nathanfraske/CEC-Platform/beta/pcie-8pin-2port/README.md

# PCIe 8-pin module — 2-port SKU

> **STATUS (2026-07-04, spec §2.8 v1.4.0 output-architecture revision, owner-ratified,
> BETA-2):** the per-cable board-mount **J_OUT1/J_OUT2** output headers are **RETIRED**. Each
> cable's output now crosses the ratified all-Keystone/TE connector-daughterboard interface
> (`docs/standard-tier-review/output-daughterboard-study-2026-07-04.md` §8.9–§8.10,
> `blade-fit-check-2026-07-04.md`): **2 rail clips + 2 GND clips per cable** (Keystone 3586 SMT
> universal-entry blade clips, LCSC C238113, refs `TB{cable}1`–`TB{cable}4` — e.g. cable 1 =
> `TB11`–`TB14`), each single-pin clip landing on the exact post-shunt net (`/SENSEC{n}_LO`) or
> `GND` its share of J_OUT used to carry. Applied via `scripts/gen-module-beta.py`'s
> `06-cable-power` leaf (generator edit + `--force` regen); J_IN (input) unchanged.
> Netlist-verified: only `/SENSEC1_LO`, `/SENSEC2_LO`, and `GND` changed, every other net
> byte-for-byte identical; ERC/audit-sch introduce zero new findings once `fp-lib-table`
> carries `cec-Connector_Blade` (added). `bom/pcie8pin-2port-module-BOM-jlcpcb.csv` updated.
> Sense-return contacts are explicitly NOT added — study §5 decision box (e) is still open with
> the owner. **PCB follow-up (not done here):** needs Update-PCB-from-Schematic + a footprint
> swap + re-route before fab. The mating daughterboard (TE 63849-1 tabs) is a separate
> deliverable, tracked outside this board.

Standard-tier **per-cable** sensing module for the PCIe 8-pin (PCIe/GPU) power
connector. **2-port SKU: 2 cables → 4 connectors**. The 3-port variant (spec
upper bound) is a separate board in
[`../pcie-8pin-3port`](../pcie-8pin-3port). BOM target **$38** (100-qty). See spec
[§6.2](../../CEC-Platform-Ground-Truth-Spec.md).

| Item | Decision |
|---|---|
| Tier | Standard |
| SKU | **2-port** (2 cables / 4 connectors) — SKU separation from the 3-port |
| MCU | **ESP32-C6-MINI-1-N4** (v3.10; was ESP32-S3-MINI-1-N4R2). Native USB-Serial-JTAG on IO13 (D+)/IO12 (D−); ADC1 = GPIO0–6. |
| Hub link | RJ-45 8P8C shielded FTP, locking boot (J1) |
| Power path | Pass-through interposer: per cable a PSU-side **IN** + load-side **OUT** 8-pin (2×4) header; **2 cables → 4 headers**. Molex Mini-Fit Jr (PCIe/ATX 8-pin standard; 3×12V + 5×GND). Gender/footprint per the 24-pin §2.8 interposer pattern — confirm at layout. |
| Control | CAN on pair 3 (classical 500 kbps in a Standard Hub), TJA1051T/3 (U2) |
| Sensing | **Per-cable INA238** (16-bit I²C), 2 cables (U10/U11, distinct I²C addresses) — one across each cable's **0.5 mΩ** Kelvin shunt (RS1/RS2, §6.4), Vbus read on the load side. |
| Transient detection (§6.13) | **Per-cable analog DETECTION front-end** (v3.10, resolves OQ-9): INA181A2 gain-50 CSA (U20/U21) → TLV7011 hysteresis comparator (U30/U31) → board-shared firmware THRESH (MCU PWM IO14 + R10 10 kΩ / C40 100 nF) → per-cable DET → MCU GPIO, ORs into the §6.10 FREEZE trigger. Binary event (it happened + averaged envelope), not the sub-ms waveform — magnitude/shape are a PCIe Pro/Max SKU. |
| Streaming | RS-485 **not populated** (Standard); pair 2 terminated module-side |
| DETECT | 2.2 kΩ precision (R1) — CAN-only code (§2.3, OQ-6 resolved), Hub 10 kΩ/3.3 V divider; poke-and-ack tap R7 → IO10 (OQ-28) |
| Protection | No per-pin PoE/over-voltage (Standard/Pro, §2.4 v2.0); low-cap ESD diode D1 (**PESD5V0S1BA**, C5261083) on DETECT pin 8 |
| Flash/debug | USB-C (J5) on the ESP32-C6 native USB-Serial-JTAG (D+ = IO13 / D− = IO12) + BOOT/RESET buttons (SW1/SW2, TS-1088-AR02016; BOOT = IO9); VBUS ORs into +5VSB via D2 (SS34); CC1/CC2 = 5.1 kΩ |
| Decoupling | LP5907 LDO; 24-pin gold-standard tiering (2× 10 µF bulk, 1 µF LDO in/out, per-IC 100 nF) |
| BOM target | $38 (100-qty) |

## Open questions touching this board

- **OQ-9 (RESOLVED, v3.10 §6.13):** PCIe transient capture is the analog DETECTION
  ladder above — Standard sees that a transient happened (binary, into FREEZE);
  magnitude/shape are held to the PCIe Pro/Max SKUs. (OQ-57..59 gate the details.)
- **OQ-10 / OQ-12:** bundled-shunt vertical transition + high-current stackup for
  the ~40–55 A/cable shunt sites (§6.7).
- **OQ-11:** per-module shunt part selection (§6.4 table).
- *(OQ-6 module-ID encoding resolved — CAN-only modules = 2.2 kΩ.)*

## Status

Schematic generated by `scripts/gen-modules.py`; the initial PCB floorplan by
`scripts/gen-module-pcb.py` (one-shot — hand-maintained in the GUI afterwards):
4-layer, **2 oz outer / 1 oz inner** (In1 = GND, In2 = 12 V), ~110 × 66 mm, 2
cables inline top/bottom, the ESP + CAN + LDO + flash front end + RJ-45 on the
right, 4× M3 corner mounts (cables inset to clear them), CEC copper logo on the
back. **DRAFT** marker present (ERC/DRC not yet CI-gated). Next in GUI: *Update
PCB from Schematic* to pull the passives, then place/route + pour (§6.8 Kelvin
taps, §6.7 high-current transitions). Project-local library tables point at
`../../lib` via `${KIPRJMOD}`.

## Update (2026-06-06) — v3.10: ESP32-C6 MCU + §6.13 transient-detection front-end

Regenerated on the consolidated v3.10 spec:

- **MCU ESP32-S3-MINI-1-N4R2 → ESP32-C6-MINI-1-N4** (C5736265), pin map
  netlist-verified (CAN_TX/RX → pads 26/27, USB D+/D− → pads 18/17, I²C → 24/25,
  EN → 8, BOOT/IO9 → 23, DETECT_SENSE → 12, +3V3 → 3, THRESH_PWM/IO14 → 19).
  Footprint `cec-RF_Module:ESP32-C6-MINI-1`.
- **§6.13 per-cable detection front-end** (2 cables): U20/U21 **INA181A2IDBVR**
  (C2058784) + U30/U31 **TLV7011DBVR** (C702117) + board-shared R10/C40 THRESH RC
  off MCU PWM IO14. Chain netlist-verified (shunt → INA181 → comparator → THRESH →
  per-cable DET → MCU GPIO pads 28/29). **D1 PESD UL → BA** (C5261083).
- BOM regenerated (`bom/pcie8pin-2port-module-BOM-jlcpcb.csv`): **sourced 39/45**;
  open are the 0.5 mΩ shunts (OQ-11) + the Mini-Fit Jr THT power headers.
- ERC = benign only.

## PCB floorplan (2026-06-06) — condensed candidate generator (86.4 × 44 mm)

Reproduced by `scripts/gen-pcie-condensed.py` (the **parametric** PCIe analogue of the
EPS `gen-eps-condensed.py`; reuses `gen-module-pcb.py`'s emit helpers without touching the
shared generator — one script drives both PCIe SKUs by board-name arg). Built the EPS way,
with **two sub-agent passes — footprint/placement planning, then a routing game-plan**.
**86.4 × 44 mm** (4-layer, F.Cu 2 oz / In1 1 oz / In2 1 oz / B.Cu 2 oz) — condensed from the
earlier 99 × 44. Plan + diagram: `pcie2-routing-plan.png`. **All 45 schematic parts placed**
(25/25 support passives netlist-verified by `PASSIVE_SPEC` + explicitly cluster-placed — the
3 entries for the 3rd cable are correctly absent on this 2-cable SKU); DRC 0 structural apart
from a known headless false within-footprint mask-bridge artifact on a button (absent in the
GUI; the RJ-45 mouth overhangs with copper kept on-board).

- **Cable connectors = the REAL Molex 45586** (J_IN/J_OUT): **Mini-Fit Jr. right-angle,
  3rd-gen PCIe polarization, 8-circuit, Nylon UL94V-0, 2.54µm matte tin — MPN
  45586-0005** (user-confirmed keying). The footprint is the manufacturer ECAD land
  (`cec-Connector_Molex:Molex_Mini-Fit_Jr_45586_2x04_P4.20mm_Horizontal`, vendored from
  the Molex `-SD` export + its STEP): 4.20 mm pitch + **5.50 mm rows**, round ⌀2.36 mm /
  1.85 mm-drill pads, two ⌀3.0 mm snap pegs in line with the outer pins 7.3 mm forward.
  THT, consigned/hand-soldered.
- **Connectors overhang their edges** — the body+mouth hang off the top (J_IN) /
  bottom (J_OUT) edges; only the pad rows + the 2 snap pegs stay on-board. The
  footprint is native mouth-toward-+y, so J_IN is placed rot180 / J_OUT rot0 (which
  reproduces the prior pad columns, so the net map + 12 V alignment are unchanged).
  The **RJ-45 mouth overhangs the right edge** too. The 45586 snap pegs set H = 44.
- **Side-by-side sense band** per cable: 0.5 mΩ shunt vertical in the 12 V path, INA238 +
  the §6.13 INA181→TLV7011 pair beside it.
- **J1 = platform FTP jack** Kinghelm **KH-RJ45-58-8P8C** (LCSC **C2683360**,
  `cec:RJ45_FTP_Shielded_Horizontal`), SH1/SH2 → GND — matching the Hub, EPS and
  12VHPWR.
- **3 M3 mounts:** two on the logic/electronics (right) side (TR/BR corners) + **one
  centered on the connector (left) side** at (4, H/2). USB-C on the top edge.
- Dual `GND Plane` over In1 + In2 (12 V on the outers, split at the shunt), emitted
  unfilled. Routing-candidate guides on user layers (12 V pours Dwgs.User, Kelvin pairs
  Cmts.User, control→sense spine Eco1.User, CAN/USB Eco2.User). CEC logo + fab note on back.

**Next in the GUI:** *Fill All Zones*, route (§6.8 Kelvin taps, §6.7 high-current
transitions), re-DRC. Regenerate (pre-route only) with
`python3 scripts/gen-pcie-condensed.py pcie-8pin-2port` — one-shot bootstrap, refuses to
overwrite once tracks/vias exist (`--force` overrides); hand-maintained from the first route.
