nathanfraske/CEC-Platform/hubs/hub-rev2/README.md

# Hub Rev2 — sectioned regen + mezzanine stack (2026-06-24)

Generated by `scripts/gen-hub-rev2.py` from the hand-maintained **Hub Standard** netlist
(extracted to `extract.json`, BOM/LCSC preserved), laid out in 10 LABELLED FUNCTIONAL SECTIONS,
with the **Rev2 delta**: the mezzanine SOCKET (`CEC_MEZZANINE_16P`, mirror of the 24-pin rev3
header) wired as "port 0" — pre-muxed `+5V_SYS`→`+5VSB`, the shared CAN bus, `/DETECT1`, GND.
Population variant: `J_MEZZ` XOR the `J2` RJ-45 port.

STATUS: schematic DRAFT — ERC clean (0 errors; benign lib_symbol_mismatch/pin_to_pin warnings only),
78 parts, BOM sourced (inherited from Hub Standard). The live `hubs/hub-standard/` stays the source of
truth; this is a fresh Rev2 board. NEXT: PCB layout (shared alignment frame w/ the 24-pin), and the
mezzanine socket on B.Cu (the mirror). Pinout verification + the 2 new-vs-24pin IC datasheets: see the
respin docs.

## Pinout verification vs datasheets (2026-06-24)
All Hub ICs cross-checked against their cached datasheets — every pinout MATCHES (no wiring errors):
| IC | verdict | note |
|---|---|---|
| ESP32-S3-WROOM-1 | ✅ match (41 pins) | CAN_TX=10/IO17, CAN_RX=11/IO18, DETECT1-4=4-7 (ADC1), EN=3, +3V3=2 all confirmed; pads 13/14 USB + pad41 EPAD=GND are cosmetic names |
| TPS3839DBZ | ✅ match (3) | 1=GND/2=RESET/3=VDD. NOTE: RESET is PUSH-PULL (not open-drain) — no external pull-up needed on the RESET line (drop one if the layout carries it). |
| SN74AHCT1G08 | ✅ match (5) | 1=A/2=B/3=GND/4=Y/5=VCC; the LED-data buffer use (A,B tied) is correct |
| TJA1051 / LP5907 / TPS2121 | ✅ | same symbols already datasheet-verified with the 24-pin rev3 |

The Hub Rev2 is electrically verified — connectivity, BOM, and all IC pinouts checked. NEXT: PCB layout.
