nathanfraske/CEC-Platform/modules/eps-8pin-rev2/README.md

# eps-8pin-rev2 — sectioned regen (2026-06-24)

Generated by `scripts/gen-module-rev2.py eps-8pin` from the source module's extracted netlist
(`extract.json`, BOM/LCSC preserved via cec_sch `props=`), laid out in **7 LABELLED FUNCTIONAL
SECTIONS** (cable connectors · MCU C6 · CAN · LDO · cable sensing INA238+shunt+§6.13 · flash/USB ·
hub-link RJ-45+DETECT). Same treatment as the 24-pin rev3 / Hub Rev2.

STATUS: schematic DRAFT — ERC = 1 benign error (the C6→CAN-TXD GPIO typing every generated module
carries) + benign lib_symbol_mismatch/pin_to_pin warnings. BOM sourced (inherited). All ICs use
symbols already datasheet-verified (C6, TJA1051, LP5907, INA238=INA226 body, INA181, TLV7011); INA238
datasheet now cached. The source module `modules/eps-8pin/` stays the source of truth. NEXT: PCB layout.
