nathanfraske/CEC-Platform/firmware/tools/README.md

# Bench tooling (`firmware/tools/`)

Host-side tools for the 12vhpwr proto bench. They replace "open PuTTY, log
everything, extract CSVs by hand, plot offline" with a clean capture → organize
→ analyze pipeline.

```
  device (ESP32-P4 + FPGA + AD7606)
        │  USB-CDC: teleplot lines, command output, ===BURST_CSV=== blocks
        ▼
  cec_bench.py ........ owns the serial port (no dropped lines), sends commands,
        │               splits each capture into its own file + a run manifest
        ▼
  runs/run-<ts>/
    captures/NNN-<hhmmss>-<kind>.csv     one file per capture (version-stamped header line)
    analysis/NNN-<hhmmss>-<kind>/        (--analyze) per-capture subfolder:
                                           *-time.png  *-imbalance.png  *-fft.png
                                           *-metrics.md/.json (analyzer version stamped)
    manifest.md                          every command + capture + version, timestamped
    session.log                          raw terminal mirror
        ▲
        │
  cec_capture_analyze.py ... per-MODULE analysis: parses a capture, computes the
                             metrics that matter for THAT module, emits plots +
                             a metrics.md/.json. Reads the MEASURED sample rate
                             from the capture header (never the nominal label).
```

Keep using **TelePlot** for the live 5 Hz monitor — these tools own the **bursts**
and the **record**. This capture→organize→analyze path is the prototype of the
**Concierge** host layer (spec Appendix C); the per-module profiles seed its
analysis stage.

## One-time setup (your bench machine)

Install into the **same** interpreter you'll run the tools with — use
`python -m pip` (not bare `pip`) so it can't land in a different Python than the
one you launch. These tools do **not** need ESP-IDF; a plain PowerShell/terminal
is fine (and avoids polluting the IDF venv).

```
python -m pip install pyserial numpy matplotlib
python -c "import serial, numpy, matplotlib; print('ok', serial.__version__)"   # verify
```

> Windows uses `python`; Linux/macOS use `python3`. The examples below say
> `python3` — substitute `python` on Windows. **Gotcha:** in the ESP-IDF terminal
> `pip` and `python3` can be *different* Pythons, so a `pip install` then a
> `python3 ...` gives "pyserial is required". The `python -m pip` form above + the
> matching `python` (Windows) / `python3` (Linux/mac) avoids it.

## A bench session

```
# 0. rebuild the FPGA bitstream + reflash the ESP if firmware changed.
# 1. start the host (Windows COM7 / Linux /dev/ttyACM0). --analyze auto-plots each capture.
python3 cec_bench.py --port COM7 --analyze --script "cal; rate; fastburst"
#    cal   -> zeroes the current channels at idle (run with the GPU idle)
#    rate  -> measures the TRUE native rate (~100k, not the 200k nominal) -- pins the FFT axis
#    fastburst -> a native-rate window; analyzer plots it
# 2. then induce a GPU load and, interactively, type:
autoburst 500 5
#    watches the stream; on a transient > ~0.75 A deviation it freezes the native
#    ring and dumps it. The host saves + analyzes each automatically.
quit
```

Everything lands in `runs/run-<timestamp>/` — captures, the manifest doc, and
(with `--analyze`) the metrics + plots. No manual extraction.

> The scripted sequence uses quiet-detection between commands (good for the
> deterministic `cal`/`rate`/`fastburst`/`stream` setup). `autoburst` waits for a
> transient *you* induce, so run it interactively.

## `cec_bench.py` — capture host

```
python3 cec_bench.py --port PORT [--analyze] [--module 12vhpwr]
                     [--script "cal; rate; fastburst"] [--run-dir DIR]
                     [--show-teleplot] [--teleplot-udp 127.0.0.1:47269]
```
Owns the port (pyserial), shows device output + lets you type commands, **and** in
the background splits each `===BURST_CSV===` block into `captures/`, appends to
`manifest.md`, and (`--analyze`) runs the analyzer per capture. `quit` to stop.

**Auto-analyze needs numpy + matplotlib in the *same* Python** that runs
`cec_bench` (the analyzer runs as its subprocess). `--analyze` checks this at
startup and prints the exact `pip` line if they're missing — that's the usual
reason charts don't appear. Each capture's charts land in their own subfolder
`analysis/<capture>/`, and the CSVs + manifest carry a version
(`cec_bench v1.0+<git-sha>`) so a run is documented + reproducible.

**The 5 Hz teleplot `>` lines are HIDDEN in the terminal by default** — they'd
otherwise bury your typing and the command output (and break the `--script`
step-detection). They still go to `session.log`. `--show-teleplot` un-hides them.

**Live graphing + capture at the same time:** a serial port has exactly one owner,
so you cannot run Teleplot *and* `cec_bench` on the same COM port. Two ways to get
both:
- **`--teleplot-udp 127.0.0.1:47269`** — `cec_bench` owns the port and re-broadcasts
  the teleplot stream over UDP; point Teleplot's **UDP input** at that address and
  it graphs live while `cec_bench` captures. (Works with the UDP-capable Teleplot;
  the VS Code extension reading *serial* can't share the port this way.)
- Or just run them **separately** — Teleplot for live monitoring, `cec_bench` for a
  capture session. (During `autoburst`/`fastburst` the device pauses teleplot
  anyway, so you're not losing much by not having both at once.)

## `cec_capture_analyze.py` — per-module analysis

```
python3 cec_capture_analyze.py CAPTURE.csv|putty.log [--module 12vhpwr]
                     [--rate HZ] [--index N] [--out DIR]
                     [--analog-rc-hz 15900 --analog-adc-hz 14000]
```
Parses every capture block in the input (a single file or a whole PuTTY log) and,
per the **module profile**, writes `*-time.png`, `*-fft.png`, and `*-metrics.md/.json`.

Each module asks a different question, so analysis is a **profile** (pluggable):

| module | what it computes |
|---|---|
| **`12vhpwr`** (done) | per-PIN imbalance (the melt metric, flagged under load), per-pin mean/peak/RMS, total, rail droop/ripple, load fundamental + floor (FFT at the real rate, analog-ceiling overlay) |
| `atx-24pin` (stub) | per-rail power + energy (INA228 accumulators), rail stability |
| `eps` / `pcie` (stub) | per-cable balance + total power + §6.13 transient events |

### Honest notes (they matter for the numbers)

- **Rate:** the analyzer uses the rate stamped in the capture header. If it says
  `(NOMINAL -- run rate)`, every frequency is flagged ~2× suspect — run `rate` on
  the device first (the conv+read FSM self-limits to ~100k at ÷4, not the 200k
  nominal). `--rate HZ` overrides.
- **Imbalance needs load:** at idle the mean pin current is ~0 (and dominated by
  uncalibrated INA offsets), so the imbalance % is undefined and reported as
  `no_load`. Run `cal`, then capture under GPU load for a real imbalance number.
- **Imbalance has a measurement floor:** the per-pin shunts are ±1% *independent*,
  so each pin's share is only known to ±`2·tol·(N-1)/N` (≈ ±1.5% at 4 pins) — drawn
  as the grey band on the imbalance chart. A bar inside the band may be shunt
  mismatch, not real imbalance; the headline spread is trustworthy above ~2×tol.
  `--isense-tol PCT` sets the shunt class (default 1.0).
- **FFT validity:** uniform only for `fastburst`/`autoburst` (FPGA-paced). The
  ESP-paced `burst` has a non-uniform time axis — time-domain + stats only.
- **Analog ceiling** defaults to the perfboard RC (15.9 kHz) × AD7606 (14 kHz) ≈
  9.6 kHz; adjust to your front-end with `--analog-rc-hz` / `--analog-adc-hz`.

## Next

When the firmware stamps a **self-describing header** (module id + channel roles,
on top of the measured rate it already stamps), the analyzer will auto-select the
profile from the capture instead of `--module`. That header + these profiles are
the handoff into Concierge.
