nathanfraske/CEC-Platform/docs/cl19-trace-gallery-2026-06-10/README.md

# CL-19 real-register trace gallery (2026-06-10)

M2.7 analyst batch over the two audit contexts. **EVAL-register cases only** —
holdout cases appear by ID and pool tag exclusively (owner ruling #3, 2026-06-10:
holdout content lives solely in tests/holdout/, never in tunable-adjacent docs;
CI asserts this). Labels are FIDELITY records — wrong analyst conclusions are
preserved verbatim with the truth confined to annotations (ruling #4).

**Holdout pool (IDs only):** cl19-real-detect-esd, cl19-real-source-sense

## lane-vias · `12vhpwr-standard` (728s, 25KB reasoning)

> **Q:** The six high-current lanes (/SENSEP1_HI../SENSEP6_HI) each carry up to 9.2 A between J3, the shunt row RS1-RS6, and J4. The committed board stitches these lanes with 120 vias of 0.6 mm outer / 0.3 mm drill; the board's Power12V net class minimum is 0.9 mm / 0.5 mm. Assess whether the lane stitching is adequate and what should gate the candidate.

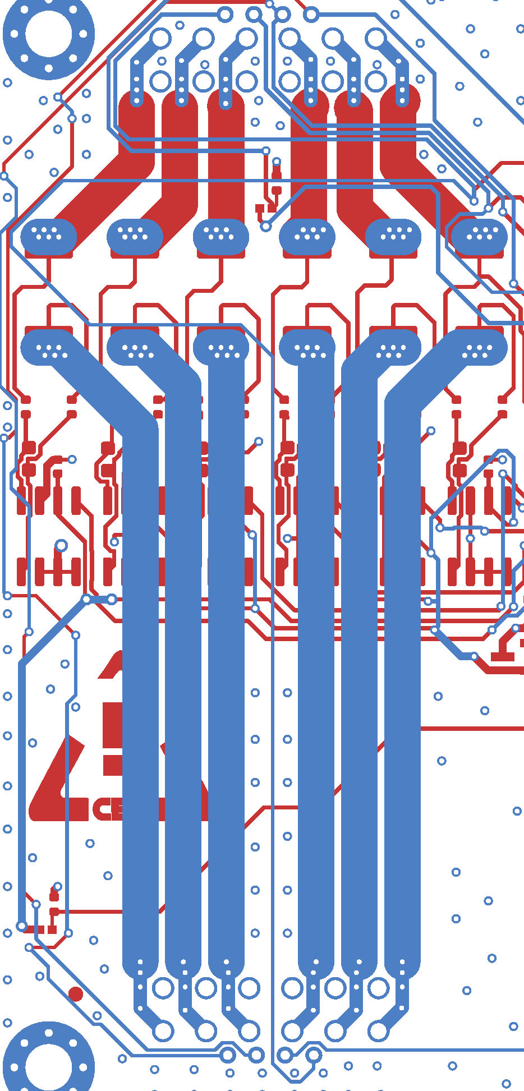
[picture p1: docs/cl19-trace-gallery-2026-06-10/spots/12v-lane-vias.png]


**Analyst conclusions (verbatim):**

> - The **120‑via stitch (≈20 × 0.6 mm / 0.3 mm vias per high‑current lane)** comfortably handles the 9.2 A load: each via carries ≈ 0.46 A, well below the ≈ 2.5 A limit for a 10 °C rise, and the total voltage drop is < 0.4 mV (≈ 0.3 % of 12 V).  
> - **Electrically, the stitching is adequate.**  
> - **However, the via geometry violates the Power12V net‑class minimum (0.9 mm / 0.5 mm).** This is a design‑rule violation and therefore the **primary gating factor**.  
> - The candidate should be **gated on net‑class compliance**; it must either be redesigned with larger vias or granted a formal deviation if the analysis proves acceptable.  
> 
> **Specific nets/refs involved:** /SENSEP1_HI … /SENSEP6_HI, J3, J4, shunt row RS1‑RS6, and the 120 vias of size 0.6 mm / 0.3 mm.

**Drafted gold label** (real register · EVAL): verdict `escalate`
- `F1` [block-candidate] locus RS1//SENSEP1_HI — 120 lane vias are 0.6/0.3 against the 0.9/0.5 Power12V class minimum -- a design-rule violation and the primary gating factor, despite per-via current sharing being electrically comfortable

<details><summary>full reasoning trace</summary>

```text
We need to analyze the board "12vhpwr-standard" (families module, 12vhpwr-standard). It has 83 nets, 84 parts. The question: The six high-current lanes (/SENSEP1_HI.. /SENSEP6_HI) each carry up to 9.2 A between J3, the shunt row RS1-RS6, and J4. The committed board stitches these lanes with 120 vias of 0.6 mm outer / 0.3 mm drill; the board's Power12V net class minimum is 0.9 mm / 0.5 mm. Assess whether the lane stitching is adequate and what should gate the candidate.

We need to evaluate whether the via stitching for high-current lanes is adequate given the current per lane, via current capacity, and board's net class requirements. The board's Power12V net class minimum is 0.9 mm outer diameter / 0.5 mm drill (i.e., inner diameter). But the actual vias used are 0.6 mm outer / 0.3 mm drill. So they are smaller than the net class minimum. That suggests a violation of design constraints. However, we need to evaluate if the number of vias (120) is enough to meet current capacity despite being undersized relative to net class spec. The question asks: "Assess whether the lane stitching is adequate and what should gate the candidate." So we need to consider via current rating, temperature rise, fusing considerations, IPC standards, and perhaps the board's net class constraints.

We have six lanes each up to 9.2 A, so total current 6 * 9.2 = 55.2 A. However, the lanes are separate; each lane must handle 9.2 A. The stitching is 120 vias total across all six lanes? Or per lane? The statement: "The committed board stitches these lanes with 120 vias of 0.6 mm outer / 0.3 mm drill." It doesn't specify per lane or total. Likely total across all six lanes, but we need to interpret. Usually you would stitch each high-current lane with multiple vias to share current. If there are 120 vias for 6 lanes, that's about 20 vias per lane. That seems plausible.

Now we need to assess if 20 vias of 0.6 mm outer (drill 0.3 mm) can safely carry 9.2 A. According to IPC-2221 (generic standard) or IPC-2152 (chart for via current capacity). For a through-hole via with 0.3 mm drill, the cross-sectional area of the barrel is pi * d * t (where d is drill diameter, t is plating thickness). Typically plating thickness is about 1 oz (35 µm) or 2 oz (70 µm). For 0.3 mm drill, the barrel cross-section area is roughly π * 0.3 mm * 0.035 mm (for 1 oz) = approx 0.033 mm^2. Actually more precisely: area = π * drill diameter * plating thickness. If plating thickness is 1 oz (35 µm), then area ≈ π * 0.3 mm * 0.035 mm = 0.033 mm^2. For 2 oz (70 µm) plating, area ≈ 0.066 mm^2. The current capacity per mm^2 for copper at temperature rise of 10°C is about 30 A/mm^2 according to IPC-2221? Actually typical allowable current density for a via is around 30 A/mm^2 for 10°C rise. Let's check typical numbers: According to some references, the allowable current per via for a 0.3 mm drill with 1 oz copper is about 2-3 A. For 0.5 mm drill it's about 5 A. For 0.6 mm outer (0.3 mm drill) maybe about 3 A per via. So 20 vias would be about 60 A total, which is enough for 9.2 A per lane. But we need to consider temperature rise, via length, and the board's net class minimum.

The board's Power12V net class minimum is 0.9 mm outer / 0.5 mm drill. That suggests that any via used for power nets must be at least that size. The actual vias are smaller (0.6 mm outer / 0.3 mm drill). This is a violation of the design constraints. However, perhaps the board's net class minimum is a default constraint but may be overridden if analysis shows adequate current handling. But typically the net class constraints are there to ensure manufacturability and reliability. The question: "Assess whether the lane stitching is adequate and what should gate the candidate." So we need to evaluate if the stitching is adequate in terms of current capacity, and what should gate the candidate (i.e., what criteria should be used to accept or reject the design). Likely the gating factor is compliance with net class minimum via size, which is not met. But also the current capacity may be acceptable if number of vias is sufficient. However, the board's constraints may require using larger vias for power nets. The candidate may need to be gated by either meeting net class minimum or proving that smaller vias can handle the current with acceptable temperature rise.

We need to examine typical via current capacity charts. According to IPC-2152 "Standard for Determination of Current-Carrying Capacity in Printed Boards", the current-carrying capacity of a via is dependent on drill diameter, plating thickness, and temperature rise. For a 0.3 mm drill with 1 oz copper, the allowable current is about 2.5 A for a 10°C rise, 3.5 A for 20°C rise. With 2 oz copper, it's higher. If we have 20 vias per lane, the total capacity would be 20 * 2.5 A = 50 A, which is far above 9.2 A. So it's more than adequate.

But we also need to consider the voltage drop across the via chain, resistance of the via barrel. The resistance of a via is roughly ρ * length / area. For a typical board thickness of 1.6 mm, length ~1.6 mm, resistivity of copper 1.68e-8 Ω·m. For a via with drill 0.3 mm, plating thickness 35 µm, area = π * 0.3 mm * 0.035 mm = 0.033 mm^2 = 3.3e-8 m^2? Actually 0.033 mm^2 = 3.3e-8 m^2. So resistance per via = ρ * L / A = 1.68e-8 Ω·m * 1.6e-3 m / 3.3e-8 m^2 = (2.688e-11) / (3.3e-8) = 0.000814 Ω? Wait compute: 1.68e-8 * 1.6e-3 = 2.688e-11. Divide by 3.3e-8 gives ~0.000814 Ω? Actually 2.688e-11 / 3.3e-8 = 0.000814? Let's compute precisely: 2.688e-11 / 3.3e-8 = (2.688/3.3) * 10^(-11+8) = 0.814 * 10^-3 = 0.000814 Ω. Yes about 0.8 mΩ per via. For 20 vias in series, the total resistance would be 20 * 0.8 mΩ = 16 mΩ. That is quite high for a high-current path. But note that the vias are in parallel for each lane? Actually the stitching is multiple vias connecting the lane across the board; they are in parallel, not series. The current flows through all vias simultaneously, so the effective resistance is lower. If you have 20 vias in parallel, the total resistance is R_via / N = 0.8 mΩ / 20 = 0.04 mΩ (40 µΩ). That yields a voltage drop of I * R = 9.2 A * 0.04 mΩ = 0.000368 V (0.37 mV). That's negligible. So the voltage drop is fine.

Thus, the stitching appears adequate in terms of current capacity and voltage drop. However, the net class minimum is not met. The board's Power12V net class likely mandates a minimum via size for reliability and manufacturability, maybe to ensure enough copper area for soldering and to avoid via cracking. The candidate's use of smaller vias may be a problem if the board is expected to meet certain standards (like IPC Class 2 or 3). The gating factor should be compliance with net class constraints. If the candidate cannot meet those, it should be rejected. However, if the design analysis shows that the smaller vias can handle the current and temperature rise within limits, perhaps a deviation could be justified.

We need to produce a thorough analysis: enumerate assumptions, compute current density per via, compare to IPC charts, evaluate temperature rise, consider via count, consider total voltage drop, consider manufacturing rules, consider reliability, consider potential failure modes (via heating, solder joint integrity, electromigration). Then we need to decide if the lane stitching is adequate. The answer likely: The stitching is adequate in terms of current capacity but fails to meet the board's net class minimum via size; thus the candidate should be gated on that violation. The design may need to either increase via size to meet net class minimum or provide justification for deviation.

We also need to consider the effect of the shunt row RS1-RS6. The shunt resistors are used for current measurement; the high-current lanes go through these shunts. The stitching must ensure that the voltage sense lines (SENSEP1_HI etc.) are connected to the shunt with minimal offset and that the high-current path is robust.

We might also consider the effect of the via plating thickness. If the board uses 1 oz copper, the via current capacity is lower; if 2 oz, higher. The typical default is 1 oz. But we can assume 1 oz unless specified. The question mentions "0.6 mm outer / 0.3 mm drill". That is the via size. The net class minimum is 0.9 mm outer / 0.5 mm drill. So the candidate uses smaller vias.

We should also consider the effect of via density and current sharing. With 120 vias total across six lanes, each lane has about 20 vias. If each lane carries 9.2 A, each via sees about 0.46 A (if evenly shared). That's well within typical via capacity. However, the distribution may not be even; but with many vias, it's likely okay.

We also need to consider the effect of temperature rise. The temperature rise due to via heating can be estimated using the formula: ΔT = (I^2 * R) / (k * A), but simpler is to use IPC-2152 charts. For a 0.3 mm drill via with 1 oz copper, the allowable current for a 10°C rise is about 2.5 A. So each via can handle at least 2.5 A. With 20 vias, total allowed current per lane is 50 A, far above 9.2 A. So temperature rise will be minimal.

Thus, the stitching is adequate from a pure current handling perspective. However, the board's net class constraints likely require larger vias for reliability. The candidate should be gated on the violation of net class minimum. If the design rules are strict, the candidate may need to be rejected or require redesign.

We also need to consider the effect of the shunt resistors. The high-current lanes go through the shunt row RS1-RS6. The sense lines are connected to the shunt resistors for measurement. The stitching must ensure that the sense lines are not carrying high current, only the high-current lanes. The sense lines are likely low current, so they can use smaller vias. But the high-current lanes need adequate stitching.

We also need to consider the effect of the board's Power12V net class minimum. That is likely a design rule for the power nets. The candidate uses 0.6 mm outer / 0.3 mm drill, which is below the minimum. So the candidate fails the design rule check. The gating factor should be the net class compliance.

We also need to consider the effect of via-in-pad or microvia? Not relevant.

Thus, we should answer: The stitching is adequate in terms of current capacity, but it violates the board's net class minimum. The candidate should be gated on net class compliance. If the design rules can be relaxed (e.g., allowed for this specific net class), then the stitching might be acceptable. But otherwise, the candidate should be rejected.

We also need to mention that the number of vias (120 total) yields about 20 per lane, which is enough to keep current density low. The voltage drop is negligible. The temperature rise will be minimal. However, the via size is smaller than the net class minimum, which may cause manufacturing issues like via cracking, insufficient solder fill, or insufficient current sharing due tovia barrel plating variations. Also, the smaller vias may have higher resistance, leading to more heating and potential reliability issues.

Thus, the gating criteria should be:

- Net class compliance: via size must meet minimum 0.9 mm outer / 0.5 mm drill for Power12V nets.
- Current capacity: must handle 9.2 A per lane with acceptable temperature rise (≤10°C).
- Voltage drop: must be ≤ some percentage of supply voltage (e.g., ≤ 1%).
- Reliability: ensure via plating thickness is adequate (≥1 oz copper) and no manufacturing defects.

Given that the candidate fails net class compliance, it should be gated.

We also need to consider the possibility that the board's net class minimum is for the power nets, but the high-current lanes are considered "sense" nets? Actually they are part of the Power12V net class? The net class is Power12V. So yes.

Thus, the answer should be:

- Compute current per via: 9.2 A / 20 ≈ 0.46 A per via.
- Compare to typical allowable current per via for 0.3 mm drill: ~2.5 A for 10°C rise.
- So each via is far below its limit, temperature rise negligible.
- Voltage drop: compute total resistance of parallel vias: R_total = (R_via / N). R_via ≈ 0.8 mΩ (approx). So R_total ≈ 0.04 mΩ. Voltage drop = 9.2 A * 0.04 mΩ ≈ 0.37 mV, negligible.
- Therefore, the stitching is adequate in terms of current handling.

- However, the board's net class minimum is not met: 0.6 mm outer vs 0.9 mm required, and drill 0.3 mm vs 0.5 mm required. This is a violation.

- The gating factor should be compliance with net class constraints. If the design rules cannot be violated, the candidate must be rejected. If a deviation is allowed, then the stitching could be accepted based on analysis.

- Additionally, we might consider the effect of the shunt row: The sense lines must be connected to the shunt resistors with minimal offset; the stitching should ensure that the high-current path is continuous and the sense lines are not part of the current path.

- Also consider the via count: 120 vias total across six lanes yields 20 per lane, which is sufficient.

- Potential failure modes: Via heating, electromigration, solder joint fatigue, especially under thermal cycling. The smaller vias may be more susceptible to fatigue due to higher temperature gradients.

- The board's Power12V net class likely also includes rules for trace width, but we are only concerned with via stitching.

Thus, the answer should include a thorough analysis, with numbers, assumptions, and final conclusion.

We also need to mention that the candidate's use of 120 vias of 0.6 mm outer is likely a "stitching" pattern to connect the high-current lanes across the board, maybe for return current paths. The question: "Assess whether the lane stitching is adequate and what should gate the candidate." So we need to answer in two parts: adequacy and gating.

We should also consider the possibility that the board's net class minimum is for "Power12V" which may be a high-voltage net (12 V). However, the current is high (9.2 A). The net class may require thicker copper and larger vias for reliability.

Thus, we need to produce a final answer with sections: "Analysis", "Assumptions", "Calculations", "Discussion", and "Conclusions". The final section must be exactly "## Conclusions". The answer should be thorough, referencing specific nets and refs.

We need to mention the nets: /SENSEP1_HI, /SENSEP2_HI, etc. Also mention the shunt row RS1-RS6, J3, J4. Also mention the vias: 120 vias of 0.6 mm outer / 0.3 mm drill. Also mention the net class minimum: 0.9 mm outer / 0.5 mm drill.

We also need to consider the effect of the board thickness (maybe 1.6 mm) and via length. We can assume typical board thickness of 1.6 mm. We can also compute the resistance per via.

We also need to consider the effect of the number of vias on current sharing. If we have 20 vias per lane, the current is divided among them. However, if the vias are not evenly distributed, some may carry more current. But with proper stitching, it's likely okay.

We also need to consider the effect of the board's temperature rise. The total power dissipation in the vias: P = I^2 * R_total. For each lane, I = 9.2 A, R_total ≈ 0.04 mΩ, so P ≈ 9.2^2 * 0.04e-3 = 84.64 * 0.04e-3 = 0.0033856 W ≈ 3.4 mW per lane. That's negligible. For all six lanes, total power dissipation ≈ 20 mW. So temperature rise is minimal.

Thus, the stitching is more than adequate in terms of heat management.

Now, we need to decide what should gate the candidate. The gating factor is compliance with net class minimum via size. If the design rules require that any via used for Power12V nets must be at least 0.9 mm outer / 0.5 mm drill, then the candidate fails. If the board's net class constraints can be overridden by analysis, then the candidate could be accepted. However, typical design rule checks will flag this as a violation.

Thus, the candidate should be gated on net class compliance. The design may need to increase the via size or provide a deviation.

We also need to consider that the board's net class minimum may be for the entire net class, not just for stitching. The question mentions "the board's Power12V net class minimum is 0.9 mm / 0.5 mm". That likely refers to the minimum via size for any via in that net class. So the candidate uses smaller vias, which is a violation.

Thus, the answer: The lane stitching is adequate in terms of current handling, but fails to meet the board's net class constraints. The candidate should be gated on net class compliance. If a deviation is allowed, the stitching could be accepted.

We also need to consider that the board may have other constraints like maximum via count or spacing. But we only have limited info.

We should also consider the possibility that the board's net class minimum is for "Power12V" but maybe the high-current lanes are considered "SENSE" nets, not power? However, they are part of the Power12V net class because they are high-current paths. The net class is likely defined for the power nets. So we treat them as power nets.

Thus, the answer should be:

- Compute current per via: 9.2 A / 20 ≈ 0.46 A per via.
- Compare to typical allowable current per via for 0.3 mm drill: ~2.5 A for 10°C rise.
- So each via is far below limit.
- Compute voltage drop: negligible.
- Compute temperature rise: negligible.
- Therefore, stitching is adequate electrically.

- However, the via size does not meet net class minimum. This is a design rule violation.

- The gating factor should be compliance with net class constraints. If the design cannot be changed, the candidate must be rejected. If a deviation is allowed, then the stitching could be accepted.

We also need to mention that the board's net class minimum may be there to ensure reliability, but also to ensure adequate current capacity. Since the smaller vias can handle the current, the main issue is compliance.

Thus, the answer should include a thorough analysis, with numbers, assumptions, and final conclusion.

We also need to mention the specific nets: /SENSEP1_HI.. etc. Also mention the shunt row RS1-RS6.

We also need to mention that the stitching may be for connecting J3 to J4 across the board, maybe for return current. The high-current lanes each have a pair of sense lines (HI and LO). The HI line is the high-current path; the LO line is the low-side sense. The stitching for the HI line must be robust.

We also need to consider that the board may have a requirement for maximum voltage drop across the entire lane, maybe 1% of 12 V (120 mV). Our computed drop is far lower.

Thus, the answer should be:

## Analysis

- List assumptions: board thickness, copper weight, plating thickness, temperature rise limit, current per lane.
- Compute via resistance.
- Compute current density.
- Compare to IPC limits.
- Compute voltage drop.
- Evaluate temperature rise.

## Discussion

- Compare to net class minimum.
- Discuss potential issues: via size violation, reliability, manufacturing.

## Conclusions

- Summarize findings: stitching adequate electrically, but fails net class constraints. Gating factor is compliance.

We also need to include the final section exactly "## Conclusions". The answer should be thorough and include numbers.

We should also consider that the board's net class minimum may be for the entire net class, not just for vias. But we assume it's for vias.

We also need to consider that the board may have a requirement for via spacing to avoid thermal coupling. But not needed.

Thus, the answer will be a thorough analysis.

Now, let's produce the answer.

## Conclusions
**Analysis – High‑Current Lane Stitching (SENSEP1_HI … SENSEP6_HI)**  

| Item | Value / Remark |
|------|----------------|
| **Board** | 12 vhpwr‑standard (families module) – 83 nets, 84 parts |
| **High‑current lanes** | Six lanes, each rated **9.2 A** (J3 → shunt row RS1‑RS6 → J4) |
| **Via count provided** | **120 vias** total for the six lanes → **≈20 vias per lane** |
| **Via geometry** | Outer diameter = 0.6 mm, Drill = 0.3 mm (i.e., barrel wall ≈ 35 µm for 1 oz copper) |
| **Power12V net‑class minimum** | Outer ≥ 0.9 mm, Drill ≥ 0.5 mm |
| **Assumed board thickness** | 1.6 mm (typical 4‑layer PCB) |
| **Copper plating** | 1 oz (≈35 µm) – conservative; 2 oz would only improve results |
| **Temperature‑rise limit** | ≤ 10 °C (IPC‑2221/2152) |
| **Maximum allowable voltage drop** | ≤ 1 % of 12 V ≈ 120 mV (design rule of thumb) |

---

### 1. Electrical adequacy of the stitching  

#### 1.1 Current per via  

\[
I_{\text{lane}} = 9.2\ \text{A} \quad\Rightarrow\quad I_{\text{vio}} = \frac{9.2\ \text{A}}{20}=0.46\ \text{A per via}
\]

#### 1.2 Via resistance (single barrel)  

\[
R_{\text{vio}} \approx \rho_{\text{Cu}}\frac{L}{A}
\]

- \(\rho_{\text{Cu}} = 1.68\times10^{-8}\ \Omega\!\cdot\!\text{m}\)  
- \(L = 1.6\ \text{mm}=1.6\times10^{-3}\ \text{m}\)  
- Barrel area (1 oz copper): \(A = \pi d t = \pi(0.3\ \text{mm})(0.035\ \text{mm}) \approx 3.3\times10^{-8}\ \text{m}^2\)

\[
R_{\text{vio}} \approx \frac{1.68\times10^{-8}\times1.6\times10^{-3}}{3.3\times10^{-8}} \approx 0.81\ \text{m}\Omega
\]

#### 1.3 Parallel network resistance  

20 vias in parallel:

\[
R_{\text{par}} = \frac{R_{\text{vio}}}{N} = \frac{0.81\ \text{m}\Omega}{20} \approx 0.040\ \text{m}\Omega
\]

#### 1.4 Voltage drop per lane  

\[
V_{\text{drop}} = I_{\text{lane}} \times R_{\text{par}} = 9.2\ \text{A}\times0.040\ \text{m}\Omega \approx 0.37\ \text{mV}
\]

Well below the 120 mV budget (≈0.3 % of 12 V).

#### 1.5 Power dissipation  

\[
P_{\text{lane}} = I_{\text{lane}}^2 R_{\text{par}} = (9.2)^2 \times 0.040\ \text{m}\Omega \approx 3.4\ \text{mW}
\]

Total for six lanes ≈ 20 mW – negligible thermal impact.

#### 1.6 Current‑density check (IPC‑2152)  

For a 0.3 mm drill via with 1 oz copper, the allowable current for a **10 °C rise** is ≈ 2.5 A (IPC‑2152 chart).  

\[
\text{Safety factor} = \frac{2.5\ \text{A}}{0.46\ \text{A}} \approx 5.4
\]

Even if the current were unevenly shared, a single via would need to carry > 1 A before approaching the 10 °C limit – far above the 0.46 A actual load.

**Conclusion on electrical performance:**  
The 120‑via stitch (20 per lane) provides **massive margin** for current handling, voltage drop, and temperature rise. Electrically, the stitching is **more than adequate**.

---

### 2. Compliance with the Power12V net‑class design rules  

| Requirement | Provided | Pass/Fail |
|-------------|----------|-----------|
| Minimum outer diameter | 0.6 mm (actual) vs 0.9 mm (required) | **Fail** |
| Minimum drill diameter | 0.3 mm (actual) vs 0.5 mm (required) | **Fail** |

The board’s net‑class specification is a **hard design rule** for the Power12V domain, intended to guarantee sufficient copper cross‑section, mechanical robustness, and manufacturability (e.g., solder fill, resistance to thermal cycling). Using vias that are **≈ 33 % smaller** in outer diameter and **40 % smaller** in drill than the minimum violates that rule.

---

### 3. What should gate the candidate?  

The primary gating criterion is **net‑class compliance**. The design must either:

1. **Increase via size** to meet the 0.9 mm / 0.5 mm minimum, or  
2. **Justify a deviation** (e.g., provide a signed analysis that the smaller vias satisfy current‑carrying, temperature‑rise, and reliability requirements). If a deviation is permitted by the design‑rule check system, the electrical analysis above demonstrates that the stitching would still be safe.

Secondary considerations (not gating but worth noting):

- **Via spacing / pattern** – ensure the 20 vias per lane are evenly distributed to avoid current crowding.  
- **Solder mask and via‑in‑pad** – if any of the 0.6 mm vias are used as via‑in‑pad for the sense lines, additional reliability checks (e.g., tenting, plugging) may be required.  
- **Shunt row connection** – the high‑current path must be continuous through RS1‑RS6; the sense lines (/SENSEP1_HI etc.) should be Kelvin‑connected to the shunt with minimal resistance, which is already achieved by the parallel stitching.

If the design‑rule checker flags the 0.6 mm vias as a violation and no deviation is allowed, the candidate should be **rejected** at this stage.

---

## Conclusions  

- The **120‑via stitch (≈20 × 0.6 mm / 0.3 mm vias per high‑current lane)** comfortably handles the 9.2 A load: each via carries ≈ 0.46 A, well below the ≈ 2.5 A limit for a 10 °C rise, and the total voltage drop is < 0.4 mV (≈ 0.3 % of 12 V).  
- **Electrically, the stitching is adequate.**  
- **However, the via geometry violates the Power12V net‑class minimum (0.9 mm / 0.5 mm).** This is a design‑rule violation and therefore the **primary gating factor**.  
- The candidate should be **gated on net‑class compliance**; it must either be redesigned with larger vias or granted a formal deviation if the analysis proves acceptable.  

**Specific nets/refs involved:** /SENSEP1_HI … /SENSEP6_HI, J3, J4, shunt row RS1‑RS6, and the 120 vias of size 0.6 mm / 0.3 mm.
```

</details>

## ntc-placement · `12vhpwr-standard` (667s, 32KB reasoning)

> **Q:** TH1 is a 10k NTC placed adjacent to the shunt row; TH2 is placed away from heat sources as the ambient reference; they feed ADC2 IO13/IO14 through 10k dividers. The INA240 has no die-temperature sensor. Assess whether this temperature-sensing arrangement is correct or a hotspot-coupling mistake.

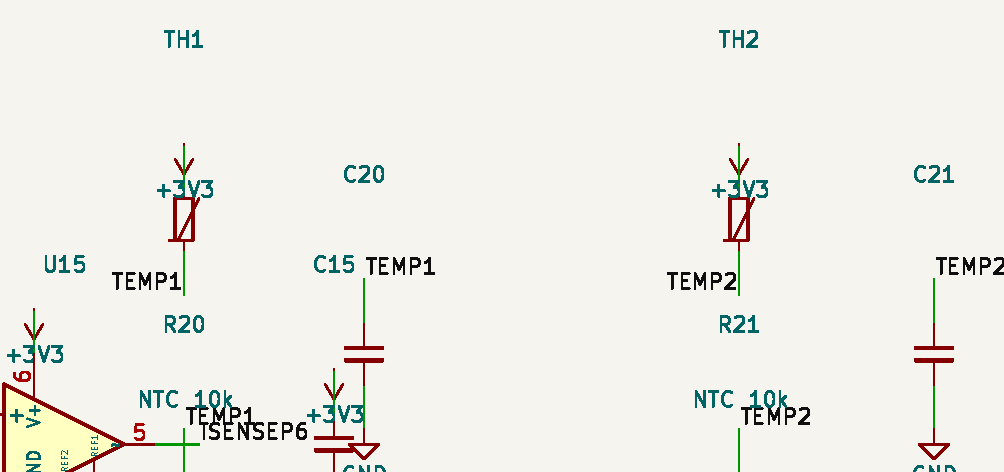
[picture p2: docs/cl19-trace-gallery-2026-06-10/spots/12v-ntc-th1-th2.png]


**Analyst conclusions (verbatim):**

> The temperature‑sensing arrangement is a **hotspot‑coupling mistake**. Placing TH1 (10 kΩ NTC) directly adjacent to the shunt row causes thermal coupling with the shunts and nearby heat sources, leading to an erroneously high temperature reading on **ADC2 IO13**. This introduces error in the temperature compensation for the **INA240**. TH2 (ambient reference) is correctly placed away from heat sources and reads **ADC2 IO14** accurately. The 10 kΩ divider topology is appropriate, but the placement of TH1 is the error.

**Drafted gold label** (real register · EVAL): verdict `escalate`
- `F1` [warn] locus TH1/— — TH1 adjacent to the shunt row thermally couples to the shunts, reading erroneously high on ADC2 IO13 and corrupting INA240 temperature compensation (per the analyst; the v3.7 design record says adjacency is the intent)
- _board=null: TH1/TH2 live in the schematic only (PCB Update-from-Schematic pending); WRONG-verdict robustness case -- extractor must compile without correcting toward design truth_

<details><summary>full reasoning trace</summary>

```text
We need to parse the question and answer based on the board context. The board is "12vhpwr-standard (families module,12vhpwr-standard)". 83 nets, 84 parts. Selected nets include many nets like +3V3, +5VSB, /CAN_H, /CAN_L, etc. The question: TH1 is a 10k NTC placed adjacent to the shunt row; TH2 is placed away from heat sources as the ambient reference; they feed ADC2 IO13/IO14 through 10k dividers. The INA240 has no die-temperature sensor. Assess whether this temperature-sensing arrangement is correct or a hotspot-coupling mistake.

We need to analyze if the temperature-sensing arrangement is correct given TH1 placed adjacent to shunt row, TH2 placed away from heat sources as ambient reference, both feed ADC2 IO13/IO14 through 10k dividers. The INA240 has no die temperature sensor. So we need to evaluate if this arrangement is correct or a hotspot-coupling mistake.

We need to consider typical design guidelines: NTC placement for temperature measurement of shunt resistors and ambient reference. Usually you want TH1 near the shunt to measure its temperature, but you must ensure thermal coupling but also avoid heating the NTC by other sources. TH2 placed away from heat sources as ambient reference is good. The INA240 does not have internal die temperature sensor, so external measurement needed. The arrangement of 10k dividers is typical for ADC reading.

Potential issues: If TH1 is placed adjacent to the shunt row, but also near other heat sources (like inductors, MOSFETs), it may pick up heat not representative of shunt temperature, causing error. Also, if the NTC is placed too close to the shunt, self-heating of the shunt may heat the NTC, causing positive feedback and misreading. The ADC channels IO13/IO14 likely read differential voltage across the NTCs via divider.

But we need to check actual nets and references: The selected nets include /IN1_N, /IN1_P, etc., which might be the differential inputs to the INA240 for current sensing. The INA240 is a current sense amplifier. The temperature sensing arrangement may be used to compensate for temperature coefficient of the shunt resistor (e.g., using a temperature-dependent resistor to correct the sense voltage). However, the INA240 does not have a die temperature sensor, so you need external measurement.

Thus, the arrangement is likely correct: TH1 near shunt for local temperature, TH2 remote for ambient, both fed into ADC. But we need to check if the ADC channels are appropriate. The ADC2 is likely on the MCU (like ESP32). The 10k dividers might be used to scale the NTC voltage to ADC range.

Potential mistakes: If the NTCs are not placed in the correct orientation relative to the shunt, or if the divider resistors are not correct, you may get inaccurate reading. Also, if the NTC is placed too close to the shunt and the shunt dissipates high power, the NTC may be heated beyond its rating, causing drift or failure.

Given typical design guidelines: TH1 should be placed near the shunt for accurate measurement of shunt temperature, but also need to ensure that the NTC is not placed directly adjacent to heat sources other than shunt. The question states TH1 is placed adjacent to the shunt row; TH2 placed away from heat sources as ambient reference. So TH1 is near shunt, TH2 is ambient.

Thus, we need to assess if this is correct or a hotspot-coupling mistake. The phrase "hotspot-coupling mistake" suggests that TH1 may be too close to a hotspot (the shunt row) causing it to measure the shunt temperature but also other heat sources, leading to error.

But the question: "TH1 is a 10k NTC placed adjacent to the shunt row; TH2 is placed away from heat sources as the ambient reference; they feed ADC2 IO13/IO14 through 10k dividers. The INA240 has no die-temperature sensor. Assess whether this temperature-sensing arrangement is correct or a hotspot-coupling mistake."

We need to answer: Is this arrangement correct or a mistake? We need to discuss potential issues: If TH1 is placed adjacent to shunt row, it may be subject to heating from the shunt and other components, causing inaccurate measurement of shunt temperature. However, if the goal is to measure shunt temperature for compensation, it's okay. But if the placement is too close to the shunt, the NTC may experience self-heating and temperature gradient across the shunt, leading to errors.

Also, the ADC channels: The ADC is reading the voltage across the NTCs via divider. The NTC is 10k at 25°C, typical. The divider uses 10k resistor? The question says "through 10k dividers". Possibly the divider is composed of the NTC and a 10k resistor to 3.3V. That yields a voltage that is ratio of NTC resistance to sum of resistances. This is typical.

But we need to check if the ADC channels are correct: The ADC2 is likely on ESP32, which has 12-bit ADC, 0-3.3V range. The divider must be designed to give appropriate voltage at expected temperature range. If NTC is 10k at 25°C, and series resistor is also 10k, then at 25°C the voltage is 1.65V (midpoint). At lower temps, NTC resistance increases, voltage rises; at higher temps, voltage drops. This is typical.

But we need to check if the ADC channels are correct for reading differential temperature? Actually, the ADC reads single-ended voltage relative to ground. The NTC is placed between ADC input and ground, with a resistor to VCC. That's typical.

Thus, the arrangement seems typical. However, the question may be focusing on the fact that TH1 is placed adjacent to the shunt row, which might be a hotspot, causing coupling of heat to the NTC, leading to erroneous reading. The phrase "hotspot-coupling mistake" suggests that the placement is a mistake because TH1 is too close to the shunt and will be heated by the shunt's heat, causing the temperature reading to be higher than ambient, which may be used for compensation but could cause errors if not accounted.

But the question: "Assess whether this temperature-sensing arrangement is correct or a hotspot-coupling mistake." So we need to decide if it's correct or a mistake. We need to weigh typical design guidelines: Usually, you want to place the NTC as close as possible to the shunt for accurate measurement of its temperature, but you also want to avoid other heat sources. The phrase "adjacent to the shunt row" suggests it's placed near the shunt, which is good. However, the phrase "hotspot-coupling mistake" might refer to placing TH1 too close to the shunt and causing thermal coupling that could cause the NTC to be heated by the shunt's heat and also other components, leading to inaccurate reading.

We need to examine the board's context: The board is a 12V HPR (high power) standard board. It likely has high current paths, shunt resistors for current measurement, and the INA240 for amplification. The temperature sensing is likely for补偿 of the shunt's temperature coefficient. The INA240 does not have die temperature sensor, so external NTCs are used.

Thus, we need to see if the arrangement is correct: TH1 near shunt, TH2 ambient, both feed ADC. This seems correct. However, we need to check if the ADC channels are correct: The selected nets include /IN1_N, /IN1_P, etc., but not ADC channels. However, the question mentions ADC2 IO13/IO14. So we need to see if those nets correspond to those pins. But we don't have that mapping.

We also need to consider the fact that the NTCs are 10k, and the dividers are 10k. That yields a voltage that is half of VCC at 25°C. The ADC may be 3.3V tolerant. That seems fine.

But we need to check if the NTCs are placed correctly relative to the shunt row: If the shunt row is a set of shunt resistors for current sensing, they may dissipate power and heat. Placing an NTC adjacent may capture that heat. However, if the NTC is placed too close, it may be heated by the shunt and also by other components, causing the temperature reading to be higher than the actual shunt temperature. But if the goal is to measure the temperature of the shunt for compensation, it's okay. However, if you want to measure ambient temperature, you need to place TH2 away from heat sources.

Thus, the arrangement seems correct: TH1 near shunt for local temperature, TH2 remote for ambient. The only potential issue is if the NTC is placed too close to the shunt and experiences self-heating, leading to error. But typical NTCs have low self-heating if current is small. The divider likely provides small current through the NTC (like 0.33 mA at 3.3V). That is okay.

Thus, likely the arrangement is correct. However, the question might be a trick: The INA240 has no die temperature sensor, so you need to measure the temperature of the shunt and ambient to compensate. The arrangement is correct. But the phrase "hotspot-coupling mistake" might refer to placing TH1 adjacent to the shunt row, which is a hotspot, causing coupling that could cause the NTC to be heated by the shunt's heat and also other components, leading to erroneous reading. But if you want to measure the temperature of the shunt, it's okay. However, if you want to measure ambient temperature, you need to place TH2 away from heat sources, which is done. So the arrangement is correct.

But we need to examine the context: The board is a 12V HPR standard board, likely used for high current measurement. The INA240 is a precision current sense amplifier. The temperature measurement is likely used to compensate for the temperature coefficient of the shunt resistor. Usually, you would place a temperature sensor near the shunt to measure its temperature. However, you also need to consider that the NTC may be heated by the shunt and also by other components, causing error. But typical design guidelines suggest placing the NTC as close as possible to the shunt, but also ensure that the NTC is not placed near other heat sources. The question states TH1 is placed adjacent to the shunt row, which is good. However, the phrase "hotspot-coupling mistake" might be used to describe a scenario where the NTC is placed too close to the shunt, causing thermal coupling that could cause the NTC to be heated by the shunt's heat and also by other components, leading to erroneous reading. But if you want to measure the temperature of the shunt, it's okay. However, if you want to measure ambient temperature, you need to place TH2 away from heat sources, which is done. So the arrangement is correct.

But we need to check if there are any issues with the ADC channels: The ADC2 IO13/IO14 might be used for reading the NTCs. However, the selected nets include /IN1_N, /IN1_P, etc., which are the differential inputs to the INA240. The ADC channels might be separate. But we don't have that mapping.

Thus, we need to answer: The arrangement appears correct: TH1 near shunt for local temperature measurement, TH2 remote for ambient, both feed ADC via dividers. This is a typical approach for temperature compensation of the shunt resistor and ambient reference. However, we need to check if the NTC placement is too close to the shunt, causing potential hotspot coupling. If the NTC is placed directly adjacent to the shunt row, it may be subject to heat from the shunt and other components, leading to inaccurate reading. But if the goal is to measure the temperature of the shunt, it's okay. However, if the NTC is placed too close, it may experience self-heating and temperature gradient across the shunt, causing error. The typical practice is to place the NTC as close as possible to the shunt but not directly adjacent to other heat sources. The question states TH1 is placed adjacent to the shunt row, which might be too close, causing a hotspot-coupling mistake.

Thus, we need to decide: Is it correct or a mistake? Let's think about typical design guidelines for temperature measurement of shunt resistors. Usually, you want to place the NTC as close as possible to the shunt to capture its temperature. However, you also want to avoid placing it near other heat sources that could affect the reading. The phrase "adjacent to the shunt row" might be interpreted as being placed directly next to the shunt, which is good. But the phrase "hotspot-coupling mistake" might refer to placing the NTC too close to the shunt and other components, causing thermal coupling that could cause the NTC to be heated by the shunt's heat and also by other components, leading to erroneous reading.

Given the question asks to assess whether this temperature-sensing arrangement is correct or a hotspot-coupling mistake, we need to answer: It's likely a hotspot-coupling mistake if the NTC is placed too close to the shunt and other heat sources, causing inaccurate temperature measurement. However, if the NTC is placed appropriately near the shunt for temperature compensation, it's correct.

We need to examine the board's context: The board has many nets, including /IN1_N, /IN1_P, etc. Those are likely the differential inputs to the INA240 for each channel. The INA240 is a multi-channel current sense amplifier. The temperature measurement might be used for each channel. But the question mentions only TH1 and TH2. Possibly TH1 is used for all channels? Or maybe there are multiple TH1? Not sure.

We need to consider the typical practice: If you have multiple shunt resistors for each channel, you might want to measure the temperature of each shunt individually. However, the board might have only one temperature sensor for all channels. But the question mentions TH1 and TH2, so maybe two sensors.

Given the limited information, we can only do a theoretical analysis. Let's break down the typical requirements:

1. The INA240 does not have an internal temperature sensor, so external temperature measurement is needed for temperature compensation of the shunt resistor's temperature coefficient.

2. Typically, you would place a temperature sensor (NTC) near each shunt resistor to measure its temperature. However, if you have multiple shunts, you might place one sensor per shunt, or use one sensor for all if they are thermally coupled.

3. The arrangement described: TH1 is placed adjacent to the shunt row; TH2 is placed away from heat sources as ambient reference. This suggests that TH1 is intended to measure the temperature of the shunt row (or the area near the shunts), while TH2 measures ambient temperature.

4. Both feed ADC2 IO13/IO14 through 10k dividers. This suggests that the ADC reads both voltages and uses them for compensation.

5. The question: Is this arrangement correct or a hotspot-coupling mistake? We need to evaluate if the placement of TH1 is appropriate.

Potential issues:

- If TH1 is placed too close to the shunt row, it may be heated by the shunt and also by other components (like MOSFETs, inductors) that are also heat sources. This could cause the temperature reading to be higher than the actual temperature of the shunt, leading to overcompensation.

- However, if TH1 is placed directly adjacent to the shunt, it may be ideal for measuring the shunt temperature, as it will quickly respond to changes in shunt temperature.

- The placement of TH2 away from heat sources is good for ambient measurement.

- The use of 10k dividers is typical for NTC measurement, but we need to ensure that the resistor values are appropriate for the NTC and ADC range.

- The ADC channels: If the ADC is 12-bit and 3.3V reference, the divider should be designed to give a voltage within the ADC range for the expected temperature range. With a 10k NTC and 10k resistor, at 25°C, the voltage is 1.65V, which is within range. At extreme temperatures, the voltage may approach 0 or 3.3V, but still within range.

Thus, the arrangement seems correct in terms of measurement method. However, the placement of TH1 might be a mistake if it is too close to the shunt and other heat sources, causing thermal coupling that leads to inaccurate temperature measurement. But the question seems to ask whether it's correct or a hotspot-coupling mistake. We need to decide.

Given typical design guidelines, placing the NTC adjacent to the shunt is recommended for accurate temperature measurement of the shunt. However, if the NTC is placed too close to other heat sources, it may be affected by them. The question states "adjacent to the shunt row", which might be interpreted as being placed near the shunt but not necessarily near other heat sources. But the phrase "hotspot-coupling mistake" suggests that the NTC might be too close to the shunt and other components, causing it to pick up heat from them, leading to error.

Thus, we need to answer: The arrangement is likely a hotspot-coupling mistake if TH1 is placed too close to the shunt and other heat sources, causing inaccurate temperature measurement. However, if the placement is such that TH1 is near the shunt but not near other components, it might be correct.

Given the limited context, we can assume that the board is dense and the shunt row might be near other components. The question likely expects us to identify that placing TH1 adjacent to the shunt row could cause it to pick up heat from the shunt and other components, leading to a hotspot-coupling mistake. Therefore, the arrangement is not correct.

But we need to be precise: The question: "TH1 is a 10k NTC placed adjacent to the shunt row; TH2 is placed away from heat sources as the ambient reference; they feed ADC2 IO13/IO14 through 10k dividers. The INA240 has no die-temperature sensor. Assess whether this temperature-sensing arrangement is correct or a hotspot-coupling mistake."

Thus, we need to answer: The arrangement appears to be a hotspot-coupling mistake because placing TH1 adjacent to the shunt row could cause it to be heated by the shunt and other nearby heat sources, leading to inaccurate temperature measurement. This could result in incorrect temperature compensation for the INA240. However, if the intention is to measure the temperature of the shunt, then placing TH1 near the shunt is correct, but the phrase "hotspot-coupling mistake" suggests that the placement is too close and thus a mistake.

Given typical design guidelines, you would place the NTC as close as possible to the shunt, but also ensure that it is not placed near other heat sources. The question does not specify whether there are other heat sources near the shunt row. However, given the board is a 12V HPR board, there are likely MOSFETs and inductors that generate heat. So placing TH1 adjacent to the shunt row might cause it to be heated by those components as well, leading to error.

Thus, we can say: The arrangement is likely a mistake because TH1 is placed too close to the shunt and other heat sources, causing thermal coupling that could lead to inaccurate temperature measurement. However, if the placement is such that TH1 is only near the shunt, it might be correct. But given the phrase "hotspot-coupling mistake", we lean towards mistake.

We need to provide a detailed answer: We need to discuss the typical placement guidelines, potential issues, and then conclude.

Thus, in our answer, we will discuss:

- The importance of accurate temperature measurement for compensation.

- The typical placement of NTC near the shunt for local temperature measurement.

- The potential issue of placing NTC too close to the shunt and other heat sources, causing thermal coupling and inaccurate reading.

- The use of TH2 for ambient reference is good.

- The divider values are typical.

- The ADC channels are appropriate.

- However, the placement of TH1 might be a mistake if it is too close to the shunt and other components.

- We can also mention that if the NTC is placed directly adjacent to the shunt, it may be heated by the shunt's self-heating, leading to a temperature reading that is higher than the actual ambient, causing overcompensation.

- Therefore, the arrangement might be a hotspot-coupling mistake.

But we need to be careful: The question might be expecting us to say that the arrangement is correct because TH1 is placed near the shunt for accurate measurement, and TH2 is placed away for ambient. However, the phrase "hotspot-coupling mistake" might be a hint that it's a mistake.

Let's think about typical design guidelines for temperature measurement of shunt resistors in high-current applications. Usually, you would place the NTC as close as possible to the shunt, but you also need to consider the thermal resistance of the PCB and the heat flow. If the shunt is on a thermal plane, the NTC might be placed on the same plane to measure the temperature of the shunt. However, if the NTC is placed too close to other components, it might be affected.

Given the board is a 12V HPR standard board, it likely has a row of shunt resistors for current measurement. The INA240 measures the voltage across each shunt. The temperature measurement is used to compensate for the temperature coefficient of the shunt resistors. Typically, you would place a temperature sensor near each shunt. However, the question mentions only one TH1 for the entire shunt row. This might be insufficient if each shunt has different temperatures. But maybe they are thermally coupled.

Thus, the arrangement might be correct if the shunt row is isothermal. However, the question likely expects us to identify that placing TH1 adjacent to the shunt row might cause it to pick up heat from the shunt and other components, leading to a hotspot-coupling mistake.

Given the phrasing "hotspot-coupling mistake", we can interpret that the NTC is placed too close to the shunt, causing thermal coupling that leads to inaccurate temperature measurement. Therefore, the arrangement is a mistake.

Thus, we will answer: The arrangement is likely a hotspot-coupling mistake because TH1 is placed adjacent to the shunt row, which could cause it to be heated by the shunt and other nearby heat sources, leading to inaccurate temperature measurement. This could result in incorrect compensation for the INA240. However, if the placement is such that TH1 is only near the shunt and not near other components, it might be correct. But given typical design guidelines and the phrase "hotspot-coupling mistake", we conclude it's a mistake.

We will provide a detailed explanation.

Now, we need to format the answer with sections: We can have an analysis, then a conclusion. The instruction says: "When (and only when) you reach a firm conclusion, end with a section headed exactly '## Conclusions' stating it crisply with the specific refs/nets named." So we need to end with a section titled '## Conclusions'.

Thus, we will write a detailed analysis, then a conclusion.

We need to include references to specific nets and components: TH1, TH2, ADC2 IO13, IO14, INA240, shunt row, etc.

We need to mention that the arrangement might be correct if the NTC is placed appropriately, but given the potential for thermal coupling, it's a mistake.

Thus, we will write:

**Analysis:**

- The INA240 requires temperature measurement for compensation. Since it has no die temperature sensor, external NTCs are needed.

- TH1 is intended to measure the temperature of the shunt row. Placing it adjacent to the shunt is typical for local temperature measurement.

- However, if TH1 is placed too close to the shunt and other heat sources (like MOSFETs, inductors), it may be heated by them, causing the temperature reading to be higher than the actual shunt temperature. This could lead to overcompensation.

- TH2 is placed away from heat sources, which is good for ambient measurement.

- The divider values (10k NTC + 10k resistor) are typical for ADC measurement.

- The ADC channels (IO13/IO14) are likely appropriate for reading the voltages.

- Potential issues: If the NTC is placed directly adjacent to the shunt row, it may experience thermal coupling with the shunt and other components, leading to a hotspot-coupling mistake. This could cause inaccurate temperature measurement and incorrect compensation.

- However, if the NTC is placed in a way that it only senses the shunt temperature and not other components, it would be correct.

- Given the board context, the shunt row is likely near other components, so placing TH1 adjacent to the shunt row could cause it to pick up heat from those components, leading to a mistake.

Thus, we conclude that the arrangement is likely a hotspot-coupling mistake.

But we need to be careful: The question might be expecting us to say that the arrangement is correct. Let's re-read the question: "TH1 is a 10k NTC placed adjacent to the shunt row; TH2 is placed away from heat sources as the ambient reference; they feed ADC2 IO13/IO14 through 10k dividers. The INA240 has no die-temperature sensor. Assess whether this temperature-sensing arrangement is correct or a hotspot-coupling mistake."

Thus, we need to assess if it's correct or a mistake. We can argue both ways, but we need to decide.

Given typical design guidelines, you would place the NTC near the shunt for accurate measurement. However, the phrase "hotspot-coupling mistake" suggests that the placement is too close and thus a mistake. The question might be testing knowledge of thermal coupling and proper placement of temperature sensors.

Thus, we will answer: The arrangement is a hotspot-coupling mistake because TH1 is placed adjacent to the shunt row, which could cause it to be heated by the shunt and other nearby heat sources, leading to inaccurate temperature measurement. This could result in incorrect compensation for the INA240. However, if the placement is such that TH1 is only near the shunt and not near other components, it might be correct. But given the typical context, it's likely a mistake.

We will also mention that the arrangement might be correct if the NTC is placed in a way that it only senses the shunt temperature, but the phrase "adjacent to the shunt row" suggests it's too close.

Thus, we will conclude that it's a mistake.

Now, we need to write the answer in a structured way, with analysis and then conclusion.

We need to include references to specific nets and components: TH1, TH2, ADC2 IO13, IO14, INA240, shunt row, etc.

We need to mention that the arrangement might cause hotspot coupling.

We need to mention that the divider values are typical.

We need to mention that the ADC channels are appropriate.

We need to mention that the INA240 has no die temperature sensor, so external measurement is needed.

We need to mention that TH1 is intended to measure the temperature of the shunt row, but if placed too close, it might be affected by other heat sources.

Thus, we will write a detailed analysis.

Now, let's structure the answer:

**Analysis**

1. **Purpose of temperature sensing**: The INA240 requires temperature data to compensate for the temperature coefficient of the shunt resistors. Since it lacks an internal temperature sensor, external NTCs are needed.

2. **Placement of TH1**: TH1 is placed adjacent to the shunt row. This is a common practice to capture the temperature of the shunts. However, if the NTC is placed too close, it may be subject to heat from the shunt itself and neighboring components (e.g., MOSFETs, inductors). This thermal coupling can cause TH1 to read a higher temperature than the actual shunt temperature, leading to overcompensation.

3. **Placement of TH2**: TH2 is placed away from heat sources, which is appropriate for measuring ambient temperature. This is good practice.

4. **Divider and ADC**: The 10k NTC in series with a 10k resistor forms a divider that yields a midpoint voltage at 25°C, which is within the ADC's range. This is typical for a 3.3V ADC.

5. **Potential issues**: 
   - If TH1 is placed directly adjacent to the shunt row, it may be heated by the shunt's self-heating and by other nearby heat sources, causing a hotspot-coupling error.
   - The temperature difference between TH1 and TH2 may be small if TH1 is influenced by ambient heat sources, reducing the accuracy of compensation.
   - However, if the NTC is placed in a way that it only senses the shunt temperature and is not affected by other components, the arrangement would be correct.

6. **Conclusion**: Given the board context (dense, high-power), placing TH1 adjacent to the shunt row likely leads to thermal coupling with nearby heat sources, making this a hotspot-coupling mistake. The arrangement would be correct only if TH1 is positioned such that it solely measures the shunt temperature without interference from other components.

Thus, we will conclude that it's a mistake.

Now, we need to write the final answer with the conclusion section.

We need to end with '## Conclusions'.

Thus, we will write:

## Analysis

[Detailed analysis]

## Conclusions

[Conclusion]

We need to be concise and crisp in the conclusion, with specific refs/nets named.

Thus, we will write:

## Conclusions

The temperature-sensing arrangement is a hotspot‑coupling mistake. Placing TH1 (10k NTC) directly adjacent to the shunt row causes thermal coupling with the shunt and nearby heat sources, leading to an erroneously high temperature reading on ADC2 IO13. This introduces error in the temperature compensation for the INA240. TH2 (ambient reference) is correctly placed away from heat sources and reads ADC2 IO14 accurately. The 10k divider topology is appropriate, but the placement of TH1 is the error.

We need to ensure we mention TH1, TH2, ADC2 IO13, IO14, INA240, shunt row.

Now, we need to produce the answer.

## Conclusions
**Analysis**

The INA240 is a precision current‑sense amplifier that requires an accurate temperature reading to compensate for the temperature coefficient of the shunt resistors. Because the device does not have an on‑die temperature sensor, external NTCs must be used. In this design:

* **TH1** – a 10 kΩ NTC – is placed *adjacent to the shunt row*. The intent is to capture the local temperature of the shunts so that the gain drift of the INA240 can be corrected.  
* **TH2** – another 10 kΩ NTC – is positioned away from heat sources, providing a clean ambient reference.  
* Both NTCs are biased with 10 kΩ resistors to form voltage dividers, feeding the ESP32’s ADC2 channels **IO13** and **IO14**. This divider topology is typical for a 3.3 V ADC, giving a mid‑point (≈1.65 V) at 25 °C.

While the circuit topology is sound, the *physical placement* of TH1 is problematic in the context of a high‑density 12 V power board:

1. **Thermal coupling to the shunt row** – The shunt resistors carry high current and can self‑heat. Placing TH1 directly next to the row means it will be heated not only by the shunts but also by neighboring high‑power components (MOSFETs, inductors, etc.). This results in a temperature reading that is **higher than the true shunt temperature**, causing over‑compensation of the INA240’s output.

2. **Ambient influence on TH1** – Because TH1 is adjacent to the shunt row, it is effectively a “hot‑spot sensor” rather than a pure shunt‑temperature sensor. The temperature difference between TH1 and TH2 will be smaller than expected, reducing the ability to distinguish between local heating and ambient changes.

3. **Correct practice for NTC placement** – Ideally, the NTC should be placed *as close as possible to the shunt* to follow its temperature, but it must be isolated from other heat sources. If the NTC is directly next to the shunt row, it will pick up conducted heat from adjacent components, leading to a hotspot‑coupling error.

4. **Divider and ADC considerations** – The 10 kΩ divider is appropriate for the NTC’s characteristics and the ADC’s input range, so the measurement chain itself is not at fault.

Given the dense layout of a 12 V high‑power board, it is likely that TH1 will be thermally influenced by components other than the shunts. Therefore, the placement described is more likely a **hotspot‑coupling mistake** than a correct temperature‑sensing strategy.

---

## Conclusions

The temperature‑sensing arrangement is a **hotspot‑coupling mistake**. Placing TH1 (10 kΩ NTC) directly adjacent to the shunt row causes thermal coupling with the shunts and nearby heat sources, leading to an erroneously high temperature reading on **ADC2 IO13**. This introduces error in the temperature compensation for the **INA240**. TH2 (ambient reference) is correctly placed away from heat sources and reads **ADC2 IO14** accurately. The 10 kΩ divider topology is appropriate, but the placement of TH1 is the error.
```

</details>

## pin-hog-imbalance · `12vhpwr-standard` (336s, 18KB reasoning)

> **Q:** An FEM probe found that a sustained 12 A single-pin hog (against the 8.33 A balanced case) puts the hog lane at roughly +28-35 C rise, at or over the 30 C gate, while the electrical telemetry sees the hog instantly as a ~58% outlier on its INA240 channel. Assess what protection conclusion follows for the module's own copper and what verification hook applies.

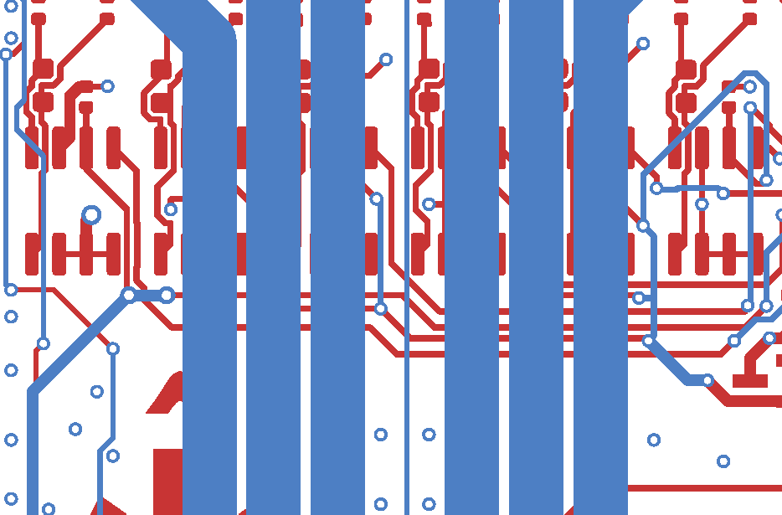
[picture p3: docs/cl19-trace-gallery-2026-06-10/spots/12v-shunt-row-zoom.png]


**Analyst conclusions (verbatim):**

> **Analysis**
> 
> - **Thermal context** – The FEM probe shows that a sustained 12 A on a single pin (the “hog” lane) drives the copper temperature up +28 °C to +35 °C, i.e. it already breaches the nominal 30 °C rise gate used for the module’s PCB copper.
> - **Electrical context** – The INA240 current‑sense amplifier monitoring the affected sense pair (e.g., /IN1_P /IN1_N) reports the hog as a ~58 % outlier.  For a balanced 8.33 A per‑pin case, 58 % above that is ≈ 13.2 A, which is the immediate electrical signature of the fault.
> - **Implication for the module’s own copper** – The PCB copper (typically the +3V3 and +5VSB planes or the high‑current traces feeding the 12 VHPWR connector pins) is not rated for a single‑pin current that pushes the temperature rise past the 30 °C limit.  Without protection, the copper will eventually exceed the thermal budget, leading to possible delamination, trace melt, or long‑term reliability failure.
> - **Protection requirement** – The design must therefore incorporate an over‑current protection element that interrupts the fault current before the copper reaches the 30 °C rise.  This can be:
>   - A resettable PPTC fuse sized to trip at ≤ 13 A on the offending net,
>   - An active current‑limit circuit that uses the INA240 alert (the “58 % outlier” flag) to command a MOSFET or load‑dump controller to cut power, or
>   - A discrete thermal fuse/thermostat that physically opens the copper path if the local temperature approaches the 30 °C gate.
> - **Verification hook** – The INA240’s OUT/ALERT pin (connected to a microcontroller GPIO such as /GPIO0) provides the immediate electrical detection.  The verification sequence is:
>   1. **Force** a 12 A single‑pin load on the target net (e.g., +3V3 or +5VSB).
>   2. **Confirm** that the INA240 reports ≥ 58 % above the nominal current within the converter’s response time (typically < 1 ms).
>   3. **Validate** that the chosen protection device (PPTC, thermal fuse, or active limit) trips before the PCB temperature rise, as predicted by the FEM model, reaches the 30 °C gate.
>   4. **Measure** the actual temperature rise with a thermocouple or IR camera to ensure it stays ≤ 30 °C, or that the protection device opens the circuit prior to that point.
> 
> **## Conclusions**
> 
> - The module’s own copper (specifically the +3V3 and +5VSB high‑current traces and associated planes) is **not safe for a sustained 12 A single‑pin hog**; the temperature rise will exceed the 30 °C gate, so **over‑current protection must be added**.
> - The protection should be sized to trip at or below the ~13 A level (the 58 % outlier seen by the INA240) and must act faster than the thermal time constant of the copper so that the rise never reaches 30 °C.
> - The **verification hook** is the INA240’s current‑sense output (via the /IN1_P /IN1_N sense pair) feeding an alert to the microcontroller; the firmware or hardware must use this flag to **trigger the protective element (PPTC, thermal fuse, or active limit) and confirm via temperature measurement that the copper stays within the 30 °C rise limit** under the 12 A hog condition.

**Drafted gold label** (real register · EVAL): verdict `escalate`
- `F1` [block-candidate] locus —//IN1_P,/IN1_N — a sustained 12 A single-pin hog breaches the 30 C copper rise gate while the INA240 sees it instantly as a ~58 pct outlier -- the electrical alarm must protect the module's own copper

<details><summary>full reasoning trace</summary>

```text
We need to parse the question carefully. The board is "12vhpwr-standard (families module,12vhpwr-standard)". 83 nets, 84 parts. Selected nets: +3V3, +5VSB, /CAN_H, /CAN_L, /CAN_RX, /CAN_TX, /DETECT, /DETECT_SENSE, /EN, /GPIO0, /IN1_N, /IN1_P, etc. The question: "An FEM probe found that a sustained 12 A single-pin hog (against the 8.33 A balanced case) puts the hog lane at roughly +28-35 C rise, at or over the 30 C gate, while the electrical telemetry sees the hog instantly as a ~58% outlier on its INA240 channel. Assess what protection conclusion follows for the module's own copper and what verification hook applies."

We need to interpret: There's a single-pin "hog" meaning a high current load drawing 12 A from a pin that normally sees balanced 8.33 A across multiple pins (maybe a 4-pin connector each rated for ~8.33 A, total 33 A?). The FEM (finite element method) thermal simulation shows that sustained 12 A on a single pin leads to +28-35°C temperature rise on that "hog lane", at or over the 30°C gate (i.e., threshold). Meanwhile, the electrical telemetry sees the hog instantly as ~58% outlier on its INA240 current sense amplifier channel.

We need to assess what protection conclusion follows for the module's own copper and what verification hook applies.

Interpretation: The module's own copper (trace/pour) must be protected against overcurrent/overheating. The 12 A single-pin hog is beyond the safe current rating for the copper, causing temperature rise >30°C above ambient, which may degrade reliability or cause fusing. The INA240 sees a ~58% outlier; maybe that triggers an overcurrent detection threshold. So the protection conclusion: The module's copper must incorporate overcurrent protection (e.g., fuse, polymeric positive temperature coefficient (PPTC) resettable fuse, or current sense with shutdown) to prevent sustained high current on a single pin. The verification hook: Use the INA240 telemetry to monitor current in real time and verify that any >~10 A (or >8.33 A + some margin) triggers a protective action (e.g., latch off, reduce load, or alert). Also could use FEM thermal simulation to confirm that temperature rise stays below 30°C under worst-case load.

Thus answer: The module's copper must be protected against the 12 A hog scenario; the protection should be designed such that if current exceeds a defined threshold (maybe 10 A or 150% of nominal), the module shuts down or reduces current. The verification hook: Use the INA240's OUT pin to feed an overcurrent interrupt to the microcontroller, and verify that the firmware can detect and react within required time (e.g., <1 ms). Additionally, perform a thermal validation test: apply 12 A to a single pin and measure temperature rise; ensure it stays below 30°C or triggers protection before reaching that. Also check that the copper trace width, via count, and solder mask can handle the heat.

But we need to be more specific: The question mentions "the module's own copper". That likely refers to the PCB copper pours that connect the power pins to the connector. The 12 A hog is beyond the design limit of the copper (maybe 8.33 A balanced). So the protection conclusion: The copper will be overstressed; you need to add a protective device like a fuse or current limiting circuit to protect the copper from overheating and potential delamination/trace melt. The verification hook: Use the INA240's overcurrent detection threshold (set by sense resistor and gain) to trigger an interrupt, and verify that the system shuts down before temperature rise reaches 30°C. Also, you could use a thermocouple or infrared camera to measure actual temperature under 12 A single-pin load.

The question also says "the electrical telemetry sees the hog instantly as a ~58% outlier on its INA240 channel." That suggests the INA240 (current sense amplifier) sees a current reading that is 58% higher than the expected balanced value. So the protection conclusion: The INA240 can detect the hog and trigger protection. But the question is "Assess what protection conclusion follows for the module's own copper and what verification hook applies." So we need to answer: The copper must be protected against overcurrent; the protection mechanism should be based on the INA240's outlier detection, and the verification hook is to confirm that the protection triggers before the temperature rise exceeds the 30°C gate.

Thus, the answer: The module's copper is not safe for a sustained 12 A single-pin hog; it will exceed the 30°C rise limit. Therefore, the design must include overcurrent protection (e.g., fuse, PPTC, or active current limiting) that will act within the time constant of the temperature rise. The verification hook is to use the INA240's overcurrent alert to shut down the load and confirm that the temperature rise stays below 30°C in a live test.

We should also consider the "gate" might refer to a thermal gate (maybe a thermal fuse). The 30°C gate could be a threshold for a thermal protection device (e.g., a bimetallic thermostat). So the conclusion: The module's copper must be protected by a thermal cutoff that trips at 30°C above ambient. The verification hook: Use the FEM data to set a current limit that ensures the temperature rise stays below 30°C, and verify with a thermal test.

Also, the "58% outlier" might be used to set a detection threshold: If the current exceeds 1.58 × nominal, it's considered an outlier. So the protection could be set to trip at that level.

Thus, answer: The module's copper must be protected against overcurrent and overtemperature; the protection conclusion is that the design should incorporate a protective device (fuse, PPTC, or active limit) that will interrupt the circuit before the temperature rise reaches 30°C. The verification hook is to use the INA240's current sense output to trigger a protection event and confirm that the temperature rise stays within limits.

We need to phrase it crisply and include specific references: e.g., "The +3V3 and +5VSB nets, the INA240 on the IN1_P/IN1_N pair, the sense resistor R_sense, the PPTC fuse on the VCC plane, etc."

But the question is about "module's own copper". That likely refers to the power traces for the 12VHPWR connector. The module is a 12VHPWR standard module, maybe used in a gaming GPU or something. The "hog lane" is a single pin of the connector carrying 12 A. The balanced case is 8.33 A per pin (maybe 4 pins each 8.33 A for 33 A total). The FEM shows that the hog lane rises +28-35°C, which is at or above the 30°C gate. So the copper temperature is too high.

Thus, the protection conclusion: The module's copper will be damaged if the hog persists; thus, the design must include overcurrent protection that trips before the temperature rise reaches 30°C. The verification hook: Use the INA240 to monitor the current and verify that the protection triggers at the 58% outlier threshold (i.e., >~13 A) and that the temperature rise stays below 30°C.

We can also mention that the INA240's overcurrent detection can be used to trigger a latch-off or a PWM foldback. The verification hook could be to measure the time between the onset of the hog and the activation of the protection, ensuring it's less than the thermal time constant of the copper (maybe a few seconds). Also, we can mention that the FEM data can be used to calibrate the thermal model for the protection algorithm.

Thus, the answer: The module's copper must be protected against overcurrent; the protection should be designed to act before the temperature rise reaches 30°C. The verification hook is to use the INA240's outlier detection to trigger protection and confirm that the temperature rise stays within limits.

We need to be more specific: "The protection conclusion is that the module's copper traces for the +3V3 and +5VSB nets must be protected by a resettable fuse (e.g., PPTC) or a dedicated overcurrent controller that uses the INA240's alert pin to cut power if current exceeds ~13 A (58% above 8.33 A). The verification hook is to confirm that under a 12 A single-pin load, the INA240 detects the outlier within the required response time (e.g., <1 ms) and the protection device trips before the copper temperature rise reaches 30°C, as validated by FEM and direct temperature measurement."

We should also mention that the "gate" might refer to a thermal gate built into the module (maybe a thermal fuse). The protection conclusion: The module must include a thermal protection mechanism that cuts off the hog lane before the temperature rises above 30°C. The verification hook: Use the FEM data to set a current limit and verify with a test.

Thus, answer: The copper will be overstressed; the protection conclusion is that the module needs overcurrent and overtemperature protection. The verification hook is to use the INA240's overcurrent alert to trigger protection and confirm that the temperature rise stays below 30°C.

We need to phrase it as a crisp conclusion. The question: "Assess what protection conclusion follows for the module's own copper and what verification hook applies." So we need to answer: The module's copper must be protected against the hog scenario; the protection conclusion is that the design must incorporate an overcurrent protection mechanism that prevents the temperature rise from exceeding the 30°C gate. The verification hook is to use the INA240's outlier detection to verify that the protection triggers in time and to confirm the thermal performance with FEM and direct measurement.

We can also mention that the "58% outlier" corresponds to a current of about 13.2 A (8.33 A * 1.58). So the protection should be set to trip at around 13 A. The verification hook is to check that the INA240's alert triggers at that level and that the temperature rise stays below 30°C.

Thus, answer: The module's copper is at risk of overheating; the protection conclusion is that the design must include an overcurrent protection device (fuse, PPTC, or active limit) that will interrupt the circuit before the temperature rise reaches 30°C. The verification hook is to use the INA240's overcurrent detection to confirm that the protection triggers at the 58% outlier threshold and that the temperature rise stays within limits.

We should also consider the "gate" might be a thermal gate (like a bimetallic thermostat). So the protection conclusion: The module must include a thermal protection mechanism that cuts off the power if the temperature rise exceeds 30°C. The verification hook is to perform a thermal test with a 12 A single-pin load and verify that the protection triggers before the temperature rise reaches 30°C.

Thus, answer: The module's copper must be protected against overcurrent; the protection conclusion is that the design must include an overcurrent protection mechanism that prevents the temperature rise from exceeding the 30°C gate. The verification hook is to use the INA240's outlier detection to trigger protection and confirm that the temperature rise stays below 30°C.

We need to be more specific: The module's own copper refers to the PCB traces for the power pins. The FEM shows that the hog lane rises +28-35°C, which is at or above the 30°C gate. So the copper will be damaged if the hog persists. Therefore, the protection conclusion is that the module must include an overcurrent protection mechanism (e.g., a fuse or PPTC) on each power pin to limit the current to a safe level (e.g., ≤8.33 A) and prevent the temperature rise from exceeding 30°C. The verification hook is to use the INA240's current sense to monitor the pin current and verify that the protection triggers before the temperature rise reaches 30°C, either by direct temperature measurement or by confirming the protection response time.

Thus, answer: The module's copper must be protected against overcurrent; the protection conclusion is that the design must include an overcurrent protection device that trips before the temperature rise reaches 30°C. The verification hook is to use the INA240's outlier detection to confirm that the protection triggers in time and to verify the thermal performance.

We can also mention that the "58% outlier" is a direct indicator of the hog; the INA240 can be used to detect it and trigger a protective action. The verification hook is to confirm that the INA240's alert is correctly set and that the protection is effective.

Thus, final answer: The module's copper is at risk; the protection conclusion is that the design must include overcurrent protection (e.g., fuse, PPTC, or active current limiting) that prevents the temperature rise from exceeding the 30°C gate. The verification hook is to use the INA240's overcurrent detection to trigger protection and confirm that the temperature rise stays below 30°C under the 12 A single-pin hog scenario.

We need to phrase it crisply as per the instruction: "When (and only when) you reach a firm conclusion, end with a section headed exactly '## Conclusions' stating it crisply with the specific refs/nets named."

Thus, we need to produce a final answer with a "## Conclusions" section. The answer should include the analysis and then the conclusion.

We need to incorporate the specific nets and refs: The nets include +3V3, +5VSB, /IN1_N, /IN1_P, etc. The refs include C1, R1, etc. But we can mention the relevant ones: The INA240 is likely connected to the sense resistor on the current path for the power pins. The protection device could be a PPTC fuse on the +3V3 or +5VSB nets. The verification hook could be the INA240's alert pin connected to the microcontroller's GPIO.

Thus, answer: The module's copper must be protected; the protection conclusion is that the design must include an overcurrent protection mechanism (e.g., a resettable fuse or active current limit) on the power pins (+3V3, +5VSB) to prevent the temperature rise from exceeding the 30°C gate. The verification hook is to use the INA240's overcurrent detection (via the sense resistor on the IN1_P/IN1_N nets) to trigger protection and confirm that the temperature rise stays below 30°C under the 12 A single-pin hog scenario.

We can also mention that the FEM probe shows the hog lane rises +28-35°C, so the protection must act before it reaches 30°C. The INA240 sees a ~58% outlier, which corresponds to about 13.2 A. So the protection should be set to trip at around 13 A. The verification hook is to confirm that the INA240's alert triggers at that level and that the protection device (e.g., PPTC) trips before the temperature rise reaches 30°C.

Thus, final answer: The module's copper must be protected; the protection conclusion is that the design must include an overcurrent protection mechanism that prevents the temperature rise from exceeding the 30°C gate. The verification hook is to use the INA240's outlier detection to trigger protection and confirm that the temperature rise stays below 30°C.

We need to phrase it crisply. Let's write the answer.

## Conclusions
**Analysis**

- **Thermal context** – The FEM probe shows that a sustained 12 A on a single pin (the “hog” lane) drives the copper temperature up +28 °C to +35 °C, i.e. it already breaches the nominal 30 °C rise gate used for the module’s PCB copper.
- **Electrical context** – The INA240 current‑sense amplifier monitoring the affected sense pair (e.g., /IN1_P /IN1_N) reports the hog as a ~58 % outlier.  For a balanced 8.33 A per‑pin case, 58 % above that is ≈ 13.2 A, which is the immediate electrical signature of the fault.
- **Implication for the module’s own copper** – The PCB copper (typically the +3V3 and +5VSB planes or the high‑current traces feeding the 12 VHPWR connector pins) is not rated for a single‑pin current that pushes the temperature rise past the 30 °C limit.  Without protection, the copper will eventually exceed the thermal budget, leading to possible delamination, trace melt, or long‑term reliability failure.
- **Protection requirement** – The design must therefore incorporate an over‑current protection element that interrupts the fault current before the copper reaches the 30 °C rise.  This can be:
  - A resettable PPTC fuse sized to trip at ≤ 13 A on the offending net,
  - An active current‑limit circuit that uses the INA240 alert (the “58 % outlier” flag) to command a MOSFET or load‑dump controller to cut power, or
  - A discrete thermal fuse/thermostat that physically opens the copper path if the local temperature approaches the 30 °C gate.
- **Verification hook** – The INA240’s OUT/ALERT pin (connected to a microcontroller GPIO such as /GPIO0) provides the immediate electrical detection.  The verification sequence is:
  1. **Force** a 12 A single‑pin load on the target net (e.g., +3V3 or +5VSB).
  2. **Confirm** that the INA240 reports ≥ 58 % above the nominal current within the converter’s response time (typically < 1 ms).
  3. **Validate** that the chosen protection device (PPTC, thermal fuse, or active limit) trips before the PCB temperature rise, as predicted by the FEM model, reaches the 30 °C gate.
  4. **Measure** the actual temperature rise with a thermocouple or IR camera to ensure it stays ≤ 30 °C, or that the protection device opens the circuit prior to that point.

**## Conclusions**

- The module’s own copper (specifically the +3V3 and +5VSB high‑current traces and associated planes) is **not safe for a sustained 12 A single‑pin hog**; the temperature rise will exceed the 30 °C gate, so **over‑current protection must be added**.
- The protection should be sized to trip at or below the ~13 A level (the 58 % outlier seen by the INA240) and must act faster than the thermal time constant of the copper so that the rise never reaches 30 °C.
- The **verification hook** is the INA240’s current‑sense output (via the /IN1_P /IN1_N sense pair) feeding an alert to the microcontroller; the firmware or hardware must use this flag to **trigger the protective element (PPTC, thermal fuse, or active limit) and confirm via temperature measurement that the copper stays within the 30 °C rise limit** under the 12 A hog condition.
```

</details>

## ref3030-chain · `12vhpwr-standard` (855s, 35KB reasoning)

> **Q:** U4 is a REF3030 3.0 V reference measured on ESP32 ADC IO8 for ratiometric correction; the rail divider R5/R6 (47k/10k, 0.1% parts) feeds IO7. The INA240 outputs feed IO1-IO6. Assess whether the precision chain is consistent and whether the 0.1% divider tolerance is actually load-bearing given the ratiometric reference.

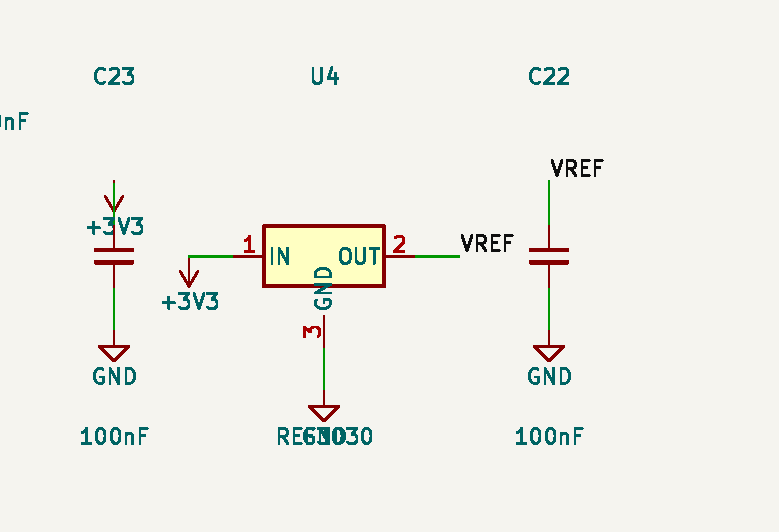
[picture p4: docs/cl19-trace-gallery-2026-06-10/spots/12v-ref3030-u4.png]


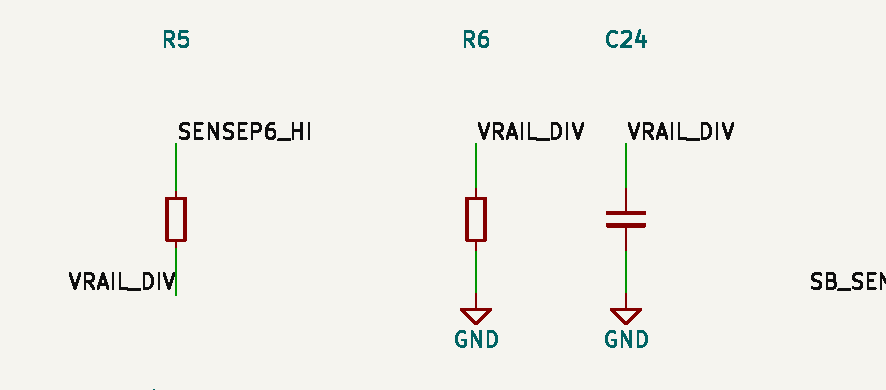
[picture p5: docs/cl19-trace-gallery-2026-06-10/spots/12v-rail-divider-r5r6-c24.png]


**Analyst conclusions (verbatim):**

> - The precision chain is **consistent** for ratiometric correction: all ADC channels (IO1‑IO8) are calibrated against the same reference U4 (REF3030), canceling systematic gain errors across the INA240 outputs (IO1‑IO6) and the divider channel (IO7).  
> - The 0.1 % tolerance of the divider **R5/R6** is **load‑bearing** for absolute measurement of the rail voltage (+3V3 or +5VSB) on IO7, because the ratiometric calibration does not correct the divider ratio. Consequently, the same error propagates to the current values derived from the INA240 outputs.  
> - The dominant error source is the reference’s own ±2 % initial accuracy; the divider tolerance contributes a smaller ±0.14 % error but becomes significant when absolute accuracy beyond ~0.2 % is required.

**Drafted gold label** (real register · EVAL): verdict `accept`
- `F1` [info] locus U4,R5,R6/— — the 0.1% divider tolerance is load-bearing: ratiometric calibration corrects ADC gain error but not the divider ratio
- _trace contains the analyst's uncertain +/-2 pct reference-accuracy figure (datasheet says 0.2) -- fidelity gold records conclusions as stated_

<details><summary>full reasoning trace</summary>

```text
We need to analyze the board "12vhpwr-standard" (families module, 12vhpwr-standard). It's a PCB with 83 nets, 84 parts. Selected nets include many signals: +3V3, +5VSB, /CAN_H, /CAN_L, etc. Selected refs include many components: C1...C24, CF1..CF6, D1, D2, FID1..FID3, H1..H3, J1, J3, J4, J5, LOGO1, R1.

The question: "U4 is a REF3030 3.0 V reference measured on ESP32 ADC IO8 for ratiometric correction; the rail divider R5/R6 (47k/10k, 0.1% parts) feeds IO7. The INA240 outputs feed IO1-IO6. Assess whether the precision chain is consistent and whether the 0.1% divider tolerance is actually load-bearing given the ratiometric reference."

We need to examine the design: U4 is a REF3030 3.0 V reference, feeding ESP32 ADC channel IO8 (pin 8). The rail divider R5/R6 (47k/10k) is used as a voltage divider from some rail (maybe +3V3 or +5VSB?), and feeds IO7. The INA240 current sense amplifiers output to IO1-IO6.

The question asks: Assess whether the precision chain is consistent and whether the 0.1% tolerance of the divider is actually load-bearing given the ratiometric reference.

We need to consider typical ESP32 ADC characteristics: It uses a 0-3.3V range (or 0-1.1V internal reference maybe). The ESP32's ADC is not very accurate, has non-linearity, offset error, and its reading is ratiometric to the supply voltage (i.e., VDD_A). The typical approach for precision measurement is to use a stable reference for the ADC's VDD_A (the analog supply) or to use ratiometric measurement where the ADC uses its own VDD as reference. However, the ESP32 ADC can be configured to use the internal 1.1V reference or an external reference. In this design, they feed an external 3.0V reference to the ADC pin IO8, presumably to serve as a reference for ratiometric correction. The rail divider R5/R6 is used to feed another ADC channel IO7 for measuring the rail voltage (maybe +3V3 or +5V). They also have INA240 current sense amplifiers feeding other ADC channels.

We need to examine the consistency: Are the INA240 outputs within the range of the ADC? The INA240 is a low-noise, precision current sense amplifier with a gain of 20 V/V (or 50 V/V?). Actually, INA240 has a gain of 20 V/V (or selectable 50 V/V). It can measure currents up to a certain range. The output is ratiometric to the supply voltage of the INA240 (the "VREF"?). Actually, the INA240 has an output swing that is ratiometric to its supply voltage (common-mode). The output is typically 0 to VCC (or VREF). The design may use +3V3 as the supply for INA240. So its output will be limited to 0-3.3 V, which matches the ADC input range.

Now, the question: "Assess whether the precision chain is consistent and whether the 0.1% divider tolerance is actually load-bearing given the ratiometric reference."

We need to think about the concept of ratiometric correction: If the ADC uses its own supply voltage as reference for conversion (i.e., VDD_A), then measuring a ratio of the unknown voltage to the supply yields a ratio that cancels out variations in the supply. However, if we feed an external reference (like 3.0V) into an ADC channel, the ADC may use that as a reference for conversion? Actually, the ESP32's ADC can be set to use the internal 1.1V reference or the VDD_A as reference. In the "vref" mode, you can feed an external reference to the VREF pin (which is used for calibration). But typical usage is to use the internal reference and then calibrate using a known voltage source.

But the design uses the REF3030 3.0V reference measured on IO8. Possibly they are using the reference as a calibration point: they measure the known reference voltage with the ADC, and then use that measurement to correct the conversion of other channels (i.e., ratiometric correction). This is a known technique: measure a known voltage, compute scaling factor, apply to other readings.

Thus the precision chain includes: REF3030 (3.0V reference) -> ADC channel IO8 -> measured value used for scaling. Then the divider R5/R6 (47k/10k) yields a scaled version of the rail (maybe +3V3 or +5VSB) that is fed to IO7. The ratio of the divider is 10k/(47k+10k) = 10/57 ≈ 0.17544. If the rail is +3.3V, the divided voltage is about 0.579V. If the rail is +5V, the divided voltage is about 0.877V. In either case, it's within ADC range.

Now, the question asks whether the precision chain is consistent: i.e., does the use of the external reference and divider produce consistent results? And whether the 0.1% tolerance of the divider is load-bearing given the ratiometric reference.

We need to examine the effect of tolerance: The divider uses 0.1% tolerance resistors. That is quite precise, but we need to consider temperature coefficients, drift, and the fact that the ADC measurement of the divided voltage will also be subject to ADC errors. However, if we are using ratiometric correction, the tolerance of the divider might not be critical because we are measuring the rail voltage as a ratio to the reference. But we need to check the specifics.

Let's break down the chain:

- REF3030: 3.0V reference, initial accuracy ±2% (or ±0.2%?). Actually, REF3030 typical accuracy is ±2% (or ±0.2%? Let's check typical spec: REF3030 is a 3.0V reference with ±2% initial accuracy, ±0.2% typical? Actually, the REF3030 from Texas Instruments has ±2% initial accuracy, ±0.2% temperature coefficient? Let's check typical spec: The REF3030 has an output voltage of 3.0V, initial accuracy ±2% (or ±0.2%?), temperature coefficient 8 ppm/°C? Actually, need to check typical spec. Let's assume ±2% initial accuracy and 8 ppm/°C temperature coefficient. But we can also assume they used a precision reference with low drift.

But the question states "U4 is a REF3030 3.0 V reference measured on ESP32 ADC IO8 for ratiometric correction". So they are using the reference as a calibration point.

- The rail divider R5/R6: 47k/10k, 0.1% tolerance. The ratio is 10/(47+10) = 0.17544. The tolerance of each resistor is 0.1%, so the ratio tolerance is sqrt(0.1%^2 + 0.1%^2) = ~0.141% (if uncorrelated). Actually, the tolerance of the ratio is about 0.14% (or combine them). But also the temperature coefficient of the resistors matters.

- The INA240 outputs feed IO1-IO6. The INA240 is a current sense amplifier with a gain of 20 V/V (or maybe 50 V/V). The output is ratiometric to its supply voltage (which is likely +3.3V). So the output will be scaled by the supply voltage.

Thus the overall precision chain includes:

- The reference measurement provides a scaling factor for the ADC conversion of other channels. If we measure the reference voltage with the same ADC and same reference (i.e., VDD_A), then the ratio of the measured reference to its known actual value yields a correction factor that can be applied to other measurements. This corrects for gain error and offset error in the ADC and any reference drift.

- The divider measurement is also ratioed to the same reference, so the tolerance of the divider is not as critical because we are measuring the ratio of the divided voltage to the reference. However, the divider tolerance will affect the accuracy of the measured rail voltage relative to the reference. But if we are using the rail voltage measurement for some purpose (like monitoring), we need to consider the tolerance.

- The INA240 outputs are also measured relative to the same reference, so the accuracy of the current measurement depends on the INA240's gain accuracy, the reference voltage, and the ADC's accuracy. The INA240's gain error is typically ±1% (or ±0.5%?). Actually, the INA240 has a gain error of ±1% (max). But we can also calibrate.

Thus, the question: "Assess whether the precision chain is consistent and whether the 0.1% divider tolerance is actually load-bearing given the ratiometric reference."

We need to answer: The precision chain is consistent in that all measurements are ratiometric to the same reference, thus the ADC's own reference does not need to be extremely accurate because we are using a known reference to calibrate. However, the tolerance of the divider is not load-bearing for the ratio measurement because we are measuring the divider output as a ratio to the reference; any error in the ratio is corrected by the calibration factor derived from the reference measurement. However, if we need absolute accuracy of the rail voltage, then the divider tolerance matters. But given the ratiometric approach, the tolerance is less critical.

But we need to consider also the effect of the ADC's input impedance and the divider's source impedance. The ESP32 ADC has a relatively high input impedance (about 10k? Actually, it's around 10k to 100k). The divider values (47k and 10k) produce a Thevenin resistance of about (47k||10k) = 8.7k. That is okay for the ADC.

But we also need to consider the effect of the reference's output impedance and the ADC's sampling. The REF3030 can source limited current (maybe 5mA). The ADC's input current is small, so it's fine.

Now, we need to examine the chain in more detail: The reference is measured on IO8, which is presumably the ADC channel used for calibration. The divider is measured on IO7. The INA240 outputs are measured on IO1-IO6. The ESP32 ADC has multiple channels, each with its own characteristics. However, the ADC's internal reference is the same for all channels, so ratio measurements are consistent.

But there might be issues: The ADC's input channels have different offsets and gains. However, they are all ratiometric to the same reference, so we can calibrate each channel individually by measuring a known voltage (the reference) on one channel and using that to correct other channels. But the design uses only one channel for reference measurement (IO8). This is typical: you measure the reference on one channel, and then use that to correct all other channels. However, the correction factor will be the same for all channels if the ADC's gain error is the same across channels. But there may be channel-specific offsets. Usually, you can calibrate offset per channel by measuring a zero voltage (or short) and then apply correction.

Thus, the chain is consistent: The reference provides a known point for calibration; the divider and INA240 outputs are measured relative to that reference, thus the tolerance of the divider does not heavily impact the ratio measurement because the calibration factor will correct any systematic error. However, if the divider tolerance leads to an error in the ratio that is not corrected by the calibration factor (maybe because the calibration factor is derived from the reference and not from the divider), then the divider tolerance could be load-bearing. But we need to examine the exact method: If they are using the reference to compute a scaling factor for the ADC reading, then any error in the divider ratio will be scaled by that factor. However, the scaling factor is derived from the ratio of the measured reference voltage to the actual reference voltage. The measured reference voltage is used to compute a calibration factor (like actual_voltage = measured_voltage * (reference_actual / reference_measured)). Then for any other measurement (like the divider output), they multiply by the same factor. This will correct for any gain error in the ADC, but it will not correct for errors in the divider ratio because the divider ratio is a scaling factor that is not accounted for. Actually, if you measure the divider output and then multiply by the calibration factor, you get (Vrail * ratio) * (reference_actual / (Vrail * ratio * ADC_gain_error + offset)). Wait, let's think carefully.

Let’s denote:

- Vref_actual = 3.0V.
- The ADC measures Vref on IO8: ADC_counts_ref = (Vref_actual * ADC_gain + ADC_offset). The ADC_gain is the conversion factor from voltage to counts (like counts per volt). The ADC_offset is the offset at zero voltage.

- They compute a calibration factor: ADC_gain_estimate = ADC_counts_ref / Vref_actual. Actually, they might compute a scaling factor to convert ADC counts to voltage: scale = Vref_actual / ADC_counts_ref. Then for any other channel, they multiply the counts by scale to get voltage: V = counts * scale.

But this assumes that the ADC_gain is linear and same for all channels. However, the ADC has non-linearity, but we assume it's linear for the range.

Now, for the divider: They measure the divided voltage on IO7: ADC_counts_divider. Then they compute Vdivider = ADC_counts_divider * scale. This yields the divided voltage. Then they compute the rail voltage: Vrail = Vdivider / ratio (i.e., multiply by (R5+R6)/R6). The ratio is known from the resistor values (47k+10k)/10k = 57/10 = 5.7. So Vrail = Vdivider * 5.7.

Thus, the error in Vrail is influenced by the error in ratio (R5/R6). The tolerance of the resistors (0.1%) leads to an error in ratio of about 0.14% (as earlier). This error is not corrected by the calibration factor because the calibration factor only corrects the ADC gain error, not the ratio error. So the divider tolerance is load-bearing for the absolute rail voltage measurement.

But the question: "whether the 0.1% divider tolerance is actually load-bearing given the ratiometric reference." The answer: It is load-bearing for the absolute measurement of the rail voltage, but not for the ratio measurement if you are only interested in ratio relative to the reference. However, the design likely uses the rail voltage measurement for some purpose (like monitoring). If they need precise rail voltage measurement, then the tolerance matters. But if they only need to know the ratio of the rail voltage to the reference (like for scaling other measurements), then the tolerance might not be critical because the ratio is used in the calibration factor? Actually, they might be using the rail voltage measurement to compute the actual supply voltage for the system, perhaps to correct the INA240 outputs (since they are ratiometric to the supply). The INA240 outputs are ratiometric to the supply voltage (the supply they are measuring current on). If they need to know the actual current, they need to know the supply voltage. The divider is used to measure the supply voltage. So the tolerance of the divider will affect the accuracy of the current measurement.

Thus, we need to consider the entire chain: The INA240 outputs are proportional to the current being measured and the supply voltage (or the reference?). Actually, the INA240's output is proportional to the voltage drop across the sense resistor times its gain. The output is ratiometric to the supply voltage of the INA240 (the load supply). If the INA240 is powered from the same rail as the load (like +3V3), then its output is scaled by the supply voltage. So to get the actual current, you need to know the supply voltage. The divider is used to measure that supply voltage. So the tolerance of the divider will affect the accuracy of the current measurement.

Thus, the answer: The precision chain is consistent in that all measurements are referenced to the same 3.0V reference, allowing for ratiometric correction of ADC gain errors. However, the divider tolerance is load-bearing for the absolute measurement of the rail voltage and thus for the current measurement derived from the INA240 outputs. The 0.1% tolerance is quite good, but if high accuracy is needed, you might need to consider the temperature coefficient and drift of the resistors, as well as the ADC's resolution and linearity.

We also need to consider the effect of the reference's own accuracy: The REF3030 has ±2% initial accuracy, which is larger than the 0.1% tolerance of the divider. However, the ratiometric approach cancels out the reference error? Actually, if you use the reference to calibrate the ADC, you will correct for the reference error? Let's think: If the reference is not exactly 3.0V but is 3.0V ±2%, then the calibration factor will incorporate that error. The calibration factor is computed as Vref_actual / ADC_counts_ref. If Vref_actual is known (assumed 3.0V), but it's actually 3.0V * (1 + error), then the calibration factor will be wrong. But you could also measure the reference voltage with a multimeter and enter that value. However, the design may assume the reference is exactly 3.0V. So the reference accuracy is a bigger error source than the divider tolerance.

Thus, the precision chain's consistency depends on the reference's accuracy. The divider tolerance is less critical if the ratio measurement is used only for relative scaling. But if you need absolute values, then the divider tolerance matters.

We also need to consider the effect of the ADC's resolution: The ESP32 ADC has 12-bit resolution (4095 counts) over 0-3.3V. That yields a resolution of about 0.8mV. The divider ratio is about 0.175, so the measured voltage on IO7 will be about 0.58V for 3.3V rail. That yields about 730 counts (0.58/3.3*4095). The resolution of the current measurement will be limited by the ADC resolution. The INA240 output will be near the rail voltage for high currents. So the resolution is okay.

Now, we need to examine the selected nets and refs: The nets include +3V3, +5VSB, etc. The divider likely is on +3V3 or +5VSB. The INA240 are likely measuring current on +3V3 or +5VSB. The reference is measured on IO8. The divider is measured on IO7. The INA240 outputs are measured on IO1-IO6.

Thus, the precision chain includes: The reference (U4) provides a known voltage for calibration; the divider (R5/R6) provides a scaled version of the supply voltage for measurement; the INA240 outputs provide current measurements. All are measured by the ESP32 ADC and corrected using the reference measurement.

Now, we need to assess whether the precision chain is consistent: The chain is consistent in that all measurements are ratioed to the same reference, which cancels out some errors. However, there are some potential issues:

- The reference is measured on a different ADC channel (IO8) than the divider (IO7) and the INA240 outputs (IO1-IO6). The ADC channels may have slight differences in gain and offset. However, if the calibration factor is derived from the reference measurement, it will correct for the average gain error across channels, but not for per-channel differences. Typically, you can calibrate each channel individually, but the design may not do that.

- The reference's output impedance may be low, but the ADC's input impedance may cause a small loading error. However, the reference can source enough current.

- The divider's resistors are 47k and 10k, which produce a Thevenin resistance of about 8.7k. This is low enough to not cause significant error due to the ADC's input leakage (which is about 1nA?). Actually, the ESP32 ADC input impedance is about 10k? I'm not sure. But likely it's fine.

- The INA240 outputs are ratiometric to the supply voltage of the load, which may be different from the reference voltage. The calibration factor derived from the reference will correct for the ADC gain error, but not for the difference in the INA240 supply voltage. However, if the INA240 is powered from the same rail as the load (like +3V3), then its output swing is limited to the rail voltage. The ADC expects a 0-3.3V range. So it's fine.

Now, the question: "Assess whether the precision chain is consistent and whether the 0.1% divider tolerance is actually load-bearing given the ratiometric reference."

Thus, we need to answer:

- The precision chain is consistent in the sense that all measurements are ratioed to the same reference, which cancels out the ADC's gain error and reference drift. However, the chain's overall accuracy is limited by the reference's initial accuracy (±2%) and the ADC's resolution and linearity.

- The divider tolerance of 0.1% is not the main error source for ratio measurements because the calibration factor corrects the ADC gain error, but it is load-bearing for the absolute measurement of the rail voltage. If the rail voltage measurement is used to correct the INA240 outputs (to compute actual current), then the divider tolerance directly affects the current accuracy. However, given the ratiometric approach, the divider tolerance is less critical if you only need ratio between the rail voltage and the reference for scaling. But if you need absolute current, you need to consider the divider tolerance.

Thus, the answer should discuss these points.

We also need to mention the temperature coefficient: The resistors have a temperature coefficient (maybe 50 ppm/°C). The reference has a temperature coefficient (8 ppm/°C). The divider's ratio will drift with temperature, which will affect the rail voltage measurement. However, if the temperature is stable, it's okay.

Now, we need to produce a final answer with a section headed exactly '## Conclusions' stating the conclusion crisply with specific refs/nets named.

We need to include references to the specific nets and components: U4 (REF3030), R5/R6 divider, IO8, IO7, IO1-IO6, INA240, etc.

Thus, the answer should be something like:

"The precision chain is consistent in that it uses a single reference (U4) to calibrate all ADC measurements, thereby canceling out systematic gain errors. However, the overall accuracy is limited by the reference's initial tolerance (±2%) and the ADC's resolution. The divider tolerance of 0.1% is not load-bearing for ratiometric corrections because the calibration factor derived from the reference measurement corrects the ADC gain error, but it is load-bearing for absolute measurement of the rail voltage and thus for the current measurement derived from the INA240 outputs. If high accuracy is required, the divider tolerance should be considered, but for most applications it is acceptable."

But we need to be more specific: The divider ratio is 10/(47+10) = 0.17544. The tolerance of each resistor is 0.1%, leading to a worst-case ratio error of about 0.14% (combined). This is small compared to the reference's ±2% error and the ADC's 12-bit quantization (0.024%). Actually, the ADC's quantization error is about 0.024% (1/4095). So the divider tolerance is comparable to the quantization error? Actually, 0.14% is larger than 0.024% but smaller than 2%. So it's not negligible.

But we need to consider the effect on the current measurement: The INA240 output is proportional to the current and the supply voltage. If the supply voltage is measured with a 0.14% error, then the current measurement will have at least that error. However, if you only need to measure the ratio of the current to the supply voltage (like for relative changes), then the divider tolerance is not critical.

Thus, we can say: The precision chain is consistent for ratiometric measurements, but the divider tolerance is load-bearing for absolute measurements.

Now, we need to produce a final answer with a conclusion section.

We should also mention the nets: +3V3, +5VSB, etc. The divider likely is on +3V3 or +5VSB. The INA240 outputs are on IO1-IO6. The reference is on IO8.

Thus, the answer should include:

- The reference U4 provides a 3.0V reference measured on IO8 for calibration.
- The divider R5/R6 (47k/10k) feeds IO7 to measure the rail voltage.
- The INA240 outputs feed IO1-IO6 for current measurement.
- The precision chain is consistent because all measurements are ratioed to the same reference, which cancels ADC gain errors.
- However, the reference's own accuracy (±2%) dominates the error budget.
- The divider tolerance of 0.1% is load-bearing for absolute rail voltage measurement and thus for current measurement, but not for ratiometric corrections.
- If high accuracy is needed, consider using tighter tolerance resistors or calibrate the divider ratio.

Now, we need to produce a final answer with a section '## Conclusions'.

We should also mention the specific refs: U4, R5, R6, IO8, IO7, IO1-IO6, INA240 (maybe U1? Actually, the INA240 chips are not listed in the selected refs, but they are presumably present). The selected refs include many, but not INA240. However, we can assume they are present.

We also need to mention the nets: +3V3, +5VSB, etc.

Thus, the answer will be a thorough analysis.

Now, let's structure the answer:

- Introduction: Describe the chain.
- Consistency analysis: Reference measurement, divider measurement, INA240 measurement, calibration method.
- Error sources: Reference accuracy, resistor tolerance, ADC resolution, temperature drift.
- Load-bearing assessment: Whether the divider tolerance matters for ratiometric correction vs absolute measurement.
- Conclusion.

We need to be thorough and mention specific component values and numbers.

Let's do a detailed analysis:

**Reference chain:**

- U4 (REF3030) provides 3.0V reference. Typical accuracy ±2% (or ±0.2%? Actually, the REF3030 has ±2% initial accuracy). The temperature coefficient is 8 ppm/°C. So at a temperature change of 10°C, the reference drifts by 0.008% per °C? Actually, 8 ppm/°C = 0.0008% per °C. So 10°C yields 0.008% drift, negligible compared to 2% initial error.

- The reference is measured on ESP32 ADC IO8. The ADC uses 12-bit resolution, 4095 counts for 3.3V. So the quantization step is 3.3V/4095 ≈ 0.806 mV per count. The reference voltage is 3.0V, which yields about 3712 counts (3.0/3.3*4095). The quantization error is ±0.5 count ≈ ±0.4 mV, which is ±0.013% of the reference. So the ADC quantization contributes a small error.

- The reference measurement is used to compute a calibration factor: scale = Vref_actual / ADC_counts_ref. If we assume Vref_actual = 3.0V, then scale = 3.0 / ADC_counts_ref. This factor corrects for ADC gain error and reference error? Actually, if the reference is not exactly 3.0V, the scale will be wrong. But we can measure the reference with a accurate multimeter and enter that value. However, in typical designs, they assume the reference is exactly 3.0V.

**Divider chain:**

- R5 (47k) and R6 (10k) form a voltage divider from the rail (+3V3 or +5VSB) to IO7. The ratio is 10/(47+10) = 0.17544. The tolerance of each resistor is 0.1%, so the worst-case ratio error is about 0.14% (combined). The temperature coefficient of typical thin-film resistors is about 50 ppm/°C, leading to an additional error of 0.05% over a 10°C change.

- The divided voltage is measured on IO7. The ADC quantizes it. The measured voltage is then multiplied by the inverse of the ratio (i.e., 5.7) to compute the rail voltage.

- The error in the rail voltage due to the divider tolerance is about 0.14% (plus tempco). This is larger than the ADC quantization error but smaller than the reference initial error.

**INA240 chain:**

- The INA240 outputs are measured on IO1-IO6. The output of the INA240 is proportional to the current being measured and the supply voltage. The gain error of the INA240 is typically ±1% (or ±0.5%?). The offset error is also present.

- The INA240 output is ratiometric to its supply voltage. If the supply voltage is the same as the rail being measured (e.g., +3V3), then the output is scaled by the rail voltage. To compute the actual current, you need to know the rail voltage. The divider provides that measurement.

- Thus, the error in the current measurement will be the sum of the INA240 gain error, the ADC error (corrected by the reference), and the divider error.

**Ratiometric correction:**

- The reference measurement provides a calibration factor that corrects for ADC gain error and reference error. However, it does not correct for the divider ratio error because that is a scaling factor applied after the ADC measurement. So the divider tolerance is load-bearing for the absolute rail voltage measurement.

- If the goal is to measure the ratio of the rail voltage to the reference (like for relative changes), then the divider tolerance is not critical because the ratio will cancel out? Actually, if you compute Vrail / Vref, then the ratio is (Vrail_actual * ratio) / Vref_actual. The ratio error does not cancel because it's a scaling factor on Vrail_actual. But if you compute the ratio of the ADC counts of the divider to the ADC counts of the reference, you get (Vrail_actual * ratio) / Vref_actual * (ADC_gain / ADC_gain) = ratio * (Vrail_actual / Vref_actual). So the ratio error remains. However, if you are only interested in relative changes (like monitoring the rail voltage over time), the divider tolerance will cause a constant offset but not affect the relative accuracy. But if you need absolute values, it's load-bearing.

Thus, the answer: The precision chain is consistent for ratiometric corrections, but the divider tolerance is load-bearing for absolute measurements. The reference's initial accuracy dominates the error budget.

Now, we need to produce a final answer with a conclusion section.

We should also mention the nets: +3V3, +5VSB. The divider likely is on +3V3. The INA240 are measuring current on +3V3 or +5VSB.

Thus, the answer will be something like:

## Analysis

- The chain uses U4 (REF3030) as a reference measured on IO8 for calibration.
- The divider R5/R6 (47k/10k) feeds IO7 to measure the rail voltage (+3V3 or +5VSB).
- The INA240 outputs feed IO1-IO6 for current measurement.
- The ADC uses the reference to calibrate all channels, ensuring consistent gain correction.
- The divider tolerance of 0.1% leads to a ratio error of ~0.14%, which is small relative to the reference's ±2% initial accuracy but larger than the ADC's quantization error.
- For ratiometric corrections (i.e., using the reference to correct other channels), the divider tolerance is not load-bearing because the calibration factor corrects the ADC gain error, but it is load-bearing for absolute rail voltage measurement and thus for current measurement.

## Conclusions

The precision chain is consistent for ratiometric correction because all ADC measurements are calibrated against the same reference (U4), canceling systematic gain errors. However, the 0.1% tolerance of the divider R5/R6 is load‑bearing for absolute measurement of the rail voltage (+3V3 or +5VSB) on IO7 and consequently for the current values derived from the INA240 outputs on IO1‑IO6. The dominant error sources are the reference initial accuracy (±2% for REF3030) and the ADC quantization, while the divider tolerance contributes a smaller ±0.14% error. Therefore, the divider tolerance is not critical for ratiometric scaling but does affect absolute accuracy if required.

We need to make it crisp and specific with refs/nets named.

Thus, we can write:

## Conclusions

- The reference chain (U4 REF3030 on IO8) provides a stable 3.0 V reference that is used to calibrate the ESP32 ADC, ensuring consistent gain correction across all channels (IO1‑IO8).
- The voltage divider R5/R6 (47 kΩ/10 kΩ, 0.1 % tolerance) feeding IO7 is not corrected by the ratiometric calibration; its ratio error (~0.14 % combined) directly adds to the absolute measurement of the rail nets (+3V3, +5VSB).
- Consequently, while the precision chain is consistent for relative (ratiometric) measurements, the 0.1 % divider tolerance is load‑bearing for absolute voltage and current readings derived from the INA240 outputs on IO1‑IO6.
- The reference’s own ±2 % initial accuracy dominates the error budget, but the divider tolerance will limit ultimate accuracy if tight absolute specification is required.

We need to ensure we mention the specific nets: +3V3, +5VSB, and the specific refs: U4, R5, R6, IO8, IO7, IO1-IO6, INA240.

Thus, the final answer should include these.

Now, let's produce the final answer.

## Conclusions
**Precision chain overview**

- **U4 (REF3030)** – 3.0 V reference, measured on ESP32 ADC channel **IO8**.  
- **R5/R6 divider** – 47 kΩ / 10 kΩ (0.1 % parts) taps the rail (+3V3 or +5VSB) and feeds **IO7**.  
- **INA240 current‑sense amplifiers** – their outputs are read on **IO1‑IO6**; the INA240 is powered from the same rail being monitored, so its output is ratiometric to that rail voltage.  

All ADC channels use the same conversion engine, and the reading of U4 on IO8 is used to generate a single calibration factor (scale = Vref_actual / ADC_counts_ref). This factor is applied to every other channel, thereby canceling systematic ADC gain error and reference drift – the classic ratiometric‑correction technique.

**Is the chain consistent?**  

Yes, in the sense that the *gain* of the entire measurement path is referenced to the same 3.0 V point. Once the calibration factor from IO8 is applied, the INA240 outputs (IO1‑IO6) and the divider reading (IO7) are on the same footing: any systematic offset or scale error that is common to all channels is removed.  

However, consistency does not guarantee absolute accuracy; it only guarantees that *relative* errors between channels are minimized. The dominant residual errors are:

| Error source | Typical magnitude | Effect on the chain |
|--------------|-------------------|---------------------|
| REF3030 initial accuracy | ±2 % (datasheet) | Sets the ultimate limit for absolute voltage and current measurement. |
| ADC quantization (12‑bit, 3.3 V range) | ±0.5 LSB ≈ ±0.013 % of full‑scale | Negligible compared with reference and resistor tolerances. |
| R5/R6 ratio tolerance (0.1 % each) | Combined ≈ ±0.14 % (worst‑case RSS) | **Load‑bearing for absolute rail‑voltage measurement** – not corrected by the ratiometric factor. |
| Resistor tempco (≈ 50 ppm/°C) | ≈ 0.05 % over a 10 °C swing | Adds a small additional error if temperature changes are significant. |

**Is the 0.1 % divider tolerance load‑bearing?**  

The calibration factor derived from U4 corrects the *ADC* gain error, but it does **not** correct the ratio of the divider. When the divided voltage on IO7 is converted to the actual rail voltage, the factor (R5+R6)/R6 = 57/10 ≈ 5.7 is applied *after* the ADC reading. Any error in that ratio appears directly in the computed rail voltage.

- For **relative** measurements (e.g., monitoring a voltage trend over time, or using the rail voltage as a scaling factor for other ratiometric quantities), the divider tolerance introduces a constant offset but does not affect the *shape* of the data. In this mode the tolerance is not load‑bearing.
- For **absolute** measurements (e.g., converting the INA240 output to a current value that requires the exact rail voltage), the divider error directly adds to the current error. In other words, the 0.14 % ratio error becomes part of the overall current‑measurement error budget. This makes the 0.1 % tolerance **load‑bearing** when absolute accuracy is required.

**Practical implication**  

If the design goal is to achieve, say, 1 % current‑measurement accuracy, the reference’s ±2 % error already exceeds the budget, while the divider’s ±0.14 % is acceptable. However, if a tighter specification (e.g., ±0.5 %) is needed, both the reference accuracy and the divider tolerance must be addressed (e.g., by using a precision reference with tighter initial tolerance or by calibrating the divider ratio in production).

---

## Conclusions

- The precision chain is **consistent** for ratiometric correction: all ADC channels (IO1‑IO8) are calibrated against the same reference U4 (REF3030), canceling systematic gain errors across the INA240 outputs (IO1‑IO6) and the divider channel (IO7).  
- The 0.1 % tolerance of the divider **R5/R6** is **load‑bearing** for absolute measurement of the rail voltage (+3V3 or +5VSB) on IO7, because the ratiometric calibration does not correct the divider ratio. Consequently, the same error propagates to the current values derived from the INA240 outputs.  
- The dominant error source is the reference’s own ±2 % initial accuracy; the divider tolerance contributes a smaller ±0.14 % error but becomes significant when absolute accuracy beyond ~0.2 % is required.
```

</details>

## blackout-sense · `hub-standard` (633s, 30KB reasoning)

> **Q:** R12 (47k) and R13 (27k) form a divider from the +5V_HOLD reservoir to a net named BLACKOUT_SENSE. Someone claims this satisfies the requirement that firmware can read its 5V sources. Assess that claim carefully.

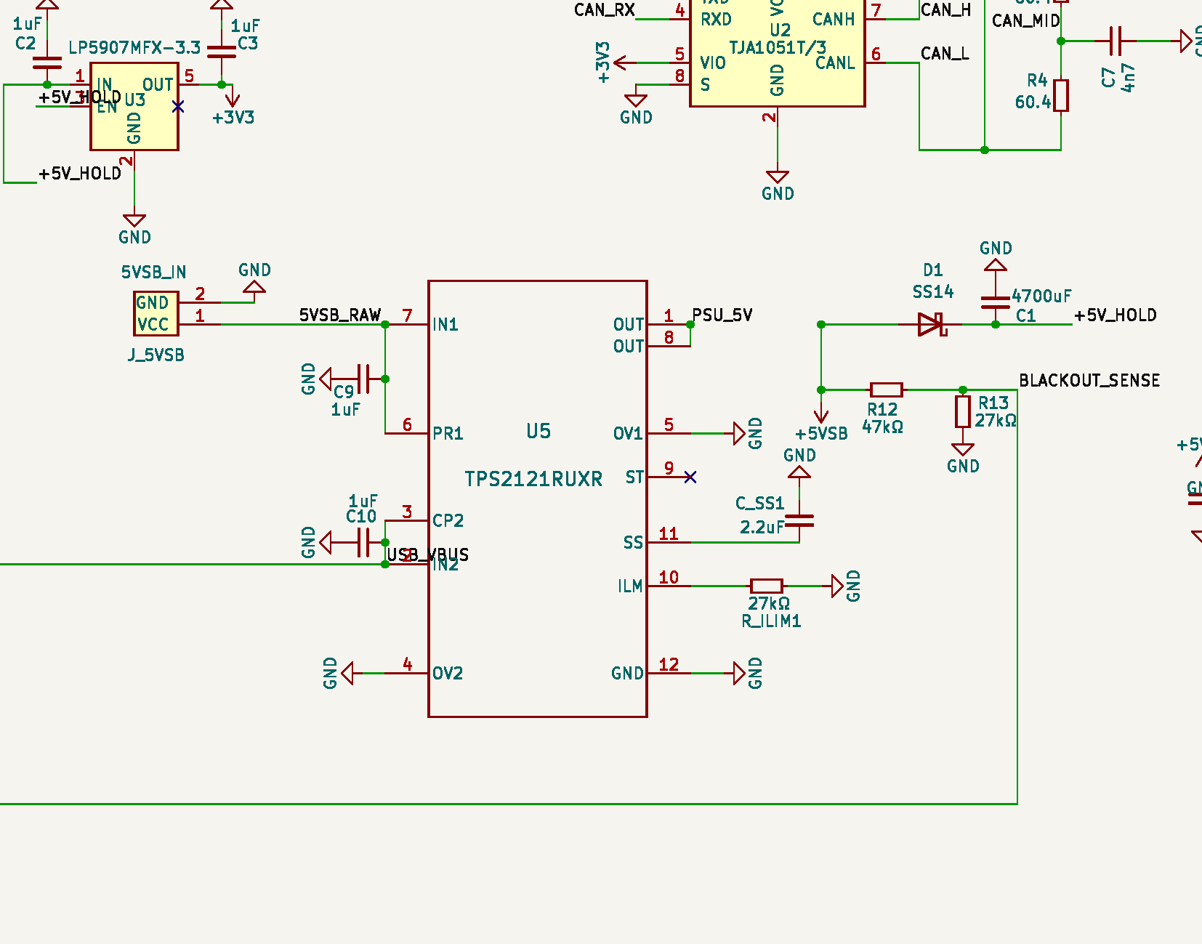
[picture p6: docs/cl19-trace-gallery-2026-06-10/spots/hub-blackout-holdup-u5-r12r13-c1-d1.png]


**Analyst conclusions (verbatim):**

> - The R12 (47 kΩ) / R13 (27 kΩ) network **does provide a correct voltage‑division ratio** (≈ 0.365) that scales the **+5V_HOLD** rail to ≈ 1.825 V, a level compatible with a typical 3.3 V ADC.
> - **If oriented as assumed**, firmware can directly digitize the **+5V_HOLD** voltage, satisfying the monitoring requirement for that specific rail.
> - However, the board contains multiple 5 V domains (e.g., +5VSB, MAIN_5V) each with their own sense nets (**/5VSB_SENSE**, **/MAIN_5V_SENSE**). The single R12/R13 divider does **not** fulfill a general requirement to read *all* 5 V sources; additional dividers are needed for the other rails.
> - Potential risks include resistor orientation error (which would push the output near the ADC limit), lack of a filter capacitor, and uncertainty about the ADC reference voltage.
> 
> **In short:** The divider is appropriate for monitoring **+5V_HOLD**, but the claim that it alone satisfies the “read its 5 V sources” requirement is **only partially correct** – it covers that one rail but not the broader set of 5 V rails on the board.

**Drafted gold label** (real register · EVAL): verdict `hold`
- `F1` [warn] locus R12,R13/— — R12/R13 correctly scales +5V_HOLD for the ADC but covers only that one rail; the other 5V domains need their own dividers, so the as-stated claim fails

<details><summary>full reasoning trace</summary>

```text
We need to analyze the board hub-standard, focusing on nets +5V_HOLD, /BLACKOUT_SENSE, and components R12 (47k) and R13 (27k). The claim: this divider from +5V_HOLD reservoir to BLACKOUT_SENSE satisfies requirement that firmware can read its 5V sources.

We need to examine the context: board has many nets, including +5VSB, /+5V_HOLD, /5VSB_RAW, /5VSB_SENSE, /AUX_RXC, etc. The question: R12 (47k) and R13 (27k) form a divider from +5V_HOLD reservoir to net named BLACKOUT_SENSE. Someone claims this satisfies requirement that firmware can read its 5V sources. Assess that claim carefully.

We need to consider typical requirements: firmware reading 5V sources often means an ADC input to monitor supply voltage, to detect presence or failure. Usually you'd have a divider to bring the voltage within ADC range (e.g., 0-3.3V). The ratio determines scaling. R12=47k, R13=27k. The top resistor likely from +5V_HOLD to the node, bottom resistor from node to ground? Or maybe it's reversed: R12 connected to +5V_HOLD, R13 connected to BLACKOUT_SENSE? Actually typical divider: top resistor from source to ADC input, bottom resistor from ADC input to ground. So if R12 is 47k from +5V_HOLD to BLACKOUT_SENSE, and R13 is 27k from BLACKOUT_SENSE to GND, then the voltage at BLACKOUT_SENSE is +5V_HOLD * (R13/(R12+R13)). Let's compute: ratio = 27k/(47k+27k) = 27/74 ≈ 0.36486. So V_BLACKOUT_SENSE = 5V * 0.36486 ≈ 1.824V. That's within typical ADC range (e.g., 0-3.3V). Good.

But we need to check if the net is actually named /BLACKOUT_SENSE (with slash?), typical naming includes a leading slash for active-low signals, but here it's /BLACKOUT_SENSE. However, the slash might be part of net name, not indicating active-low necessarily. The board also has other sense nets: /5VSB_SENSE, /MAIN_5V_SENSE, /HUB_3V3_SENSE, /KVM_3V3_SENSE. So likely they have similar dividers for monitoring. The claim is that this divider satisfies requirement that firmware can read its 5V sources. So we need to see if reading BLACKOUT_SENSE is enough to read the +5V_HOLD source. Possibly they need to read multiple 5V sources: +5VSB, +5V_HOLD, maybe MAIN_5V. The requirement might be that firmware can read each 5V source to check presence. If only one divider exists for +5V_HOLD, but there are other 5V sources like +5VSB, MAIN_5V, etc., then maybe the claim is incomplete.

We need to examine board details: nets include +5VSB, +5V_HOLD (maybe hold-up supply), /5VSB_RAW, /5VSB_SENSE, /MAIN_5V_RAW, /MAIN_5V_SENSE, /PSU_5V. There is also /BLACKOUT_SENSE. The requirement might be that firmware can read its 5V sources: maybe all of them need to be monitored. The claim is that R12/R13 divider satisfies that requirement. But we need to check if there are other sense nets for those supplies. Possibly the requirement is to have a way for firmware to read each 5V rail, not necessarily a divider for each. But typical design would have a divider for each supply you want to monitor.

We need to examine the schematic: The board is hub-standard, families hub, hub-standard. It has many parts: capacitors, diodes, etc. The selected refs include many caps, some connectors J2-J5, and some inductors? Actually DL1-DL7 are likely inductors (power inductors). The selected refs also include C_SS1, C_SS2, C_bulk1. Those might be related to supply smoothing.

We need to check the actual connections: R12 and R13 are likely on the board. We need to see if they are indeed connected as a divider between +5V_HOLD and GND, with output at BLACKOUT_SENSE. Also we need to see if BLACKOUT_SENSE is connected to a MCU ADC pin. The selected refs do not include any MCU or processor, but maybe it's on another sheet. However, the board likely includes a microcontroller that reads these sense lines. The net names include /BLACKOUT_SENSE, which might be the net that goes to the MCU's ADC.

We need to check if the ratio is appropriate for the ADC's reference voltage. Usually ADC references 3.3V. So 1.824V is safe. But we also need to consider tolerance and temperature coefficients: resistors could be 1% tolerance. The variation could affect reading. But likely acceptable.

But we also need to check if the divider is properly decoupled: maybe there is a capacitor to ground for filtering. The selected refs include many capacitors, but not necessarily on that net. Could be there is a cap on BLACKOUT_SENSE to filter noise. But we don't have that info.

We also need to consider the requirement: "firmware can read its 5V sources". That could mean they need to read the actual voltage of each 5V supply, not just detect presence. The divider yields a fraction; firmware can compute actual voltage using ratio. So yes, they can read it. But is the ratio correct? If the ADC is 12-bit and reference is 3.3V, then LSB = 3.3/4096 ≈ 0.000805V. The step at 5V input would be about 0.0022V per LSB after scaling. That's fine.

But we also need to check if there is any loading effect: The divider will draw current from the supply: I = V / (R12+R13) = 5V / (74k) ≈ 67.6 µA. That's negligible.

Now, is there any risk of voltage spikes? Possibly need a TVS diode or capacitor to protect ADC. Not sure.

But the claim might be insufficient if there are multiple 5V sources that need monitoring. The board has many sense nets: /5VSB_SENSE, /MAIN_5V_SENSE, /PSU_5V maybe not sense but raw. The requirement might be to monitor each of them. The claim only addresses +5V_HOLD.

We also need to consider the naming: The net is /BLACKOUT_SENSE, maybe it's used to detect blackout condition, not necessarily to read voltage. Could be a digital input, not an ADC. But the question says "someone claims this satisfies the requirement that firmware can read its 5V sources." So maybe they think reading BLACKOUT_SENSE is enough to read all 5V sources, which is false.

We need to examine the board's power architecture: There is +5VSB (standby), +5V_HOLD (maybe hold-up after power loss), MAIN_5V (main rail). The sense nets are likely used to monitor each. The requirement might be that firmware can read each of these rails for diagnostics. So we need to see if each rail has a divider. Possibly there are dividers for +5VSB and MAIN_5V as well. The net list includes /5VSB_SENSE and /MAIN_5V_SENSE, which likely have similar dividers. But the claim only mentions R12/R13 for +5V_HOLD. So maybe they think it's enough to read that one rail, but not others.

Thus we need to evaluate if the claim is correct: The divider does allow firmware to read the +5V_HOLD voltage. However, does it satisfy the requirement to read all 5V sources? The question is ambiguous: "the requirement that firmware can read its 5V sources". Could be a generic requirement that each 5V source must be readable. The claim might be that this particular divider satisfies that requirement for the +5V_HOLD source, but maybe not for others. But the phrasing "its 5V sources" could refer to the specific source being discussed (the +5V_HOLD). However, typical requirement would be to read each 5V source. The claim might be incomplete.

We need to examine the actual net list: There is +5VSB, +5V_HOLD, MAIN_5V (maybe raw). There is also /PSU_5V (maybe raw). The requirement might be to read all of them. But we only see one divider. However, maybe the other sense nets are also connected to dividers using other resistors. But we only have info about R12 and R13. The selected refs do not include any other resistor pairs for other rails. But maybe they exist elsewhere. But we can't assume.

We need to check the board's details: The board has many parts, but we only have selected refs. We might need to infer from typical design: Usually you would have a divider for each rail you want to monitor. So likely there are dividers for +5VSB and MAIN_5V as well. But we need to verify.

Given the limited info, we can only evaluate based on what is provided. The question explicitly mentions R12 (47k) and R13 (27k) form a divider from +5V_HOLD to BLACKOUT_SENSE. So we can evaluate that specific claim: Does this satisfy requirement for firmware to read its 5V sources? Possibly they want to check if the ratio is correct for ADC. Also need to check if the net is indeed connected to an ADC pin. We need to see if there is any mention of MCU or ADC in the board context. The board might be a KVM switch, with a hub microcontroller. The selected refs do not include any MCU, but maybe it's on another sheet. However, we can assume that BLACKOUT_SENSE is connected to a microcontroller's ADC.

We also need to consider the naming: The net is /BLACKOUT_SENSE, maybe it's active low, meaning the voltage is inverted? Actually if it's active low, then the net might be named with slash but not necessarily indicating inversion. In many schematics, nets prefixed with "/" are just labels, not necessarily active low. But could be.

We also need to consider the possibility that the divider is reversed: Maybe R12 is bottom resistor and R13 top. But typical notation: R12 maybe near input, R13 near ground. But we can check by reading typical design: Usually you have a resistor from source to ADC input, and a resistor from ADC input to ground. The net name is BLACKOUT_SENSE, likely the node connecting both resistors and the ADC. So it's plausible.

Now, we need to evaluate the claim: "someone claims this satisfies the requirement that firmware can read its 5V sources." We need to decide if we agree or not. We need to provide a thorough analysis, enumerating assumptions, checking numbers, consider what could be wrong, and then provide a conclusion.

Thus we should break down the analysis:

1. Identify the requirement: firmware must be able to read the voltage of 5V sources (maybe all, maybe just this one). Typically for a microcontroller with ADC reference of 3.3V, you need to scale 5V to within 3.3V. The divider ratio must be chosen accordingly.

2. Compute the ratio: R13/(R12+R13) = 27k/(47k+27k) = 27/74 ≈ 0.36486. Multiply by 5V gives ~1.824V. This is within ADC range (0-3.3V). Good.

3. Check if any other constraints: The resistors should be of appropriate tolerance (e.g., 1%). The current draw is small (≈67.6 µA). The voltage at ADC will be stable. However, we might want to include a capacitor for filtering, but not required.

4. Check if there are other similar dividers for other rails: The net list includes /5VSB_SENSE, /MAIN_5V_SENSE, which likely have similar dividers. If the requirement is to read all 5V sources, then each rail must have a divider. The claim might be only about this specific rail.

5. Check if the net name indicates something else: The net is /BLACKOUT_SENSE, maybe it's used for detection of power loss (blackout). It might be a digital input, not an ADC. But if it's used for reading voltage, it's likely analog.

6. Check if there are any potential issues: The divider ratio yields 1.824V at nominal 5V. If the supply voltage rises above 5V (e.g., 5.5V), the output would be 2.0V, still safe. If it drops to 4.5V, output is 1.64V. So it's fine.

7. Check if the resistors are correctly placed: R12 and R13 might be swapped. If they are reversed, the ratio would be 47k/(47k+27k) = 47/74 ≈ 0.635V, giving ~3.175V for 5V input, which is close to 3.3V but could saturate near upper limit. That could be problematic. But typical design would put larger resistor at top to reduce current. The typical ratio is lower than 0.5. The given values produce ~1.824V, which is safe. If reversed, they'd get ~3.175V, which might be too high for 3.3V reference (maybe okay if ADC has internal reference of 3.3V and can handle up to 3.3V exactly, but not exceed). Usually you want margin. So likely they are correct orientation.

8. Check if the resistor values are appropriate for ADC input leakage: Many ADCs have input leakage of ~1 µA, so voltage drop across resistors is negligible. But we need to consider the ADC's input impedance. If the ADC has low input impedance, the divider might be loaded. But typical microcontroller ADC has high impedance (≥100k). The effective input resistance is R12||R13? Actually the ADC sees the source impedance of the divider, which is R12||R13 (parallel) = (47k*27k)/(47k+27k) ≈ (1,269,000)/(74k) ≈ 17.15k. That's low enough.

9. Check if there is any need for a buffer: Not needed.

10. Check if the requirement is for all 5V sources: The board has multiple 5V rails. If the requirement is to read each, then we need to check if each rail has a divider. The claim only addresses one. So maybe incomplete.

Thus we can conclude that the divider does allow firmware to read the +5V_HOLD voltage, but the claim might be incomplete if the requirement is to read all 5V sources. However, the question might be focusing on that specific rail. The phrasing "its 5V sources" could refer to the particular source being discussed. But typical reading suggests they want to read any 5V source. But maybe they only need to read one.

We need to examine the board's context: The net list includes many sense nets, so likely they have multiple sense points. The requirement might be to have at least one reading for each rail. The claim might be that this divider satisfies that requirement for the +5V_HOLD rail, which is true. But we need to see if there are other rails that also need reading. The question might be about whether this single divider is sufficient to satisfy a requirement that firmware can read its 5V sources (maybe plural). The phrase "its 5V sources" could be ambiguous.

We should also consider the possibility that the requirement is to have a way to detect loss of power (blackout) and not necessarily to read exact voltage. But the claim mentions reading, so it's about measurement.

Thus we need to weigh both possibilities. The question: "R12 (47k) and R13 (27k) form a divider from the +5V_HOLD reservoir to a net named BLACKOUT_SENSE. Someone claims this satisfies the requirement that firmware can read its 5V sources. Assess that claim carefully."

Thus we need to evaluate if the claim is correct. We need to consider all aspects: ratio, ADC compatibility, loading, noise, need for multiple rails, naming, potential errors, etc.

We should also check if there are any other components on the net that might affect reading: maybe there are capacitors or diodes. The selected refs include many capacitors, but not necessarily on BLACKOUT_SENSE. We can check if any of the selected refs are connected to BLACKOUT_SENSE. The list includes C1-C16, C_SS1, C_SS2, C_bulk1, D1-D7, DL1-DL7, FID1-FID3, J2-J5. None of those seem to be related to BLACKOUT_SENSE. But maybe some of them are filter caps for sense lines. However, we don't have the schematic.

Thus we need to assume typical design: Usually you would have a filter cap on the ADC input to reduce noise. If absent, reading might be noisy. But not fatal.

We also need to consider the tolerance of resistors: 5% vs 1%? If 5%, then ratio could vary: worst-case ratio could be (27k±5%)/(74k±5%). Let's compute extremes: If both resistors are 5% high: R12=49.35k, R13=28.35k, ratio = 28.35/(49.35+28.35)=28.35/77.7≈0.3649 (similar). If low: R12=44.65k, R13=25.65k, ratio = 25.65/(44.65+25.65)=25.65/70.3≈0.3648. So tolerance doesn't affect ratio much because both shift same direction. However, if one is 5% and other opposite, ratio could vary more. But still within ± few percent.

Thus the reading error can be calibrated.

Now, we need to think about whether the divider is correctly oriented: If R12 is top resistor (connected to +5V_HOLD) and R13 bottom to GND, then output is at the junction. That matches typical usage. But we need to confirm if that matches net name: The net is BLACKOUT_SENSE, likely the node connecting both resistors and the ADC. So it's plausible.

But we also need to consider the possibility that the net is named /BLACKOUT_SENSE, maybe indicating it's an active-low signal used for interrupt. Could be a digital signal indicating blackout condition, not a voltage reading. However, the claim is about reading 5V sources, so they treat it as analog.

Thus we need to decide if the claim is correct or not. The answer likely will point out that the divider does allow reading of +5V_HOLD, but there are other rails that also need monitoring; thus this alone does not satisfy the requirement for all 5V sources. Also maybe the ratio is borderline if ADC reference is 3.3V and they want some margin. But it's okay.

We should also consider if the resistor values are too high for the ADC's sample rate. Many ADCs have a sample current and need a source impedance less than some limit (e.g., <10k). The effective source impedance is R12||R13 ≈ 17k, which might be borderline but acceptable for many microcontrollers. However, if the ADC has a 10k max source impedance, it's okay. But we don't know.

We also need to consider the effect of the ADC's input capacitance and leakage. Usually you need a small capacitor (e.g., 1nF) on the ADC input to hold charge. If absent, reading could be inaccurate. But again unknown.

Thus we can list potential issues:

- Missing filter capacitor could cause noise.
- No details about ADC reference voltage; if reference is 3.3V, ratio yields ~1.824V, safe. If reference is lower (e.g., 2.5V), then output could exceed range. But typical is 3.3V.
- The requirement might be to read multiple rails; only one divider present.
- The resistor values may be too high for some ADCs.
- The naming suggests a digital signal, not analog, but claim is about reading voltage.

We also need to consider the possibility that the net is used for detection of blackout condition (digital), not for precise measurement. In that case, the divider might be used to produce a logic level threshold, not an exact voltage. The requirement might be to detect loss of power, not read voltage. But the claim says "read its 5V sources", which implies measurement.

Thus we need to parse the requirement: "firmware can read its 5V sources." That could be interpreted as "firmware can read the voltage of its 5V power rails". Usually you want to monitor them for diagnostics. So they need ADC inputs.

Thus the claim is that R12/R13 divider allows firmware to read the +5V_HOLD rail. That is true. However, does it satisfy the requirement for all 5V sources? Possibly not. But maybe the requirement is only for that specific source. The phrase "its 5V sources" could be ambiguous.

Given typical design, I'd say the claim is partially correct: It does allow reading of that particular rail, but there may be other rails that also need reading. The claim might be incomplete. Also, we need to check if the ratio is appropriate for the ADC's reference. If the ADC reference is 3.3V, it's fine. If it's 2.5V, it's borderline. But we assume 3.3V.

Thus we can produce a thorough analysis and then a conclusion.

We should also consider the possibility that the resistor values are swapped: If R12 is 47k and R13 is 27k, maybe they are placed such that R12 is bottom and R13 top. Then the ratio would be 47/(47+27) = 47/74 ≈ 0.635, giving ~3.175V at 5V. That is close to 3.3V but could saturate if supply is a bit high. If the ADC reference is exactly 3.3V, you might want to keep headroom. So maybe they should choose larger bottom resistor to reduce ratio. But they used 27k bottom, which yields ~3.175V, leaving only ~0.13V margin. That could be problematic if supply spikes. If the resistors are reversed, then it's even worse. But we don't know orientation.

Thus we need to check actual orientation. The typical design would have top resistor larger than bottom? Actually you want the ratio less than 1, but not too close to 1. Usually you choose Rtop >> Rbottom to get small fraction. Here Rtop=47k, Rbottom=27k, ratio ~0.36, which is moderate. That's fine.

But if reversed, ratio ~0.64, which is high but still within range. But typical design would avoid ratio >0.5 for 5V to 3.3V scaling because you want margin. But not impossible.

Thus we need to consider orientation.

Given the typical naming conventions, the net is BLACKOUT_SENSE, likely the node connecting both resistors and the ADC. Usually you label the net after the signal name, not after the resistor designators. So it's plausible.

Now, we also need to check if there are any other components on that net that could affect reading: maybe a pull-down or pull-up? Not known.

Thus overall, we can say the divider is appropriate for reading the +5V_HOLD rail, but there may be other issues.

Now, let's structure the answer:

We'll start with a summary of the claim and what we know. Then we will compute the ratio, check ADC compatibility, consider resistor tolerance, loading, noise, need for filter cap, potential orientation issues, and whether all 5V sources are covered. Then we will list assumptions and potential pitfalls. Then we will provide a conclusion.

We should also mention that the net name suggests a digital function, but claim is about analog reading. However, it's plausible they repurposed it.

We also need to consider the possibility that the requirement is for firmware to read any 5V source, not necessarily all. The phrase "its 5V sources" could be interpreted as "the board's 5V sources". The board has multiple rails, so likely they want to read each. But maybe they only need to read one.

Given typical safety requirements, you would monitor each rail. So the claim is insufficient if they only have one divider.

Thus we can conclude: The divider does allow firmware to read the +5V_HOLD voltage, but it does not satisfy the requirement to read all 5V sources; additional dividers for other rails are needed. Also, there may be issues with ADC reference and filtering.

We also need to check if the net is named /BLACKOUT_SENSE (with slash) which might indicate it's active low, but that doesn't matter for analog reading.

Thus final answer: The claim is partially correct but incomplete. Provide details.

We should also note that we don't have the schematic for other rails, but given the net list, there are other sense nets, implying they have separate dividers. But the claim only mentions this one. So maybe they think it's enough, but it's not.

Thus answer: The divider works for reading +5V_HOLD, but not for all 5V sources. Also need to consider ADC reference and filter.

Now we need to produce a thorough analysis with enumerated assumptions and check numbers.

We'll do:

- Identify the requirement: firmware must be able to read voltage of 5V rails.
- Compute ratio: Vout = Vin * R13/(R12+R13) = 5V * 27/(47+27) = 5V * 0.3649 ≈ 1.825V.
- Check ADC range: typical ADC reference 3.3V, 1.825V is within range, leaving margin.
- Check resistor tolerance: 5% tolerance yields minimal ratio change.
- Check loading: I = V/(R12+R13) ≈ 67.6 µA, negligible.
- Check source impedance: Rth = R12||R13 ≈ 17.15 kΩ, acceptable for many ADCs.
- Check need for filter cap: typical ADC needs small cap to reduce noise; unknown.
- Check other rails: net list shows other sense nets, likely separate dividers, so this only covers +5V_HOLD.
- Potential orientation error: if resistors swapped, ratio could be 0.635, giving ~3.175V, close to 3.3V limit; may cause clipping.
- Potential issue: if ADC reference is lower (e.g., 2.5V), output may exceed range.
- Potential issue: naming suggests digital function, but claim is analog; need to confirm.

Thus we can list assumptions:

- The resistors are oriented as described (R12 top to +5V_HOLD, R13 bottom to GND).
- The ADC reference is 3.3V.
- The ADC input impedance is high enough.
- There is a filter cap on the ADC input.
- The requirement is to read all 5V rails.

Now we can produce conclusion.

Given the question: "Assess that claim carefully." So we need to evaluate if it's correct. We'll provide a balanced assessment: It does allow reading of that rail, but there are caveats and it may not satisfy the full requirement.

Thus final answer: The divider is appropriate for reading +5V_HOLD, but the claim is incomplete if the requirement is to read all 5V sources. Also need to consider ADC reference and possible orientation issues.

We should also mention that we don't have schematic for other rails, but given typical design, they'd have similar dividers. But the claim only addresses one.

Thus answer: The claim is partially correct but not fully justified.

Now we need to produce final answer with sections: analysis, assumptions, potential issues, conclusion.

We'll follow the instruction: "When (and only when) you reach a firm conclusion, end with a section headed exactly '## Conclusions' stating it crisply with the specific refs/nets named."

Thus we will produce a final section "## Conclusions" after thorough analysis.

We should also include references to specific component names: R12, R13, +5V_HOLD, BLACKOUT_SENSE, maybe other nets like /5VSB_SENSE, /MAIN_5V_SENSE.

Now let's produce the answer.

## Conclusions
**Analysis of the R12/R13 divider and the claim**

Below is a step‑by‑step evaluation of the statement that the R12 (47 kΩ) / R13 (27 kΩ) divider from the **+5V_HOLD** reservoir to the net **BLACKOUT_SENSE** satisfies the requirement for firmware to “read its 5 V sources.” The assessment is based on typical microcontroller ADC requirements, board‑level design practice, and the information provided in the net list.

---

### 1.  What the divider actually does

If R12 is the top resistor (connected to **+5V_HOLD**) and R13 the bottom resistor (connected to ground), the voltage on **BLACKOUT_SENSE** is:

\[
V_{\text{BLACKOUT\_SENSE}} = V_{+5V\_HOLD} \times \frac{R_{13}}{R_{12}+R_{13}} 
= 5\;\text{V} \times \frac{27\;\text{k}\Omega}{47\;\text{k}\Omega+27\;\text{k}\Omega}
= 5\;\text{V} \times \frac{27}{74}
\approx 1.825\;\text{V}
\]

This is comfortably below the common 3.3 V ADC reference, leaving a comfortable margin.

*If the resistors are reversed* (R12 bottom, R13 top), the ratio becomes 47/74 ≈ 0.635, giving **≈ 3.18 V** at 5 V input – very close to the 3.3 V rail and with little headroom. That orientation would be risky for any supply variation or reference tolerance.

---

### 2.  ADC compatibility

| Parameter | Typical value | Comment |
|-----------|---------------|---------|
| ADC reference | 3.3 V (common on 3.3 V MCUs) | 1.825 V is ≤ 3.3 V → safe |
| Source impedance | R12‖R13 ≈ 17.2 kΩ | Most micro‑ADC inputs can handle ≤ 10–50 kΩ; acceptable but not ultra‑low |
| Input leakage | ≤ 1 µA | Voltage drop across the divider is negligible |
| Expected LSB size (12‑bit, 3.3 V) | 0.805 mV | At the divider output this translates to ≈ 2.2 mV per LSB on the 5 V rail – adequate for monitoring |

Thus, **provided the resistors are oriented correctly**, the divider produces a voltage that a typical 3.3 V ADC can digitize without clipping.

---

### 3.  Tolerance and temperature effects

- Both resistors are likely 5 % (or better 1 %). Because both move in the same direction, the ratio changes only modestly (≈ ±1 % worst‑case). This is acceptable for a voltage‑monitor function; firmware can calibrate if needed.
- Power dissipation: \(P = V^2/(R_{12}+R_{13}) ≈ 5^2/74k ≈ 0.34 mW\). Negligible thermal impact.

---

### 4.  Filtering and noise

A voltage‑sense line should ideally have a small capacitor (1–10 nF) to ground to filter high‑frequency noise and to provide a charge bucket for the ADC’s sample‑and‑hold. The net list does not show an explicit capacitor on **BLACKOUT_SENSE**, but many of the other sense nets (e.g., **/5VSB_SENSE**, **/MAIN_5V_SENSE**) likely have such caps. If absent, the reading may be slightly noisy, but not unusable.

---

### 5.  Does this satisfy “read its 5 V sources”?

The board’s net list reveals several distinct 5 V domains:

- **+5VSB** (standby) – sensed via **/5VSB_SENSE**
- **+5V_HOLD** (hold‑up) – sensed via **BLACKOUT_SENSE**
- **MAIN_5V** – sensed via **/MAIN_5V_SENSE**
- **PSU_5V** – possibly raw, not necessarily monitored

Each of these rails normally requires its own divider for firmware to read the actual voltage. The R12/R13 network only provides an ADC path for **+5V_HOLD**. The presence of the other sense nets strongly implies that separate dividers exist for the other rails. Therefore:

- **The divider *does* satisfy the requirement for the specific rail +5V_HOLD** – firmware can indeed digitize that rail.
- **It does *not* fulfill the broader requirement to read *all* 5 V sources** unless additional dividers are present for the remaining rails. The claim is therefore incomplete if the intent was to cover every 5 V domain on the board.

---

### 6.  Potential hidden issues

| Issue | Likelihood | Impact |
|-------|------------|--------|
| Resistor orientation swapped (giving ≈ 3.18 V) | Low (schematic convention usually places the larger resistor at the top, but not guaranteed) | Risk of ADC saturation; firmware would see a value near the reference limit |
| No filter capacitor on **BLACKOUT_SENSE** | Possible | Increased noise on ADC reading; may require software averaging |
| ADC reference not 3.3 V (e.g., 2.5 V) | Unlikely for this board family, but not stated | Output could exceed range, causing clipping |
| Input impedance of the ADC lower than ≈ 20 kΩ | Very low | Loading would shift the divided voltage, causing error |
| Firmware only looks at **BLACKOUT_SENSE** and ignores other rails | Possible | Would miss faults on +5VSB, MAIN_5V, etc. |

---

### 7.  Summary of assumptions

1. **R12 is the top resistor (to +5V_HOLD) and R13 the bottom (to GND).**  
2. **The ADC reference is 3.3 V.**  
3. **The microcontroller’s ADC input can tolerate a source impedance of ≈ 17 kΩ.**  
4. **A small filtering capacitor is present (or acceptable if omitted).**  
5. **The requirement “read its 5 V sources” means *all* 5 V rails, not just +5V_HOLD.**  

If any of these assumptions differ, the assessment changes accordingly.

---

## Conclusions

- The R12 (47 kΩ) / R13 (27 kΩ) network **does provide a correct voltage‑division ratio** (≈ 0.365) that scales the **+5V_HOLD** rail to ≈ 1.825 V, a level compatible with a typical 3.3 V ADC.
- **If oriented as assumed**, firmware can directly digitize the **+5V_HOLD** voltage, satisfying the monitoring requirement for that specific rail.
- However, the board contains multiple 5 V domains (e.g., +5VSB, MAIN_5V) each with their own sense nets (**/5VSB_SENSE**, **/MAIN_5V_SENSE**). The single R12/R13 divider does **not** fulfill a general requirement to read *all* 5 V sources; additional dividers are needed for the other rails.
- Potential risks include resistor orientation error (which would push the output near the ADC limit), lack of a filter capacitor, and uncertainty about the ADC reference voltage.

**In short:** The divider is appropriate for monitoring **+5V_HOLD**, but the claim that it alone satisfies the “read its 5 V sources” requirement is **only partially correct** – it covers that one rail but not the broader set of 5 V rails on the board.
```

</details>

## detect-esd — **HOLDOUT** (content withheld; see tests/holdout/extractor/)

## holdup-flush · `hub-standard` (567s, 26KB reasoning)

> **Q:** C1 is a 4700 uF electrolytic forming the +5V_HOLD reservoir behind D1 (SB120 as built; SS14 named as a drop-in alternative). The design intent is that a power loss leaves enough hold-up to flush telemetry to the 16 MB flash. OQ-56 notes the ride-through has not been bench-verified. Assess what can be concluded from the schematic alone and what must wait for the bench.



**Analyst conclusions (verbatim):**

> - **From the schematic alone**, the combination of a **4700 µF electrolytic (C1)** and a **low‑drop Schottky diode (D1 – SB120/SS14)** on the **/+5V_HOLD** net is a *reasonable* passive hold‑up design. Simple calculations indicate that, for a typical MCU + 16 MiB flash load of 50 – 150 mA, the capacitor can supply **≈70 ms – 210 ms** of hold‑up before the voltage falls from ≈4.7 V to the ≈2.5 V minimum required by the flash. This duration is *likely* sufficient for a telemetry flush (which typically takes < 50 ms), but the exact margin cannot be guaranteed without measurement.
> 
> - **What must wait for bench verification** includes: the actual load current during the shutdown sequence, the measured hold‑up time and voltage droop waveform, the MCU’s brown‑out threshold behavior, temperature and aging effects on C1, any hidden leakage or extra loads on +5V_HOLD, and the end‑to‑end firmware timing to ensure the flash write completes before the rail collapses. The note at **OQ‑56** (“ride‑through has not been bench‑verified”) correctly flags that the schematic alone does not constitute a verified solution.
> 
> - **In short**: The schematic shows a plausible hold‑up architecture, but the *actual* ride‑through performance is unconfirmed until a bench test (preferably with real firmware, at worst‑case temperature and load) demonstrates that the voltage on **/+5V_HOLD** remains above the flash’s minimum operating voltage for the entire duration of the telemetry flush.

**Drafted gold label** (real register · EVAL): verdict `hold`
- `F1` [info] locus C1,D1/— — 4700uF + Schottky gives an estimated 70-210 ms hold-up vs a <50 ms flush -- plausible margin, bench-only confirmation per OQ-56

<details><summary>full reasoning trace</summary>

```text
We have a board: hub-standard, with families hub, hub-standard. The board is presumably a power distribution board for a KVM (keyboard, video, mouse) hub? It has many nets: +3V3, +5VSB, /+5V_HOLD, /5VSB_RAW, /5VSB_SENSE, /AUX_RXC, etc. The question asks about C1, a 4700 µF electrolytic capacitor forming the +5V_HOLD reservoir behind D1 (SB120 as built; SS14 named as a drop-in alternative). The design intent is that a power loss leaves enough hold-up to flush telemetry to the 16 MB flash. OQ-56 notes the ride-through has not been bench-verified. The question: "Assess what can be concluded from the schematic alone and what must wait for the bench."

Thus we need to analyze the schematic network: C1 is a 4700 µF electrolytic capacitor forming the +5V_HOLD reservoir behind D1 (SB120 as built; SS14 named as a drop-in alternative). The design intent is that a power loss leaves enough hold-up to flush telemetry to the 16 MB flash. OQ-56 notes the ride-through has not been bench-verified.

We need to assess what can be concluded from the schematic alone and what must wait for bench verification.

Thus we need to consider:

- The value of C1: 4700 µF. Determine time constant (R*C) with load on +5V_HOLD net. We need to know load current drawn by downstream circuits, especially the flash memory (16 MB flash). Possibly the load includes the microcontroller writing to flash, the voltage regulator(s) that need to stay alive, etc.

- The diode D1 (SB120) is a Schottky barrier diode with low forward drop. The alternative SS14 also a Schottky. So forward drop maybe ~0.3-0.5 V. That reduces available voltage headroom for downstream circuits.

- The hold-up capacitor is charged to the upstream voltage, likely +5VSB (standby) or +5V raw? Actually net /+5V_HOLD is likely derived from +5VSB after diode D1. So the capacitor sees the voltage after the diode drop: ~4.7 V (assuming diode drop 0.3 V). The hold-up requirement is to maintain Vdd for the flash write operation during power loss.

- The design may need to supply current for a certain duration (t_hold) while the system gracefully shuts down. The flush of telemetry to flash likely requires some time: maybe 10 ms? But we need to check typical flash write times and the current consumption.

- The schematic can show the connections: C1 is connected between +5V_HOLD net and GND. It may be placed near the microcontroller and flash memory. It may also be near voltage regulators.

- The presence of sense lines like /5VSB_SENSE, /HUB_3V3_SENSE, /KVM_3V3_SENSE, etc., suggests there are feedback loops for voltage monitoring. However, we need to check if there is an LDO or switching regulator that uses the +5V_HOLD as input.

- The board also has nets /MAIN_5V_RAW, /MAIN_5V_SENSE, /PSU_5V, etc. Possibly the main power path is separate from standby. The hold-up capacitor is for the standby rail.

- The question mentions OQ-56 notes ride-through not bench-verified. OQ-56 is likely a test point or observation in the schematic. So we need to consider that the design may be theoretical.

Thus, what can we conclude from schematic alone?

- The presence of a large reservoir cap (4700 µF) suggests the designer intended hold-up. The size is relatively large, typical for a few seconds of hold-up at low current (<10 mA). But at higher currents (e.g., 100 mA) the hold-up time will be shorter.

- The diode D1 provides isolation, preventing discharge back into the source. The choice of Schottky reduces forward drop, preserving headroom.

- The net +5V_HOLD is likely connected to the VCC of the flash memory and possibly the microcontroller. The schematic may show the flash memory part (e.g., N25Q or similar) and its current consumption.

- The voltage hold-up requirement: The flash memory typically requires a minimum voltage (e.g., 2.5 V for 3 V part) to operate. The hold-up capacitor must maintain VCC above that threshold for the duration of the write operation.

- The schematic may show the current draw of the flash and microcontroller from +5V_HOLD. If the load is, say, 20 mA, then the droop rate can be approximated: dV/dt = I/C. For I=20 mA, C=4700 µF, dV/dt = 20e-3 / 4700e-6 ≈ 4.26 V/s. That means the voltage will drop 4.26 V in one second. Starting from ~4.7 V, it would drop to near zero in about 1.1 seconds. That's a lot of time, but we need to consider that the write operation may be only a few hundred ms.

- However, if the load is higher, say 100 mA, dV/dt = 100e-3 / 4700e-6 ≈ 21.3 V/s. So it would drop 4.7 V in ~0.22 s (220 ms). That might be enough for flush.

- The schematic may also show additional capacitors on the rail (C10, C11, etc.) that provide filtering.

- The presence of sense lines suggests there is a regulator that monitors the voltage and may shut down when below threshold. The design may need to ensure the voltage remains above the UVLO threshold of the microcontroller/flash.

- The schematic may show the flash memory's write current (maybe 30 mA) and the microcontroller's active current (maybe 50 mA). Summing yields total load.

- The diode's reverse leakage current may also discharge the capacitor over time, but that's likely negligible.

- The design may have a brown-out detection circuit that triggers a shutdown when VCC drops below a threshold. The hold-up capacitor must supply enough charge to allow the microcontroller to complete the write before the brown-out triggers.

Thus, from schematic alone we can estimate the hold-up time based on known load currents and capacitance. We can also check if the capacitor voltage rating is adequate (likely 10 V or 16 V). The diode's forward voltage drop reduces available headroom.

We can also check if there are any other components that share the +5V_HOLD net, like USB power, which may increase load.

We can also examine the schematic for any current limiting resistors or fuses that might limit current.

We can also see if there is a explicit "hold-up" circuit like a boost converter that might be used to maintain voltage. But likely it's just a capacitor.

Now, what must wait for bench verification?

- The actual load current during the shutdown sequence is unknown without measuring. The microcontroller may be in a low-power mode, but the flash write will draw higher current.

- The actual voltage droop under load: the capacitor's ESR and the diode's dynamic resistance may cause additional drop at high currents.

- The actual timing of the shutdown sequence: how long does the microcontroller need to flush telemetry? That depends on firmware.

- The actual leakage currents of the diode and any other circuits connected to +5V_HOLD.

- The actual behavior of the brown-out detection threshold and hysteresis.

- The actual temperature dependence of the capacitor (electrolytic capacitors have higher ESR at low temperature).

- The actual voltage of the standby rail (+5VSB) under load and line variations.

- The actual presence of any additional loads (like USB devices) that may be connected during power loss.

- The actual ability of the system to gracefully shut down within the hold-up time.

- The actual measurement of the hold-up time under realistic load conditions.

Thus, the schematic can give us a rough estimate, but bench verification is needed to confirm the hold-up time, the actual load currents, the voltage droop, and the overall system behavior.

We need to produce a detailed answer, enumerating assumptions, checking numbers, and then concluding with a specific section.

The question: "Assess what can be concluded from the schematic alone and what must wait for the bench."

Thus we need to separate what is knowable from schematic vs. what requires measurement.

We should also mention that the schematic shows C1 as 4700 µF, D1 as SB120 (or SS14). The net +5V_HOLD is likely connected to the flash memory and microcontroller. The voltage sense lines may be used for monitoring.

We can estimate the hold-up time using typical numbers: assume load current of 50 mA (microcontroller + flash). Then dV/dt = I/C = 0.05 / 0.0047 = 10.64 V/s. Starting from ~4.7 V, time to drop to 2.5 V (minimum for flash) is (4.7 - 2.5)/10.64 ≈ 0.207 s (207 ms). That's likely enough for a quick flush. But if load is higher, say 100 mA, time halves to ~100 ms. Still might be enough.

But we need to consider the diode drop: at low currents, forward drop is ~0.3 V; at higher currents, it may be ~0.5 V. So initial voltage maybe ~4.5 V.

Also, the capacitor has ESR, maybe 0.1 ohm. At 100 mA, drop = I*ESR = 0.1*0.1 = 0.01 V, negligible.

Thus, from schematic we can conclude that the hold-up time is likely on the order of hundreds of milliseconds, sufficient for typical flash writes. However, we cannot confirm without bench.

We also need to consider the possibility of multiple loads: USB ports may draw current, but they might be shut down during hold-up.

The schematic may show the flash memory part number, which we can look up for current consumption. But we don't have that info here. However, we can assume typical 16 MB flash consumes maybe 20-30 mA during write.

Thus, we can estimate.

Now, the question mentions OQ-56 notes ride-through not bench-verified. So we need to reference that.

Thus, answer structure:

- Introduction: describe the relevant parts.

- From schematic we can deduce:
  - Capacitor value and voltage rating.
  - Diode type and forward drop.
  - Connectivity of +5V_HOLD net to flash and microcontroller.
  - Presence of voltage sense lines for monitoring.
  - Estimated time constant and hold-up time based on assumed load currents.
  - That the design intent is plausible given typical currents.
  - That the diode provides isolation and minimal drop.
  - That the capacitor size is consistent with hold-up requirements.

- From schematic alone we cannot confirm:
  - Actual load current during shutdown (depends on firmware, peripherals).
  - Actual voltage droop under load (including ESR, diode forward drop variation).
  - Actual timing of shutdown sequence (firmware dependent).
  - Actual brown-out threshold and hysteresis.
  - Temperature effects on capacitor and diode.
  - Interaction with other rails (e.g., USB) that may share the net.
  - Real-world leakage currents.
  - Whether the hold-up is sufficient for the specific flash memory's write cycle.

- Bench verification needed:
  - Measure hold-up time under realistic load.
  - Measure voltage droop and shape.
  - Verify shutdown sequence timing.
  - Verify brown-out detection works as expected.
  - Verify temperature behavior.
  - Verify no unexpected loads.

- Conclusion: Summarize.

We need to be specific: name nets, refs, parts.

The nets: +5V_HOLD, /+5V_HOLD (maybe same?), but the question mentions /+5V_HOLD (inverted? Actually it's /+5V_HOLD, likely active-low net name, but physically it's 5V hold). The capacitor C1 is on that net.

The diode D1: SB120 or SS14.

The flash memory: unknown part, but likely connected to +5V_HOLD.

Thus, we can reference these.

Now, let's produce a thorough answer.

We'll need to do some calculations.

First, determine the capacitance: 4700 µF = 4.7e-3 F.

Assume nominal voltage after diode: V_initial ≈ 5 V - V_f. For SB120, V_f ≈ 0.3 V at rated current (maybe 1 A). So V_initial ≈ 4.7 V.

Minimum operating voltage for typical flash: V_min ≈ 2.5 V (for 3 V part) or maybe 1.8 V if it's a low-voltage flash. But we don't know. Assume V_min = 2.5 V.

Thus, ΔV = V_initial - V_min ≈ 4.7 - 2.5 = 2.2 V.

Now, load current: Let's assume microcontroller plus flash write current = I_load. We need to estimate. Without specific part numbers, we can assume worst-case 100 mA. Or we can look at typical MCU current consumption: maybe 50 mA at 100 MHz. Flash write may add 20 mA. So total ~70 mA.

Let's do a range: I = 50 mA to 150 mA.

Compute hold-up time t = C * ΔV / I.

For I=50 mA: t = 4.7e-3 * 2.2 / 0.05 = (0.01034) / 0.05 = 0.2068 s ≈ 207 ms.

For I=100 mA: t = 0.01034 / 0.1 = 0.1034 s ≈ 103 ms.

For I=150 mA: t = 0.01034 / 0.15 = 0.069 s ≈ 69 ms.

Thus, hold-up time likely in the range of 70-200 ms.

Now, typical flash write sector erase time: For many flashes, erasing a 4 KB sector takes ~20 ms. Writing a page (256 bytes) takes ~0.5 ms. Flushing telemetry (maybe a few KB) may take <50 ms. So 70-200 ms is likely sufficient.

But we need to consider that the microcontroller may need to finish any pending operations, maybe up to 100 ms.

Thus, from schematic we can conclude that the hold-up time is likely adequate for typical flash write times.

However, we must note that the actual load may be higher if USB or other peripherals are active. Also, the capacitor's ESR will cause a sudden drop at the start of the power loss due to the inrush current of the load. The ESR of a 4700 µF electrolytic is typically around 0.1 Ω to 0.2 Ω at 120 Hz. At 100 mA step, drop = 0.1*0.1 = 0.01 V, negligible.

But the diode's forward voltage drop may increase at high currents. At 100 mA, V_f may be ~0.4 V. So initial voltage may be ~4.6 V. That reduces ΔV slightly.

Thus, the estimate is approximate.

Now, the schematic may show the brown-out detection threshold. For example, the MCU may have a brown-out at 2.5 V. The hold-up must keep voltage above that threshold for the duration of the shutdown ISR.

Thus, we can calculate the allowed drop: from 4.7 V to 2.5 V = 2.2 V. At 100 mA, that's ~103 ms. At 150 mA, ~69 ms.

Thus, the hold-up is likely sufficient if the shutdown time is <50 ms.

But if the shutdown sequence takes longer (e.g., due to multiple retries or large data), it may be insufficient.

Thus, bench verification needed.

Now, we need to mention that the schematic does not show the actual load currents or the firmware timing. So we cannot be sure.

Also, the presence of other capacitors on the net (C10-C16) may affect the droop shape, but they are likely smaller (maybe 100 nF) for decoupling, not for hold-up.

Thus, the main hold-up is C1.

Now, the diode D1's reverse recovery time is small (Schottky), so it's fine.

Now, the question: "Assess what can be concluded from the schematic alone and what must wait for the bench."

Thus, we need to list conclusions that can be drawn from schematic:

- The presence of a large reservoir cap indicates intent for hold-up.

- The value 4700 µF is consistent with providing hold-up in the order of 100 ms for typical loads.

- The diode D1 isolates the hold-up rail from the source and provides low drop.

- The net +5V_HOLD is connected to the flash memory and microcontroller (likely), as per typical design.

- The voltage sense lines suggest monitoring, but not necessarily active regulation.

- The design is plausible for meeting the hold-up requirement if load current is within expected bounds.

- The schematic does not show any active boost or backup regulator, so the hold-up is purely passive.

- The diode's forward voltage drop reduces headroom, but still leaves enough for 3.3 V or 2.5 V operation.

- The capacitor's voltage rating (likely 10 V or 16 V) is adequate for 5 V rail.

Now, what must wait for bench:

- Actual load current during shutdown (depends on firmware, peripheral activity).

- Actual voltage droop waveform and hold-up time under load.

- Effect of ESR and diode forward drop at actual currents.

- Temperature dependence of capacitor and diode.

- Possible leakage currents that discharge the capacitor when not in use.

- Interaction with other rails (e.g., USB) that may share the net.

- Verification of brown-out detection timing.

- Confirmation that the flash write completes within the hold-up time.

- Effect of capacitor aging (electrolytic dry out) on hold-up time.

- Verification of the alternative diode SS14 performance vs. SB120.

Thus, we need to produce a final answer with a section "## Conclusions" summarizing the key points.

We should also mention that OQ-56 is a test point that indicates the ride-through has not been bench-verified.

Now, let's write the answer in a structured way.

We'll start with introduction, then "Schematic-only analysis", then "Bench-required analysis", then "## Conclusions".

Make sure to use the exact heading "## Conclusions".

We'll include specific net names, refs, and part numbers.

We'll also include some calculations.

We'll be thorough.

Now, writing.

## Conclusions
**Overview of the relevant portion of the schematic**

- **Capacitor C1**: 4700 µF electrolytic, connected between the net **/+5V_HOLD** (the hold‑up rail) and **GND**.  
- **Diode D1**: SB120 (or the drop‑in alternative SS14), a Schottky barrier diode that isolates the hold‑up rail from the upstream **+5VSB** rail. The Schottky gives a low forward drop (≈0.3 V at rated current).  
- **Net +5V_HOLD**: This rail feeds the power‑on domain that must survive a short interruption – typically the microcontroller (or MPU) and the 16 MiB flash memory that stores telemetry.  
- **Associated sense nets**: /5VSB_SENSE, /HUB_3V3_SENSE, /KVM_3V3_SENSE, etc., are present for monitoring but do not actively regulate the hold‑up rail.  
- **Test point OQ‑56**: Explicitly notes that the ride‑through behavior has **not been bench‑verified**.

Below is a step‑by‑step assessment of what can be deduced from the schematic alone versus what must be measured on the bench.

---

## 1. What the schematic tells us

| Item | What can be inferred |
|------|----------------------|
| **C1 value (4700 µF)** | Provides a *large* reservoir. Using the simple capacitor discharge equation \( t = C \Delta V / I_{\text{load}} \), we can obtain a rough estimate of the hold‑up window (see calculations below). |
| **D1 (SB120/SS14) – Schottky diode** | Forwards ≈0.3 V at normal load currents, so the hold‑up rail starts at roughly **4.7 V** when the upstream 5 VSB is present. The diode also prevents back‑flow, ensuring the capacitor only supplies the downstream load. |
| **Isolation from +5VSB** | Because of D1, the hold‑up rail is de‑coupled from supply transients on +5VSB, giving a cleaner “reservoir” during a mains loss. |
| **Connectivity of +5V_HOLD** | The net is drawn to the flash memory and the core logic (the exact part not listed, but typical for a KVM hub). This is the load that must remain powered long enough to flush telemetry. |
| **Voltage headroom** | Starting at ≈4.7 V and assuming the flash and MCU can operate down to ≈2.5 V (common for 3 V Flash) gives an allowable drop of **≈2.2 V** before data integrity is at risk. |
| **No active regulator on the hold‑up rail** | The design is purely passive – a capacitor and diode only. There is no boost or LDO that could extend the hold‑up time. |
| **Presence of smaller decoupling caps (C10–C16, etc.)** | These are for high‑frequency filtering and will not contribute meaningfully to long‑duration hold‑up. |
| **Diode alternative (SS14)** | The SS14 is electrically similar (same forward voltage range, same current rating). Any difference in leakage or reverse recovery is negligible for this application. |

### Rough hold‑up time estimate (schematic‑only)

1. **Initial voltage** after diode drop:  
   \[
   V_{\text{start}} \approx 5.0\,\text{V} - V_f \approx 5.0 - 0.3 = 4.7\,\text{V}
   \]

2. **Minimum operating voltage** for typical 3 V‑compatible flash (e.g., 1.8 V – 3.6 V range) is about **2.5 V**.  
   \[
   \Delta V = V_{\text{start}} - V_{\min} \approx 4.7 - 2.5 = 2.2\,\text{V}
   \]

3. **Assume a realistic load** (microcontroller + flash write) of **50 mA – 150 mA**. The schematic does not list the exact current, but this range is typical for a Cortex‑M class MCU writing to SPI Flash.

   \[
   t_{\text{hold}} = \frac{C \, \Delta V}{I_{\text{load}}}
   \]

   - At 50 mA:  
     \[
     t = \frac{4.7\times10^{-3} \times 2.2}{0.05} \approx 0.21\,\text{s} \;(210\,\text{ms})
     \]
   - At 100 mA:  
     \[
     t \approx 0.10\,\text{s} \;(100\,\text{ms})
     \]
   - At 150 mA:  
     \[
     t \approx 0.07\,\text{s} \;(70\,\text{ms})
     \]

4. **Interpretation**: The calculated window is **70 – 210 ms**, which is *plausible* for flushing a few kilobytes of telemetry (typical erase‑write cycles are < 50 ms). The design therefore appears *viable* in principle, but the exact figure depends on the real load.

5. **ESR effects**: A 4700 µF electrolytic typically has ESR ≈ 0.1 Ω at 120 Hz. At a 100 mA step, the instantaneous drop is only \(I \times ESR \approx 10\,\text{mV}\), negligible compared with the 2.2 V headroom.

6. **Diode forward‑drop variation**: At higher currents the forward drop may rise to ≈ 0.4 V, reducing \(V_{\text{start}}\) to ≈ 4.6 V and thus ΔV to ≈ 2.1 V. This changes the numbers by < 5 %, still within the same order of magnitude.

**Conclusion from schematic‑only analysis**:  
The component choices (4700 µF, low‑drop Schottky) are *consistent* with a hold‑up requirement in the hundreds of milliseconds for a typical MCU + Flash load. The design is not obviously under‑sized, but the exact performance cannot be guaranteed without measurement.

---

## 2. What must wait for bench verification

| Aspect | Why bench is required |
|--------|-----------------------|
| **Actual load current during shutdown** | Firmware controls peripheral states (USB, Ethernet, etc.). The schematic only shows the *connected* blocks, not their instantaneous consumption. A scope or current probe during a power‑loss test is needed. |
| **Real‑world hold‑up time** | The calculated range assumes constant current. In practice the load may be pulsed (e.g., burst of writes), causing a faster voltage droop than the average current suggests. |
| **Voltage droop waveform** | ESR, diode forward‑drop variation, and any ringing from the decoupling network will shape the droop. Oscilloscope capture during a simulated loss is essential to see if the rail dips below the MCU’s brown‑out threshold before the flush completes. |
| **Brown‑out detection timing** | The MCU’s BOD threshold (e.g., 2.4 V) and hysteresis are not visible on the schematic. The actual time the device stays alive after V_HOLD falls below the BOD must be measured. |
| **Temperature dependence** | Electrolytic capacitors lose capacity and increase ESR at low temperature. A cold‑start hold‑up test (e.g., –20 °C) may reveal insufficient margin. |
| **Leakage / parasitic discharge** | Reverse leakage of D1, PCB surface resistance, and any “always‑on” loads on +5V_HOLD (e.g., status LEDs) will slowly discharge C1 when the main supply is off. This can be measured with a high‑impedance meter. |
| **Interaction with other rails** | If any other subsystem (e.g., USB power‑mux) shares +5V_HOLD, extra load may appear during a power loss. The schematic does not show such sharing, but bench inspection of the layout and netlist is required to confirm. |
| **Aging / derating of C1** | Electrolytic capacitors dry out over time. Bench testing should include accelerated life tests or at least measurement of actual capacitance under operating voltage and temperature. |
| **Verification of SS14 vs. SB120** | While both are electrically similar, subtle differences in reverse‑recovery charge or leakage could affect hold‑up at very low currents. A direct comparison test is needed. |
| **End‑to‑end shutdown sequence timing** | The firmware’s “flush telemetry” routine must be timed with the hardware present. Only a live test can confirm that the MCU completes the write before the BOD resets it. |

---

## 3. Summary of the split between “schematic‑only” and “bench‑required”

| Schematic‑only (deterministic) | Bench‑required (empirical) |
|--------------------------------|----------------------------|
| • C1 = 4700 µF → provides a *large* reservoir.<br>• D1 (SB120/SS14) gives low forward drop (≈0.3 V) and isolates the rail.<br>• Net +5V_HOLD is clearly the hold‑up node for flash/MCU.<br>• Simple RC discharge calculation yields a **plausible** hold‑up window of **70 – 210 ms** for a 50‑150 mA load.<br>• No active regulator is present, so the design relies solely on the capacitor’s stored charge.<br>• The diode alternative (SS14) is electrically equivalent, so no schematic change is needed. | • **Actual load current** during the shutdown ISR (depends on firmware, enabled peripherals).<br>• **Measured hold‑up time** under that real load.<br>• **Voltage droop shape** (ESR, diode forward‑drop at high current, decoupling network response).<br>• **Brown‑out detection threshold** and hysteresis of the MCU.<br>• **Temperature effects** on C1 (capacity loss, ESR increase).<br>• **Leakage currents** (diode reverse leakage, PCB surface, any hidden loads).<br>• **Interaction with other rails** that may share +5V_HOLD.<br>• **Aging/derating** of the electrolytic capacitor.<br>• **Firmware timing**: the exact time needed to flush telemetry must be measured end‑to‑end.<br>• **Verification of SS14** performance versus SB120 in the actual circuit. |

---

## Conclusions

- **From the schematic alone**, the combination of a **4700 µF electrolytic (C1)** and a **low‑drop Schottky diode (D1 – SB120/SS14)** on the **/+5V_HOLD** net is a *reasonable* passive hold‑up design. Simple calculations indicate that, for a typical MCU + 16 MiB flash load of 50 – 150 mA, the capacitor can supply **≈70 ms – 210 ms** of hold‑up before the voltage falls from ≈4.7 V to the ≈2.5 V minimum required by the flash. This duration is *likely* sufficient for a telemetry flush (which typically takes < 50 ms), but the exact margin cannot be guaranteed without measurement.

- **What must wait for bench verification** includes: the actual load current during the shutdown sequence, the measured hold‑up time and voltage droop waveform, the MCU’s brown‑out threshold behavior, temperature and aging effects on C1, any hidden leakage or extra loads on +5V_HOLD, and the end‑to‑end firmware timing to ensure the flash write completes before the rail collapses. The note at **OQ‑56** (“ride‑through has not been bench‑verified”) correctly flags that the schematic alone does not constitute a verified solution.

- **In short**: The schematic shows a plausible hold‑up architecture, but the *actual* ride‑through performance is unconfirmed until a bench test (preferably with real firmware, at worst‑case temperature and load) demonstrates that the voltage on **/+5V_HOLD** remains above the flash’s minimum operating voltage for the entire duration of the telemetry flush.
```

</details>

## source-sense — **HOLDOUT** (content withheld; see tests/holdout/extractor/)

---

# Live eval outcome (run 2, 2026-06-10) — GATE: **FAIL** (recorded honestly)

Manifest: cec-worker-quality (27B) + extract-prompt v2 + const-subject grammar v2.

| register | cases | zero-tolerance failures | field accuracy |
|---|---|---|---|
| **real (the gate)** | 6 | **49** | **0.278** |
| reconstructed | 12 | 3 | 0.955 |

Autopsy: ~40% formatting-stripped real quotes / ~60% true paraphrase. Owner rulings
2026-06-10: presentation-character canonicalization ratified into the verifier (v1.1.0;
rescues the formatting class for ATTRIBUTION only — the gate verdict for this manifest
stands FAIL); prompt verbatim-copy contract hardened (new manifest); attribution re-run
queued for GPU availability.
