nathanfraske/CEC-Platform/beta/output-daughterboards/eps-out-db/README.md

# EPS 8-pin output daughterboard (per-cable) — BETA-1

> **XFCN PROTOTYPE SUPERSESSION (2026-08-12):** the live authority uses four
> T34069 daughterboard bolt lands, each with a 3.4 mm plated M3 clearance
> hole, arranged `GND / +12V / +12V / GND`. The compact live outline is
> **28.0 × 18.5 mm** (9.2% less area than the 28.5 × 20.01 mm predecessor).
> The blade-era material below is retained only as historical provenance.

Passive connector-daughterboard for **one** EPS 8-pin cable's OUTPUT side,
per spec **§2.8 v1.4.0** and `docs/standard-tier-review/SYNTHESIS-beta-plan.md`
§D-5a. **One design, instantiated per cable** — the EPS module populates 2
cables, so 2 of these boards are built per module (identical PCB, no
per-cable variant). Mates with the main board's per-cable `TB{n}1`–`TB{n}6`
Keystone 3586 clips (TB symbols exist in `modules/eps-8pin`'s **schematic**,
commit `b76a62a`; **no clip placement exists on any main-board PCB yet** —
this board's tab grid is the authoritative mating drawing, see "Keying").
No active or passive components.

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

DRAFT (no fab yet — OQ-86 fit-check sample gate open).

## Posture — vertical card, tabs blade-DOWN (owner sketch, 2026-07-05)

This board is a small vertical card standing perpendicular to the main
board (unchanged). The connector form is settled by the **owner's sketch**
(the third and final same-day 2026-07-05 form — the two earlier ones are
retired, record in `docs/standard-tier-review/blade-fit-check-2026-07-04.md`
addendum 3; full geometry description in `atx24-out-db/README.md`
"Posture", identical here): the 6 **TE 63951-1** right-angle FASTON .250
tabs mount with their two legs **horizontal** through this board's face,
leg pitch (5.08 mm) **vertical** (legs stacked one above the other), so
each in-plane-L blade points **straight down**, descending past this
board's bottom edge at a 2.54–8.89 mm Z-standoff from the face. The whole
board drops vertically; the blades enter the main-board Keystone 3586
clips' **top-entry** jaws broadside, and the board's own bottom edge
**floats clear** of the main board — the tab does the reaching, not the
board. Board axes: X = length (FREE); Y = height — **the ≤15 mm cap is
EXPLICITLY RELAXED by the owner for the iteration-4 compact two-band form**
(see the 24-pin README's "Board axes" for the verbatim follow-up).

**Measured final size**: **38.5 × 20.0 mm** (length × height). Iteration 4
stacks the packed tab row BELOW the field band (owner: "stack the blades
right next to each other and put them below the pinout"), cutting length
67.8 → 43.0 mm at an honest height cost of 11.0 → 20.0 mm. Height
decomposition: 0.4 top margin + 10.2 field + 0.25 band gap + 4.82 tab
top-extent (carrier stub) + 3.79 pad lower half + 0.55 edge margin.
Length is tab-row-driven (6 × 7.6 mm pitch + margins).

## Mating geometry / seating model (iteration-4 numbers)

Same uniform model as the 24-pin board (one seating spec platform-wide,
asserted by `check_output_daughterboards.py`; derivation in that README):

- **Leg row**: **4.34 mm above the bottom edge** (uniform across families —
  the tab band is the lowest thing on every board; lower pad clears the
  0.5 mm copper-to-edge constraint by 0.05 mm, checker-asserted).
- **Blade standoff**: 2.54–8.89 mm off the front face; main-board clip slot
  centreline at **5.72 mm** from the wall plane, slot axis perpendicular
  to the wall line.
- **Descender reach**: blade tip 15.75 mm below the leg row → **11.41 mm
  below this board's bottom-edge level** (off-board at the standoff).
- **Seating**: the board **floats** (cannot edge-rest) — at the recommended
  1.0 mm tip clearance above the main-board surface (hard stop ≈0.4–0.5 mm,
  tip on the clip's own base metal), the bottom edge floats **12.41 mm**
  above the main board (now UNIFORM across families); top edge at
  **32.4 mm** (24-pin: 33.8). Blade engagement spans the clip's full
  7.16 mm interior. Legs protrude 2.21 mm out the back face.

## Mounting / retention — no mounting holes (owner directive, 2026-07-05)

Same ruling and rationale as the 24-pin board (see that README): retention
is the Keystone clip's own high insertion force (a feature, not a
shortfall) plus chassis strain relief on the cable/assembly side (OQ-87
owns the numeric spec). No BOM/schematic impact — mounts were a PCB-only
mechanical footprint on this generator, never a schematic part.

## Tab map (6 joints/cable, TE 63951-1 / LCSC C591344)

| Ref | Net | EPS8 pins bundled |
|---|---|---|
| J10, J11, J12 | GND | 1, 2, 3, 4 |
| J13, J14, J15 | +12V | 5, 6, 7, 8 |

3 contacts/polarity — matches spec §2.8 v1.4.0's ratified EPS joint count
(12 total across the module's 2 cables). Design-basis current: ~13 A/pin
continuous → ~52 A/cable sustained worst case → ~65 A margin target (§1 of
the output-daughterboard study), well inside 3× the Keystone 3586's 30 A
field rating (confirm-soak/thermal-cycle contact-R trend recommended before
BOM lock, OQ-86/88 — not gating).

## Output field (J1, `cec-Connector_Generic:EPS8_Daughterboard_Field_P4.20mm`)

Bare THT solder field, 8 positions, 2×4 @ 4.20 mm pitch / 5.5 mm row — the
real Molex Mini-Fit Jr 5569-08A2 land (measured off
`lib/vendor/Connector_Molex.pretty`). Pin map **1–4 = GND, 5–8 = +12V**,
matching the platform's own corrected EPS pinout convention (see
`CLAUDE.md` "EPS 8-pin power-connector pinout fix"). All 8 positions are
power-class (1.8 mm drill / 2.7×3.7 mm oval, 16 AWG-class) — no signal
circuits on this cable. Reuses the generic `cec:CEC_CONN_2x4` symbol
(unnamed pins; the net map lives in the wiring, not the symbol).

**Population options** — identical menu to the 24-pin board (see that
README for the full text): (1) bare 16 AWG pigtail (default); (2)
MODDIY-class vertical header, dimensionally compatible, **not placed** (no
footprint vendored, OQ-88 provenance gap); (3) sellable
daughterboard-plus-extension assembly (OQ-89).

## Keying

**Single row of 6 tabs at 7.6 mm pitch** (iteration-4 packed row), net
order GND×3 then +12V×3 (matching the tab map above). The pitch floor is
the **main-board clip row**, not the tab (each tab is ~0.84 mm thin along
the row; its 2.5 mm pads → 5.1 mm tab pad gap, trivially clear): the
Keystone 3586 rotated slot-perpendicular-to-wall presents 3.81 mm body /
3.82 mm courtyard and a **6.60 mm SMD pad span** along the row — **floor =
6.60 + 0.50 stated solder clearance = 7.10 mm**. This board sits 0.5 mm
above the floor purely for KEYING (the delta to PCIe's at-floor 7.1 mm
pitch that keeps the no-subset proof green — see below). At 7.6 mm:
**3.78 mm clip body gap, 1.00 mm pad gap** — asserted with printed numbers
by `check_output_daughterboards.py` §3b.

**The real safety property is proved geometrically, not by pitch alone.**
`scripts/check_output_daughterboards.py` takes every family's tab-centre
list straight from `pcb_placement()` (the committed board's own
coordinates) and, for every ORDERED pair, searches all 4 rotations
(0/90/180/270°) × every candidate translation for a rigid whole-set mapping
onto a subset of another family's grid, within 0.5 mm (exact bipartite
match). All 6 ordered pairs (this family vs. both others, both directions)
come back "cannot seat" — **re-proved at the iteration-4 packed pitches
(8.4/7.6/7.1)**. The pitch here (7.6 mm) and PCIe's (7.1 mm) differ by
0.5 mm, giving a (G/2)×Δpitch = 0.75 mm end error at PCIe's G=3 — 1.5× the
0.5 mm tolerance, so pitch differentiation survives at the packed floor and
no pattern keying was needed. The historic failure mode (0.1 mm/step over
3 gaps = 0.15 mm end error → PCIe seated inside this board's grid) stays
live in the checker's teeth: a sabotaged 7.2 mm pitch here was re-verified
this pass to make the proof correctly FAIL. See
`scripts/gen-output-daughterboard.py`'s `TAB_PITCH` comment for the floor +
delta math. **This daughterboard's tab grid is the authoritative main-board
mating drawing** for the EPS per-cable clip pattern (TB clip symbols exist
in the main board's schematic only; the future clip-placement pass mirrors
these X positions, the rotated-clip orientation, and the 5.72 mm
slot-centreline standoff).

**Dual-face tabs**: evaluated and rejected under the earlier flat-tab model
(see the 24-pin README); moot a fortiori under the sketch model — the row
pitch is clip/keying-limited, not tab-body-limited. Single-face, single-row
stands.

## Layer stack / current

**4-layer** (F.Cu / In1.Cu / In2.Cu / B.Cu, 2 oz outer / 1 oz inner) — this
is a **2-net board** (GND, +12V), so unlike the 24-pin board there is no
inter-rail banding problem: **GND floods both inner layers** (In1.Cu +
In2.Cu, matching this platform's own already-built EPS/PCIe cable-power
convention — "two GND inners... 12V lives on the OUTERS",
`scripts/gen-module-pcb.py` `gnd_planes()` docstring) and **+12V floods both
outer layers** (F.Cu + B.Cu). Every field pin and blade tab here is a
through-hole pad by construction (no SMD parts on this board at all), so
each already carries copper on every layer; the real `ZONE_FILLER`
auto-clears around every foreign-net pad within a flood's outline and
auto-connects to every same-net pad — **no explicit tracks/vias are needed
at all** for a genuine 2-net board, which is why 2-layer was NOT chosen
instead: doubling the copper thickness on both rails via full F+B and
In1+In2 pairing (four total flooded layers across two nets) directly buys
current margin on the ~65 A/cable target the 2-layer alternative would have
to fight for with much thinner single-layer copper.

## Electrothermal sanity — not needed as a solver run

Both nets are full-board floods on doubled layer pairs with no thin
fan-out geometry to check (no per-pin stub traces exist on this board —
see above); the governing current-capacity question is the **blade-clip
joint** itself (OQ-86's recommended confirm-soak/thermal-cycle bench), not
this board's own copper. Noted, not treated as a gap.

> **CORRECTION (2026-07-06, blade-interconnect thermal audit): the claim
> above is falsified — the solver run WAS needed.** The copper has no thin
> neck (correct), but at the 52 A worst-case basis the board dissipates
> ~2.75 W on ~11 cm² of still air: the 2.5D coupled solve gives
> **dT 216.7 °C** in the enclosed/no-sink posture vs the 30 °C-rise policy —
> a board-LEVEL dissipation red, not a neck. Unmodelled conduction sinks
> (blades → main board, pigtail copper, chassis strain relief) are large
> and the basis is worst-case (dT ~ I²: at half current ~54–71 °C class),
> so this is a gate red pending the OQ-86 thermal-soak datum, not a
> fusing defect. See
> `docs/standard-tier-review/blade-interconnect-thermal-2026-07-06.md` (F2).

## Sense-return provision

Not provisioned on this board (no signal header exists here, unlike the
24-pin board — EPS carries only GND/+12V). If OQ-88's sense-return decision
lands "yes" for EPS, it needs a small signal-tab addition in a future
revision; not a silent gap, just genuinely absent today.

## Verification (this pass — 2026-07-05 iteration-4 compact two-band layout)

- ERC: 0 errors (2 benign `lib_symbol_mismatch` warnings).
- Static connectivity audit: clean.
- DRC: **0 errors, 0 unconnected** (`kicad-cli pcb drc --severity-error`).
  At full verbosity: 17 hits, ALL cosmetic silk (5 `silk_overlap` +
  12 `silk_over_copper` — the documented-benign class; silk counts rose
  with the denser two-band stack, no copper impact).
- `scripts/check_output_daughterboards.py`: all checks pass, including the
  updated sketch-model checks (tab rot 0 / legs vertical / the NEW uniform
  4.34 mm leg-row-above-edge seating invariant / clip-row gaps recomputed
  at the packed pitches) and the geometric no-subset-seating proof re-run
  at 8.4/7.6/7.1 (teeth re-verified at the floor via a sabotaged 7.2 mm
  pitch — see the 24-pin README).
- Netlist-verified: all 6 tabs land on their mapped rail; the field's 8
  positions reproduce the platform's corrected EPS8 pinout exactly.
  Net-group identity vs. the pre-rework baseline confirmed (2→2 groups).

## Library assets used

- **`cec-vendor:TE_63951-1_FASTON_Tab` / `cec-Connector_Blade:TE_63951-1_FASTON_Tab_250x032_RA_THT`
  (LCSC C591344, in stock, $0.099–$0.164/unit by qty)** — right-angle .250
  FASTON tab, footprint REWRITTEN this pass to the true in-plane-L geometry
  (legs stacked vertically at (0, ±2.54), blade descending +Y at the
  2.54–8.89 mm standoff) from TE dwg C=63951 rev L2
  (`lib/datasheets/TE_63951-1.pdf`); see the blade-fit-check addendum 3 for
  the retired interim model.
- `cec-vendor:TE_63849-1_FASTON_Tab` / `cec-Connector_Blade:TE_63849-1_FASTON_Tab_250x032_THT`
  — pre-existing, LCSC C86469, unreferenced by this generator (left
  vendored; harmless).
- `cec:CEC_CONN_2x4` (pre-existing generic connector symbol).
- `cec-Connector_Generic:EPS8_Daughterboard_Field_P4.20mm` — tightened its
  Y-margin in an earlier pass (pad half-height instead of half the row
  pitch, `scripts/gen-daughterboard-libassets.py`), dropping its own
  courtyard height 13.0→10.2 mm; the single biggest lever in clearing the
  height cap. Unchanged this pass.
- No mounting-hole footprint — removed in an earlier pass (owner directive;
  see "Mounting / retention" above). Never a schematic/BOM part on this
  generator, so the BOM is unaffected.

Generator: `scripts/gen-output-daughterboard.py eps-out-db`.

---
## 2026-07-06 — solid high-current joints

`route_simple()` now sets `ZONE_CONNECTION_FULL` on both power floods (was the
KiCad-default THERMAL RELIEF — four 0.5 mm spokes necked the high-current joint,
owner observation). Result at worst-case no-sink: eps-out-db dT drops ~40 %
(eps 235→141 °C, pcie 117→70 °C), tab pads go from hottest feature to cool/solid.
DRC 0/0, checker 113 OK. Record + map: `docs/standard-tier-review/
thermal-wave1-daughterboard-landing-2026-07-06.md`.
