nathanfraske/CEC-Platform/beta/12vhpwr-standard/12vhpwr-route-plan.png

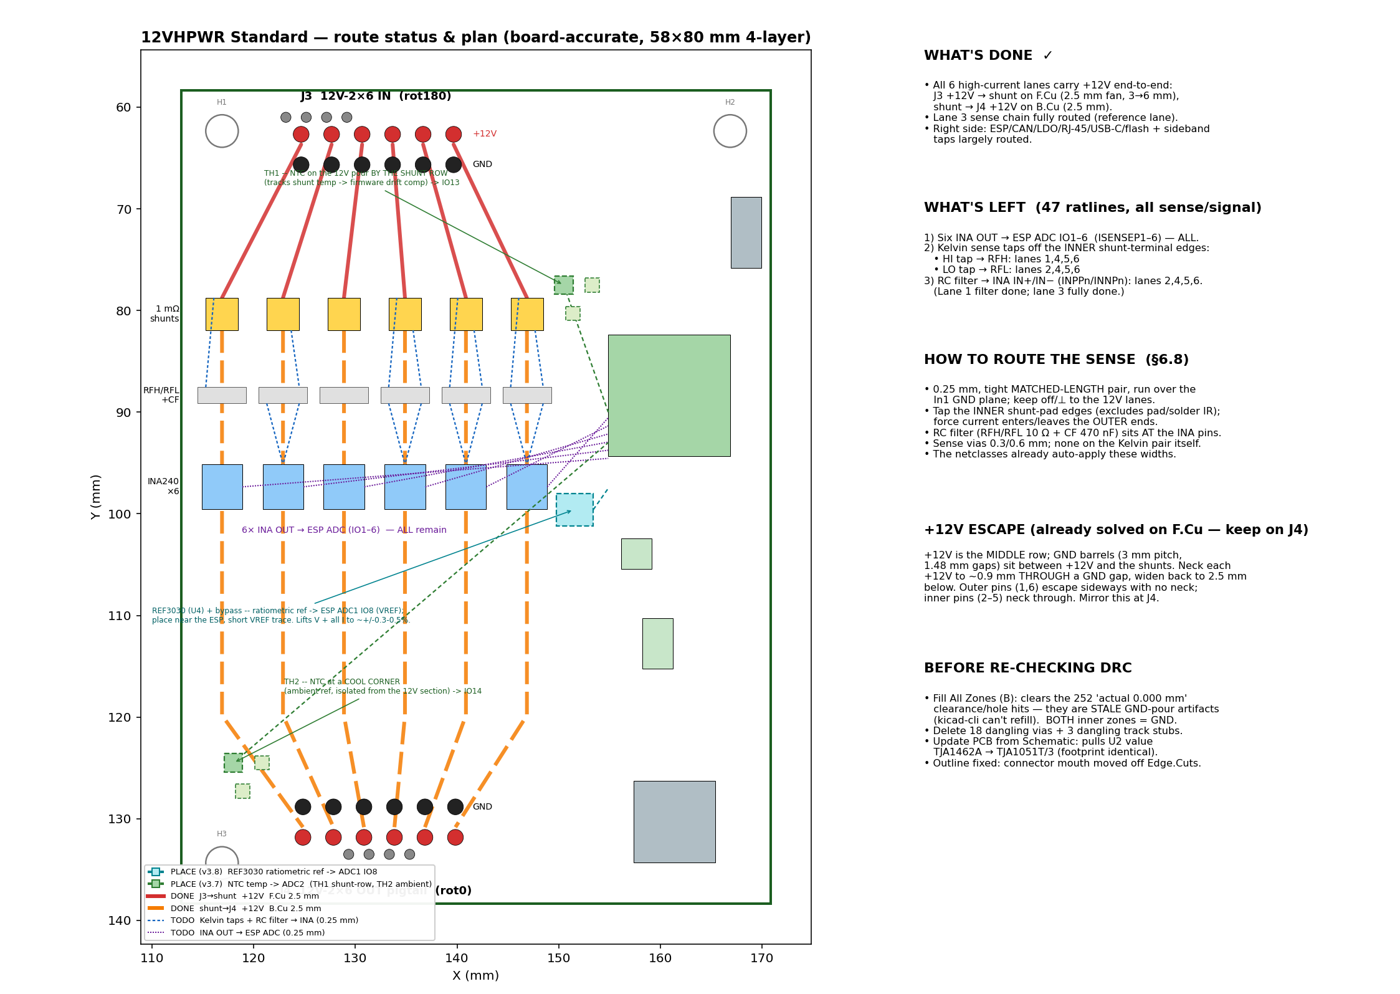
beta/12vhpwr-standard/12vhpwr-route-plan.png
