nathanfraske/CEC-Platform/beta/12vhpwr-standard/12vhpwr-routing-plan.png

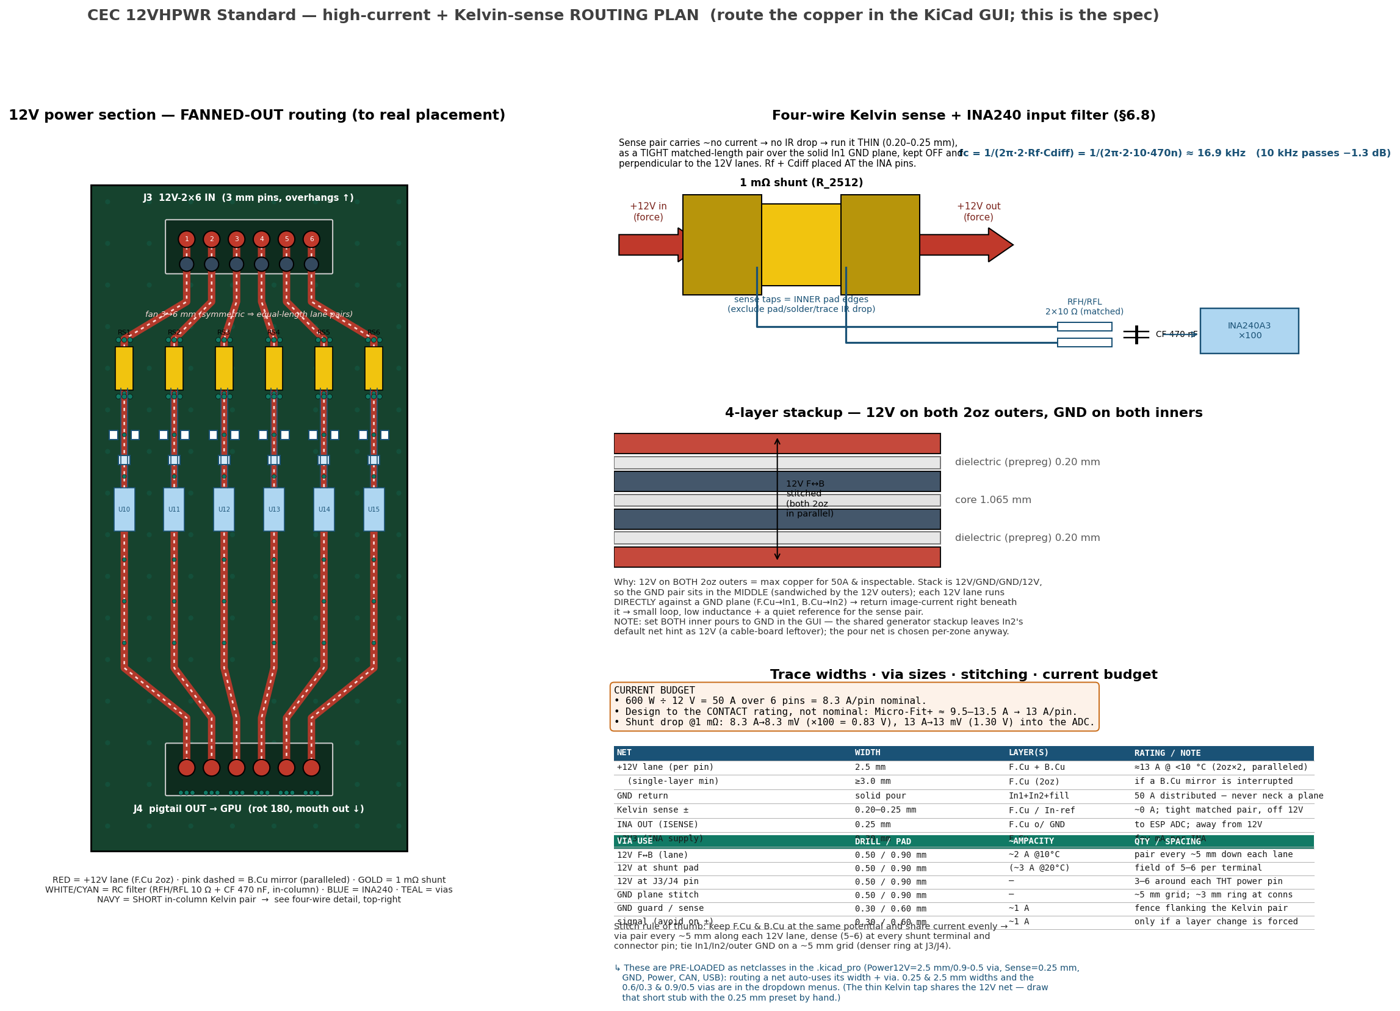
beta/12vhpwr-standard/12vhpwr-routing-plan.png
