nathanfraske/CEC-Platform/beta/pcie-8pin-2port/pcie2-routing-plan.png

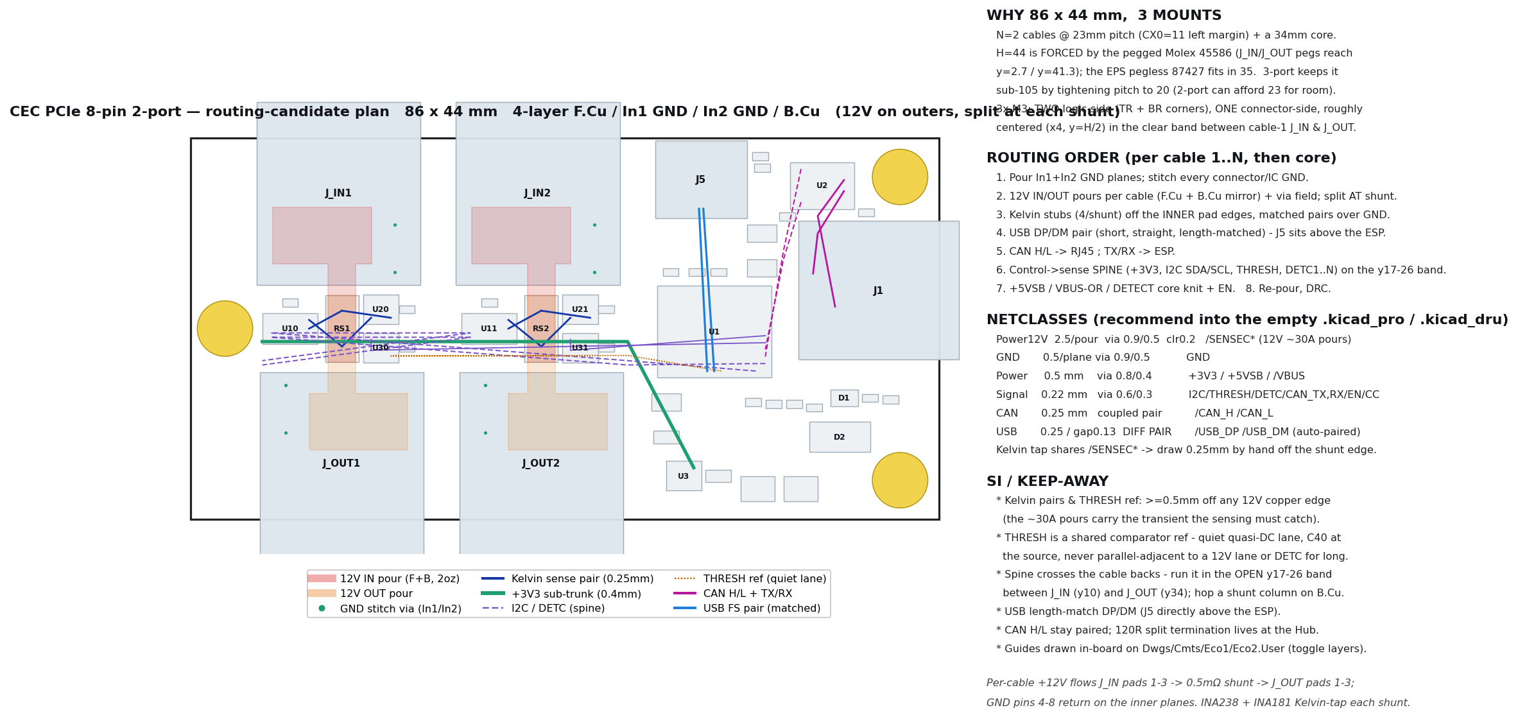
beta/pcie-8pin-2port/pcie2-routing-plan.png
