nathanfraske/CEC-Platform/beta/pcie-8pin-3port/pcie3-routing-plan.png

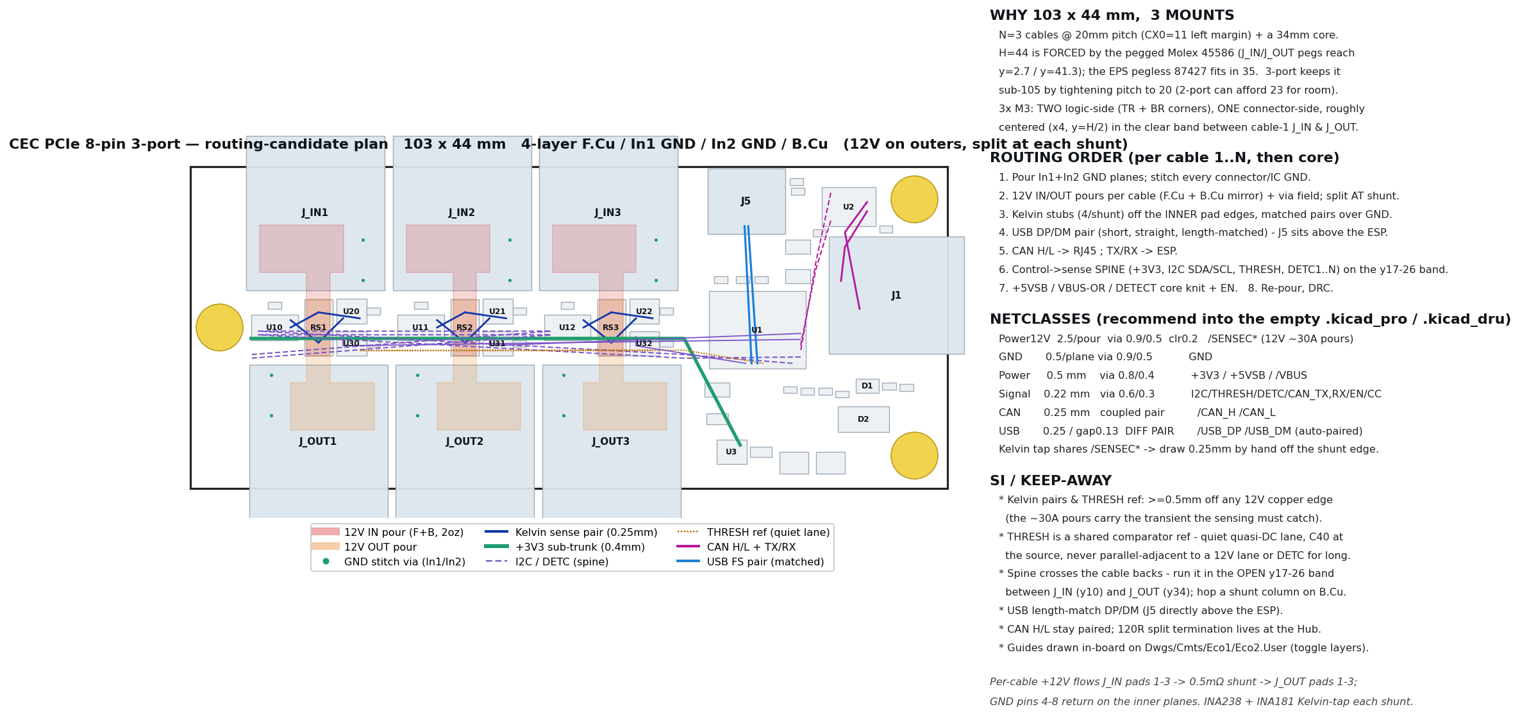
beta/pcie-8pin-3port/pcie3-routing-plan.png
