nathanfraske/CEC-Platform/docs/cl19-trace-gallery-2026-06-10/spots/hub-source-sense-u7-r15-r18.png

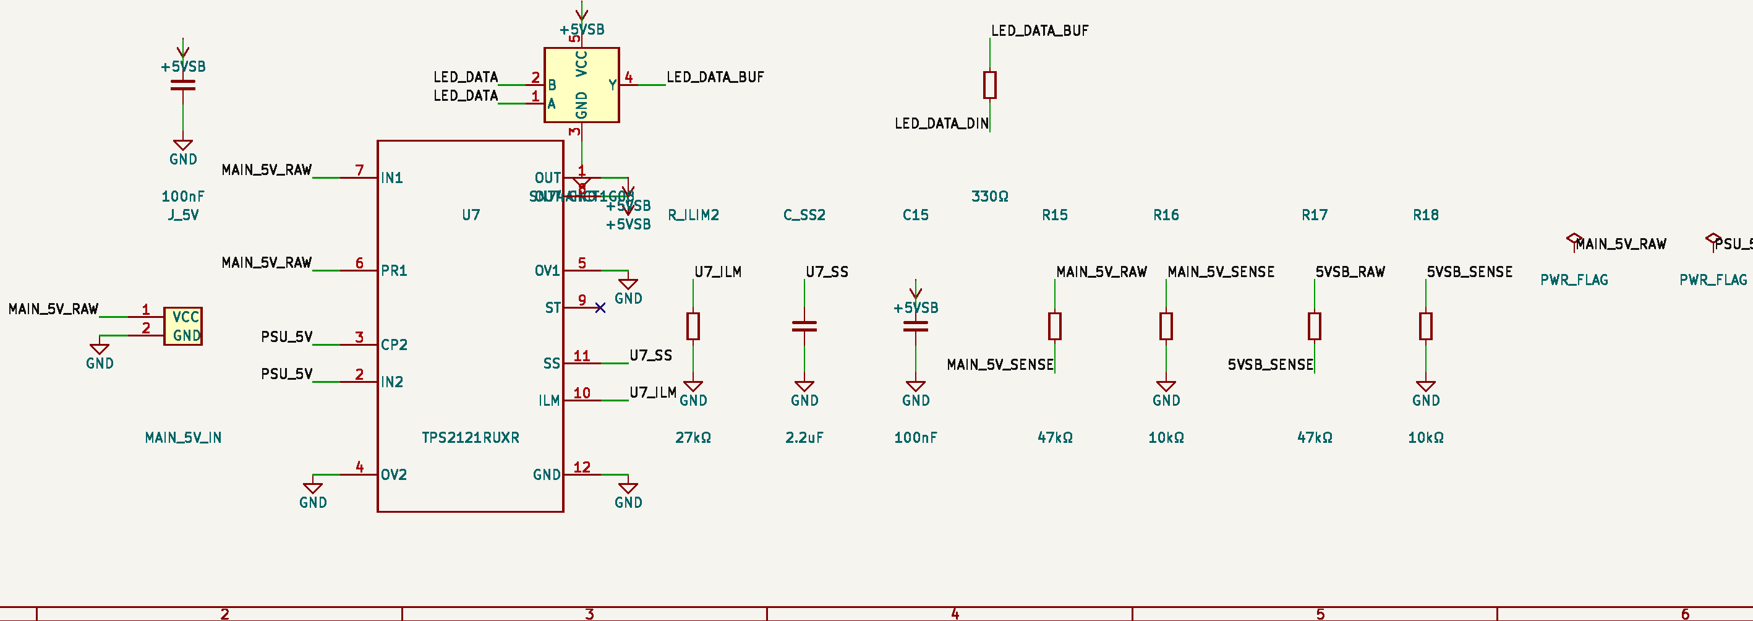
docs/cl19-trace-gallery-2026-06-10/spots/hub-source-sense-u7-r15-r18.png
