nathanfraske/CEC-Platform/docs/det-inspection/incremental-samples/clean.png

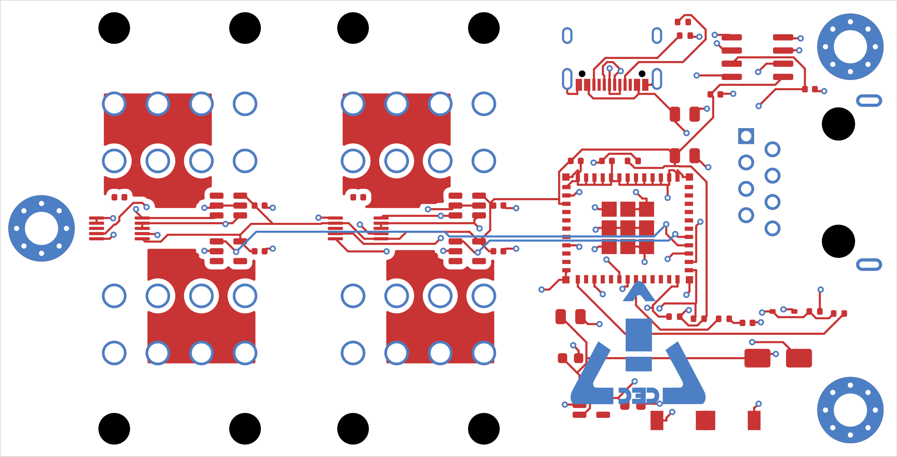
docs/det-inspection/incremental-samples/clean.png
