nathanfraske/CEC-Platform/docs/det-inspection/incremental-samples/corrupt_svg.png

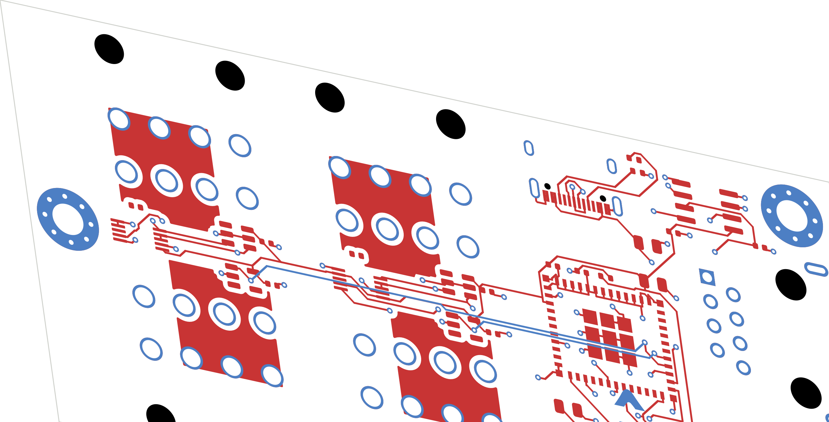
docs/det-inspection/incremental-samples/corrupt_svg.png
