nathanfraske/CEC-Platform/docs/det-inspection/incremental-samples/dropped_zone.png

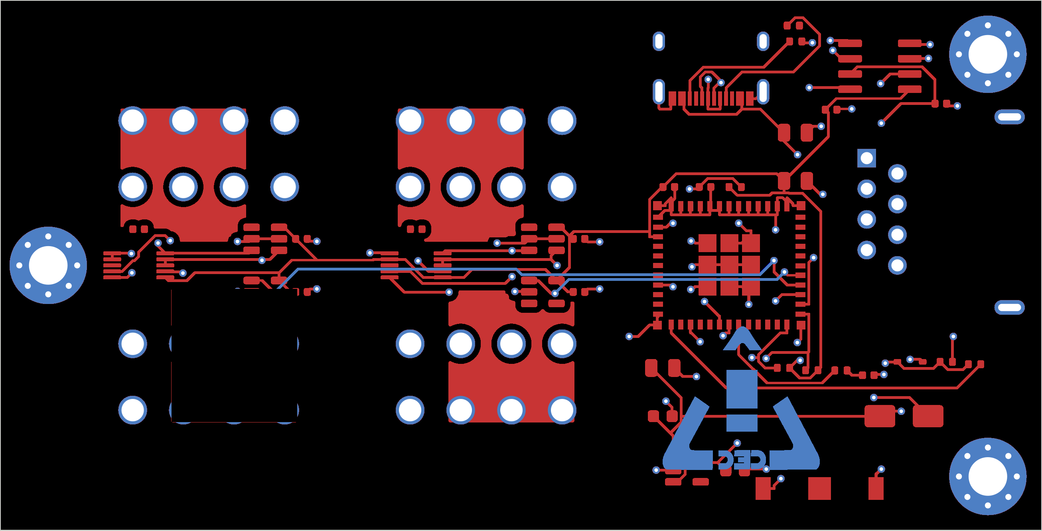
docs/det-inspection/incremental-samples/dropped_zone.png
