nathanfraske/CEC-Platform/docs/inloop-audit-2026-06-11/dashboard-board.png

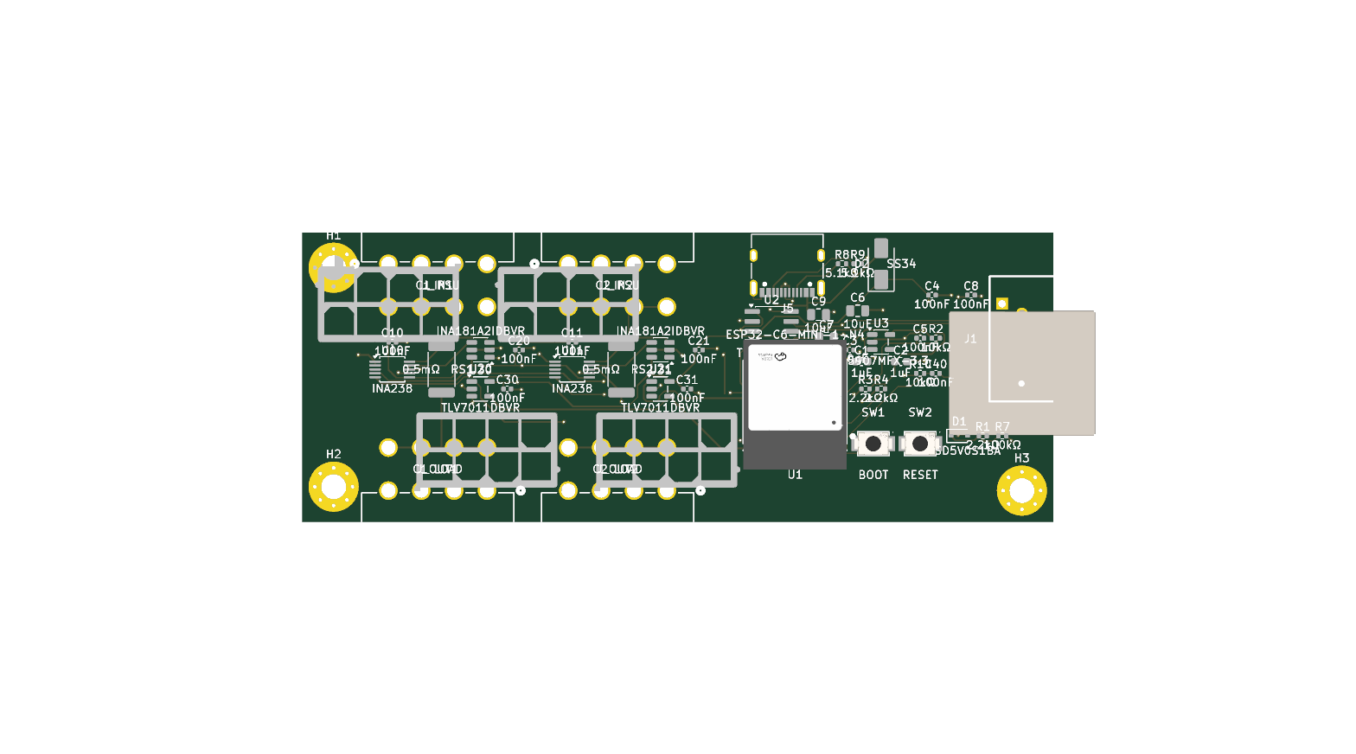
docs/inloop-audit-2026-06-11/dashboard-board.png
