nathanfraske/CEC-Platform/docs/standard-tier-review/thermal-maps/atx24-out-db-thermal.png

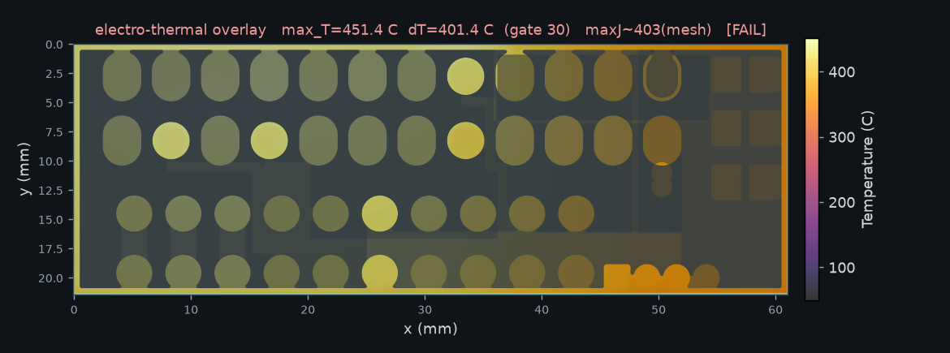
docs/standard-tier-review/thermal-maps/atx24-out-db-thermal.png
