nathanfraske/CEC-Platform/docs/standard-tier-review/thermal-maps/eps-out-db-thermal.png

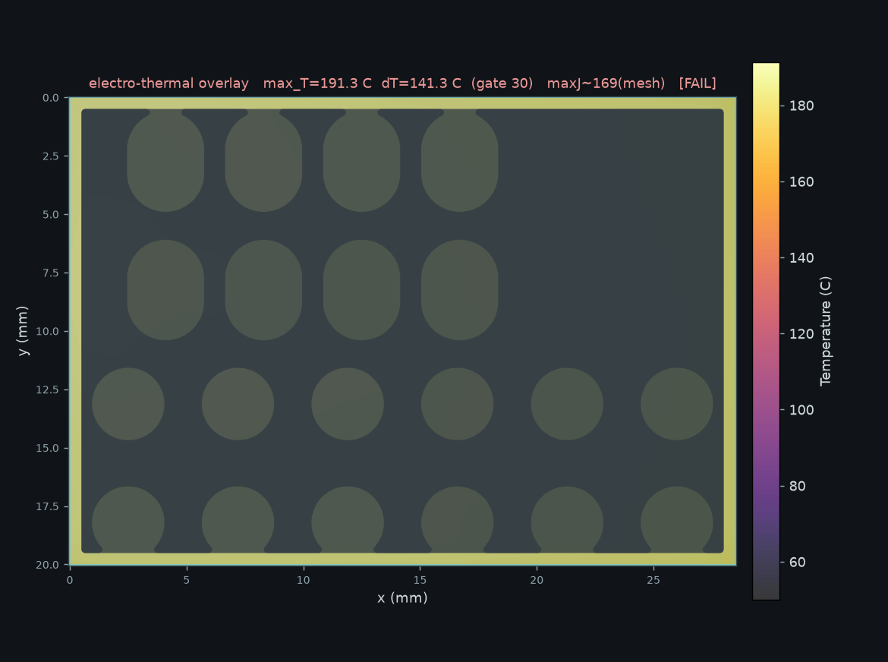
docs/standard-tier-review/thermal-maps/eps-out-db-thermal.png
