nathanfraske/CEC-Platform/docs/standard-tier-review/thermal-maps/pcie-out-db-thermal.png

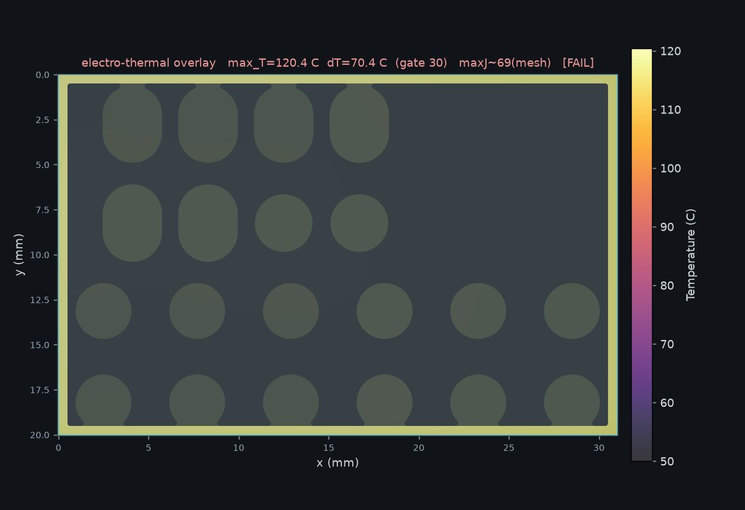
docs/standard-tier-review/thermal-maps/pcie-out-db-thermal.png
