nathanfraske/CEC-Platform/hubs/hub-standard/hub-standard-placement-plan.png

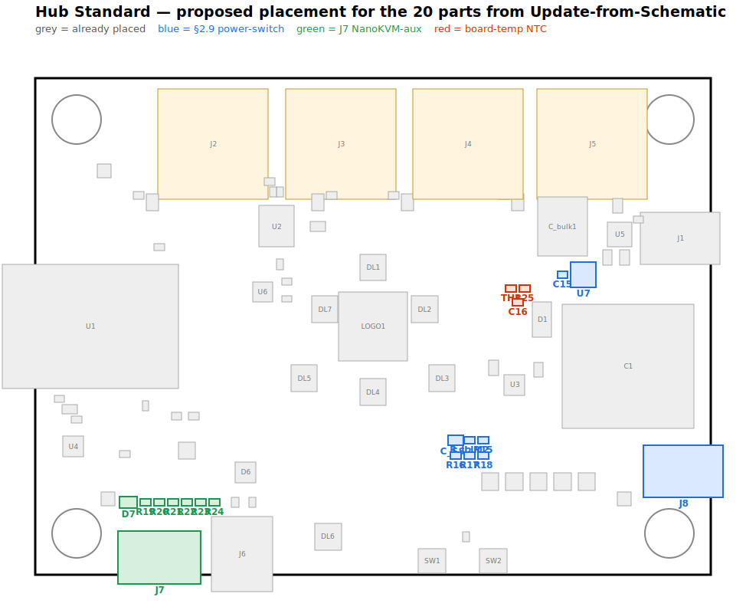
hubs/hub-standard/hub-standard-placement-plan.png
