nathanfraske/CEC-Platform/docs/enterprise-requirements/spec-sheets/bom-detailed/bom-a-compute.md

## BOM-A: Compute core — CEC ENT Hub (PolarFire SoC MPFS095TS-1FCVG484I)

| Ref-class | Qty | Value/Function | MPN | Mfr | Package | Unit@100q [date] | Datasheet URL | Notes |
|---|---|---|---|---|---|---|---|---|
| U1 | 1 | SoC — RISC-V MSS + fabric, S-suffix/Athena, industrial temp | MPFS095TS-1FCVG484I | Microchip | FCVG484 (19×19mm, 0.8mm, 484-ball BGA) | **$130–165 [RFQ]** (2026-07-02; DigiKey/Mouser/Octopart block scripted price-break reads — confirmed via [survey-1](../research/phase2/survey-1-polarfire-sizing.md)'s same-day T-part pull, $189.49 qty1/$153.96 qty25, +modest S-premium per survey; microchipusa.com confirms "Request a Quote," 18-wk lead) | [DS00004248](https://ww1.microchip.com/downloads/aemDocuments/documents/FPGA/ProductDocuments/DataSheets/PolarFire-SoC-Datasheet-DS00004248.pdf) | all SKUs |
| U2 | 1 | QSPI NOR boot flash, 128Mb, A/B image + tamper-log region | W25Q128JVSIQ | Winbond | SOIC-8-208mil | **$2.04** (LCSC C97521, verified live 2026-07-02; JLCPCB cross-check matches) | [Winbond W25Q128JV](https://www.winbond.com/resource-files/W25Q128JV%20RevH%2003102021%20Plus.pdf) | all SKUs. Real price is 2–4× the spec-sheet's $0.5–1 placeholder — flag for D-ENT-3 |
| U-EMMC | 1 | Bulk storage, eMMC 5.1, FBGA-153, density set per hub SKU (8/32/64GB on the SAME land — `cec-ent-mcu:eMMC_5.1_FBGA153_Generic`, 11.5×13mm 0.5mm-pitch, already vendored + ball-verified) | **PROPOSED, pending owner nod (2026-07-16): FORESEE (Longsys) FEMDNN family** — 8GB `FEMDNN008G-A3A55`, 32GB `FEMDNN032G-A3A55`, 64GB `FEMDNN064G-A3A56` | Longsys (FORESEE brand) | FBGA-153, 11.5×13mm (exact land match) | **[RFQ — see notes]** LCSC C5374780 / C5117593 / C5117595 respectively; all three show "Not available now" (zero live stock) at LCSC as of 2026-07-16 — real listings, real datasheets, thin/volatile spot stock, not a stale-cache artifact (independently reproduced across every eMMC candidate researched this pass) | [FEMDNN032G-A3A55](https://www.lcsc.com/datasheet/C5117593.pdf) / [FEMDNN064G-A3A56 datasheet, LCSC-hosted] | **PROPOSED pending owner sign-off — see `docs/owner-queue.md` 2026-07-16b entry for the full second-source/reference comparison (Micron MTFC*BCAQTC-IT via DigiKey; Zetta ZDEMMC*GA reference-only).** 32GB/64GB confirmed **-40°C~+85°C true industrial** at LCSC; the 8GB code's exact temp grade came back inconsistent across two independent lookups (-25°C~+85°C in one source read vs the -40°C family expectation) — confirm before lock. LCSC-native (owner-preferred route); all three are the SAME FBGA-153/11.5×13mm package as the vendored generic land, so no new footprint/symbol work is needed once an MPN is picked — this is a BOM-property pass only, same pattern as the OQ-11 shunt selection. |
| U3 | 1 | Buck, VDD core = **1.0V** (adjustable, FB divider) | MPM3833CGRH-Z | Monolithic Power Systems | QFN-18 (2.5×3.5mm) | **$2.08** (LCSC/JLCPCB C6306422, live 2026-07-02) | [MPM3833C](https://www.mouser.com/datasheet/2/277/MPM3833CGRH_Z-2946622.pdf) | all SKUs. 3A module; adjustable 0.6V+, integrated inductor+FETs, "typical apps: FPGA/ASIC/DSP power" per datasheet. **Core-current headroom risk flagged** — see current-budget note |
| U4 | 1 | Buck, VDD18 = 1.8V (+ shared VDDIx HSIO banks 0/8) | MPM3833CGRH-Z | Monolithic Power Systems | QFN-18 | $2.08 (same as U3) | (same) | all SKUs. Reuses U3's MPN, different FB set-point — per DS60001681H, VDD18 doubles as "programming and HSIO auxiliary supply," so HSIO VDDIx (1.8V option) shares this rail by design |
| U5 | 1 | Buck, VDD25 = 2.5V (corner PLLs + eNVM/PNVM) | MPM3833CGRH-Z | Monolithic Power Systems | QFN-18 | $2.08 | (same) | all SKUs |
| U6 | 1 | Buck, shared 3.3V I/O domain: VDDI3(JTAG)+VDDI5(SGMII bank)+VDDI2/VDDI4(MSS periph)+VDDIx(GPIO banks 1/7/9)+VDDAUXx+VDD_XCVR_CLK | MPM3833CGRH-Z | Monolithic Power Systems | QFN-18 | $2.08 | (same) | all SKUs. **Single regulator by datasheet rule**, not just convenience: "If VDDI and VDDAUX must be configured to the same voltage of 2.5V or 3.3V, ensure both are supplied from the same regulator" (DS60001681H §1.1) |
| U7 | 1 | Quiet LDO, VDDA = 1.0V ("XCVR Tx/Rx Lanes Supply") | TPS7A2010PDBVR *(decivolt-suffix convention)* | Texas Instruments | SOT-23-5 | **[unverified — price/exact stock]**; family confirmed real: TPS7A2018PDBVR (LCSC C963430, 1.8V) and TPS7A2050PDBVR (LCSC C2864504, 5.0V) both live-verified 2026-07-02, 0.8–5.5V range per datasheet | [TPS7A20](https://www.ti.com/lit/ds/symlink/tps7a20.pdf) | **NET only** (DNP on AIR — no transceiver). Datasheet mandates linear reg here: "quiet supply critical to meeting all datasheet specifications... use a linear regulator — no exceptions" (Note 1, DS60001681H Table 1-1) |
| U8 | 1 | Quiet LDO, VDDA25 = 2.5V ("XCVR PLL Supply") | TPS7A2025xDBVR *(family/convention as U7)* | Texas Instruments | SOT-23-5 | [unverified — same caveat as U7] | [TPS7A20](https://www.ti.com/lit/ds/symlink/tps7a20.pdf) | NET only. Treated as quiet/linear out of caution (PLL analog rail) even though the datasheet's explicit "no exceptions" language names VDDA, not VDDA25 by name |
| U9 | 1 | Supervisor — sequencing gate + POR, trip ≈3.0–3.3V, monitors U6 (3.3V domain) | TPS3839K33DBZR | Texas Instruments | SOT-23-3 | **~$0.15–0.30 [est.]** — reused platform part, LCSC C96333 (already sourced on hub-standard) | [TPS3839](https://www.ti.com/lit/ds/symlink/tps3839.pdf) | all SKUs. RESET output gates EN on U3/U4/U5/U7/U8 and drives DEVRST_N — see sequencing note |
| U10 | 1 | Supervisor — brownout detect, trip 0.9V, monitors U3 (VDD core) | TPS3839A09DBZR | Texas Instruments | SOT-23-3 | ~$0.15–0.30 [est.] | [TPS3839](https://www.ti.com/lit/ds/symlink/tps3839.pdf) | all SKUs. Satisfies §1.13 "use external brownout detection circuits" mandate for VDD |
| U11 | 1 | Supervisor — brownout detect, trip ≈1.7V, monitors U4 (VDD18) | TPS3839-family [exact threshold-suffix TBD] | Texas Instruments | SOT-23-3 | ~$0.15–0.30 [est.] | [TPS3839](https://www.ti.com/lit/ds/symlink/tps3839.pdf) | all SKUs. §1.13 names VDD18 explicitly |
| U12 | 1 | Supervisor — brownout detect, trip ≈2.3V, monitors U5 (VDD25) | TPS3839-family [exact threshold-suffix TBD] | Texas Instruments | SOT-23-3 | ~$0.15–0.30 [est.] | [TPS3839](https://www.ti.com/lit/ds/symlink/tps3839.pdf) | all SKUs. §1.13 names VDD25 explicitly |
| Y1 | 1 | Oscillator, 50MHz single-ended, MSS_REF_CLK | ECS-3225MV-500-CN-TR | ECS Inc. | SMD3225-4P | **$1.18** (LCSC C405974, live 2026-07-02) | [ECS-3225MV](https://www.lcsc.com/product-detail/SMD-Oscillators-XO_ECS-ECS-3225MV-500-CN-TR_C405974.html) | all SKUs. HCMOS 1.62–3.63V; frequency corroborated independently via Microchip Icicle Kit reference design (deepwiki clock-tree analysis) — same 50MHz REF_CLK into the CCC/PLL |
| Y2 | 1 | Oscillator, 125MHz differential (LVDS/HCSL), MSS_REFCLK_IN_P/N (SGMII transceiver ref) | AX3DAF1-125.0000T3 | Abracon | SMD3225-6P | **~$2.87–7.57** (LCSC C17568982, live 2026-07-02 — **flagged out of stock**; real DigiKey-orderable alternate: AK3AAIGDDF1-125.0000T, ClearClock family, product ID 22114010) | [AX3D family](https://abracon.com/parametric/oscillators/AX3DCF1-125.0000T3) | **NET only** (DNP on AIR). Per DS60001681H §1.10.1.1: transceiver refclk accepts 20–400MHz, LVDS25/HCSL25 direct with no external termination (ODT internal) — 125MHz chosen as the SGMII-industry-standard reference (125MHz×10=1.25Gbps); XCVR_VREF (SSTL-only ref) therefore NOT required, tied off (see R-group below) |
| J1 | 1 | JTAG/FlashPro programming header, 2×5, 0.05"/1.27mm, THT | FTSH-105-01-L-DV-K | Samtec | 2×5 vertical THT | **$0.967** (LCSC C5155080, live 2026-07-02) | [Samtec FTSH-105](https://www.samtec.com/products/ftsh-105-01-l-dv-k) | all SKUs. Microchip's own DS60001681H Fig 1-6 reference design specifies this exact Samtec FTSH-105-01 family (guide shows tin-finish "-A"; gold-flash "-K" specified here, same footprint/pinout, LCSC-stocked) |
| C-JTAG | 2 | JTAG strap: TCK 10kΩ→VSS, TRSTB 1kΩ→VDDI3 | 0402WGF1002TCE (10k, reuse) / 0402WGF1001TCE (1k) | UNI-ROYAL | 0402 | 10k: **C25744** (reused platform part) / 1k: [~C25xxx, same series, unverified exact C#] | — | all SKUs. Per DS60001681H Table 1-13 |
| R-SPI | 2 | SPI-master boot-select strap: SPI_EN 4.7kΩ, IO_CFG_INTF 1kΩ (Fig 1-7 reference network) | generic 0402 1% | UNI-ROYAL/Yageo-class | 0402 | ~$0.005 ea | — | all SKUs. **Pull polarity for "master-mode + QSPI-quad enabled" not independently re-derived here** — confirm against DS60001681H Fig 1-7 + PolarFire Family Programming User Guide at schematic capture (see open items) |
| R-VREF | 1 | XCVR_VREF tie-off, 10kΩ→GND (unused — differential refclk chosen) | 0402WGF1002TCE (reuse) | UNI-ROYAL | 0402 | C25744 (reused) | — | all SKUs. Per DS60001681H Fig 1-2 "Unused Power Supply, Option 1" |
| R-FB | 8 | FB divider resistor pairs, one pair per U3–U6 buck (values per MPM3833C Vout formula) | generic 0402 0.1–1% | UNI-ROYAL/Yageo | 0402 | ~$0.01–0.03 ea | — | all SKUs. **Exact resistor values are a schematic-capture calculation** (Vout = 0.6V×(1+R1/R2) per MPM3833C application section), not asserted here |
| C-REG | 8 | Regulator in/out bulk caps, 2 per buck (U3–U6) | CL10A106MA8NRNC (10uF) | Samsung | 0603 | **C96446** (reused platform part) | — | all SKUs |
| C-LDO | 4 | Quiet-LDO in/out caps, 2 per LDO (U7–U8) | 1uF ceramic (reuse platform 1uF 0603) | Samsung | 0603 | C15849 (reused platform part) | — | NET only (with U7/U8) |
| C-1n | 4 | BGA decoupling, 1nF (VDD25) | GRM033R71C102KA01 | Murata | 0201 | ~$0.01–0.02 ea [est.] | [Murata GRM series](https://ww1.microchip.com/downloads/aemDocuments/documents/FPGA/ProductDocuments/UserGuides/PolarFire_SoC_FPGA_Board_Design_Guidelines_User_Guide_VB.pdf) | all SKUs. Real MPN per DS60001681H Table 1-8, sized for the 0.8mm-pitch land |
| C-4n7 | 2 | BGA decoupling, 4.7nF (VDDA) | GRM155R11H472KA01 | Murata | 0402 | ~$0.02 ea [est.] | (same guide) | NET only — VDDA-specific |
| C-22n | 2 | BGA decoupling, 22nF (VDD core) | GRM155R71C223KA01D | Murata | 0402 | ~$0.02 ea [est.] | (same guide) | all SKUs |
| C-10n | 10 | BGA decoupling, 10nF (VDD/VDD18/VDDA/VDD25/VDDAUX) | GRM033R71A103KA01 | Murata | 0201 | ~$0.01–0.02 ea [est.] | (same guide) | all SKUs (1 of the 11 in the source table belongs to Bank-6-DDR — moved to OPTIONAL block below) |
| C-47n | 5 | BGA decoupling, 47nF (VDD/VDDA25/VDDAUX) | GRM155R71C473KA01J | Murata | 0201/0402 | ~$0.02 ea [est.] | (same guide) | all SKUs |
| C-100n | 25 | BGA decoupling, 0.1uF (VDD/VDD18/VDDA/VDDA25/VDD25/VDDAUX/VDD_XCVR_CLK/VDDI3/Bank2/Bank4/Bank5) | GRM033C71C104KE14 | Murata | 0201 | ~$0.02 ea [est.] | (same guide) | all SKUs. 2 of the source table's 28 (SERDES_VREF) omitted — pin tied off, not driven; 1 (Bank6-DDR) moved to OPTIONAL |
| C-10u | 8 | BGA bulk decoupling, 10uF (VDD18/VDDA/VDDA25/VDD_XCVR_CLK/VDDI3/Bank2/Bank4/Bank5) | GRM21BR71A106KE51 | Murata | 0805 | ~$0.05–0.08 ea [est.] | (same guide) | all SKUs |
| C-47u | 7 | BGA bulk decoupling, 47uF (VDD18/VDDA/VDDA25/VDDAUX/GPIO×2/HSIO) | GRM31CR61A476KE15 | Murata | 1206 | ~$0.15–0.25 ea [est.] | (same guide) | all SKUs |
| C-330u | 2 | BGA bulk decoupling, 330uF tantalum (VDD core) | T495D337K010ATE150 | AVX/Kemet | 2917 | ~$0.30–0.60 ea [est.] | (same guide) | all SKUs |
| **— OPTIONAL — DDR block (LPDDR4, pending firmware LIM-vs-DDR confirm, spec-sheet open item) —** ||||||||
| U13 | 0–1 | LPDDR4 SDRAM, 4Gb, x32 | MT53E128M32D2DS-053 (WT:A or AAT:A grade) | Micron | 200-ball VFBGA/WFBGA (10×14.5mm) | **[RFQ, ~$5–9 est.]** — real, currently-orderable part (DigiKey product ID 10321268 confirms live catalog listing); exact 100q price not independently pulled this pass | [Micron MT53E part catalog](https://www.micron.com/products/dram/lpdram/part-catalog/mt53e128m32d2ds-053-aat) | **OPTIONAL.** 128M×32 = 4Gb, matches survey-1's 4–8Gb working range |
| U14 | 0–1 | Buck, VDDIO(Bank6)/DDR-VDD2/VDDQ = **1.1V** (LPDDR4-specific) | MPM3833CGRH-Z | MPS | QFN-18 | $2.08 (as U3–U6) | (same as U3) | **OPTIONAL.** Per DS60001681H Important-note: "VDDIO (MSS DDR Bank 6) can also be operated at 1.1V to support LPDDR4." DDR chip's own VDD1 (1.8V) reuses U4 (VDD18) — same net, standard DDR practice |
| R-ZQ | 0–1 | ZQ calibration resistor, 240Ω 1% | generic 240R 1% 0402 | Yageo-class | 0402 | ~$0.01 [est.] | — | OPTIONAL. Standard LPDDR4 ZQ value |
| C-DDR | 0–4 | Bank-6/DDR-specific BGA decoupling: 10nF×1, 0.1uF×1, 1uF×1, 47uF×1 | GRM033R71A103KA01 / GRM033C71C104KE14 / GRM155R70J105KA12J / GRM31CR61A476KE15 | Murata | 0201/0805-1206 | ~$0.10 total [est.] | (BDG guide) | OPTIONAL. Split out of the base decoupling field per DS60001681H Table 1-4, "Bank 6 MSS DDR" row |
| — | — | **VTT termination: NOT NEEDED.** LPDDR4 uses on-die termination (ODT) on the CA/DQ bus, unlike DDR3/DDR4's fly-by-terminated bus — no external VTT regulator (e.g. TPS51200-class) required. If a DDR4 part were chosen instead, add a VTT rail (VDDQ/2) + regulator here. | — | — | — | — | — | OPTIONAL — informational row, not a populated part |

### Sequencing note

Derived directly from Microchip's *PolarFire SoC FPGA Board Design Guidelines* (DS60001681H), §1.1 and §1.13 — **primary source, read directly, not summarized secondhand**:

1. **Hard rule (POR circuitry, no tolerance):** VDD, VDD18, and VDD25 must each ramp *monotonically* from 0V to their minimum operating voltage — "any deviation... will compromise device functionality." This is a soft-start-quality requirement on each converter individually, not a relative-order requirement between them — satisfied by using standard COT/CCM bucks with clean soft-start (MPM3833C qualifies).
2. **VDDI3 (JTAG bank)** must be powered *before or at the same time as* VDD/VDD18/VDD25.
3. **VDDI5 (SGMII bank + MSS dedicated clocks)** must be powered *before or along with* VDD, and must reach its datasheet minimum *before* VDD reaches functional level *and* before MSS executes its first instruction (T_CPU). **This is why VDDI5 is populated on every SKU, not just NET** — it gates basic MSS boot, independent of whether the SGMII transceiver itself is used.
4. Since VDDI3 and VDDI5 are both folded into U6 (shared 3.3V domain per the datasheet's own VDDI/VDDAUX same-regulator rule), a *single* supervisor on U6's output (U9, TPS3839K33) satisfies both (2) and (3) simultaneously by gating EN on U3/U4/U5/U7/U8 — this is a PG-daisy-chain built from small supervisor ICs, not a dedicated multi-channel sequencer.
5. **Chosen approach: PG-daisy-chain via cascaded TPS3839-family supervisors, not a dedicated sequencer IC** (e.g. UCD90xxx-class). Justification: the datasheet's actual requirement is "before or at the same time" plus per-rail monotonicity — a loose ordering constraint, not a tight ms-level skew spec. A big multi-channel sequencer would be real overkill for a 2-tier gate; TPS3839 is already a sourced platform part (hub-standard, C96333) and does triple duty here: sequencing gate (U9), §1.13-mandated external brownout detection on VDD/VDD18/VDD25 (U9/U10/U11/U12 — §1.13: "for brownout detection on any PolarFire supply (including VDD, VDD18, and VDD25), use external brownout detection circuits"), and DEVRST_N drive (U9's RESET output, satisfying the datasheet's "drive DEVRST_N with a POR chip" option — chosen over the passive "1kΩ-to-VDDI3" alternative because it's an active, real POR rather than a static pull-up).
6. XCVR_VREF is not required (differential 125MHz refclk chosen) and I/O calibration gating on VDDA+XCVR_VREF is therefore moot on this design.

### Per-rail current budget (estimate — no Power Estimator run yet; survey-1's own flagged gap)

| Rail | Nominal V | Est. current | Basis |
|---|---|---|---|
| VDD (core) | 1.0V | **1.5–3.0A [est.]** | survey-1's whole-device 3–10W estimate, core/fabric assumed dominant share; **near U3's 3A ceiling — flag headroom risk, see open items** |
| VDD18 | 1.8V | 100–300mA [est.] | programming + HSIO aux, low-current housekeeping |
| VDD25 | 2.5V | 100–300mA [est.] | corner PLLs + eNVM/PNVM, low-current |
| 3.3V domain (VDDI3/5/2/4, GPIO banks, VDDAUX, VDD_XCVR_CLK) | 3.3V | 200–500mA [est.] | scales with active GPIO/JTAG/SGMII-I/O toggling; widest uncertainty band |
| VDDA (XCVR lanes) | 1.0V | <150mA [est.] | 1 SGMII lane active, NET only |
| VDDA25 (XCVR PLL) | 2.5V | <50mA [est.] | PLL bias, NET only |
| VDDIO(Bank6)/DDR VDD2/VDDQ (optional) | 1.1V | 200–600mA [est.] | x32 LPDDR4 I/O, DDR fitted only |

**All figures above are estimates pending an actual Microchip Power Estimator run** (survey-1 flagged this as unrun in this environment) — do not treat as a datasheet number.

### Total subsystem cost roll-up (100q, 2026-07-02 pricing where live, RFQ/est. elsewhere)

| Configuration | Estimate |
|---|---|
| **ENT-NET, no DDR** (SGMII populated: U7/U8/Y2 fitted) | **≈ $150–195** |
| **ENT-AIR, no DDR** (U7/U8/Y2 DNP — board pads present, one-PCB-many-SKUs principle) | **≈ $145–186** |
| **+ DDR block** (either SKU, if firmware confirms DDR-fitted over LIM-only) | **+ $7–11** |

This lands within (and cross-validates) the existing `hub-ent-spec-sheet.md` §3.A working baseline of "≈ $145–180 (no DDR)" — a useful independent sanity check between the top-down spec-sheet estimate and this bottom-up detailed build. The one material correction: **the boot flash's real 2026-07-02 price ($2.04, live LCSC/JLCPCB) is 2–4× the spec sheet's placeholder ($0.5–1)** — small in absolute terms but worth fixing at the next spec-sheet pass.

### Open items

1. **SoC and DDR pricing are RFQ-only** — MPFS095TS-1FCVG484I and the LPDDR4 candidate both returned "request a quote" behavior at every distributor reachable from this environment (Mouser/DigiKey/Octopart blocked scripted price-break reads; microchipdirect/microchipusa confirm quote-gating + an 18-week SoC lead time). Get real RFQs before D-ENT-3 lock.
2. **VDD core headroom** — a single MPM3833C (3A) is sized to the low end of the estimated core-current range with no Power Estimator run to confirm. If the real TSN-switch/data-plane fabric utilization pushes core current past ~2.5A, parallel a 2nd MPM3833C (MPS supports current-sharing) or step up to a higher-current sibling.
3. **Two TPS7A20-family decivolt SKUs (1.0V, 2.5V) and two TPS3839 threshold codes (~1.8V, ~2.5V) are named by extrapolating a confirmed-real naming convention** (verified via the 1.8V and 5.0V TPS7A20 siblings, and the 3.3V/0.9V TPS3839 siblings, both live on LCSC) but their own exact LCSC stock/price was not independently pulled this pass — confirm at BOM finalization. If unavailable, both families offer adjustable variants as a fallback.
4. **125MHz differential oscillator (Y2) is flagged out of stock at its LCSC listing** — a real DigiKey-orderable alternate (Abracon AK3AAIGDDF1-125.0000T, ClearClock family) is named; re-verify stock/price before layout.
5. **SPI-master boot-mode strap polarity (SPI_EN/IO_CFG_INTF, R-SPI)** — I provisioned the real resistor footprints/values Microchip's Fig 1-7 reference design shows, but did not independently re-derive which pull direction selects "master mode, QSPI quad enabled" vs the figure's own default network. Confirm against DS60001681H Fig 1-7 + the *PolarFire Family Programming User Guide* at schematic capture — getting this backward affects whether the board boots.
6. **WP#/HOLD# on U2 (QSPI flash) are mode-dependent**: in true quad-SPI boot (this design's intent) they're driven as IO2/IO3 by the SoC's QSPI controller, not pulled up as static WP/HOLD — no pull-up resistors provisioned here for that reason; flag if firmware ends up using single/dual SPI instead of quad.
7. **Scope boundary, explicitly excluded from this BOM**: (a) AC-coupling caps on the SGMII differential pair itself (between U1 and the GbE PHY) — this sits at the SoC/PHY interconnect and more naturally belongs to subsystem B (PHY rails) or a connector-adjacent pass; flag for cross-subsystem reconciliation. (b) DETECT external ADC / rail-sense dividers — explicitly assigned to subsystem C per `hub-ent-variants-plan.md` §3 ("PolarFire has no native ADC... added to BOM-C open items"), not duplicated here.
8. **DDR fitted-vs-LIM-only is still an open firmware-team question** (`hub-ent-spec-sheet.md` open row #2) — this BOM keeps the DDR block cleanly separable (one buck, one chip, one resistor, four caps) so either answer is a population change, not a redesign.
9. Two research sub-agents dispatched for cross-verification did not return usable results in time (one hit an internal 32MB response-size limit re-fetching the same guide I read directly; one got stuck mid-fan-out) — not a blocker, since the primary-source PDF read plus direct LCSC/DigiKey verification covered the same ground with higher confidence than a secondhand summary would have.
10. **U-EMMC (eMMC 5.1 storage, added 2026-07-16) is a PROPOSED pick, not yet owner-ratified** — see `docs/owner-queue.md`'s 2026-07-16b entry for the full comparison (FORESEE primary / Micron second-source / Zetta reference-only) and the temp-grade discrepancy on the 8GB code that needs closing before lock. This row's price is left as "[RFQ — see notes]" rather than a number to avoid double-counting against the master BOM's own existing "Storage — eMMC" line (`hub-ent-bom-detailed.md` §2, $5–9 at 8GB / $9–16 at 32–64GB, REQ-108/109) — reconcile the two into one number at the next master-BOM consolidation pass rather than here.

### Sources

- [PolarFire SoC FPGA Board Design Guidelines User Guide, DS60001681H](https://ww1.microchip.com/downloads/aemDocuments/documents/FPGA/ProductDocuments/UserGuides/PolarFire_SoC_FPGA_Board_Design_Guidelines_User_Guide_VB.pdf) — primary source, read directly (rail table, sequencing, decoupling tables 1-4/1-8, JTAG/SPI strapping figures, XCVR refclk spec, brownout mandate)
- [PolarFire SoC Datasheet DS00004248](https://ww1.microchip.com/downloads/aemDocuments/documents/FPGA/ProductDocuments/DataSheets/PolarFire-SoC-Datasheet-DS00004248.pdf)
- [MPM3833C datasheet, Monolithic Power Systems](https://www.mouser.com/datasheet/2/277/MPM3833CGRH_Z-2946622.pdf)
- [TPS7A20 datasheet, TI](https://www.ti.com/lit/ds/symlink/tps7a20.pdf); [TPS3839 datasheet, TI](https://www.ti.com/lit/ds/symlink/tps3839.pdf)
- [Winbond W25Q128JV datasheet](https://www.winbond.com/resource-files/W25Q128JV%20RevH%2003102021%20Plus.pdf)
- LCSC live product pages (verified 2026-07-02): [W25Q128JVSIQ / C97521](https://www.lcsc.com/product-detail/C97521.html), [MPM3833CGRH-Z / C6306422](https://www.lcsc.com/product-detail/DC-DC-Power-Modules_Monolithic-Power-Systems-MPM3833CGRH-Z_C6306422.html), [FTSH-105-01-L-DV-K / C5155080](https://www.lcsc.com/product-detail/C5155080.html), [ECS-3225MV-500-CN-TR / C405974](https://www.lcsc.com/product-detail/SMD-Oscillators-XO_ECS-ECS-3225MV-500-CN-TR_C405974.html), [AX3DAF1-125.0000T3 / C17568982](https://www.lcsc.com/product-detail/C17568982.html), [TPS7A2018PDBVR / C963430](https://www.lcsc.com/product-image/C963430.html), [TPS7A2050PDBVR / C2864504](https://www.lcsc.com/product-detail/Voltage-Regulators-Linear-Low-Drop-Out-LDO-Regulators_Texas-Instruments-TPS7A2050PDBVR_C2864504.html)
- [Micron MT53E128M32D2DS-053 part catalog](https://www.micron.com/products/dram/lpdram/part-catalog/mt53e128m32d2ds-053-aat); [DigiKey listing](https://www.digikey.com/en/products/detail/micron-technology-inc/MT53E128M32D2DS-053-WT-A/10321268)
- [Icicle Kit clock-and-reset structure, DeepWiki](https://deepwiki.com/polarfire-soc/icicle-kit-reference-design/2.3-clock-and-reset-structure) — MSS 50MHz REF_CLK corroboration
- U-EMMC candidate research (2026-07-16, live LCSC/DigiKey checks, all direct product-page fetches unless noted): FORESEE (Longsys) [FEMDNN032G-A3A55 / C5117593](https://www.lcsc.com/product-detail/C5117593.html), [FEMDNN064G-A3A56 / C5117595](https://www.lcsc.com/product-detail/eMMC_FORESEE-FEMDNN064G-A3A56_C5117595.html) (both -40~+85°C confirmed live), [FEMDNN008G-A3A55 / C5374780](https://www.lcsc.com/product-detail/eMMC_FORESEE-FEMDNN008G-A3A55_C5374780.html) (temp grade unresolved — see note); Micron industrial eMMC family datasheets ([8-128GB v5.1](https://mm.digikey.com/Volume0/opasdata/d220001/medias/docus/8719/emmc-industrial-8-128gb-v5-1%20(2).pdf), [32/64/128/256GB](https://mm.digikey.com/Volume0/opasdata/d220001/medias/docus/8606/industrial-emmc-32-64-128-256gb.pdf)) and DigiKey listings [MTFC64GBCAQTC-IT / DK 21572466](https://www.digikey.com/en/products/detail/micron-technology-inc/MTFC64GBCAQTC-IT/21572466) (Active, -40~+85°C, $82.56@25q, 0 stock), [MTFC32GAZAQHD-IT / DK 15779772](https://www.digikey.com/en/products/detail/micron-technology-inc/MTFC32GAZAQHD-IT/15779772) (0 stock); Kingston [EMMC08G-ML36-01B00 / DK 15776056](https://www.digikey.com/en/products/detail/kingston-technology/EMMC08G-ML36-01B00/15776056) and [-02F00 / DK 19188029](https://www.digikey.com/en/products/detail/kingston-technology/EMMC08G-ML36-02F00/19188029) (both confirmed OBSOLETE/discontinued — the same part the generic land's own Description property cites as a ball-verification source, so the land-fit provenance stands even though the exact P/N is dead); Zetta [ZDEMMC08GA / C3029818](https://www.lcsc.com/product-detail/eMMC_Zetta-ZDEMMC08GA_C3029818.html) and [ZDEMMC16GA / C7501401](https://www.lcsc.com/product-detail/C7501401.html) (both 0 live stock, -25~+85°C only — reference-only, not recommended for new sourcing).
- Repo-internal: `docs/enterprise-requirements/spec-sheets/hub-ent-spec-sheet.md` §3.A; `docs/enterprise-requirements/spec-sheets/hub-ent-variants-plan.md`; `docs/enterprise-requirements/research/phase2/survey-1-polarfire-sizing.md`; existing platform BOMs (`hubs/hub-standard/bom/bom.csv`) for reused LCSC parts (LP5907/TPS3839/10k/100nF/10uF/1uF conventions)

---

**Files/context relevant to this task** (all read, none written — this task's output is the message above per the brief):
- `/home/user/CEC-Platform/docs/enterprise-requirements/spec-sheets/hub-ent-spec-sheet.md` (§3.A baseline this BOM supersedes/details)
- `/home/user/CEC-Platform/docs/enterprise-requirements/spec-sheets/hub-ent-variants-plan.md` (subsystem-boundary authority: BOM-A = SoC + its own regulator set, explicitly excludes DETECT-ADC/BOM-C and PHY rails/BOM-B)
- `/home/user/CEC-Platform/docs/enterprise-requirements/research/phase2/survey-1-polarfire-sizing.md` (PolarFire sizing/costing grounding)
- Primary Microchip PDF fetched and read directly this session: `PolarFire_SoC_FPGA_Board_Design_Guidelines_User_Guide_VB.pdf` (DS60001681H) — saved locally at `/root/.claude/projects/-home-user-CEC-Platform/6f8ace32-71c9-52f7-b750-d450901c26ac/tool-results/webfetch-1783010486260-e7vqs9.pdf`
