nathanfraske/CEC-Platform/beta/output-daughterboards/atx24-out-db/bom/atx24-out-db-board-BOM-jlcpcb.csv

Comment | Designator | Footprint | LCSC Part #
ATX24 OUT FIELD | J1 | cec-Connector_Generic:ATX24_Daughterboard_Field_P4.20mm
TSW-102-16-G-D-RA | J20 | cec-Connector_PinHeader_2.54mm:Samtec_TSW-102-16-G-D-RA_2x02_P2.54mm_Horizontal
