nathanfraske/CEC-Platform/beta/output-daughterboards/atx24-out-db/bom/bom.csv

Reference | Qty | Value | Footprint | MPN | Manufacturer | LCSC | LC_Stock | Chosen_Distributor | Datasheet | Validated | DNP | Notes
J1 | 1 | ATX24 OUT FIELD | ATX24_Daughterboard_Field_P4.20mm |  | CEC (in-house) |  |  |  |  |  |  | Bare THT solder field, no housing/shroud -- CEC-authored footprint (lib/vendor/Connector_Generic.pretty), NOT a stocked/purchased part. Populate with a hand-soldered pigtail (default), OR (bring-up samples only, provenance-UNVERIFIED, OQ-88) a MODDIY-class vertical female header if the pitch/hole pattern proves compatible on the sample fit check -- no MODDIY footprint exists in this library and none is placed here.
J20 | 1 | TSW-102-16-G-D-RA | Samtec_TSW-102-16-G-D-RA_2x02_P2.54mm_Horizontal | TSW-102-16-G-D-RA | Samtec |  |  |  | https://suddendocs.samtec.com/catalog_english/tsw_th.pdf |  |  | Mates SSQ-102-03-G-D; 1=-12V, 2=PS_ON#, 3=PWR_OK, 4=GND. First-article mated-transform and engagement check required.
