nathanfraske/CEC-Platform/beta/output-daughterboards/eps-out-db/bom/eps-out-db-board-BOM-jlcpcb.csv

Comment | Designator | Footprint | LCSC Part #
EPS8 OUT FIELD | J1 | cec-Connector_Generic:EPS8_Daughterboard_Field_P4.20mm
