nathanfraske/CEC-Platform/beta/output-daughterboards/pcie-out-db/bom/pcie-out-db-board-BOM-jlcpcb.csv

Comment | Designator | Footprint | LCSC Part #
PCIE8 OUT FIELD | J1 | cec-Connector_Generic:PCIe8_Daughterboard_Field_P4.20mm
