nathanfraske/CEC-Platform/beta/smoke-tester/brick/bom/bom.csv

Reference | Qty | Value | Footprint | MPN | Manufacturer | LCSC | LC_Stock | Chosen_Distributor | Datasheet | Validated | DNP | Notes
"RV1..RV5" | 5 | MOV 14D220K (22V, 14mm disc) — UNIFORM all ways | Disc_D14 P7.5 | VDR-14D220K | generic | C6793760 | 800 | LCSC | varistor PDF fetch pending — FOLLOWUPS | jlcsearch 2026-07-25 |  | STOCK-WATCH (800); same-family alternates C43370767/C136782/C362865; bidirectional = free reverse clamp
"GT1..GT5" | 5 | GDT 90V THT (2R090T) | D5.5xL6 THT | 2R090TA-5 | generic | C48642402 | 2855 | LCSC | GDT PDF fetch pending — FOLLOWUPS | jlcsearch 2026-07-25 |  | ◆ visible mains crowbar on the 5 CORE ways only (VE-1, 2026-07-25: AUX ways = MOV+fuse coordination, the pre-#14 signed-safe architecture; -$0.85/brick; AUX ways since DESCOPED entirely 2026-07-25); GLASS-BODY CHECK at sample; SMD 1812-090 C693446 = electrical fallback (no show)
"RW1..RW5" | 5 | 1R 1W KNP flameproof WW | Axial D4.6 | KNP100JR-73-1R | Yageo | C1741442 | 640 | LCSC |  | jlcsearch 2026-07-25 |  | witness in series w/ each clamp leg — opens w/ designed puff + disconnects spent MOV/GDT; FKN fusible sibling preferred if sourced (arc bench proves either)
"RW_H,RW_D" | 2 | 33R 2W KNP-class flameproof | Axial | KNP200-class 33R | Yageo-class |  |  | same family — bind at capture |  |  |  | harvest-path protection x2: RW_H = store leg (common node -> store) · RW_D = instant-on domain leg (common node -> domain rail | 2026-07-25); both sacrificial
J_B1 | 1 | 2x8 0.1in header, keyed | THT 2x8 |  | generic |  |  | JLC basic — bind at capture |  |  |  | mates J_BRICK socket on MAIN; 5 ways + 5 returns + harvest node in + store/domain legs out + 2 key/spare
PCB_B | 1 | brick PCB 2-layer | n/a |  | JLCPCB |  |  | jlcpcb (panel w/ MAIN) |  |  |  | date-flag silk; keyed outline
