nathanfraske/CEC-Platform/beta/smoke-tester/faceplate/README.md

# Smoke Tester — FACEPLATE (sub-board, bare FR4)

Zero copper in the fault path; no connector; no BOM (bare board — the one candidate
part, jewel lenses for the neons/flicker tube, rides the case/consigned list). Apertures
for: 8 ATO holders, 24 way lamps, 2 neon jewels, ◆ flicker-tube jewel, ◆ LAMP TEST/SHOW
button, meter cutout, ARM missile cover, TEST/MIN-LOAD switches, SW_SEL rotary. Silk =
verdict truth-table + coroner's map + QR (reorder page). Panelized with MAIN; own
trivial KiCad project at Phase B for the outline/apertures/silk.
