nathanfraske/CEC-Platform/build/polyfuse-splice-verification.txt

Per-port RJ45-VCC polyfuse splice — verification evidence
hub-standard-rev2.kicad_sch (owner ruling 2026-07-15)
Generated by: scripts/splice_hub_rev2_polyfuse.py
kicad-cli 10.0.3

======================================================================
PART
======================================================================
0805 PTC resettable fuse, 500mA hold, 6V rated (meets the >=6V floor).
  MPN:            SMD0805-050-6
  LCSC:           C46640983
  Manufacturer:   generic (JLC catalog listing; unbranded/OEM part number)
  Stock (2026-07-15, jlcsearch.tscircuit.com): 47,440
  Source query:   https://jlcsearch.tscircuit.com/components/list.json?search=SMD0805-050-6
Symbol:     cec-vendor:R_Small (2-pin passive, already present in the file's
            lib_symbols — reused per the brief)
Footprint:  cec-Resistor_SMD:R_0805_2012Metric
  NOTE (deviation from brief): this footprint did NOT already exist in
  lib/vendor/Resistor_SMD.pretty (only 0402/2512 were vendored). Vendored it
  in this change from the local KiCad 10.0.3 install's official
  Resistor_SMD.pretty (IPC-7351-nominal generic land), plus its 3D model,
  matching the repo's existing vendoring convention (project-relative model
  path, no machine-global reference):
    lib/vendor/Resistor_SMD.pretty/R_0805_2012Metric.kicad_mod   (new)
    lib/3dmodels/Resistor_SMD.3dshapes/R_0805_2012Metric.step    (new)
  Model path rewritten from the stock ${KICAD10_3DMODEL_DIR}/... to
  ${KIPRJMOD}/../../lib/3dmodels/Resistor_SMD.3dshapes/R_0805_2012Metric.step
  (same pattern as R_0402_1005Metric.kicad_mod).

======================================================================
SHEET COORDINATES USED
======================================================================
Region occupancy-checked EMPTY before use (no (at x y ...) coordinates found
in x440-520 / y230-300):
  F1  (452.12, 260.35)
  F2  (472.44, 260.35)
  F3  (492.76, 260.35)
  F4  (513.08, 260.35)
(20.32mm pitch, single row, grid-snapped to the 1.27mm quantum — unique stub
endpoints per part, per the merge-footgun warning in the brief.)

Existing RJ-45 pin-1 stub endpoints reused for the new /VCC_Pn labels
(unchanged coordinates — only the +5VSB power symbol at each point was
removed and replaced with a label):
  J2 pin1 stub end (546.10,  35.56) -> label /VCC_P1  (removed #PWR07)
  J3 pin1 stub end (546.10,  86.36) -> label /VCC_P2  (removed #PWR08)
  J4 pin1 stub end (546.10, 140.97) -> label /VCC_P3  (removed #PWR09)
  J5 pin1 stub end (546.10, 195.58) -> label /VCC_P4  (removed #PWR10)

New #PWR refs used for F1..F4's +5VSB pins: #PWR9101..#PWR9104 (verified
unused beforehand; the file's existing #PWR namespace tops out at #PWR01155
and #PWR9001-#PWR9009 from prior splices).

======================================================================
NETLIST DELTA (kicad-cli sch export netlist, before vs after)
======================================================================
Total nets: 94 -> 98 (+4, exactly the new /VCC_Pn nets)

net "+5VSB":
  LOST:   (J2,1) (J3,1) (J4,1) (J5,1)
  GAINED: (F1,2) (F2,2) (F3,2) (F4,2)
  (all other +5VSB members — C14.1 C15.1 C5.1 C_bulk1.1 D1.2 DL1.4 DL2.4
   DL3.4 DL4.4 DL5.4 DL6.4 DL7.4 J6.1 J6.2 J6.3 J6.4 J_KVM.1 R12.1 U2.3 U6.5
   U7.1 U7.8 — unchanged, byte-identical membership)

NEW net "/VCC_P1" = {(F1,1), (J2,1)}
NEW net "/VCC_P2" = {(F2,1), (J3,1)}
NEW net "/VCC_P3" = {(F3,1), (J4,1)}
NEW net "/VCC_P4" = {(F4,1), (J5,1)}

All other 93 pre-existing nets: byte-identical membership before vs after
(programmatically diffed — zero unexpected differences).

This is EXACTLY the specified delta: +5VSB loses the four jack pin-1 taps and
gains the four fuse pin-2 taps; four new /VCC_Pn nets each bridge one fuse's
pin1 to its jack's pin1; nothing else moved.

======================================================================
ERC DELTA (kicad-cli sch erc --format json)
======================================================================
                        before   after   delta
  lib_symbol_mismatch     75       79      +4   (F1-F4 "doesn't match copy in
                                                  library 'cec-vendor'" — same
                                                  documented-benign class as
                                                  every other generator-spliced
                                                  part in this file)
  endpoint_off_grid        5        5       0
  unconnected_wire_endpoint 2       2       0
  no_connect_connected      1       1       0
  pin_to_pin (Unspecified)  13      13       0
  footprint_link_issues     0       0*      0
  ---------------------------------------------
  TOTAL                    96      100      +4
  severity: warning        96      100      +4
  severity: error           0        0       0

* footprint_link_issues transiently went 0 -> 4 ("Footprint 'R_0805_2012Metric'
  not found in library 'cec-Resistor_SMD'") until the footprint was vendored
  (see PART section above); after vendoring it is back to 0.

Every one of the 96 baseline warnings reproduces byte-identical (same type +
description + item set) in the after-run; the only additions are the four
expected benign lib_symbol_mismatch entries on F1-F4. Error count: 0 -> 0
(unchanged, does not increase).

======================================================================
RESULT: PASS — change verified, not committed.
======================================================================
