nathanfraske/CEC-Platform/testers/tester-standard/pin-audit-review-2026-07-16.txt

# cec_sym_audit --fix review for lib/cec-tester.kicad_sym
# 9 high-confidence change(s) (7 at the Phase A promotion pass + 2 more when
# 74HC165D,653 was added during 03-mcu capture, see the addendum below)

CH224K: pin 1 'VDD': unspecified -> power_in  (VDD: supply-rail pin (VDD family))
CH224K: pin 4 'DP': unspecified -> bidirectional  (BUS: USB/differential data pin)
CH224K: pin 5 'DM': unspecified -> bidirectional  (BUS: USB/differential data pin)
CH224K: pin 11 'GND': unspecified -> power_in  (GND: ground-return pin (GND family))
TPS54331DR: pin 3 'EN': unspecified -> input  (EN: enable/control pin (EN/ENABLE))
74HC595D,118: pin 8 'GND': unspecified -> power_in  (GND: ground-return pin (GND family))
74HC595D,118: pin 16 'VCC': unspecified -> power_in  (VDD: supply-rail pin (VCC/VBAT/VPP family))
74HC165D,653: pin 8 'GND': unspecified -> power_in  (GND: ground-return pin (GND family))
74HC165D,653: pin 16 'VCC': unspecified -> power_in  (VDD: supply-rail pin (VCC/VBAT/VPP family))
MM74HC273WM: pin 10 'GND': unspecified -> power_in  (GND: ground-return pin (GND family))
MM74HC273WM: pin 20 'VCC': unspecified -> power_in  (VDD: supply-rail pin (VCC/VBAT/VPP family))
CD4051BM96: pin 8 'VSS': unspecified -> power_in  (GND: ground-return pin (VSS family))
CD4051BM96: pin 16 'VDD': unspecified -> power_in  (VDD: supply-rail pin (VDD family))

## ADDENDUM 2 (orchestrator safety check-in, before 03/06 close): TWO more
## parts added, MM74HC273WM (LCSC C906662, octal D-FF w/ async CLEAR,
## SOIC-20) and CD4051BM96 (LCSC C21379, 8-channel analog mux, SOIC-16).
## REASON: the orchestrator's safety review of the shift-register-expander
## plan (addendum 1, above) surfaced two real gaps, both now fixed in the
## design (see 03-mcu.kicad_sch / 06a-06c's own notes for the as-drawn
## detail):
## (1) TRIP TIMESTAMPING: a trip signal that ONLY lives behind the polled
##     74HC165 chain degrades a promised us-class stamp to poll cadence.
##     Fix: all 12 trip-comparator outputs (4 loop + 5 bank + 3 SCP) feed a
##     diode-OR "TRIP_ANY" node (pull-down default) landing on a DIRECT MCU
##     GPIO interrupt AND the shared CLOCK input of 2x MM74HC273 (12 of 16
##     D-inputs used, one per trip signal, D tied logic-high so the trip
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
