nathanfraske/CEC-Platform/docs/fullstack-run-2026-06-11-validation/vision/pour-r1-modelfree.png

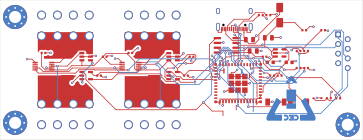
docs/fullstack-run-2026-06-11-validation/vision/pour-r1-modelfree.png
