nathanfraske/CEC-Platform/docs/fullstack-run-2026-06-11-validation/zone-progression.png

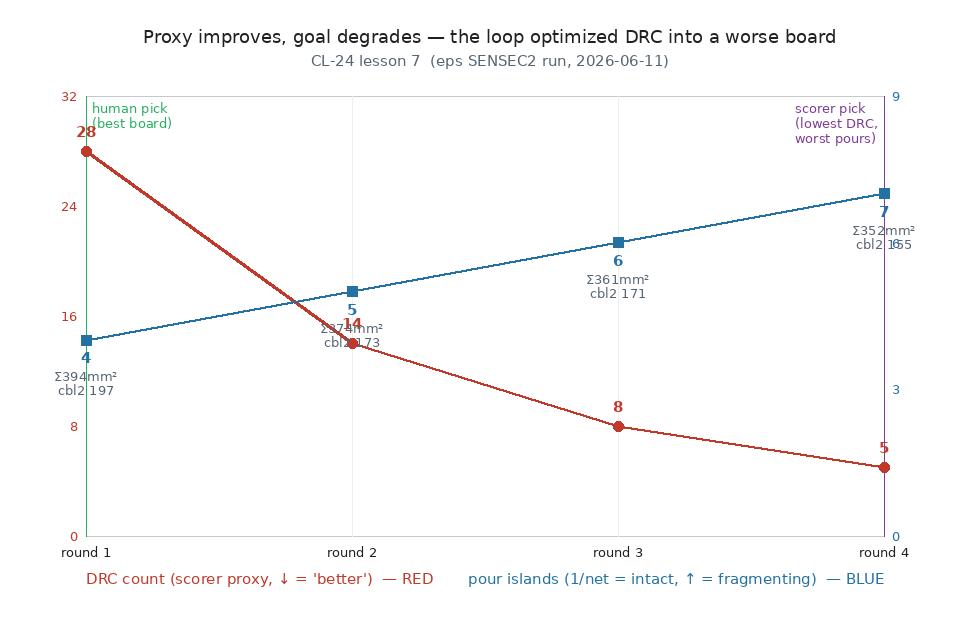
docs/fullstack-run-2026-06-11-validation/zone-progression.png
