nathanfraske/CEC-Platform/docs/enterprise-requirements/board-program/pin-audit/cec-ent-net-fix-review-2026-07-03.txt

# cec_sym_audit --fix review for lib/cec-ent-net.kicad_sym
# 17 high-confidence change(s)

DP83869HMRGZR: pin 3 'VDDA2P5': unspecified -> power_in  (VDD: supply-rail pin (VDD family))
DP83869HMRGZR: pin 6 'VDD1P1': unspecified -> power_in  (VDD: supply-rail pin (VDD family))
DP83869HMRGZR: pin 9 'VDDA2P5': unspecified -> power_in  (VDD: supply-rail pin (VDD family))
DP83869HMRGZR: pin 13 'VDDA1P8_1': unspecified -> power_in  (VDD: supply-rail pin (VDD family))
DP83869HMRGZR: pin 18 'VDDIO': unspecified -> power_in  (VDD: supply-rail pin (VDD family))
DP83869HMRGZR: pin 30 'VDDIO': unspecified -> power_in  (VDD: supply-rail pin (VDD family))
DP83869HMRGZR: pin 31 'VDD1P1': unspecified -> power_in  (VDD: supply-rail pin (VDD family))
DP83869HMRGZR: pin 39 'VDD1P1': unspecified -> power_in  (VDD: supply-rail pin (VDD family))
DP83869HMRGZR: pin 41 'MDIO': unspecified -> bidirectional  (BUS: MDIO management-bus pin)
DP83869HMRGZR: pin 43 'RESET_N': unspecified -> input  (RST: reset pin (RST/nRST/DEVRST) -- verify if this part can itself drive a reset OUTPUT to other devices)
DP83869HMRGZR: pin 48 'VDDA1P8_2': unspecified -> power_in  (VDD: supply-rail pin (VDD family))
RClamp0524PATCT: pin 3 'GND': unspecified -> power_in  (GND: ground-return pin (GND family))
RClamp0524PATCT: pin 6 'NC': unspecified -> no_connect  (NC: not-connected pin (NC))
RClamp0524PATCT: pin 7 'NC': unspecified -> no_connect  (NC: not-connected pin (NC))
RClamp0524PATCT: pin 8 'GND': unspecified -> power_in  (GND: ground-return pin (GND family))
RClamp0524PATCT: pin 9 'NC': unspecified -> no_connect  (NC: not-connected pin (NC))
RClamp0524PATCT: pin 10 'NC': unspecified -> no_connect  (NC: not-connected pin (NC))
