nathanfraske/CEC-Platform/docs/enterprise-requirements/board-program/pin-audit/cec-ent-power-fix-review-2026-07-03.txt

# cec_sym_audit --fix review for lib/cec-ent-power.kicad_sym
# no high-confidence fixes to apply
