nathanfraske/CEC-Platform/modules/atx-24pin-rev2/24pin-module.kicad_pcb

## KiCad design modules/atx-24pin-rev2/24pin-module.kicad_pcb (2026-06-02, an earlier design)

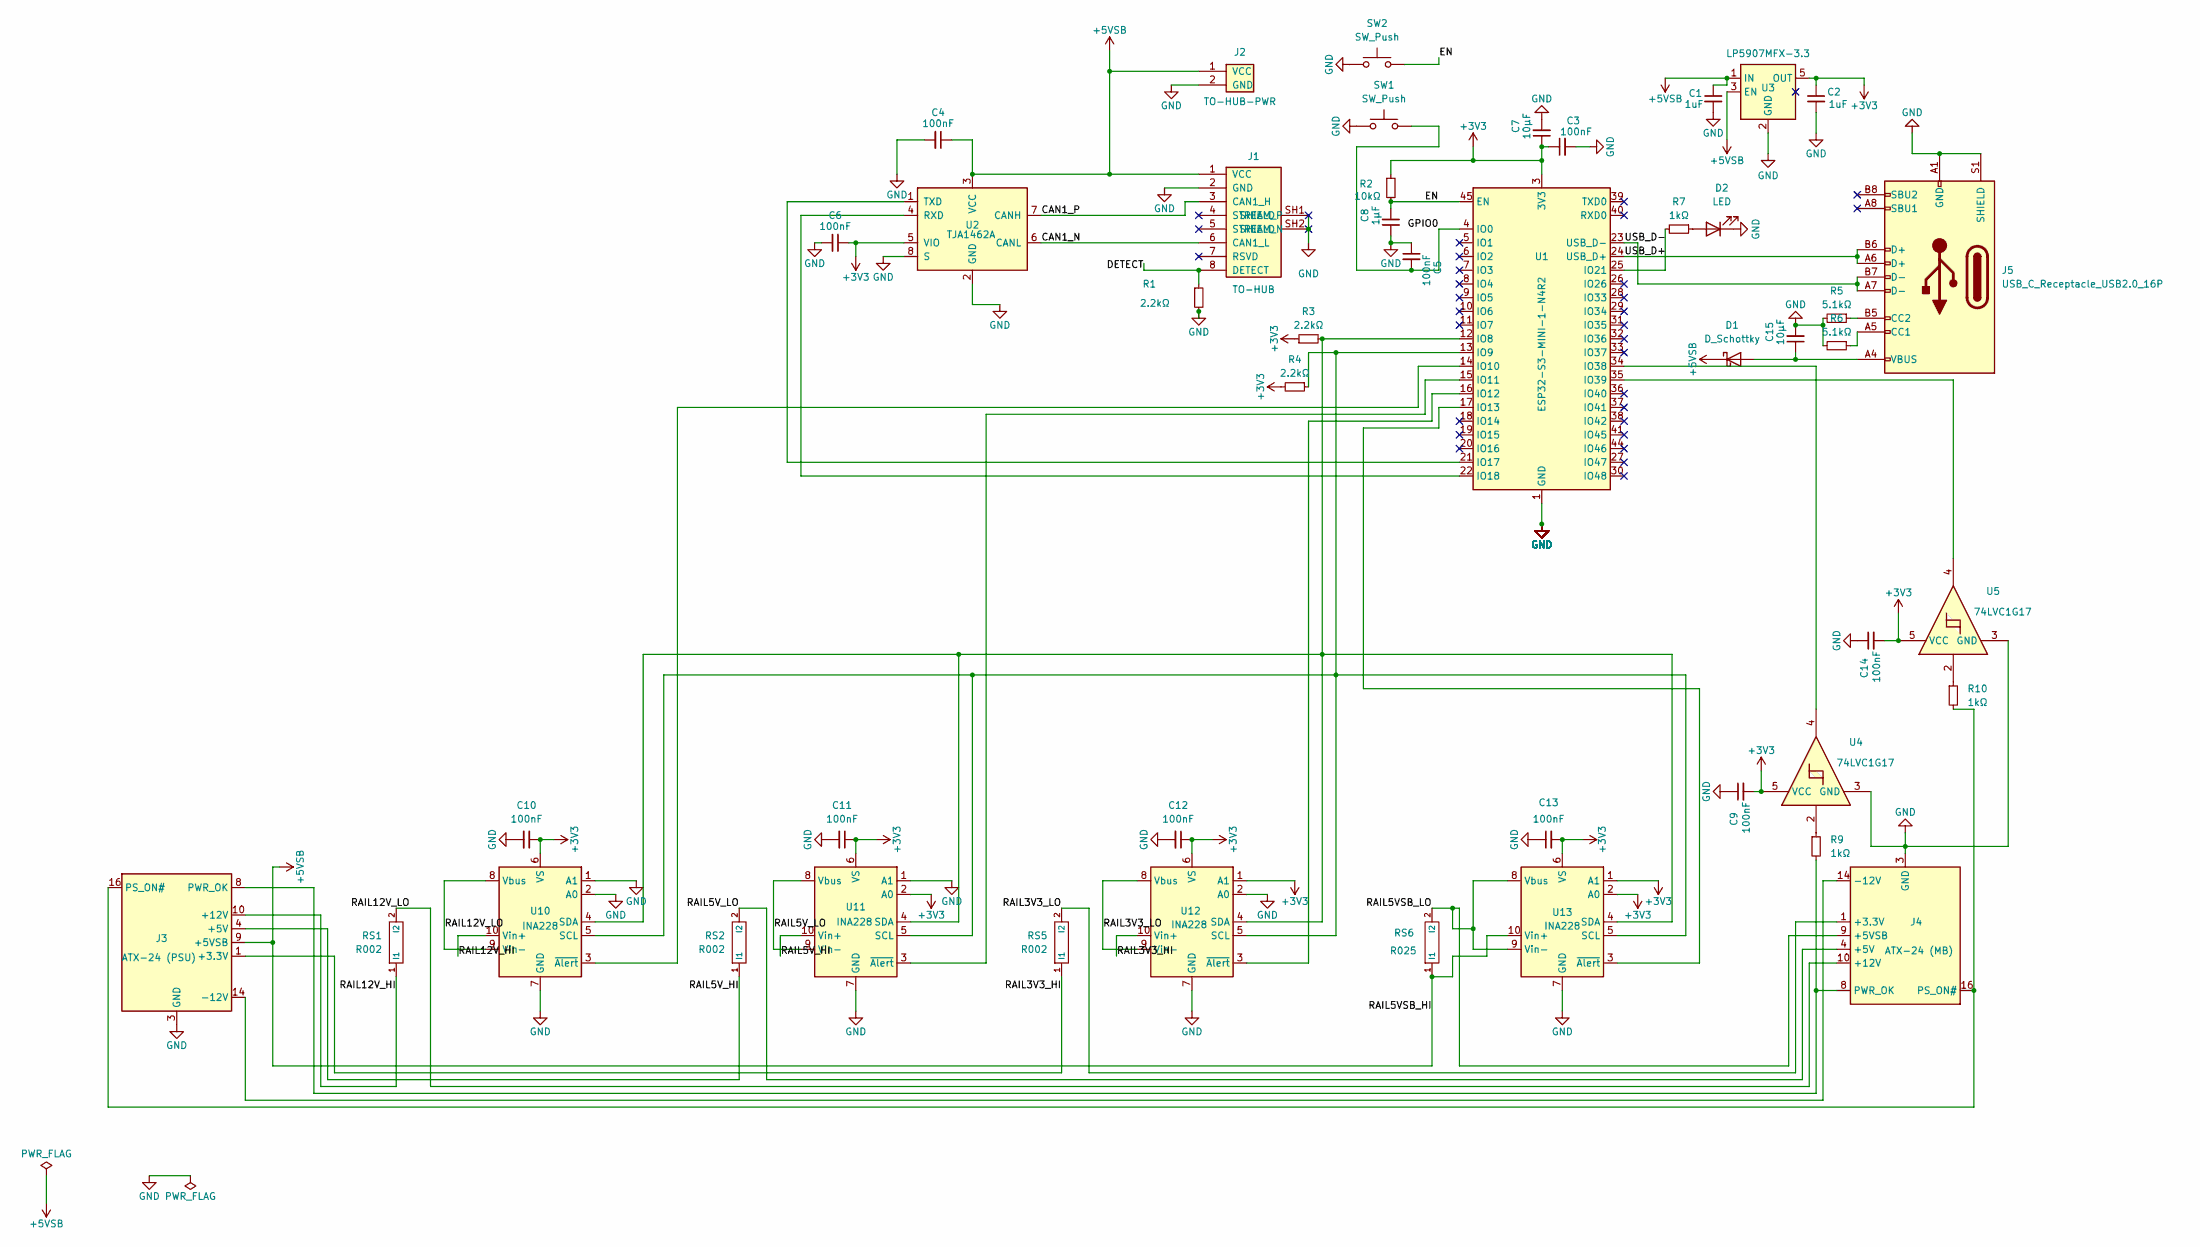
[picture p37: schematic 24pin-module.kicad_sch, CEC-24PIN-ATX-MODULE]

Parts:
C1, C2: 1uF; C_0603_1608Metric; Tolerance 10%; Voltage 25V; MPN CL10B105KB8NNNC; LCSC C15849
C3, C4, C5, C6, C10, C11, C12, C13: 100nF; C_0402_1005Metric; Tolerance 10%; Voltage 25V; MPN CL05B104KO5NNNC; LCSC C1525
C7, C15: 10µF; C_0805_2012Metric; Tolerance 10%; Voltage 25V; MPN CL21B106KOQNNNE; LCSC C15850
C8: 1µF; C_0805_2012Metric; Tolerance 10%; Voltage 25V; MPN CL21B105KBFNNNE; LCSC C28323
C9, C14: 100nF; C_0402_1005Metric; Voltage 25V; Tolerance 10%; MPN CL05B104KO5NNNC; LCSC C1525
D1: D_Schottky; D_SMA; MPN SS34; LCSC C8678
D2: LED; LED_0603_1608Metric; MPN KT-0603G; LCSC C12624
J1: TO-HUB; RJ45_Amphenol_54602-x08_Horizontal; MPN 54602-908LF; LCSC C2847314
J2: TO-HUB-PWR; JST_XH_S2B-XH-A_1x02_P2.50mm_Horizontal; MPN S2B-XH-A(LF)(SN); LCSC C157931
J3: ATX-24 (PSU); Molex_Mini-Fit_Jr_5569-24A1_2x12_P4.20mm_Horizontal; MPN 5569-24A1
J4: ATX-24 (MB); Molex_Mini-Fit_Jr_5569-24A1_2x12_P4.20mm_Horizontal; MPN 5569-24A1
J5: USB_C_Receptacle_USB2.0_16P; USB_C_Receptacle_XKB_U262-16XN-4BVC11; MPN U262-161N-4BVC11; LCSC C319148
R1, R3, R4: 2.2kΩ; R_0402_1005Metric; Tolerance 1%; MPN 0402WGF2201TCE; LCSC C25879
R2: 10kΩ; R_0402_1005Metric; Tolerance 1%; MPN 0402WGF1002TCE; LCSC C25744
R5, R6: 5.1kΩ; R_0402_1005Metric; Tolerance 1%; MPN 0402WGF5101TCE; LCSC C25905
R7, R9, R10: 1kΩ; R_0402_1005Metric; Tolerance 1%; MPN 0402WGF1001TCE; LCSC C11702
RS1, RS2, RS5: R002; R_2512_6332Metric; Tolerance 1%; MPN CSS2H-2512K-2L00F; LCSC C1729157
RS6: R025; R_2512_6332Metric; Tolerance 1%; MPN LCSR2512FR025K9L; LCSC C494568
SW1, SW2: SW_Push; Panasonic_EVQPUJ_EVQPUA; MPN EVQPUA02K; LCSC C128539
U1: ESP32-S3-MINI-1-N4R2; ESP32-S2-MINI-1_NoAntKeepout; MPN ESP32-S3-MINI-1-N4R2; LCSC C3013941
U2: TJA1462A; SOIC-8_3.9x4.9mm_P1.27mm; MPN TJA1462AT/0Z; LCSC C3234095
U3: LP5907MFX-3.3; SOT-23-5; MPN LP5907MFX-3.3/NOPB; LCSC C80670
U4, U5: 74LVC1G17; SOT-23-5; MPN SN74LVC1G17DBVR; LCSC C7836
U10, U11, U12, U13: INA228; VSSOP-10_3x3mm_P0.5mm; MPN INA228AIDGSR; LCSC C2887910

Connections:
+3V3: C2.1, C3.1, C6.1, C7.1, C9.2, C10.1, C11.1, C12.1, C13.2, C14.2, R2.1, R3.1, R4.2, U1.3 (3V3), U2.5 (VIO), U3.5 (OUT), U4.5 (VCC), U5.5 (VCC), U10.6 (VS), U11.2 (A0), U11.6 (VS), U12.1 (A1), U12.6 (VS), U13.1 (A1), U13.2 (A0), U13.6 (VS)
+5VSB: C1.1, C4.1, D1.1 (K), J1.1 (VCC), J2.1 (VCC), J3.9 (+5VSB), RS6.1 (I1), U2.3 (VCC), U3.1 (IN), U3.3 (EN), U13.10 (Vin+)
/CAN1_N: J1.6 (CAN1_L), U2.6 (CANL)
/CAN1_P: J1.3 (CAN1_H), U2.7 (CANH)
/DETECT: J1.8 (DETECT), R1.1
/EN: C8.2, R2.2, SW2.2, U1.45 (EN)
/GPIO0: C5.2, SW1.2, U1.4 (IO0)
/RAIL3V3_HI: J3.1 (+3.3V), J3.2 (+3.3V), J3.12 (+3.3V), J3.13 (+3.3V), RS5.1 (I1), U12.10 (Vin+)
/RAIL3V3_LO: J4.1 (+3.3V), J4.2 (+3.3V), J4.12 (+3.3V), J4.13 (+3.3V), RS5.2 (I2), U12.8 (Vbus), U12.9 (Vin-)
/RAIL5VSB_LO: J4.9 (+5VSB), RS6.2 (I2), U13.8 (Vbus), U13.9 (Vin-)
/RAIL5V_HI: J3.4 (+5V), J3.6 (+5V), J3.21 (+5V), J3.22 (+5V), J3.23 (+5V), RS2.1 (I1), U11.10 (Vin+)
/RAIL5V_LO: J4.4 (+5V), J4.6 (+5V), J4.21 (+5V), J4.22 (+5V), J4.23 (+5V), RS2.2 (I2), U11.8 (Vbus), U11.9 (Vin-)
/RAIL12V_HI: J3.10 (+12V), J3.11 (+12V), RS1.1 (I1), U10.10 (Vin+)
/RAIL12V_LO: J4.10 (+12V), J4.11 (+12V), RS1.2 (I2), U10.8 (Vbus), U10.9 (Vin-)
/USB_D+: J5.A6 (D+), J5.B6 (D+), U1.24 (USB_D+)
/USB_D-: J5.A7 (D-), J5.B7 (D-), U1.23 (USB_D-)
GND: C1.2, C2.2, C3.2, C4.2, C5.1, C6.2, C7.2, C8.1, C9.1, C10.2, C11.2, C12.2, C13.1, C14.1, C15.2, D2.1 (K), J1.2 (GND), J1.SH1 (SHIELD), J1.SH2 (SHIELD), J2.2 (GND), J3.3 (GND), J3.5 (GND), J3.7 (GND), J3.15 (GND), J3.17 (GND), J3.18 (GND), J3.19 (GND), J3.24 (GND), J4.3 (GND), J4.5 (GND), J4.7 (GND), J4.15 (GND), J4.17 (GND), J4.18 (GND), J4.19 (GND), J4.24 (GND), J5.A1 (GND), J5.A12 (GND), J5.B1 (GND), J5.B12 (GND), J5.S1 (SHIELD), R1.2, R5.2, R6.2, SW1.1, SW2.1, U1.1 (GND), U1.2 (GND), U1.42 (GND), U1.43 (GND), U1.46 (GND), U1.47 (GND), U1.48 (GND), U1.49 (GND), U1.50 (GND), U1.51 (GND), U1.52 (GND), U1.53 (GND), U1.54 (GND), U1.55 (GND), U1.56 (GND), U1.57 (GND), U1.58 (GND), U1.59 (GND), U1.60 (GND), U1.61 (GND), U1.62 (GND), U1.63 (GND), U1.64 (GND), U1.65 (GND), U2.2 (GND), U2.8 (S), U3.2 (GND), U4.3 (GND), U5.3 (GND), U10.1 (A1), U10.2 (A0), U10.7 (GND), U11.1 (A1), U11.7 (GND), U12.2 (A0), U12.7 (GND), U13.7 (GND)
unnamed: C15.1, D1.2 (A), J5.A4 (VBUS), J5.A9 (VBUS), J5.B4 (VBUS), J5.B9 (VBUS)
unnamed: D2.2 (A), R7.1
unnamed: J3.14 (-12V), J4.14 (-12V)
unnamed: J3.16 (PS_ON#), J4.16 (PS_ON#), R10.2
unnamed: J3.8 (PWR_OK), J4.8 (PWR_OK), R9.2
unnamed: J5.A5 (CC1), R6.1
unnamed: J5.B5 (CC2), R5.1
unnamed: R9.1, U4.2
unnamed: R10.1, U5.2
unnamed: R3.2, U1.12 (IO8), U10.4 (SDA), U11.4 (SDA), U12.4 (SDA), U13.4 (SDA)
unnamed: R4.1, U1.13 (IO9), U10.5 (SCL), U11.5 (SCL), U12.5 (SCL), U13.5 (SCL)
unnamed: U1.14 (IO10), U10.3 (~Alert)
unnamed: U1.15 (IO11), U11.3 (~Alert)
unnamed: U1.16 (IO12), U12.3 (~Alert)
unnamed: U1.17 (IO13), U13.3 (~Alert)
unnamed: U1.21 (IO17), U2.1 (TXD)
unnamed: U1.22 (IO18), U2.4 (RXD)
unnamed: R7.2, U1.25 (IO21)
unnamed: U1.34 (IO38), U4.4
unnamed: U1.35 (IO39), U5.4

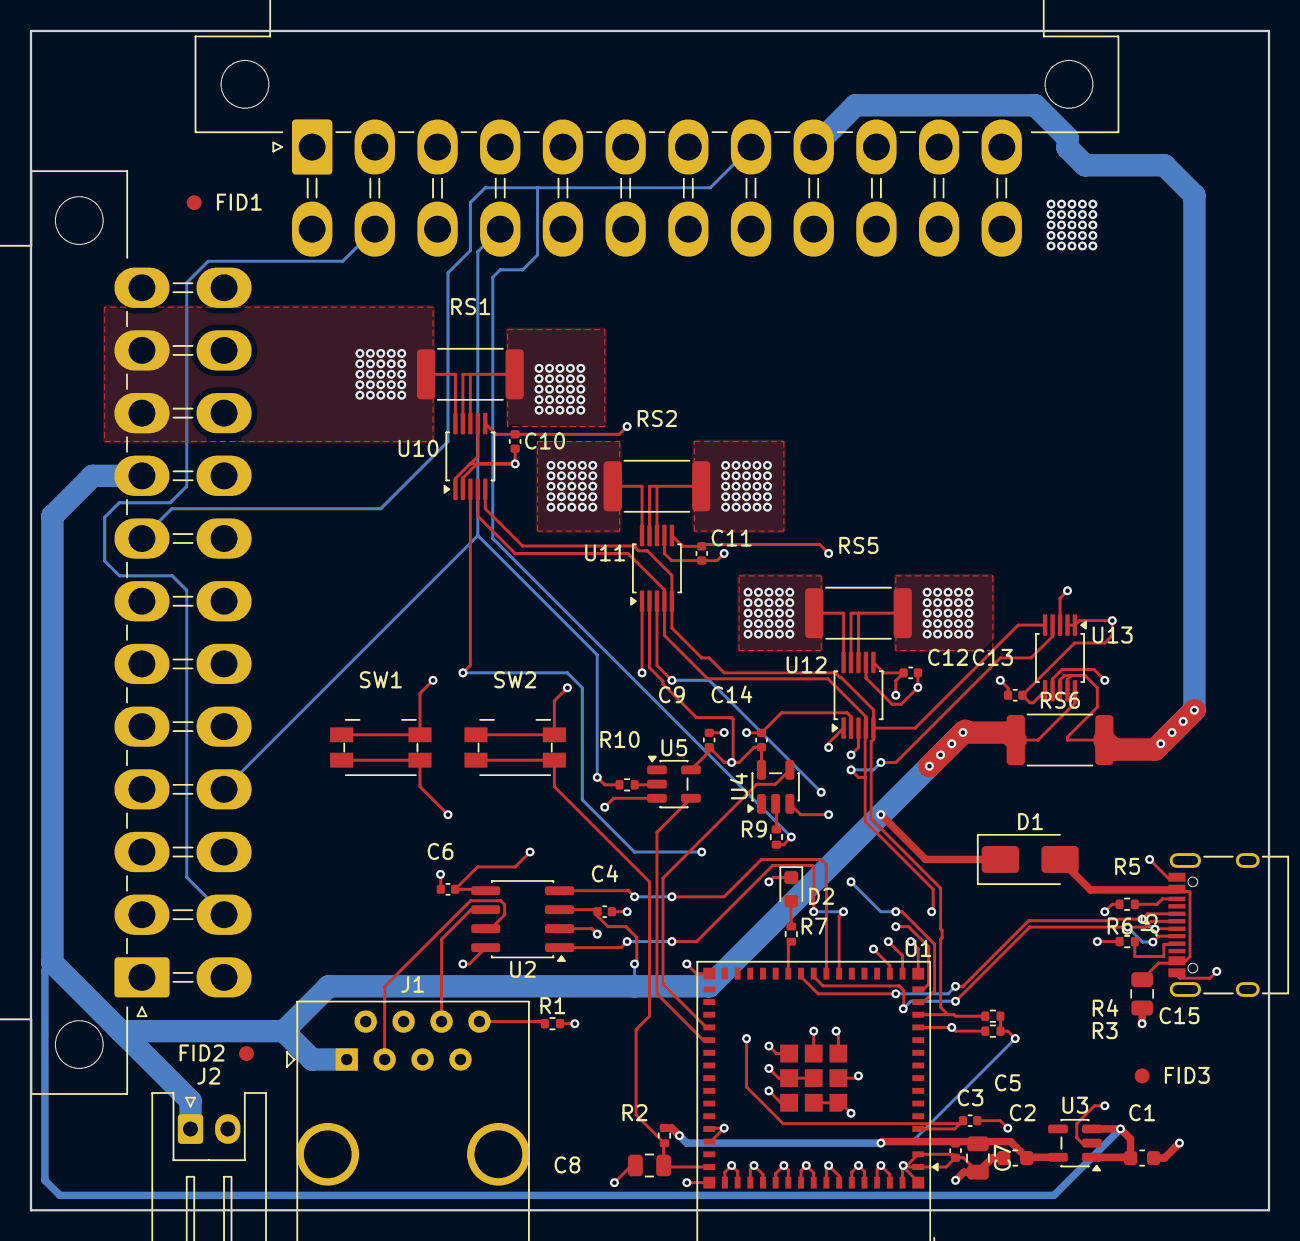
[picture p38: board modules/atx-24pin-rev2/24pin-module.kicad_pcb from above]

Board: 4 copper layers, 82.9 x 79.0 mm, 49 parts (0 on the bottom side), 37 nets.

Other parts of the board:
FID1, FID2, FID3: Fiducial_1mm_Mask2mm
