nathanfraske/CEC-Platform/testers/tester-standard/01-link.kicad_sch

## KiCad design testers/tester-standard/01-link.kicad_sch (2026-07-17)

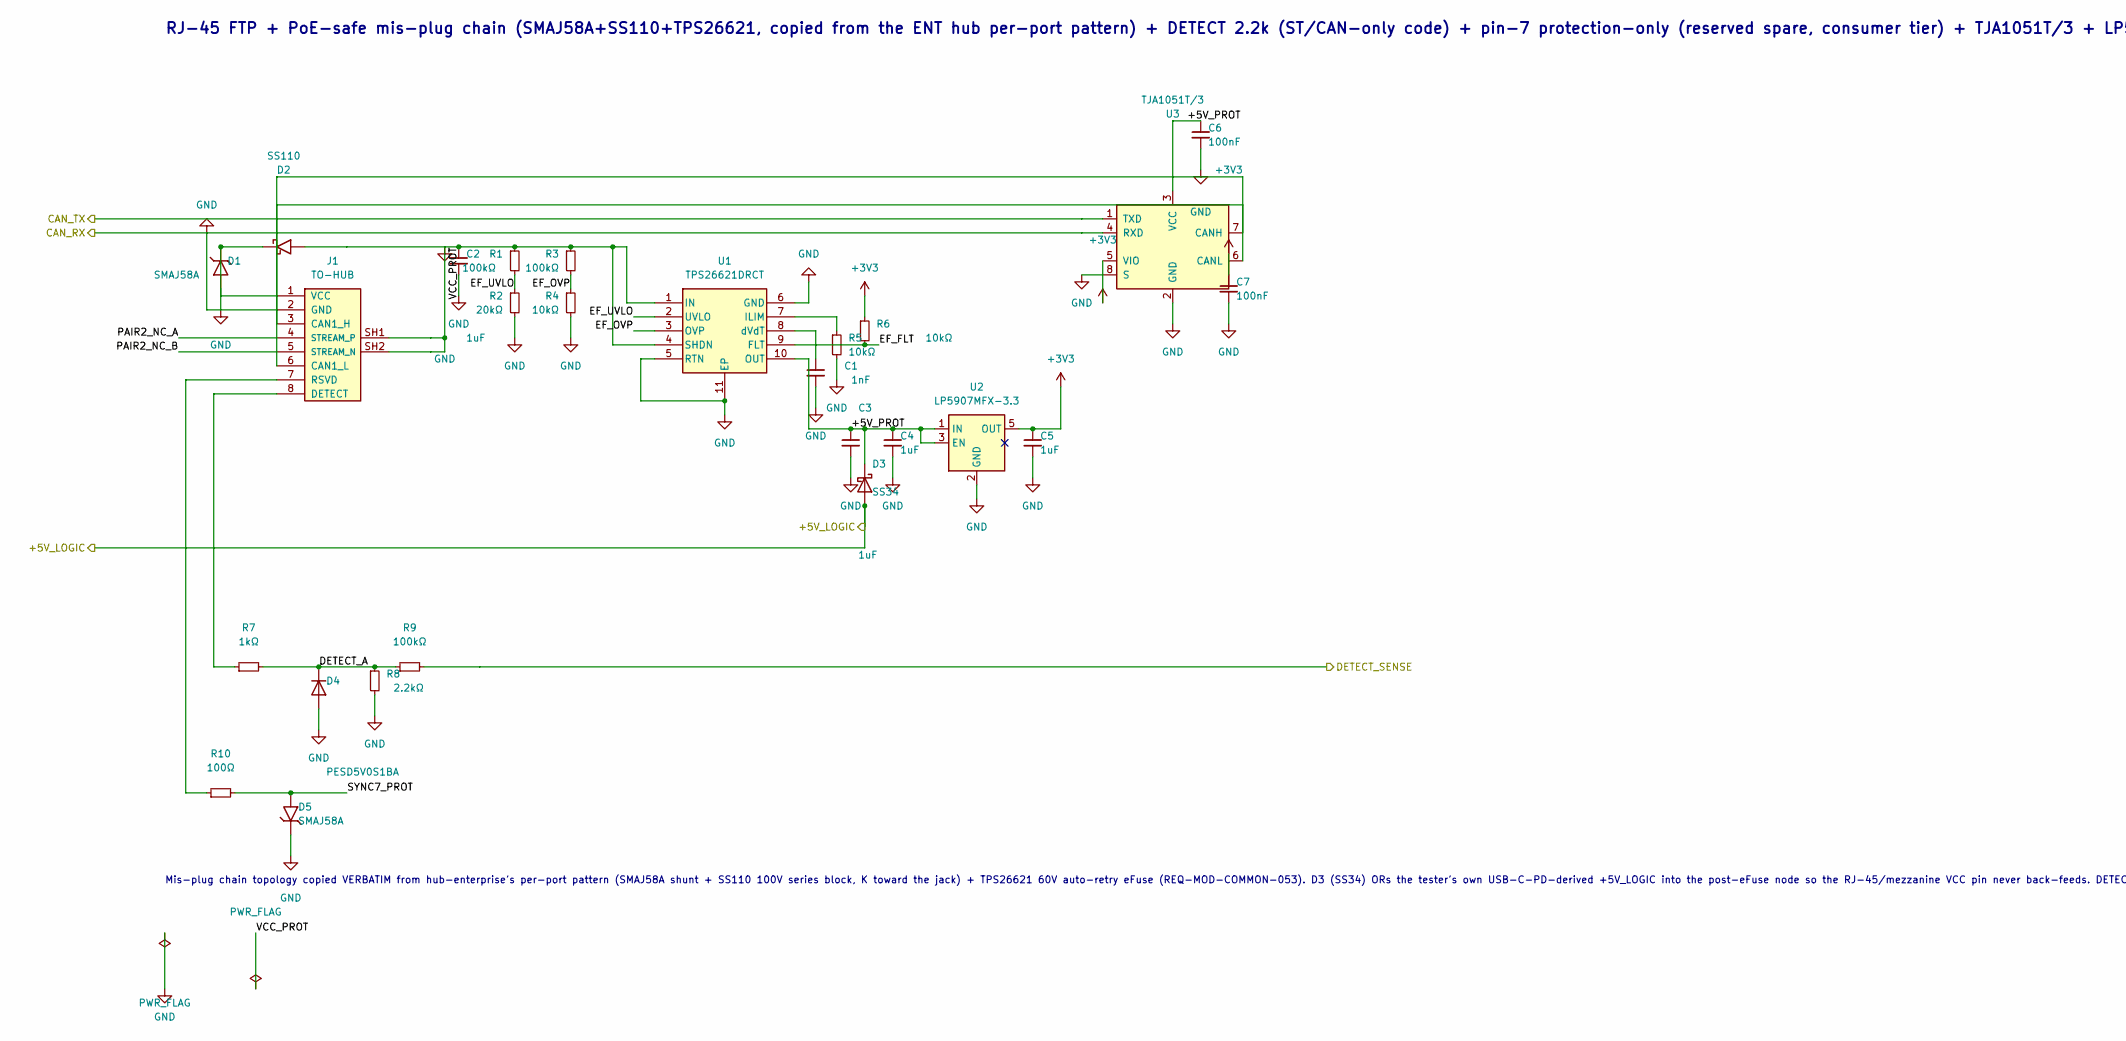
[picture p39: schematic 01-link.kicad_sch, part in row 1, column 1]

Parts:
C1: 1nF; C_0402_1005Metric
C2, C3, C4, C5: 1uF; C_0603_1608Metric
C6, C7: 100nF; C_0402_1005Metric
D1, D5: SMAJ58A; D_SMA_SMAJ58A_L4.4-W2.6-LS5.0; MPN SMAJ58A; LCSC C499822
D2: SS110; D_SMA_SS110_L4.3-W2.6-LS5.2; MPN SS110; LCSC C2482
D3: SS34; D_SOD-323
D4: PESD5V0S1BA; D_SOD-323; MPN PESD5V0S1BA; LCSC C5261083
J1: TO-HUB; RJ45_FTP_Shielded_Horizontal; MPN KH-RJ45-58-8P8C; LCSC C2683360
R1, R3, R9: 100kΩ; R_0402_1005Metric
R2: 20kΩ; R_0402_1005Metric
R4, R5, R6: 10kΩ; R_0402_1005Metric
R7: 1kΩ; R_0402_1005Metric
R8: 2.2kΩ; R_0402_1005Metric
R10: 100Ω; R_0402_1005Metric
U1: TPS26621DRCT; VSON-10_DRC0010J_L3.0-W3.0-P0.50-EP; MPN TPS26621DRCT
U2: LP5907MFX-3.3; SOT-23-5
U3: TJA1051T/3; SOIC-8_3.9x4.9mm_P1.27mm

Connections:
+3V3: C5.1, C7.1, R6.1, U2.5 (OUT), U3.5 (VIO)
+5V_LOGIC: D3.2 (A)
+5V_PROT: C3.1, C4.1, C6.1, D3.1 (K), U1.10 (OUT), U2.1 (IN), U2.3 (EN), U3.3 (VCC)
CAN_TX: U3.1 (TXD)
DETECT_A: D4.1 (K), R7.2, R8.1, R9.1
DETECT_SENSE: R9.2
EF_FLT: R6.2, U1.9 (FLT)
EF_OVP: R3.2, R4.1, U1.3 (OVP)
EF_UVLO: R1.2, R2.1, U1.2 (UVLO)
GND: C1.2, C2.1, C2.2, C3.2, C4.2, C5.2, C6.2, C7.2, D1.1 (A), D2.2 (A), D4.2 (A), D5.2 (K), J1.2 (GND), J1.SH1, J1.SH2, R1.1, R2.2, R3.1, R4.2, R5.2, R8.2, U1.1 (IN), U1.4 (SHDN), U1.5 (RTN), U1.6 (GND), U1.11 (EP), U2.2 (GND), U3.2 (GND), U3.4 (RXD), U3.8 (S)
unnamed: C1.1, U1.8 (dVdT)
unnamed: D1.2 (K), D2.1 (K), J1.1 (VCC)
unnamed: J1.3 (CAN1_H), U3.7 (CANH)
unnamed: J1.6 (CAN1_L), U3.6 (CANL)
unnamed: J1.7 (RSVD), R10.1
unnamed: J1.8 (DETECT), R7.1
unnamed: R5.1, U1.7 (ILIM)
PAIR2_NC_A: J1.4 (STREAM_P)
PAIR2_NC_B: J1.5 (STREAM_N)
SYNC7_PROT: D5.1 (A), R10.2

Notes on the sheet:
RJ-45 FTP + PoE-safe mis-plug chain (SMAJ58A+SS110+TPS26621, copied from the ENT hub per-port pattern) + DETECT 2.2k (ST/CAN-only code) + pin-7 protection-only (reserved spare, consumer tier) + TJA1051T/3 + LP5907 3V3 LDO
Mis-plug chain topology copied VERBATIM from hub-enterprise's per-port pattern (SMAJ58A shunt + SS110 100V series block, K toward the jack) + TPS26621 60V auto-retry eFuse (REQ-MOD-COMMON-053). D3 (SS34) ORs the tester's own USB-C-PD-derived +5V_LOGIC into the post-eFuse node so the RJ-45/mezzanine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
