nathanfraske/CEC-Platform/testers/tester-standard/02-power.kicad_sch

## KiCad design testers/tester-standard/02-power.kicad_sch (2026-07-17)

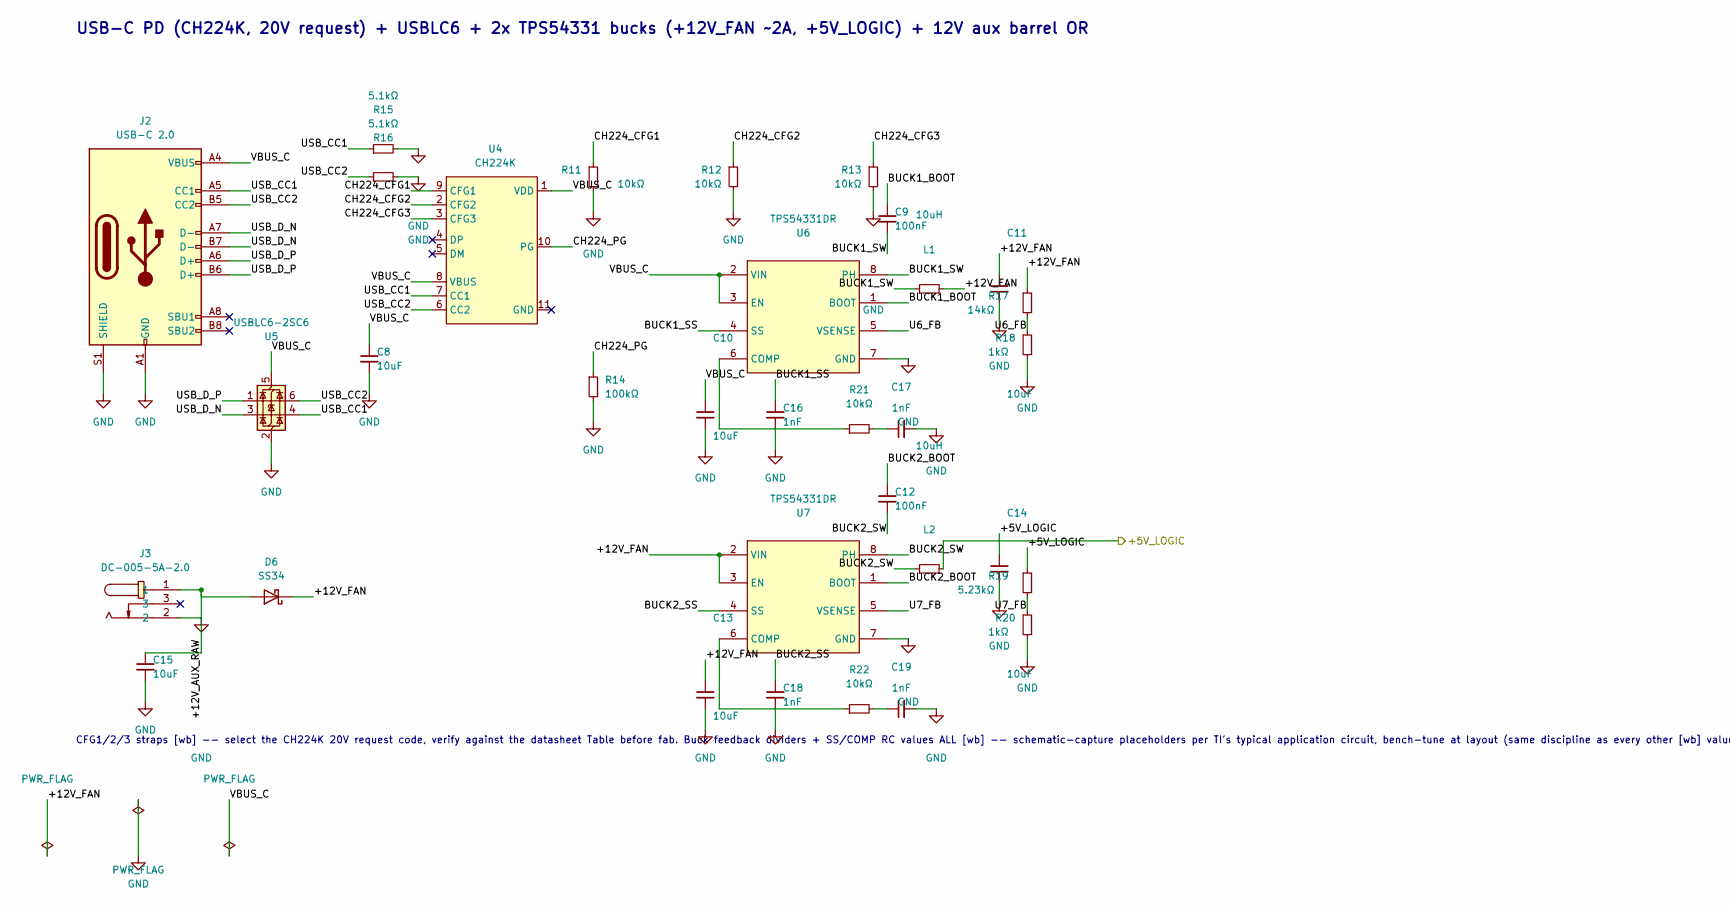
[picture p40: schematic 02-power.kicad_sch, part in row 1, column 1]

Parts:
C8, C10, C11, C13, C14, C15: 10uF; C_0805_2012Metric
C9, C12: 100nF; C_0402_1005Metric
C16, C17, C18, C19: 1nF; C_0402_1005Metric
D6: SS34; D_SOD-323
J2: USB-C 2.0; USB_C_Receptacle_XKB_U262-16XN-4BVC11
J3: DC-005-5A-2.0; DC-IN-TH_DC-005-5A-2.0; MPN DC-005-5A-2.0; LCSC C381116
L1, L2: 10uH; R_0402_1005Metric
R11, R12, R13, R21, R22: 10kΩ; R_0402_1005Metric
R14: 100kΩ; R_0402_1005Metric
R15, R16: 5.1kΩ; R_0402_1005Metric
R17: 14kΩ; R_0402_1005Metric
R18, R20: 1kΩ; R_0402_1005Metric
R19: 5.23kΩ; R_0402_1005Metric
U4: CH224K; ESSOP-10_L4.9-W3.9-P1.0-LS6.0-TL-EP; MPN CH224K; LCSC C970725
U5: USBLC6-2SC6; SOT-23-6
U6, U7: TPS54331DR; SOIC-8_L5.0-W4.0-P1.27-LS6.0-BL; MPN TPS54331DR; LCSC C9865

Connections:
+5V_LOGIC: C14.1, L2.2, R19.1
+12V_FAN: C11.1, C13.1, D6.1 (K), L1.2, R17.1, U7.2 (VIN), U7.3 (EN)
BUCK1_BOOT: C9.1, U6.1 (BOOT)
BUCK1_SS: C16.1, U6.4 (SS)
BUCK1_SW: C9.2, L1.1, U6.8 (PH)
BUCK2_BOOT: C12.1, U7.1 (BOOT)
BUCK2_SS: C18.1, U7.4 (SS)
BUCK2_SW: C12.2, L2.1, U7.8 (PH)
CH224_CFG1: R11.1, U4.9 (CFG1)
CH224_CFG2: R12.1, U4.2 (CFG2)
CH224_CFG3: R13.1, U4.3 (CFG3)
CH224_PG: R14.1, U4.10 (PG)
GND: C8.2, C10.2, C11.2, C13.2, C14.2, C15.1, C15.2, C16.2, C17.2, C18.2, C19.2, D6.2 (A), J2.A1 (GND), J2.A12 (GND), J2.B1 (GND), J2.B12 (GND), J2.S1 (SHIELD), J3.1, J3.2, R11.2, R12.2, R13.2, R14.2, R15.2, R16.2, R18.2, R20.2, U5.2 (GND), U6.7 (GND), U7.7 (GND)
unnamed: C17.1, R21.2
unnamed: C19.1, R22.2
unnamed: R21.1, U6.6 (COMP)
unnamed: R22.1, U7.6 (COMP)
U6_FB: R17.2, R18.1, U6.5 (VSENSE)
U7_FB: R19.2, R20.1, U7.5 (VSENSE)
USB_CC1: J2.A5 (CC1), R15.1, U4.7 (CC1), U5.4 (I/O2)
USB_CC2: J2.B5 (CC2), R16.1, U4.6 (CC2), U5.6 (I/O1)
USB_D_N: J2.A7 (D-), J2.B7 (D-), U5.3 (I/O2)
USB_D_P: J2.A6 (D+), J2.B6 (D+), U5.1 (I/O1)
VBUS_C: C8.1, C10.1, J2.A4 (VBUS), J2.A9 (VBUS), J2.B4 (VBUS), J2.B9 (VBUS), U4.1 (VDD), U4.8 (VBUS), U5.5 (VBUS), U6.2 (VIN), U6.3 (EN)

Notes on the sheet:
USB-C PD (CH224K, 20V request) + USBLC6 + 2x TPS54331 bucks (+12V_FAN ~2A, +5V_LOGIC) + 12V aux barrel OR
CFG1/2/3 straps [wb] -- select the CH224K 20V request code, verify against the datasheet Table before fab. Buck feedback dividers + SS/COMP RC values ALL [wb] -- schematic-capture placeholders per TI's typical application circuit, bench-tune at layout (same discipline as every other [wb] value in t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
