nathanfraske/CEC-Platform/testers/tester-standard/03-mcu.kicad_sch

## KiCad design testers/tester-standard/03-mcu.kicad_sch (2026-07-17)

Schematic: 03-mcu.kicad_sch

Parts:
C40: 10uF; C_0805_2012Metric
C41, C42, C43, C44, C45, C46, C47, C48, C49, C50, C51, C61, C62, C63, C64: 100nF; C_0402_1005Metric
J4: Fan1; PinHeader_1x04_P2.54mm_Vertical
J5: Fan2; PinHeader_1x04_P2.54mm_Vertical
J6: Fan3; PinHeader_1x04_P2.54mm_Vertical
J7: Bimetal de-gate backstop; PinHeader_1x04_P2.54mm_Vertical
R40, R41, R42, R43, R44, R45, R46, R47, R48, R49, R50, R51, R52, R53, R54, R55, R56: 10kΩ; R_0402_1005Metric
SW3, SW4, SW5: TS-1088-AR02016
TH1, TH2, TH3, TH4, TH5, TH6: NCP15XH103F03RC; NTC_0402_1005Metric; MPN NCP15XH103F03RC; LCSC C77131
U8: ESP32-C6-MINI-1-N4; ESP32-C6-MINI-1; MPN ESP32-C6-MINI-1-N4
U9, U10, U11, U12: 74HC595D,118; SOIC-16_L9.9-W3.9-P1.27-LS6.0-BL; MPN 74HC595D,118; LCSC C5947
U13, U14: 74HC165D,653; SOIC-16_L9.9-W3.9-P1.27-LS6.0-BL; MPN 74HC165D,653; LCSC C5613
U15, U16: MM74HC273WM; SOIC-20_L13.0-W7.6-P1.27-LS10.3-BL; MPN MM74HC273WM; LCSC C906662
U17: CD4051BM96; SOIC-16_L9.9-W3.9-P1.27-LS6.0-BL; MPN CD4051BM96; LCSC C21379

Connections:
+3V3: C40.1, C40.2, C41.1, C41.2, C42.1, C42.2, C43.1, C43.2, C44.1, C44.2, C45.1, C45.2, C46.1, C46.2, C47.1, C47.2, C48.1, C48.2, C49.1, C49.2, C50.1, C50.2, C51.1, C51.2, C61.2, C62.1, C62.2, C63.1, C63.2, C64.1, C64.2, J4.2, J5.2, J6.2, R40.1, R40.2, R41.1, R41.2, R42.1, R43.2, R44.2, R45.1, R46.1, R46.2, R47.1, R47.2, R48.1, R48.2, R49.1, R49.2, R50.1, R50.2, R51.1, R51.2, R52.1, R54.2, R55.1, R55.2, R56.2, SW3.2, SW4.2, SW5.2, TH1.1, TH1.2, TH2.1, TH2.2, TH3.1, TH3.2, TH4.1, TH4.2, TH5.1, TH5.2, TH6.1, TH6.2, U8.1 (GND), U8.2 (GND), U8.3 (3V3), U8.8 (EN), U8.11 (GND), U8.14 (GND), U8.23 (IO9), U8.29 (IO23), U8.36 (GND), U8.37 (GND), U8.38 (GND), U8.39 (GND), U8.40 (GND), U8.41 (GND), U8.42 (GND), U8.43 (GND), U8.44 (GND), U8.45 (GND), U8.46 (GND), U8.47 (GND), U8.48 (GND), U8.49 (GND), U8.50 (GND), U8.51 (GND), U8.52 (GND), U8.53 (GND), U9.8 (GND), U9.10 (~MR), U9.16 (VCC), U10.8 (GND), U10.10 (~MR), U10.16 (VCC), U11.8 (GND), U11.10 (~MR), U11.16 (VCC), U12.8 (GND), U12.10 (~MR), U12.16 (VCC), U13.8 (GND), U13.15 (~CE), U13.16 (VCC), U14.8 (GND), U14.15 (~CE), U14.16 (VCC), U15.10 (GND), U15.20 (VCC), U16.10 (GND), U16.13 (5D), U16.14 (6D), U16.17 (7D), U16.18 (8D), U16.20 (VCC), U17.7 (VEE), U17.8 (VSS), U17.16 (VDD)
+12V_FAN: J4.1, J5.1, J6.1
BACKLIGHT_PWM: U8.5 (IO2)
BANK_3V3_G1_CTRL: U10.2 (Q2)
BANK_3V3_G2_CTRL: U10.3 (Q3)
BANK_3V3_G3_CTRL: U10.4 (Q4)
BANK_3V3_G4_CTRL: U10.5 (Q5)
BANK_5VSB_G1_CTRL: U10.6 (Q6)
BANK_5VSB_G2_CTRL: U10.7 (Q7)
BANK_5VSB_G3_CTRL: U11.15 (Q0)
BANK_5V_G1_CTRL: U9.6 (Q6)
BANK_5V_G2_CTRL: U9.7 (Q7)
BANK_5V_G3_CTRL: U10.15 (Q0)
BANK_5V_G4_CTRL: U10.1 (Q1)
BANK_12V_G1_CTRL: U9.15 (Q0)
BANK_12V_G2_CTRL: U9.1 (Q1)
BANK_12V_G3_CTRL: U9.2 (Q2)
BANK_12V_G4_CTRL: U9.3 (Q3)
BANK_12V_G5_CTRL: U9.4 (Q4)
BANK_12V_G6_CTRL: U9.5 (Q5)
BANK_N12V_G1_CTRL: U11.1 (Q1)
BANK_N12V_G2_CTRL: U11.2 (Q2)
BOOT_STRAP: SW4.1
CAN_RX: U8.27 (IO21)
CAN_TX: U8.26 (IO20)
CLEAR_SHARED: U12.7 (Q7), U15.1 (CLEAR), U16.1 (CLEAR)
DEGATE_DRIVE: J7.1, U8.10 (IO5)
DEGATE_RAIL: J7.2, R44.1
DETECT_SENSE: U17.2 (IN/OUT6)
EN: SW3.1
FAN_PWM: J4.3, J5.3, J6.3, U8.22 (IO8)
FAN_TACH_1: J4.4, U13.3 (D4)
FAN_TACH_2: J5.4, U13.4 (D5)
FAN_TACH_3: J6.4, U13.5 (D6)
LCD_CS_BAY1: U11.6 (Q6)
LCD_CS_BAY2: U11.7 (Q7)
LCD_CS_BAY3: U12.15 (Q0)
LCD_CS_BAY4: U12.1 (Q1)
LCD_CS_BAY5: U12.2 (Q2)
LCD_CS_BAY6: U12.3 (Q3)
MUX_SEL_A: U12.4 (Q4)
MUX_SEL_B: U12.5 (Q5)
MUX_SEL_C: U12.6 (Q6)
NTC1_TAP: U17.13 (CHANNELSIN/OUT0)
NTC2_TAP: U17.14 (CHANNELSIN/OUT1)
NTC3_TAP: U17.15 (CHANNELSIN/OUT2)
NTC4_TAP: U17.12 (CHANNELSIN/OUT3)
NTC5_TAP: U17.1 (CHANNELS4)
NTC6_TAP: U17.5 (IN/OUT5)
unnamed: C61.1, R53.2
unnamed: R53.1, U8.25 (IO19)
unnamed: R54.1, U8.28 (IO22)
unnamed: R56.1, U8.13 (IO1)
unnamed: U10.9 (Q7S), U11.14 (DS)
unnamed: U9.9 (Q7S), U10.14 (DS)
unnamed: U11.9 (Q7S), U12.14 (DS)
unnamed: U13.10 (DS), U14.9 (Q7)
unnamed: U8.12 (IO0), U17.3 (COMOUT/IN)
SCP_3V3_ARM: U11.5 (Q5)
SCP_5V_ARM: U11.4 (Q4)
SCP_12V_ARM: U11.3 (Q3)
SCP_FIRE_SHARED: R43.1, U8.9 (IO4)
SHIFT_DATA_IN: U8.16 (IO7), U13.9 (Q7)
SHIFT_DATA_OUT: U8.20 (IO15), U9.14 (DS)
SHIFT_OE#: R45.2, U8.15 (IO6), U9.13 (~OE), U10.13 (~OE), U11.13 (~OE), U12.13 (~OE)
SHIFT_SCK: U8.19 (IO14), U9.11 (SHCP), U10.11 (SHCP), U11.11 (SHCP), U12.11 (SHCP), U13.2 (CP), U14.2 (CP)
SHIFT_STROBE: U8.24 (IO18), U9.12 (STCP), U10.12 (STCP), U11.12 (STCP), U12.12 (STCP), U13.1 (~PL), U14.1 (~PL)
SVC_BUTTON: R52.2, SW5.1, U13.6 (D7), U13.11 (D0)
TRIP_ANY: R42.2, U8.6 (IO3), U15.11 (CLOCK), U16.11 (CLOCK)
TRIP_BANK_3V3: U15.17 (7D)
TRIP_BANK_3V3_LATCH: U14.5 (D6), U15.16 (7Q)
TRIP_BANK_5V: U15.14 (6D)
TRIP_BANK_5VSB: U15.18 (8D)
TRIP_BANK_5VSB_LATCH: U14.6 (D7), U15.19 (8Q)
TRIP_BANK_5V_LATCH: U14.4 (D5), U15.15 (6Q)
TRIP_BANK_12V: U15.13 (5D)
TRIP_BANK_12V_LATCH: U14.3 (D4), U15.12 (5Q)
TRIP_BANK_N12V: U16.3 (1D)
TRIP_LOOP_3V3: U15.7 (3D)
TRIP_LOOP_3V3_LATCH: U14.13 (D2), U15.6 (3Q)
TRIP_LOOP_5V: U15.4 (2D)
TRIP_LOOP_5VSB: U15.8 (4D)
TRIP_LOOP_5VSB_LATCH: U14.14 (D3), U15.9 (4Q)
TRIP_LOOP_5V_LATCH: U14.12 (D1), U15.5 (2Q)
TRIP_LOOP_12V: U15.3 (1D)
TRIP_LOOP_12V_LATCH: U14.11 (D0), U15.2 (1Q)
TRIP_SCP_3V3: U16.8 (4D)
TRIP_SCP_3V3_LATCH: U13.14 (D3), U16.9 (4Q)
TRIP_SCP_5V: U16.7 (3D)
TRIP_SCP_5V_LATCH: U13.13 (D2), U16.6 (3Q)
TRIP_SCP_12V: U16.4 (2D)
TRIP_SCP_12V_LATCH: U13.12 (D1), U16.5 (2Q)
USB_D_N: U8.17 (IO12)
USB_D_P: U8.18 (IO13)

Notes on the sheet:
ESP32-C6-MINI-1-N4 core + shift-register expansion bus (4x 74HC595 / 2x 74HC165 / 2x MM74HC273 trip latches / CD4051 analog mux) + 4x PWM setpoint RC + fan PWM/tach + NTC dividers + bimetal de-gate backstop + BOOT/RESET/service buttons
GPIO map, shift-register bit map, and the real findings made DURING capture (not just planned in advance) are in this file's own header comment above compose_03() and in pin-audit-review-2026-07-16.txt addendum 4: the 5VSB setpoint upgrade + 165 having no tri-state (needs a separate DATA_IN line) u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
