nathanfraske/CEC-Platform/testers/tester-standard/04a-loop-12v.kicad_sch

## KiCad design testers/tester-standard/04a-loop-12v.kicad_sch (2026-07-17)

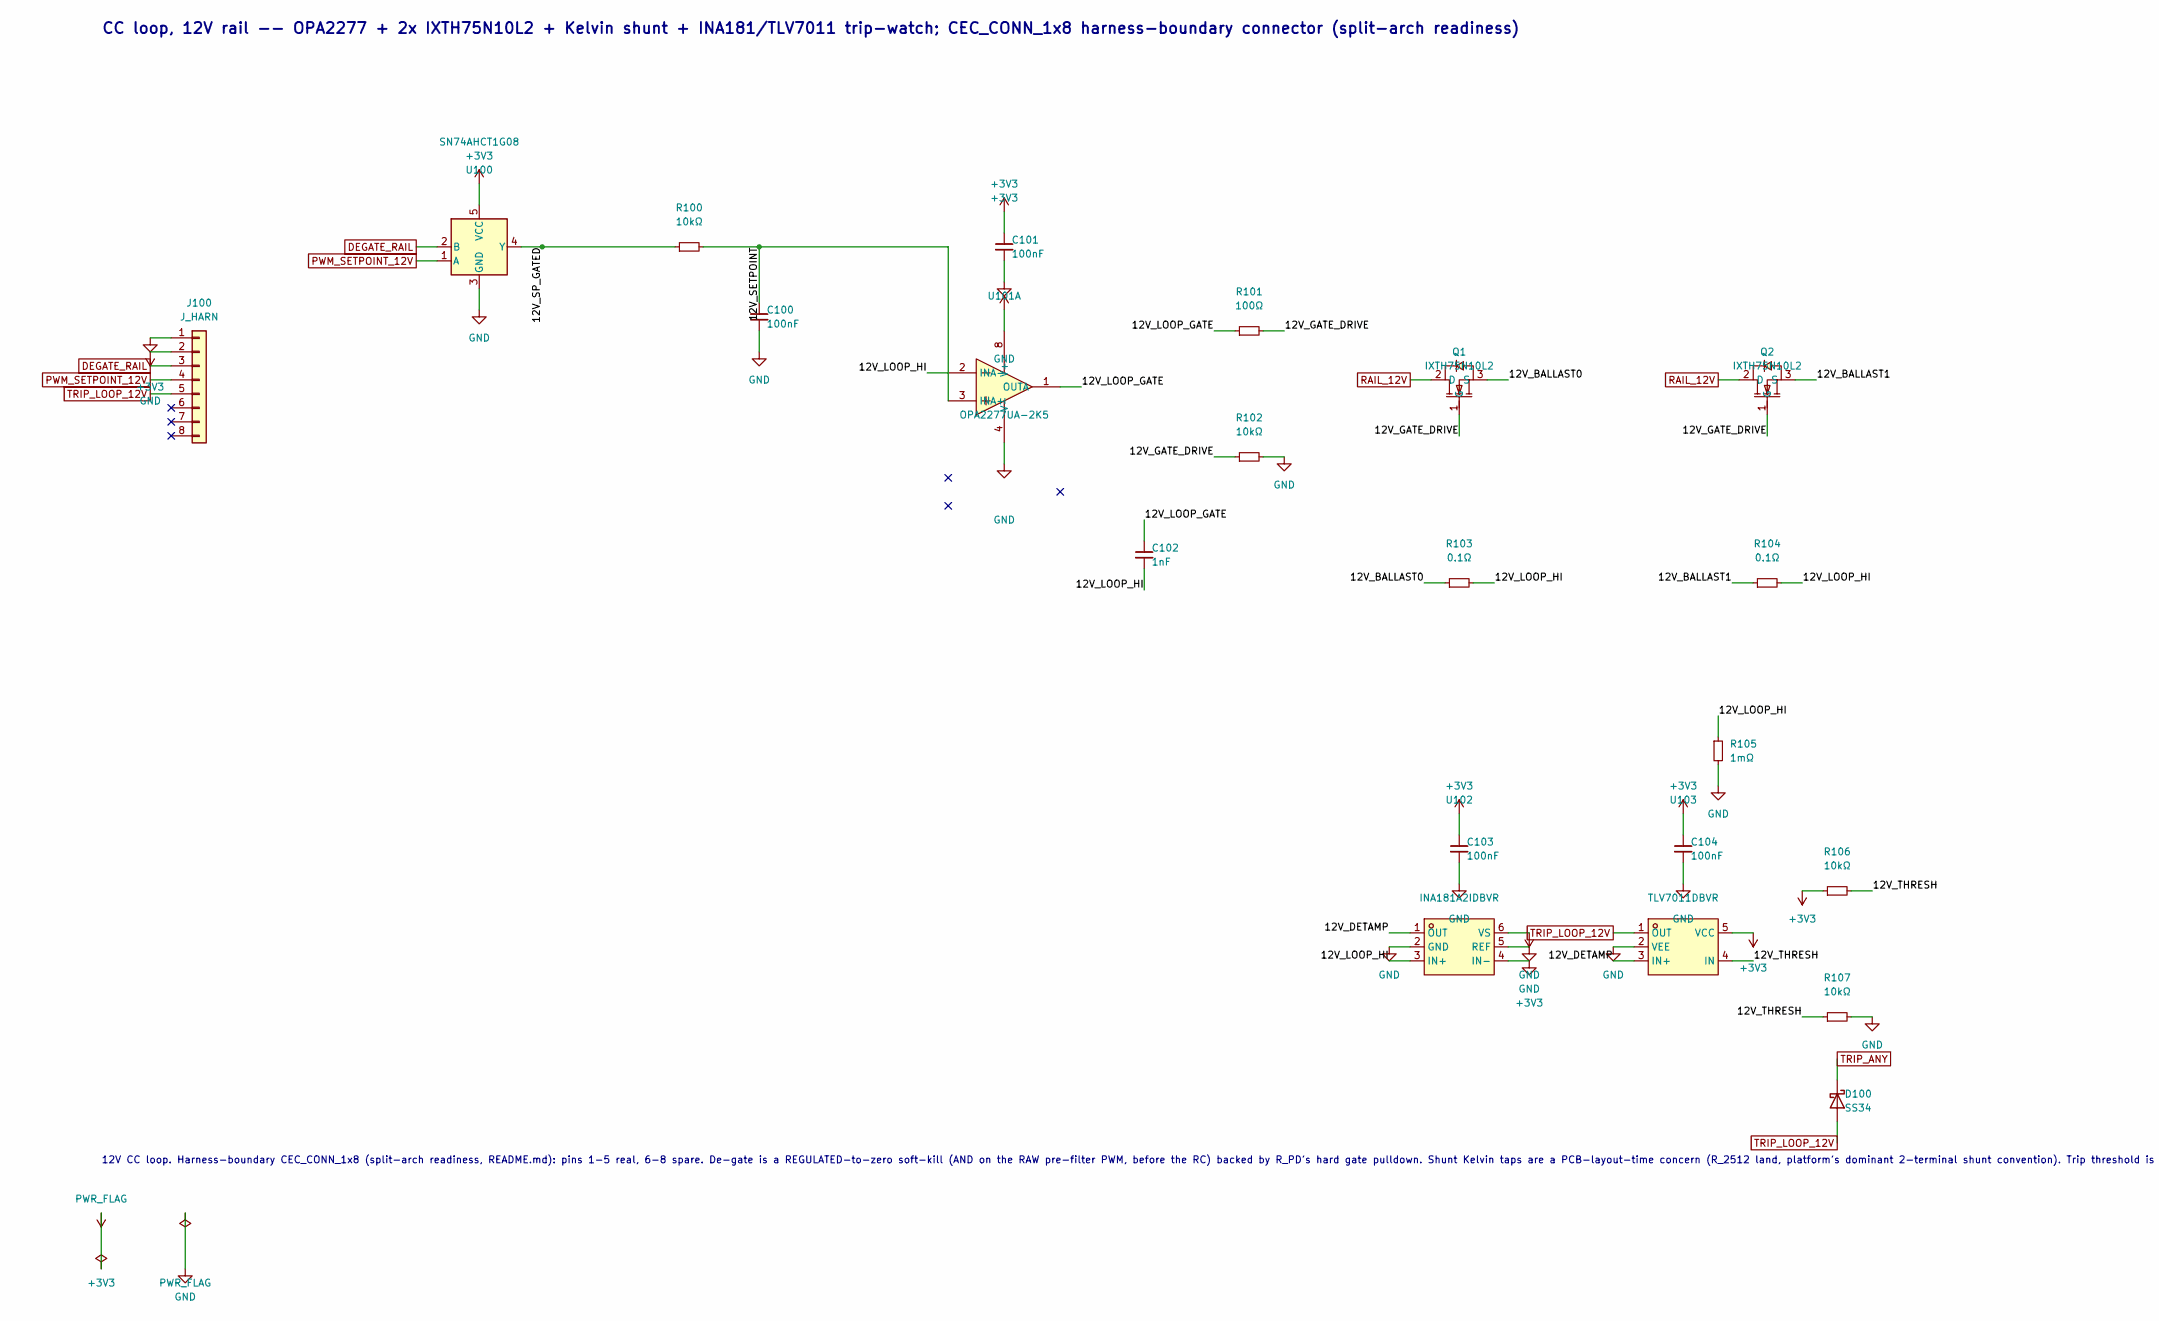
[picture p41: schematic 04a-loop-12v.kicad_sch, part in row 1, column 1]

Parts:
C100, C101, C103, C104: 100nF; C_0402_1005Metric
C102: 1nF; C_0402_1005Metric
D100: SS34; D_SOD-323
J100: J_HARN; PinHeader_1x08_P2.54mm_Vertical
Q1, Q2: IXTH75N10L2; TO-247-3_L15.9-W20.8-P5.45-Vertical
R100, R102, R106, R107: 10kΩ; R_0402_1005Metric
R101: 100Ω; R_0402_1005Metric
R103, R104: 0.1Ω; R_0402_1005Metric
R105: 1mΩ; R_0402_1005Metric; MPN CSS2H-2512R-1L00F; LCSC C4175647
U100: SN74AHCT1G08; SOT-23-5; MPN SN74AHCT1G08DBVR
U101: OPA2277UA-2K5; SOIC-8_L5.0-W4.0-P1.27-LS6.0-BL; MPN OPA2277UA-2K5; LCSC C24460
U102: INA181A2IDBVR; SOT-23-6; MPN INA181A2IDBVR; LCSC C2058784
U103: TLV7011DBVR; SOT-23-5; MPN TLV7011DBVR; LCSC C702117

Connections:
12V_BALLAST0: Q1.3 (S), R103.1
12V_BALLAST1: Q2.3 (S), R104.1
12V_DETAMP: U102.1 (OUT), U103.3 (IN+)
12V_GATE_DRIVE: Q1.1 (G), Q2.1 (G), R101.2, R102.1
12V_LOOP_GATE: C102.1, R101.1, U101.1 (OUTA)
12V_LOOP_HI: C102.2, R103.2, R104.2, R105.1, U101.2 (INA-), U102.3 (IN+)
12V_SETPOINT: C100.1, R100.2, U101.3 (INA+)
12V_SP_GATED: R100.1, U100.4 (Y)
12V_THRESH: R106.2, R107.1, U103.4 (IN)
+3V3: C101.1, C103.1, C104.1, J100.2, R106.1, U100.5 (VCC), U101.8 (V+), U102.6 (VS), U103.5 (VCC)
DEGATE_RAIL: J100.3, U100.2 (B)
GND: C100.2, C101.2, C103.2, C104.2, J100.1, R102.2, R105.2, R107.2, U100.3 (GND), U101.4 (V-), U102.2 (GND), U102.4 (IN-), U102.5 (REF), U103.2 (VEE)
PWM_SETPOINT_12V: J100.4, U100.1 (A)
RAIL_12V: Q1.2 (D), Q2.2 (D)
TRIP_ANY: D100.1 (K)
TRIP_LOOP_12V: D100.2 (A), J100.5, U103.1 (OUT)

Notes on the sheet:
CC loop, 12V rail -- OPA2277 + 2x IXTH75N10L2 + Kelvin shunt + INA181/TLV7011 trip-watch; CEC_CONN_1x8 harness-boundary connector (split-arch readiness)
12V CC loop. Harness-boundary CEC_CONN_1x8 (split-arch readiness, README.md): pins 1-5 real, 6-8 spare. De-gate is a REGULATED-to-zero soft-kill (AND on the RAW pre-filter PWM, before the RC) backed by R_PD's hard gate pulldown. Shunt Kelvin taps are a PCB-layout-time concern (R_2512 land, platform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
