nathanfraske/CEC-Platform/testers/tester-standard/04b-loop-5v.kicad_sch

## KiCad design testers/tester-standard/04b-loop-5v.kicad_sch (2026-07-17)

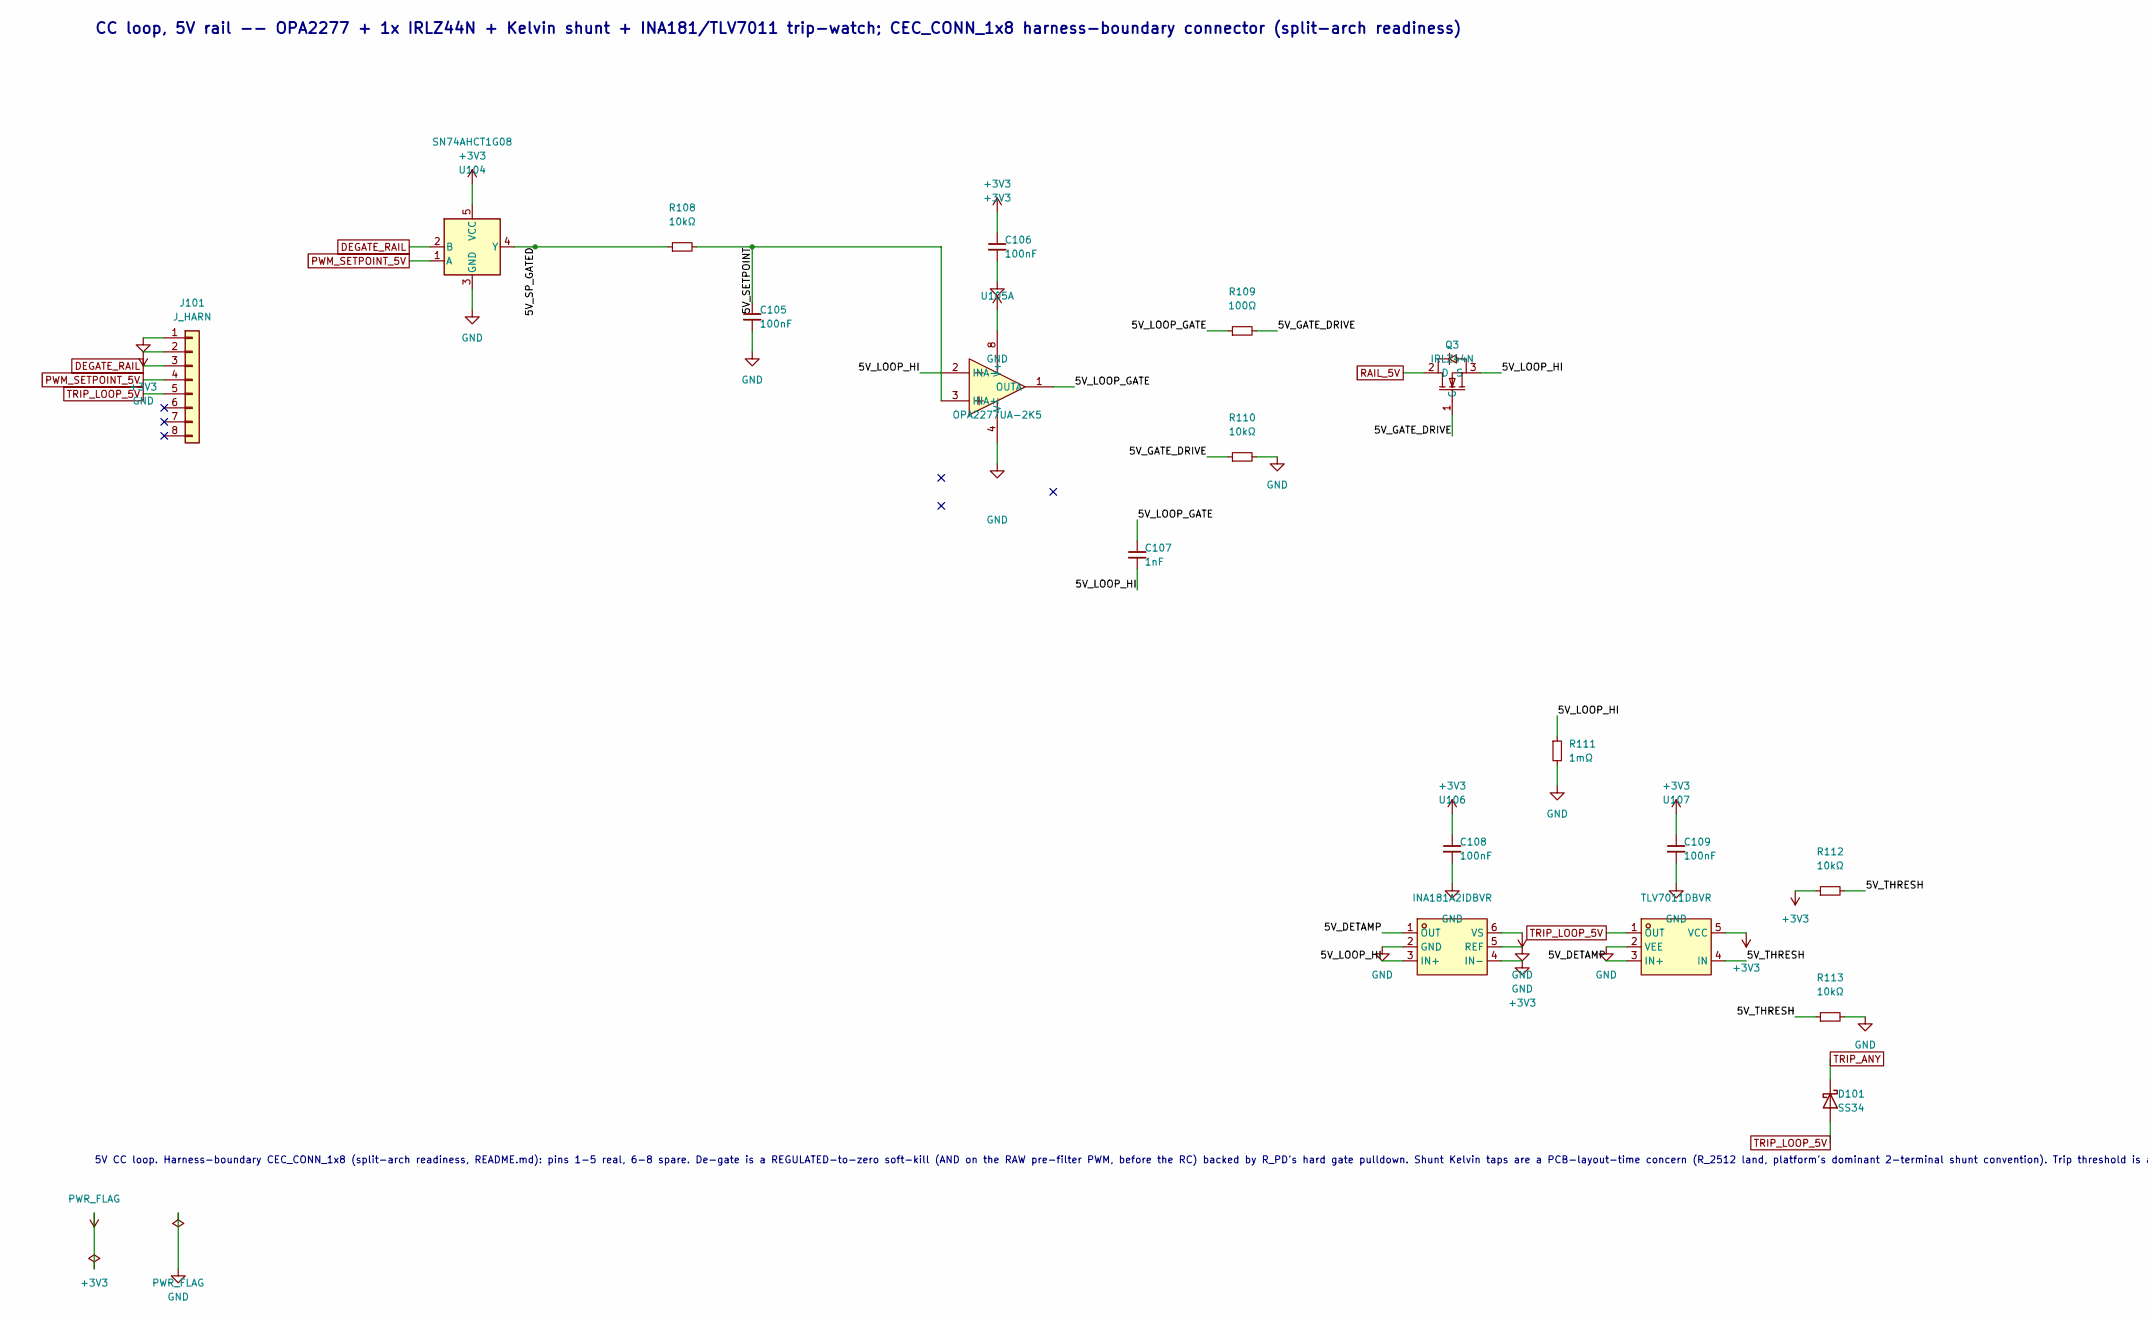
[picture p42: schematic 04b-loop-5v.kicad_sch, part in row 1, column 1]

Parts:
C105, C106, C108, C109: 100nF; C_0402_1005Metric
C107: 1nF; C_0402_1005Metric
D101: SS34; D_SOD-323
J101: J_HARN; PinHeader_1x08_P2.54mm_Vertical
Q3: IRLZ44N; TO-220-3_L10.2-W4.5-P2.54-L
R108, R110, R112, R113: 10kΩ; R_0402_1005Metric
R109: 100Ω; R_0402_1005Metric
R111: 1mΩ; R_0402_1005Metric; MPN CSS2H-2512R-1L00F; LCSC C4175647
U104: SN74AHCT1G08; SOT-23-5; MPN SN74AHCT1G08DBVR
U105: OPA2277UA-2K5; SOIC-8_L5.0-W4.0-P1.27-LS6.0-BL; MPN OPA2277UA-2K5; LCSC C24460
U106: INA181A2IDBVR; SOT-23-6; MPN INA181A2IDBVR; LCSC C2058784
U107: TLV7011DBVR; SOT-23-5; MPN TLV7011DBVR; LCSC C702117

Connections:
5V_DETAMP: U106.1 (OUT), U107.3 (IN+)
5V_GATE_DRIVE: Q3.1 (G), R109.2, R110.1
5V_LOOP_GATE: C107.1, R109.1, U105.1 (OUTA)
5V_LOOP_HI: C107.2, Q3.3 (S), R111.1, U105.2 (INA-), U106.3 (IN+)
5V_SETPOINT: C105.1, R108.2, U105.3 (INA+)
5V_SP_GATED: R108.1, U104.4 (Y)
5V_THRESH: R112.2, R113.1, U107.4 (IN)
+3V3: C106.1, C108.1, C109.1, J101.2, R112.1, U104.5 (VCC), U105.8 (V+), U106.6 (VS), U107.5 (VCC)
DEGATE_RAIL: J101.3, U104.2 (B)
GND: C105.2, C106.2, C108.2, C109.2, J101.1, R110.2, R111.2, R113.2, U104.3 (GND), U105.4 (V-), U106.2 (GND), U106.4 (IN-), U106.5 (REF), U107.2 (VEE)
PWM_SETPOINT_5V: J101.4, U104.1 (A)
RAIL_5V: Q3.2 (D)
TRIP_ANY: D101.1 (K)
TRIP_LOOP_5V: D101.2 (A), J101.5, U107.1 (OUT)

Notes on the sheet:
CC loop, 5V rail -- OPA2277 + 1x IRLZ44N + Kelvin shunt + INA181/TLV7011 trip-watch; CEC_CONN_1x8 harness-boundary connector (split-arch readiness)
5V CC loop. Harness-boundary CEC_CONN_1x8 (split-arch readiness, README.md): pins 1-5 real, 6-8 spare. De-gate is a REGULATED-to-zero soft-kill (AND on the RAW pre-filter PWM, before the RC) backed by R_PD's hard gate pulldown. Shunt Kelvin taps are a PCB-layout-time concern (R_2512 land, platform'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
