nathanfraske/CEC-Platform/testers/tester-standard/04c-loop-3v3.kicad_sch

## KiCad design testers/tester-standard/04c-loop-3v3.kicad_sch (2026-07-17)

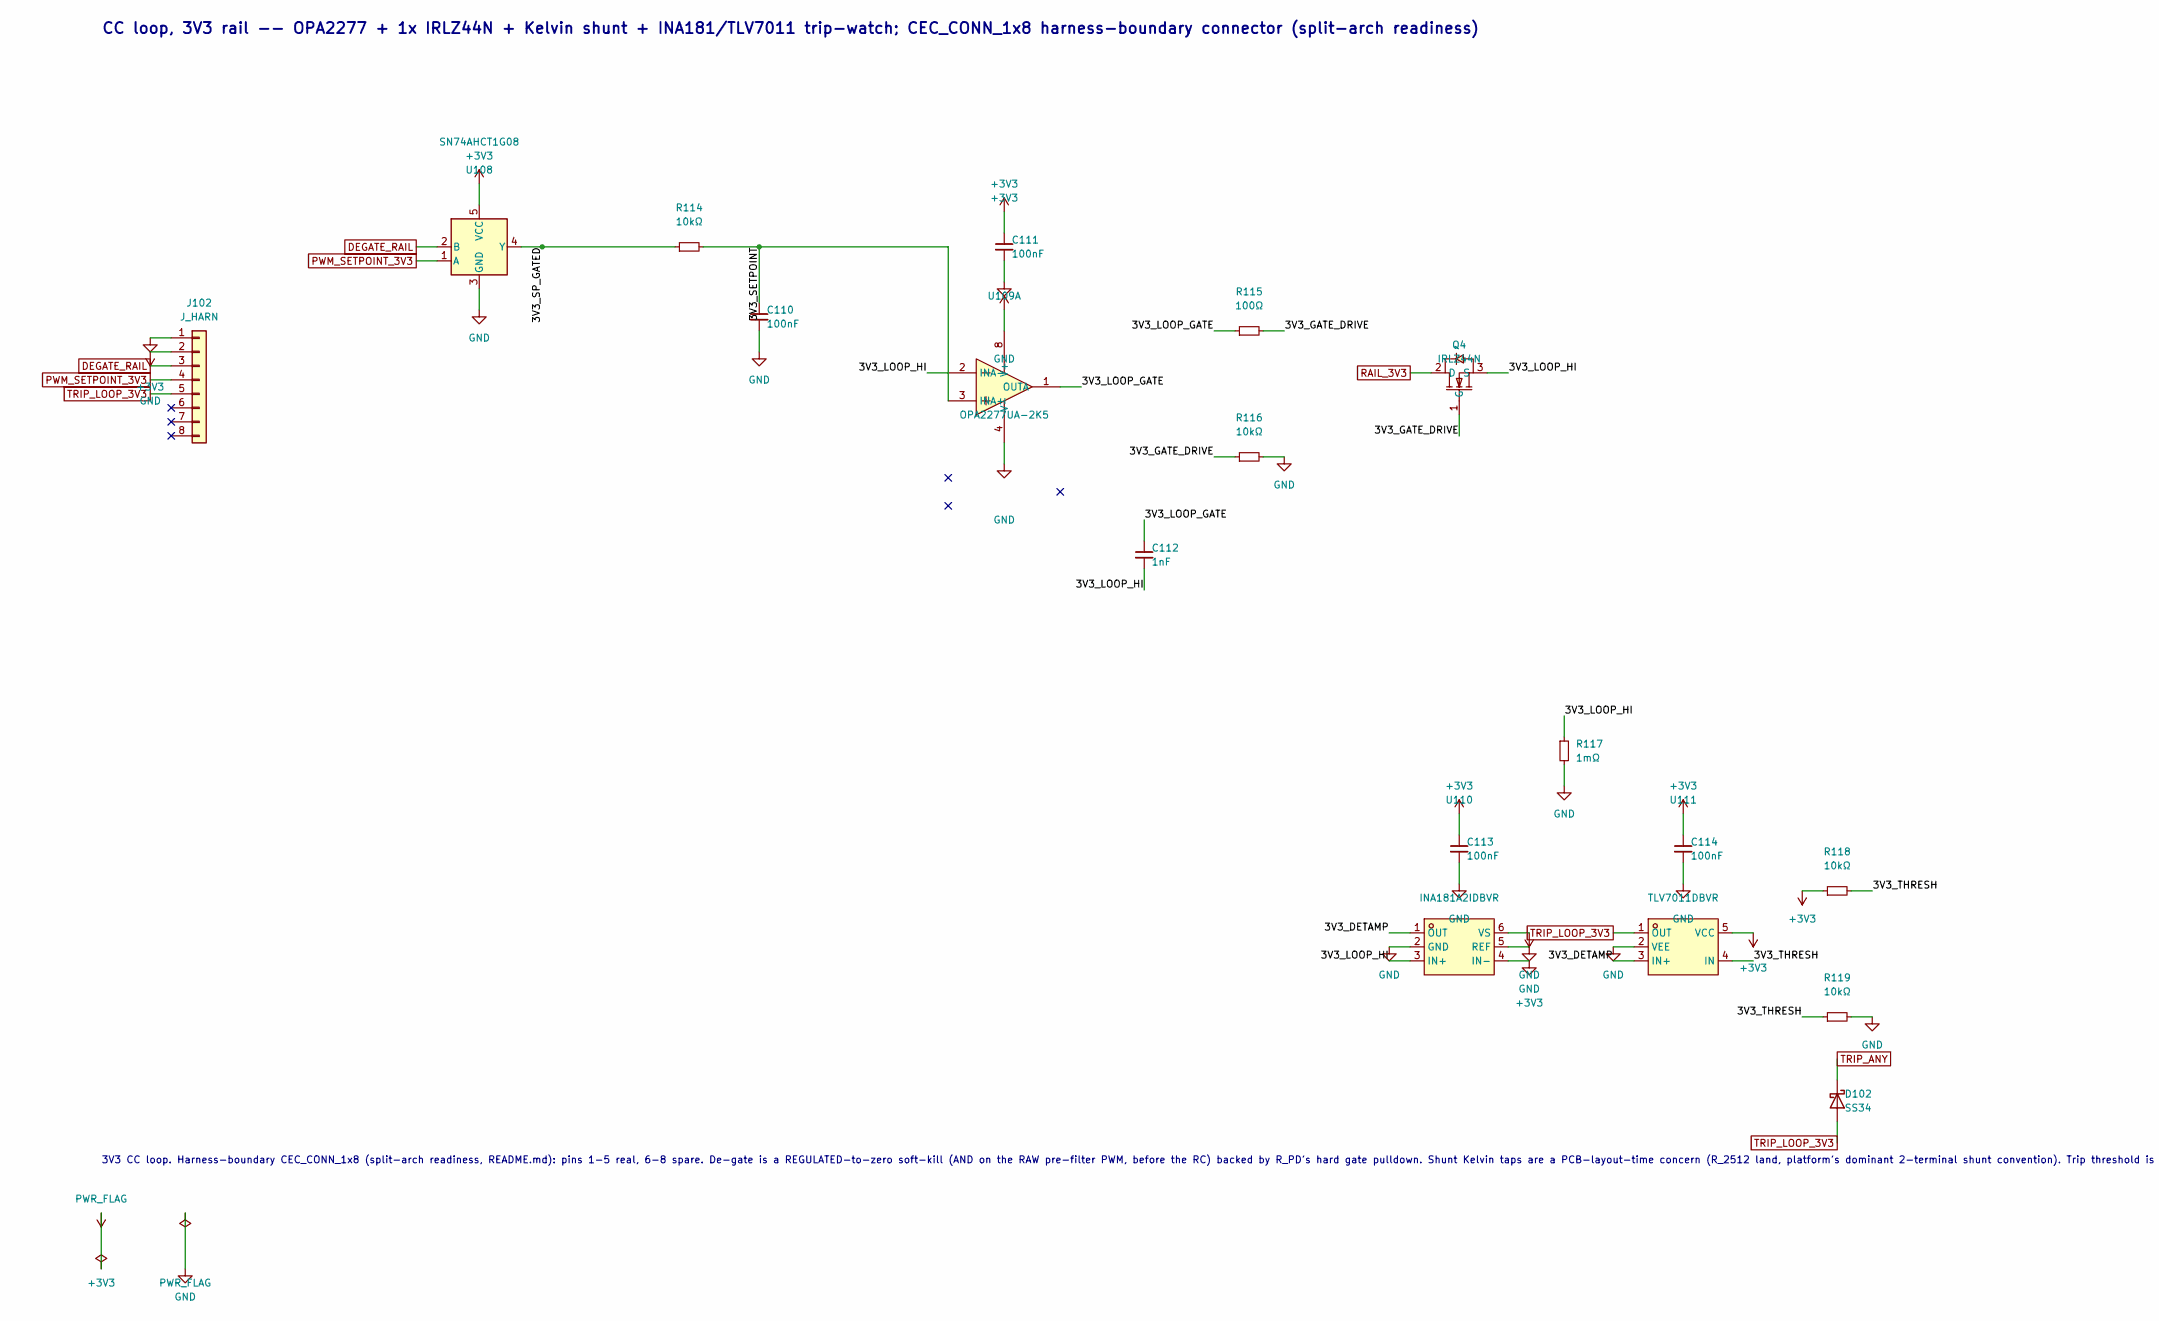
[picture p43: schematic 04c-loop-3v3.kicad_sch, part in row 1, column 1]

Parts:
C110, C111, C113, C114: 100nF; C_0402_1005Metric
C112: 1nF; C_0402_1005Metric
D102: SS34; D_SOD-323
J102: J_HARN; PinHeader_1x08_P2.54mm_Vertical
Q4: IRLZ44N; TO-220-3_L10.2-W4.5-P2.54-L
R114, R116, R118, R119: 10kΩ; R_0402_1005Metric
R115: 100Ω; R_0402_1005Metric
R117: 1mΩ; R_0402_1005Metric; MPN CSS2H-2512R-1L00F; LCSC C4175647
U108: SN74AHCT1G08; SOT-23-5; MPN SN74AHCT1G08DBVR
U109: OPA2277UA-2K5; SOIC-8_L5.0-W4.0-P1.27-LS6.0-BL; MPN OPA2277UA-2K5; LCSC C24460
U110: INA181A2IDBVR; SOT-23-6; MPN INA181A2IDBVR; LCSC C2058784
U111: TLV7011DBVR; SOT-23-5; MPN TLV7011DBVR; LCSC C702117

Connections:
3V3_DETAMP: U110.1 (OUT), U111.3 (IN+)
3V3_GATE_DRIVE: Q4.1 (G), R115.2, R116.1
3V3_LOOP_GATE: C112.1, R115.1, U109.1 (OUTA)
3V3_LOOP_HI: C112.2, Q4.3 (S), R117.1, U109.2 (INA-), U110.3 (IN+)
3V3_SETPOINT: C110.1, R114.2, U109.3 (INA+)
3V3_SP_GATED: R114.1, U108.4 (Y)
3V3_THRESH: R118.2, R119.1, U111.4 (IN)
+3V3: C111.1, C113.1, C114.1, J102.2, R118.1, U108.5 (VCC), U109.8 (V+), U110.6 (VS), U111.5 (VCC)
DEGATE_RAIL: J102.3, U108.2 (B)
GND: C110.2, C111.2, C113.2, C114.2, J102.1, R116.2, R117.2, R119.2, U108.3 (GND), U109.4 (V-), U110.2 (GND), U110.4 (IN-), U110.5 (REF), U111.2 (VEE)
PWM_SETPOINT_3V3: J102.4, U108.1 (A)
RAIL_3V3: Q4.2 (D)
TRIP_ANY: D102.1 (K)
TRIP_LOOP_3V3: D102.2 (A), J102.5, U111.1 (OUT)

Notes on the sheet:
CC loop, 3V3 rail -- OPA2277 + 1x IRLZ44N + Kelvin shunt + INA181/TLV7011 trip-watch; CEC_CONN_1x8 harness-boundary connector (split-arch readiness)
3V3 CC loop. Harness-boundary CEC_CONN_1x8 (split-arch readiness, README.md): pins 1-5 real, 6-8 spare. De-gate is a REGULATED-to-zero soft-kill (AND on the RAW pre-filter PWM, before the RC) backed by R_PD's hard gate pulldown. Shunt Kelvin taps are a PCB-layout-time concern (R_2512 land, platform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
