nathanfraske/CEC-Platform/testers/tester-standard/04d-loop-5vsb.kicad_sch

## KiCad design testers/tester-standard/04d-loop-5vsb.kicad_sch (2026-07-17)

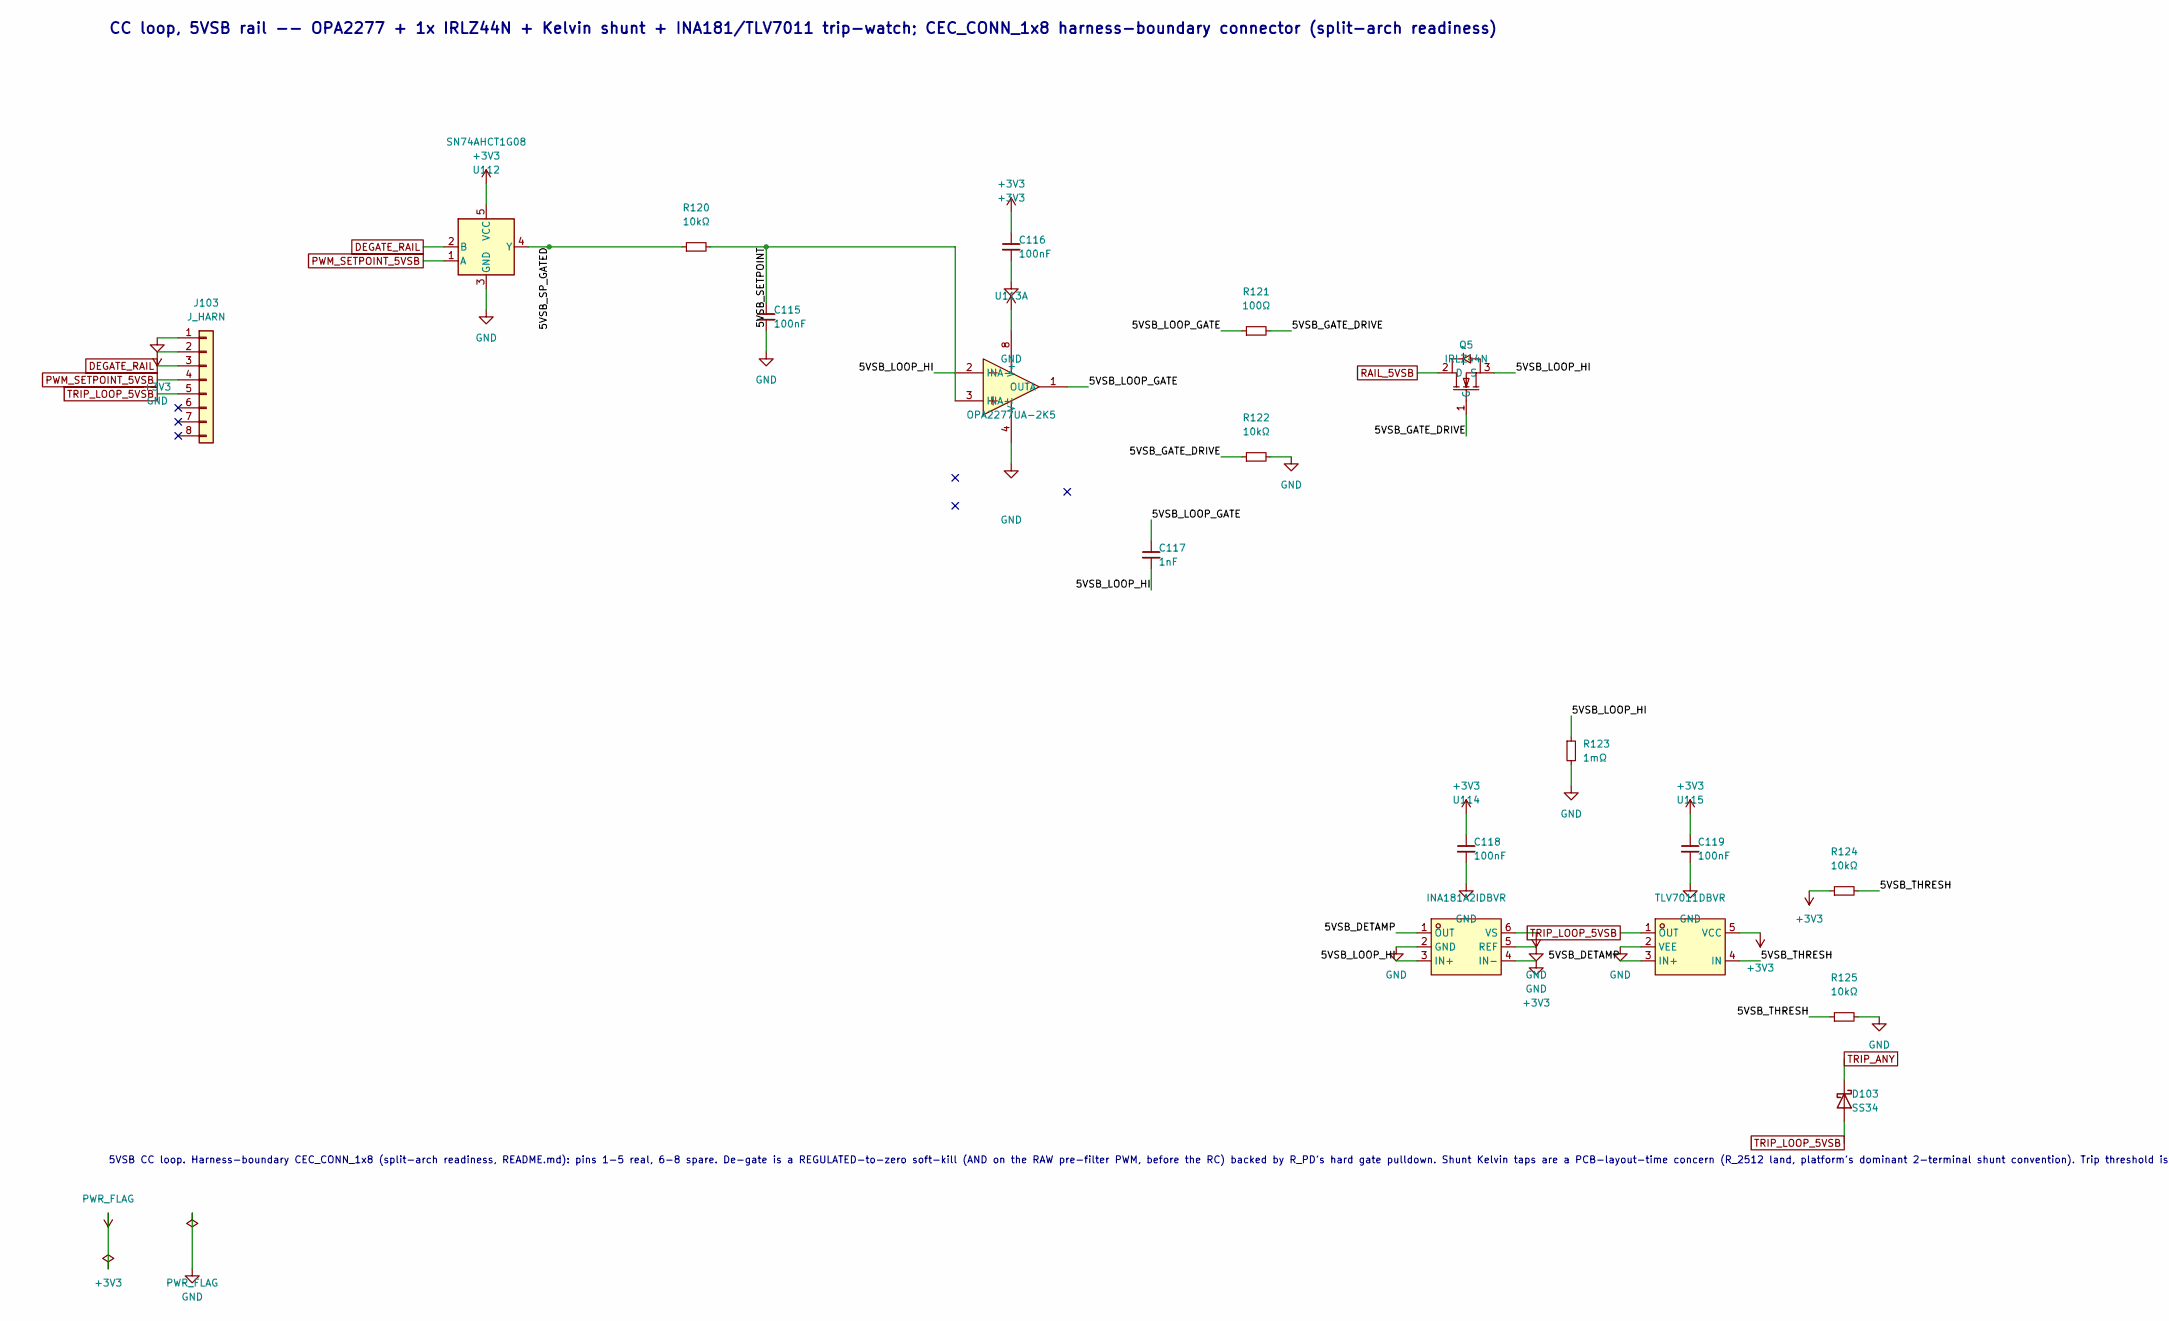
[picture p44: schematic 04d-loop-5vsb.kicad_sch, part in row 1, column 1]

Parts:
C115, C116, C118, C119: 100nF; C_0402_1005Metric
C117: 1nF; C_0402_1005Metric
D103: SS34; D_SOD-323
J103: J_HARN; PinHeader_1x08_P2.54mm_Vertical
Q5: IRLZ44N; TO-220-3_L10.2-W4.5-P2.54-L
R120, R122, R124, R125: 10kΩ; R_0402_1005Metric
R121: 100Ω; R_0402_1005Metric
R123: 1mΩ; R_0402_1005Metric; MPN CSS2H-2512R-1L00F; LCSC C4175647
U112: SN74AHCT1G08; SOT-23-5; MPN SN74AHCT1G08DBVR
U113: OPA2277UA-2K5; SOIC-8_L5.0-W4.0-P1.27-LS6.0-BL; MPN OPA2277UA-2K5; LCSC C24460
U114: INA181A2IDBVR; SOT-23-6; MPN INA181A2IDBVR; LCSC C2058784
U115: TLV7011DBVR; SOT-23-5; MPN TLV7011DBVR; LCSC C702117

Connections:
5VSB_DETAMP: U114.1 (OUT), U115.3 (IN+)
5VSB_GATE_DRIVE: Q5.1 (G), R121.2, R122.1
5VSB_LOOP_GATE: C117.1, R121.1, U113.1 (OUTA)
5VSB_LOOP_HI: C117.2, Q5.3 (S), R123.1, U113.2 (INA-), U114.3 (IN+)
5VSB_SETPOINT: C115.1, R120.2, U113.3 (INA+)
5VSB_SP_GATED: R120.1, U112.4 (Y)
5VSB_THRESH: R124.2, R125.1, U115.4 (IN)
+3V3: C116.1, C118.1, C119.1, J103.2, R124.1, U112.5 (VCC), U113.8 (V+), U114.6 (VS), U115.5 (VCC)
DEGATE_RAIL: J103.3, U112.2 (B)
GND: C115.2, C116.2, C118.2, C119.2, J103.1, R122.2, R123.2, R125.2, U112.3 (GND), U113.4 (V-), U114.2 (GND), U114.4 (IN-), U114.5 (REF), U115.2 (VEE)
PWM_SETPOINT_5VSB: J103.4, U112.1 (A)
RAIL_5VSB: Q5.2 (D)
TRIP_ANY: D103.1 (K)
TRIP_LOOP_5VSB: D103.2 (A), J103.5, U115.1 (OUT)

Notes on the sheet:
CC loop, 5VSB rail -- OPA2277 + 1x IRLZ44N + Kelvin shunt + INA181/TLV7011 trip-watch; CEC_CONN_1x8 harness-boundary connector (split-arch readiness)
5VSB CC loop. Harness-boundary CEC_CONN_1x8 (split-arch readiness, README.md): pins 1-5 real, 6-8 spare. De-gate is a REGULATED-to-zero soft-kill (AND on the RAW pre-filter PWM, before the RC) backed by R_PD's hard gate pulldown. Shunt Kelvin taps are a PCB-layout-time concern (R_2512 land, platfor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
