nathanfraske/CEC-Platform/testers/tester-standard/05a-bank-12v.kicad_sch

## KiCad design testers/tester-standard/05a-bank-12v.kicad_sch (2026-07-17)

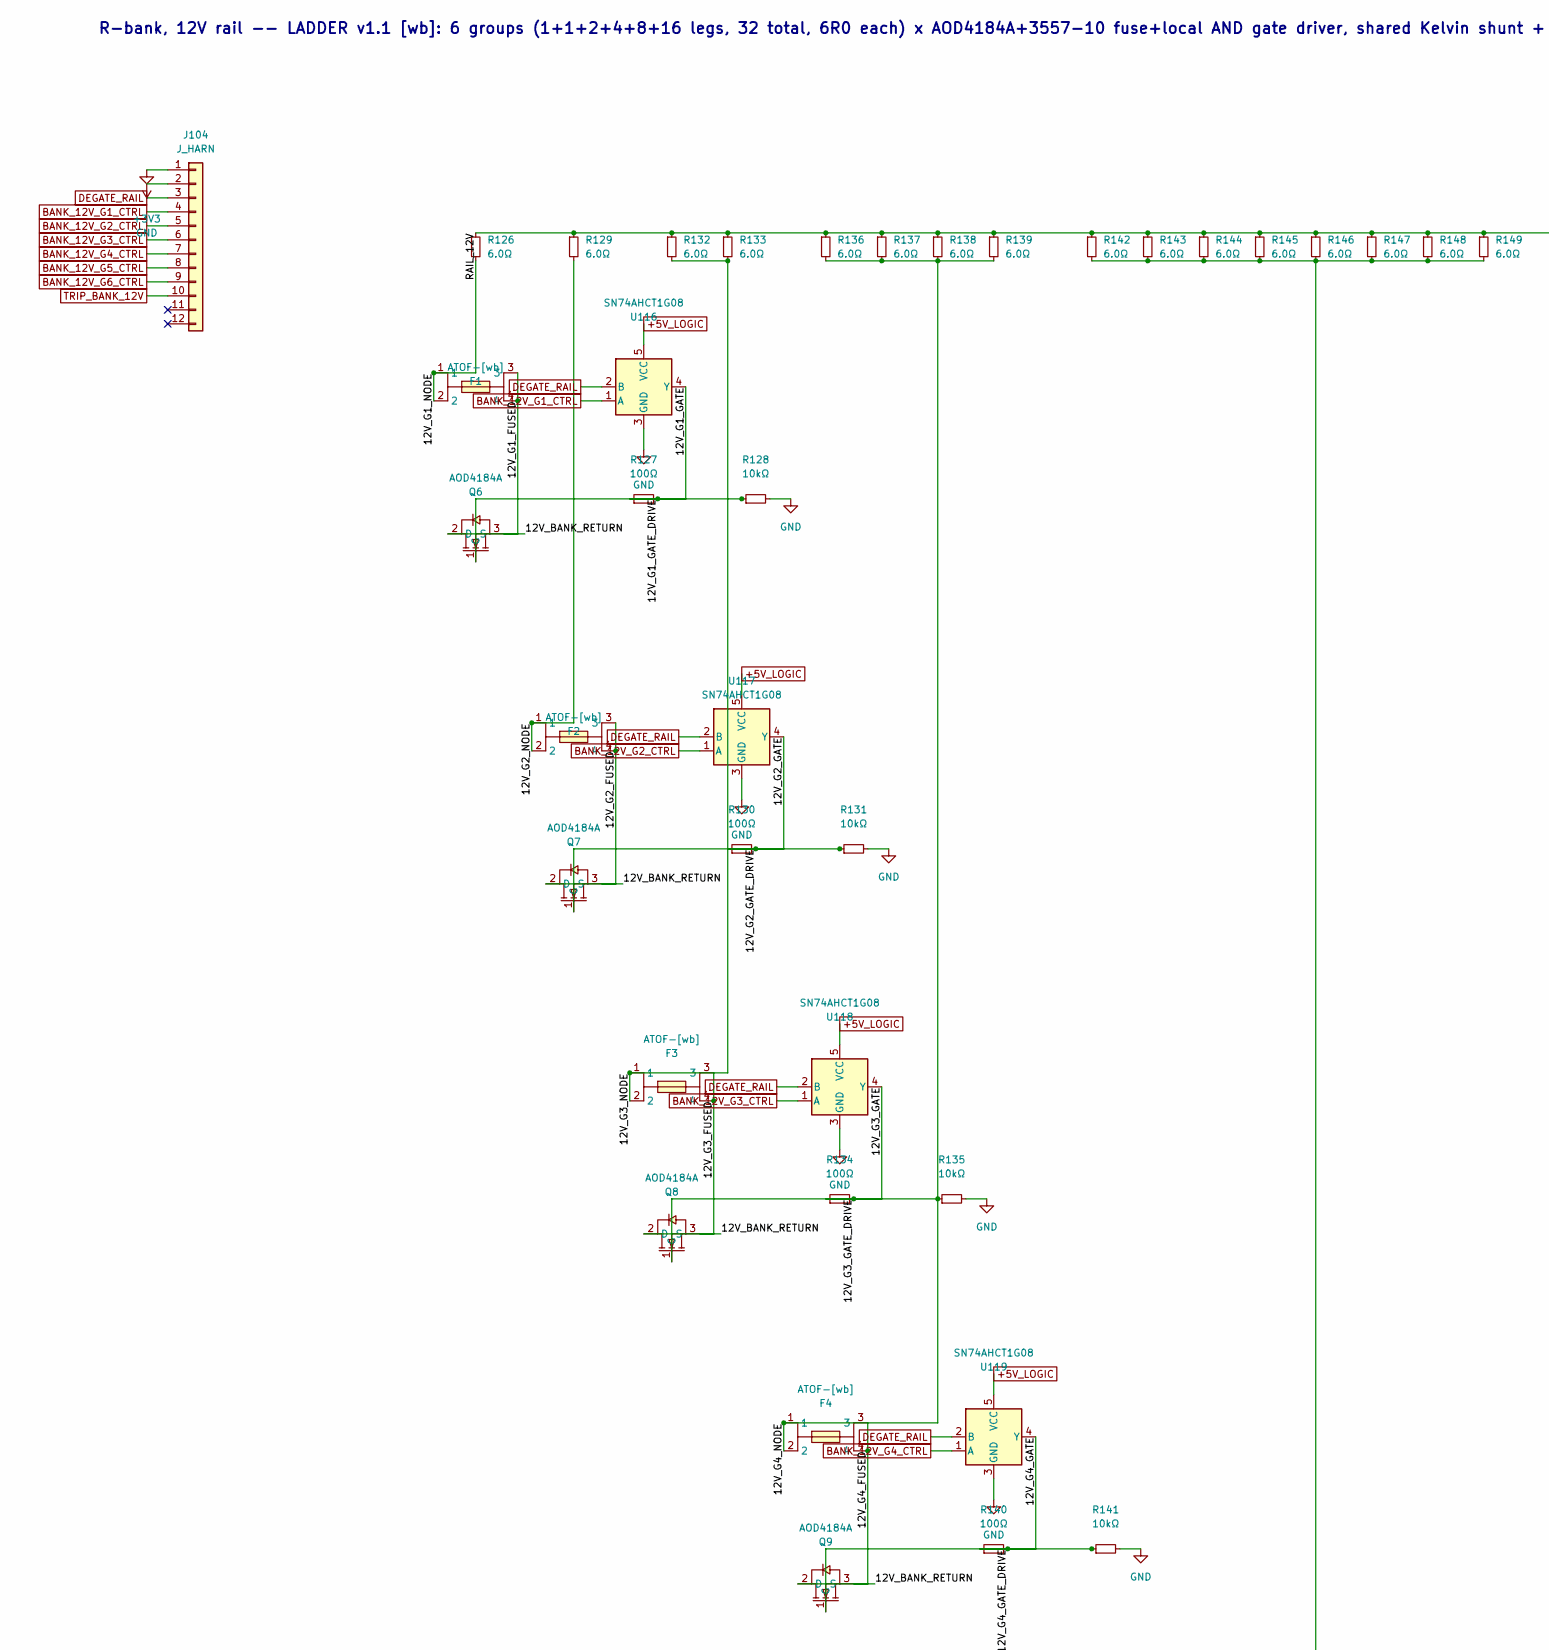
[picture p45: schematic 05a-bank-12v.kicad_sch, part in row 1, column 1]

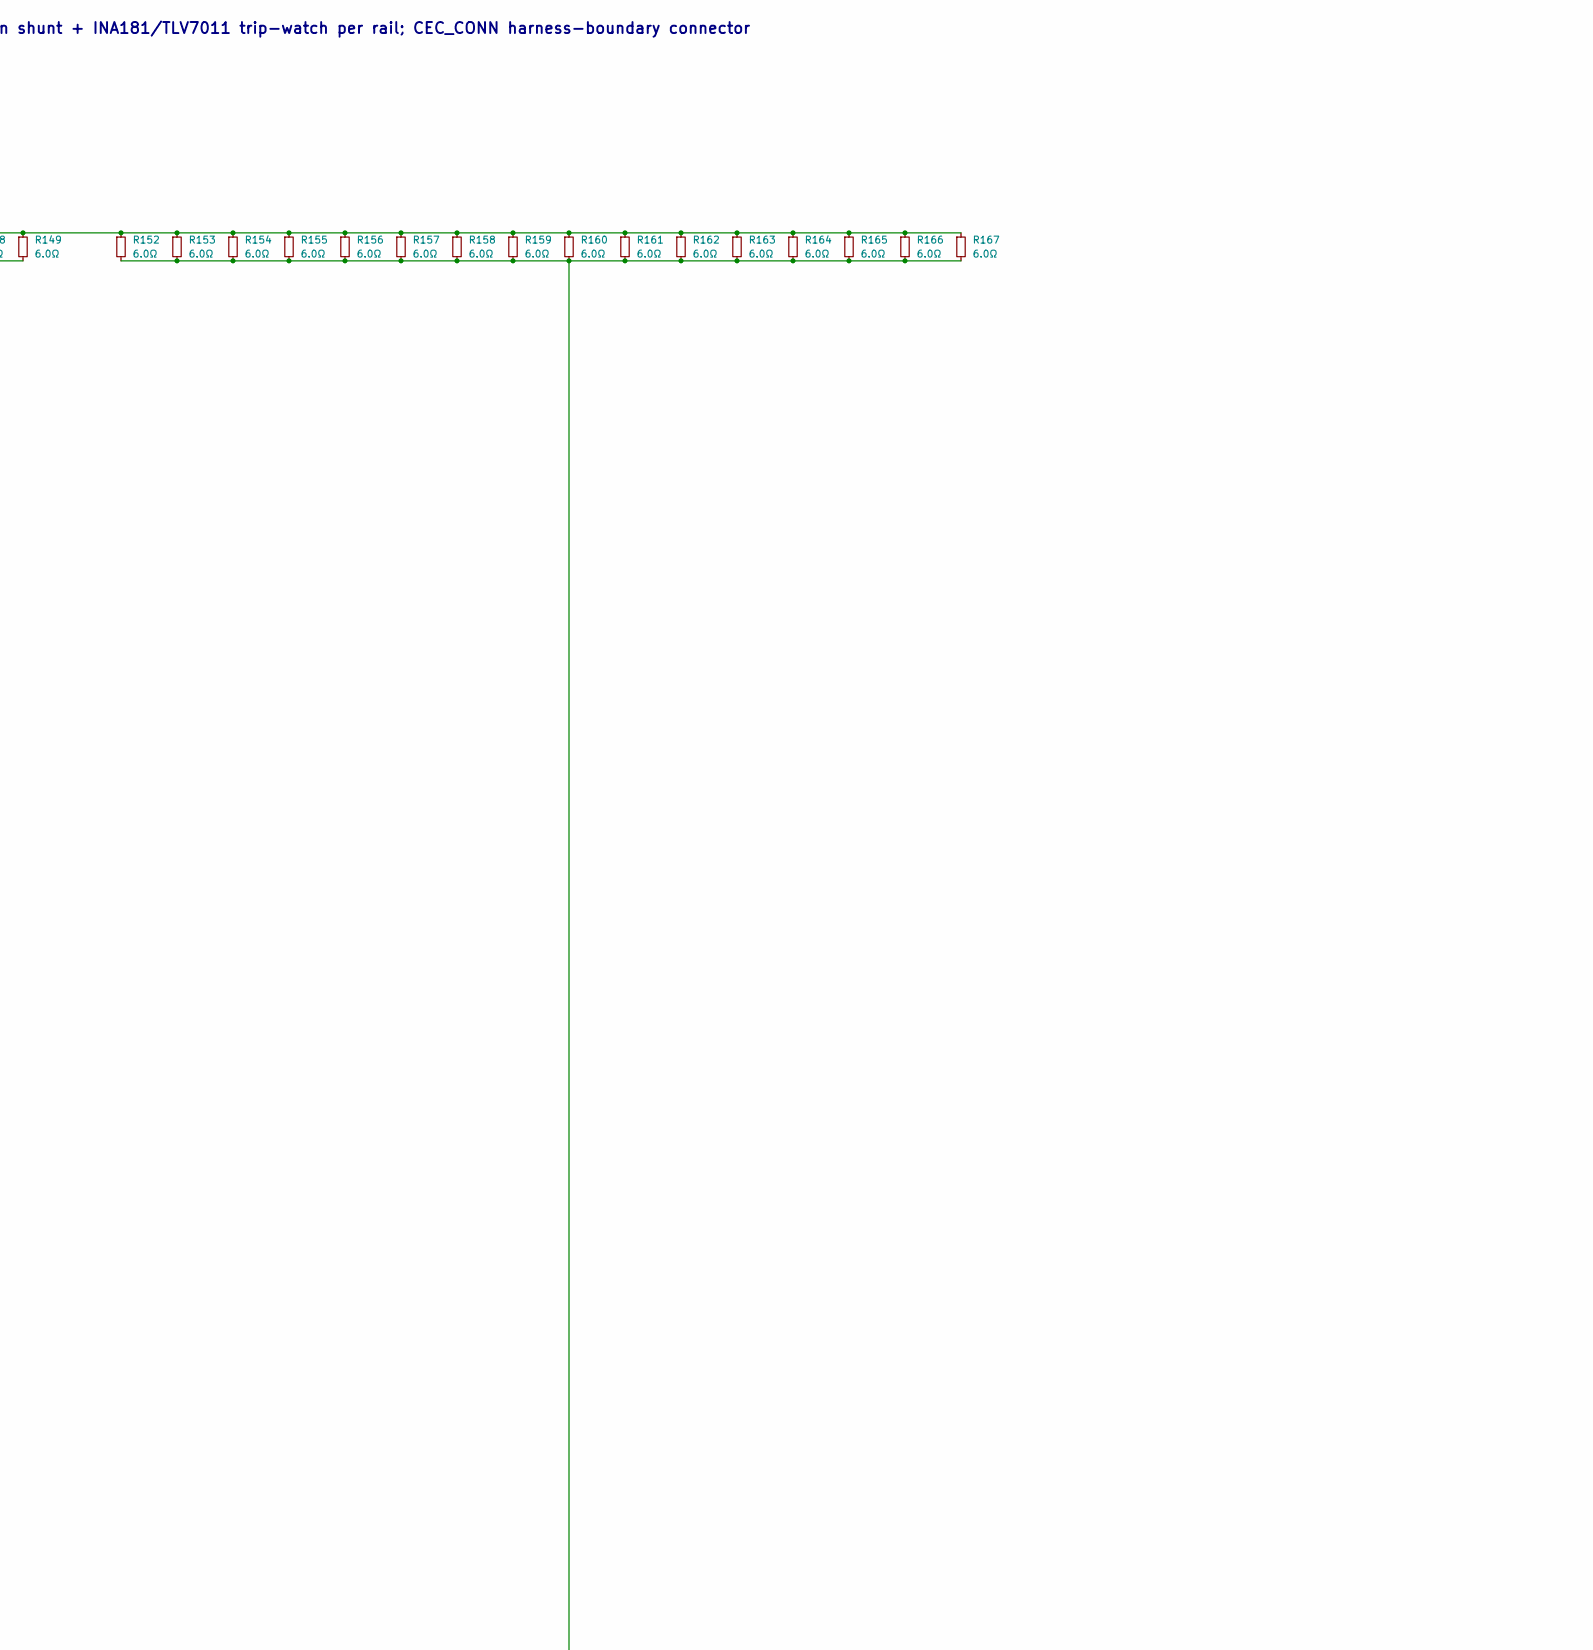
[picture p46: schematic 05a-bank-12v.kicad_sch, part in row 1, column 2]

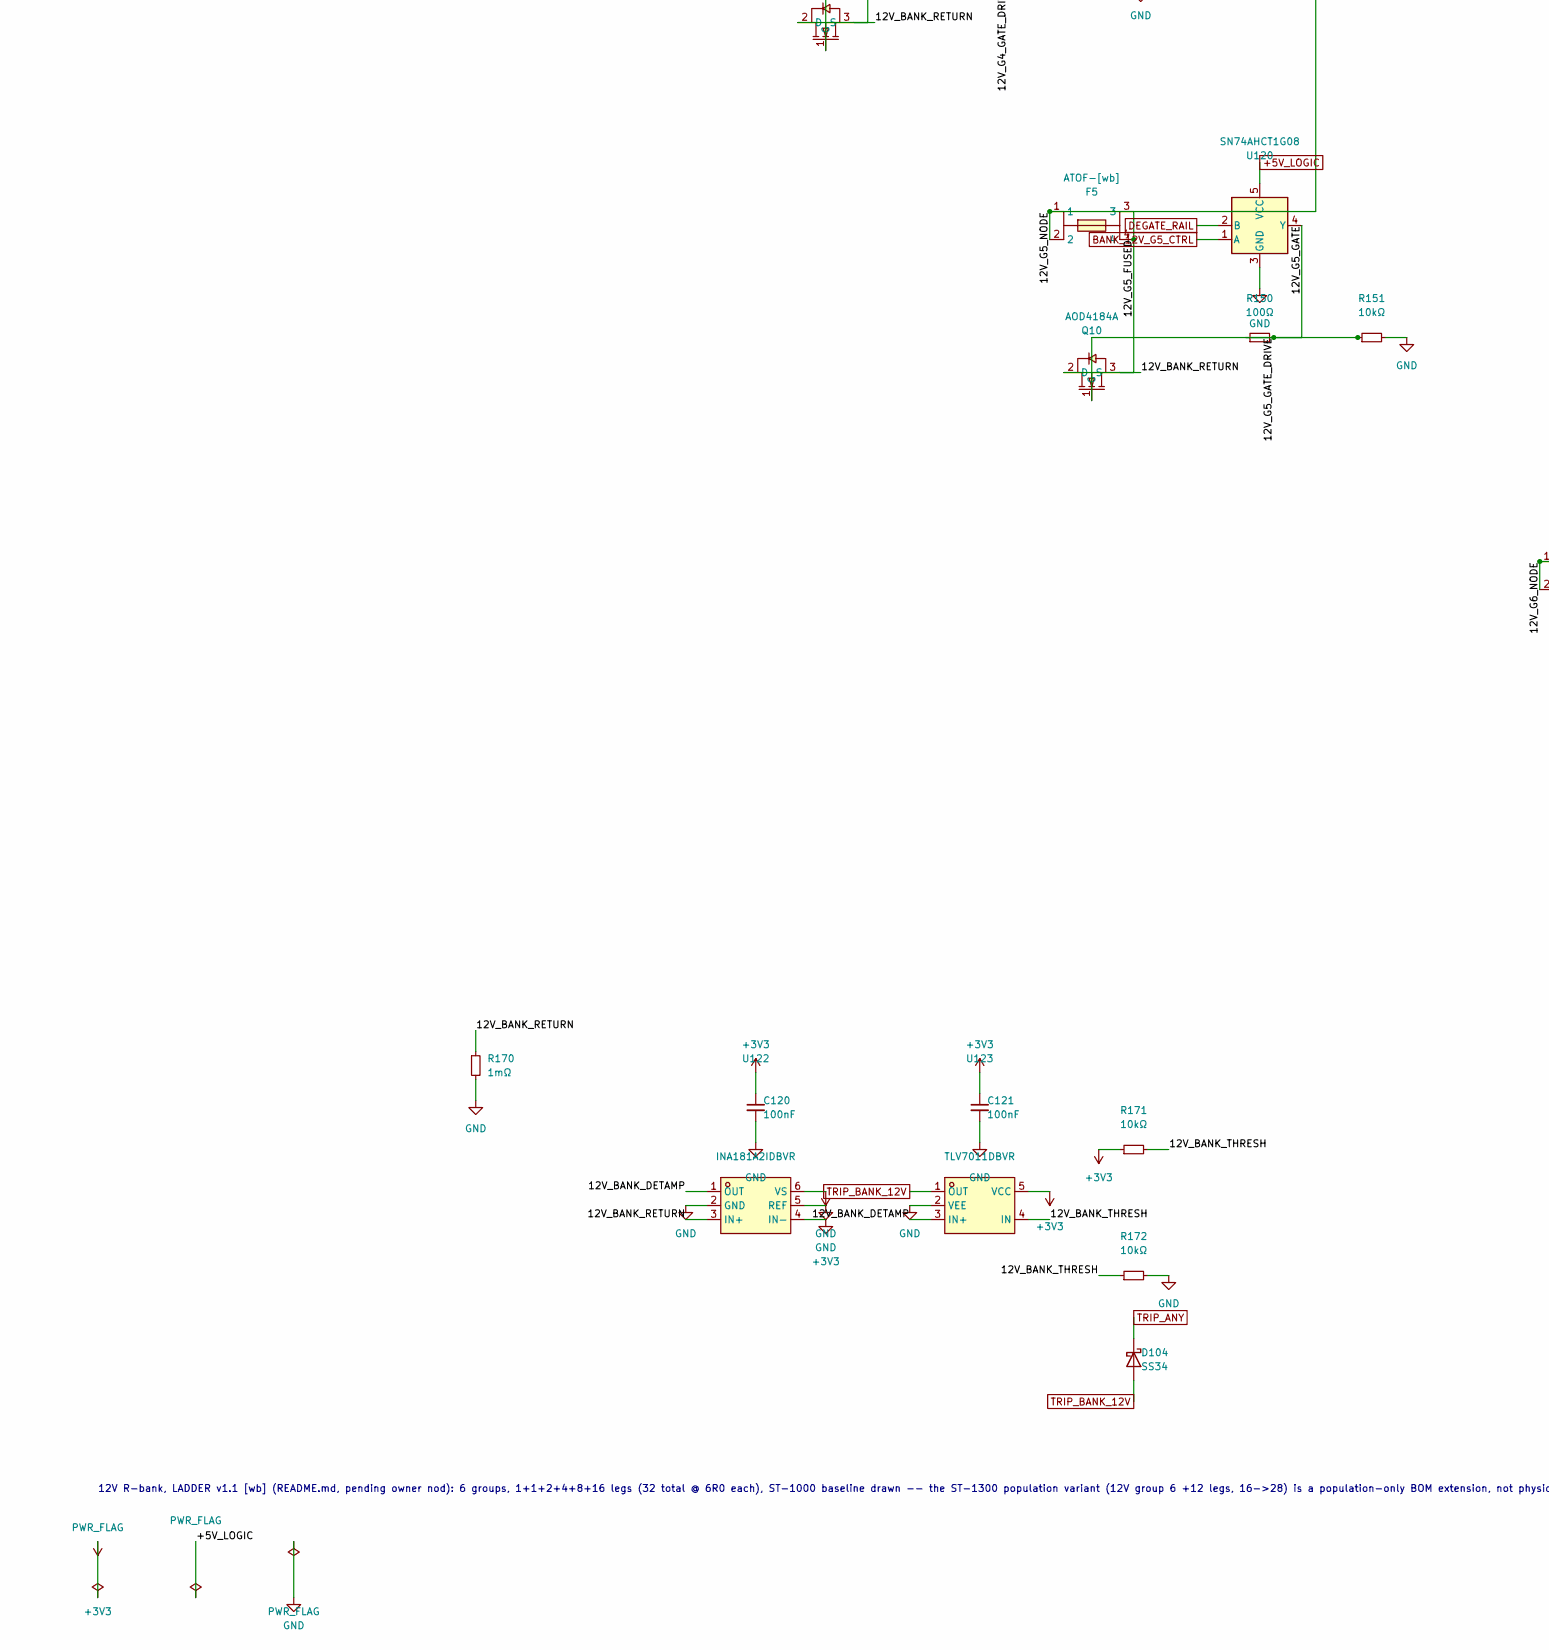
[picture p47: schematic 05a-bank-12v.kicad_sch, part in row 2, column 1]

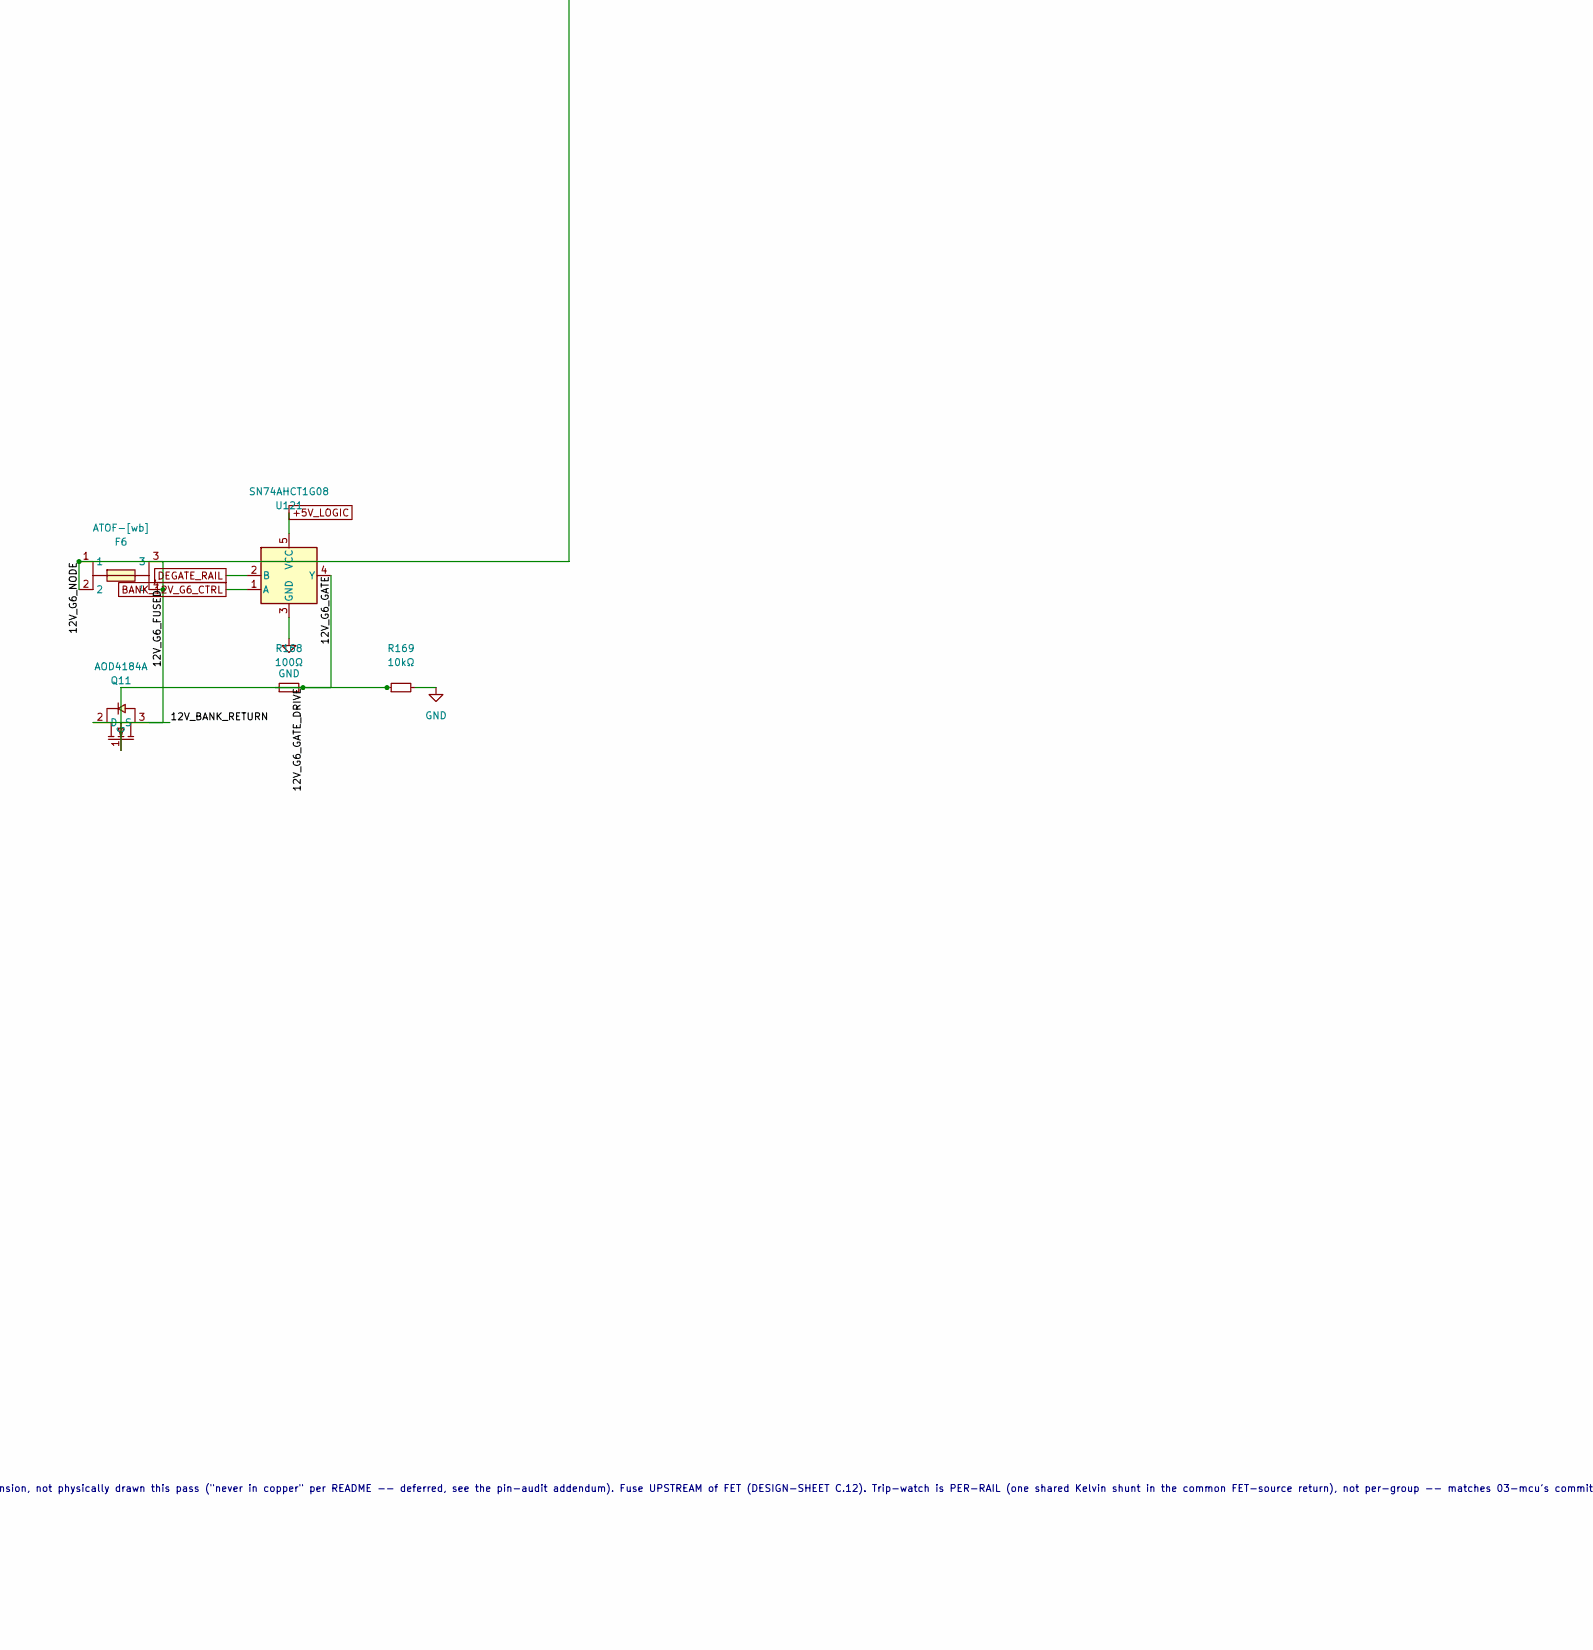
[picture p48: schematic 05a-bank-12v.kicad_sch, part in row 2, column 2]

Parts:
C120, C121: 100nF; C_0402_1005Metric
D104: SS34; D_SOD-323
F1, F2, F3, F4, F5, F6: ATOF-[wb]; FUSE-TH_4P-L19.8-W6.7_3557-2; MPN 3557-10; LCSC C3205403
J104: J_HARN; PinHeader_1x12_P2.54mm_Vertical
Q6, Q7, Q8, Q9, Q10, Q11: AOD4184A; TO-252-2_L6.6-W6.1-P4.57-LS9.9-TL-CW; MPN AOD4184A; LCSC C99124
R126, R129, R132, R133, R136, R137, R138, R139, R142, R143, R144, R145, R146, R147, R148, R149, R152, R153, R154, R155, R156, R157, R158, R159, R160, R161, R162, R163, R164, R165, R166, R167: 6.0Ω; R_0402_1005Metric; MPN HoRX-50W-class [wb exact LCSC line pend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
R127, R130, R134, R140, R150, R168: 100Ω; R_0402_1005Metric
R128, R131, R135, R141, R151, R169, R171, R172: 10kΩ; R_0402_1005Metric
R170: 1mΩ; R_0402_1005Metric; MPN CSS2H-2512R-1L00F; LCSC C4175647
U116, U117, U118, U119, U120, U121: SN74AHCT1G08; SOT-23-5; MPN SN74AHCT1G08DBVR
U122: INA181A2IDBVR; SOT-23-6; MPN INA181A2IDBVR; LCSC C2058784
U123: TLV7011DBVR; SOT-23-5; MPN TLV7011DBVR; LCSC C702117

Connections:
12V_BANK_DETAMP: U122.1 (OUT), U123.3 (IN+)
12V_BANK_RETURN: Q6.3 (S), Q7.3 (S), Q8.3 (S), Q9.3 (S), Q10.3 (S), Q11.3 (S), R170.1, U122.3 (IN+)
12V_BANK_THRESH: R171.2, R172.1, U123.4 (IN)
12V_G1_FUSED: F1.3, F1.4, Q6.2 (D)
12V_G1_GATE: Q6.1 (G), R127.1, R127.2, R128.1, U116.4 (Y)
12V_G1_NODE: F1.1, F1.2, R126.2
12V_G2_FUSED: F2.3, F2.4, Q7.2 (D)
12V_G2_GATE: Q7.1 (G), R130.1, R130.2, R131.1, U117.4 (Y)
12V_G2_NODE: F2.1, F2.2, R129.2
12V_G3_FUSED: F3.3, F3.4, Q8.2 (D)
12V_G3_GATE: F4.1, F4.2, Q8.1 (G), R134.1, R134.2, R135.1, R136.2, R137.2, R138.2, R139.2, U118.4 (Y)
12V_G3_NODE: F3.1, F3.2, R132.2, R133.2
12V_G4_FUSED: F4.3, F4.4, Q9.2 (D)
12V_G4_GATE: Q9.1 (G), R140.1, R140.2, R141.1, U119.4 (Y)
12V_G5_FUSED: F5.3, F5.4, Q10.2 (D)
12V_G5_GATE: Q10.1 (G), R150.1, R150.2, R151.1, U120.4 (Y)
12V_G5_NODE: F5.1, F5.2, R142.2, R143.2, R144.2, R145.2, R146.2, R147.2, R148.2, R149.2
12V_G6_FUSED: F6.3, F6.4, Q11.2 (D)
12V_G6_GATE: Q11.1 (G), R168.1, R168.2, R169.1, U121.4 (Y)
12V_G6_NODE: F6.1, F6.2, R152.2, R153.2, R154.2, R155.2, R156.2, R157.2, R158.2, R159.2, R160.2, R161.2, R162.2, R163.2, R164.2, R165.2, R166.2, R167.2
+3V3: C120.1, C121.1, J104.2, R171.1, U122.6 (VS), U123.5 (VCC)
+5V_LOGIC: U116.5 (VCC), U117.5 (VCC), U118.5 (VCC), U119.5 (VCC), U120.5 (VCC), U121.5 (VCC)
BANK_12V_G1_CTRL: J104.4, U116.1 (A)
BANK_12V_G2_CTRL: J104.5, U117.1 (A)
BANK_12V_G3_CTRL: J104.6, U118.1 (A)
BANK_12V_G4_CTRL: J104.7, U119.1 (A)
BANK_12V_G5_CTRL: J104.8, U120.1 (A)
BANK_12V_G6_CTRL: J104.9, U121.1 (A)
DEGATE_RAIL: J104.3, U116.2 (B), U117.2 (B), U118.2 (B), U119.2 (B), U120.2 (B), U121.2 (B)
GND: C120.2, C121.2, J104.1, R128.2, R131.2, R135.2, R141.2, R151.2, R169.2, R170.2, R172.2, U116.3 (GND), U117.3 (GND), U118.3 (GND), U119.3 (GND), U120.3 (GND), U121.3 (GND), U122.2 (GND), U122.4 (IN-), U122.5 (REF), U123.2 (VEE)
RAIL_12V: R126.1, R129.1, R132.1, R133.1, R136.1, R137.1, R138.1, R139.1, R142.1, R143.1, R144.1, R145.1, R146.1, R147.1, R148.1, R149.1, R152.1, R153.1, R154.1, R155.1, R156.1, R157.1, R158.1, R159.1, R160.1, R161.1, R162.1, R163.1, R164.1, R165.1, R166.1, R167.1
TRIP_ANY: D104.1 (K)
TRIP_BANK_12V: D104.2 (A), J104.10, U123.1 (OUT)

Notes on the sheet:
R-bank, 12V rail -- LADDER v1.1 [wb]: 6 groups (1+1+2+4+8+16 legs, 32 total, 6R0 each) x AOD4184A+3557-10 fuse+local AND gate driver, shared Kelvin shunt + INA181/TLV7011 trip-watch per rail; CEC_CONN harness-boundary connector
12V R-bank, LADDER v1.1 [wb] (README.md, pending owner nod): 6 groups, 1+1+2+4+8+16 legs (32 total @ 6R0 each), ST-1000 baseline drawn -- the ST-1300 population variant (12V group 6 +12 legs, 16->28) is a population-only BOM extension, not physically drawn this pass ("never in copper" per README --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
