nathanfraske/CEC-Platform/testers/tester-standard/05b-bank-5v.kicad_sch

## KiCad design testers/tester-standard/05b-bank-5v.kicad_sch (2026-07-17)

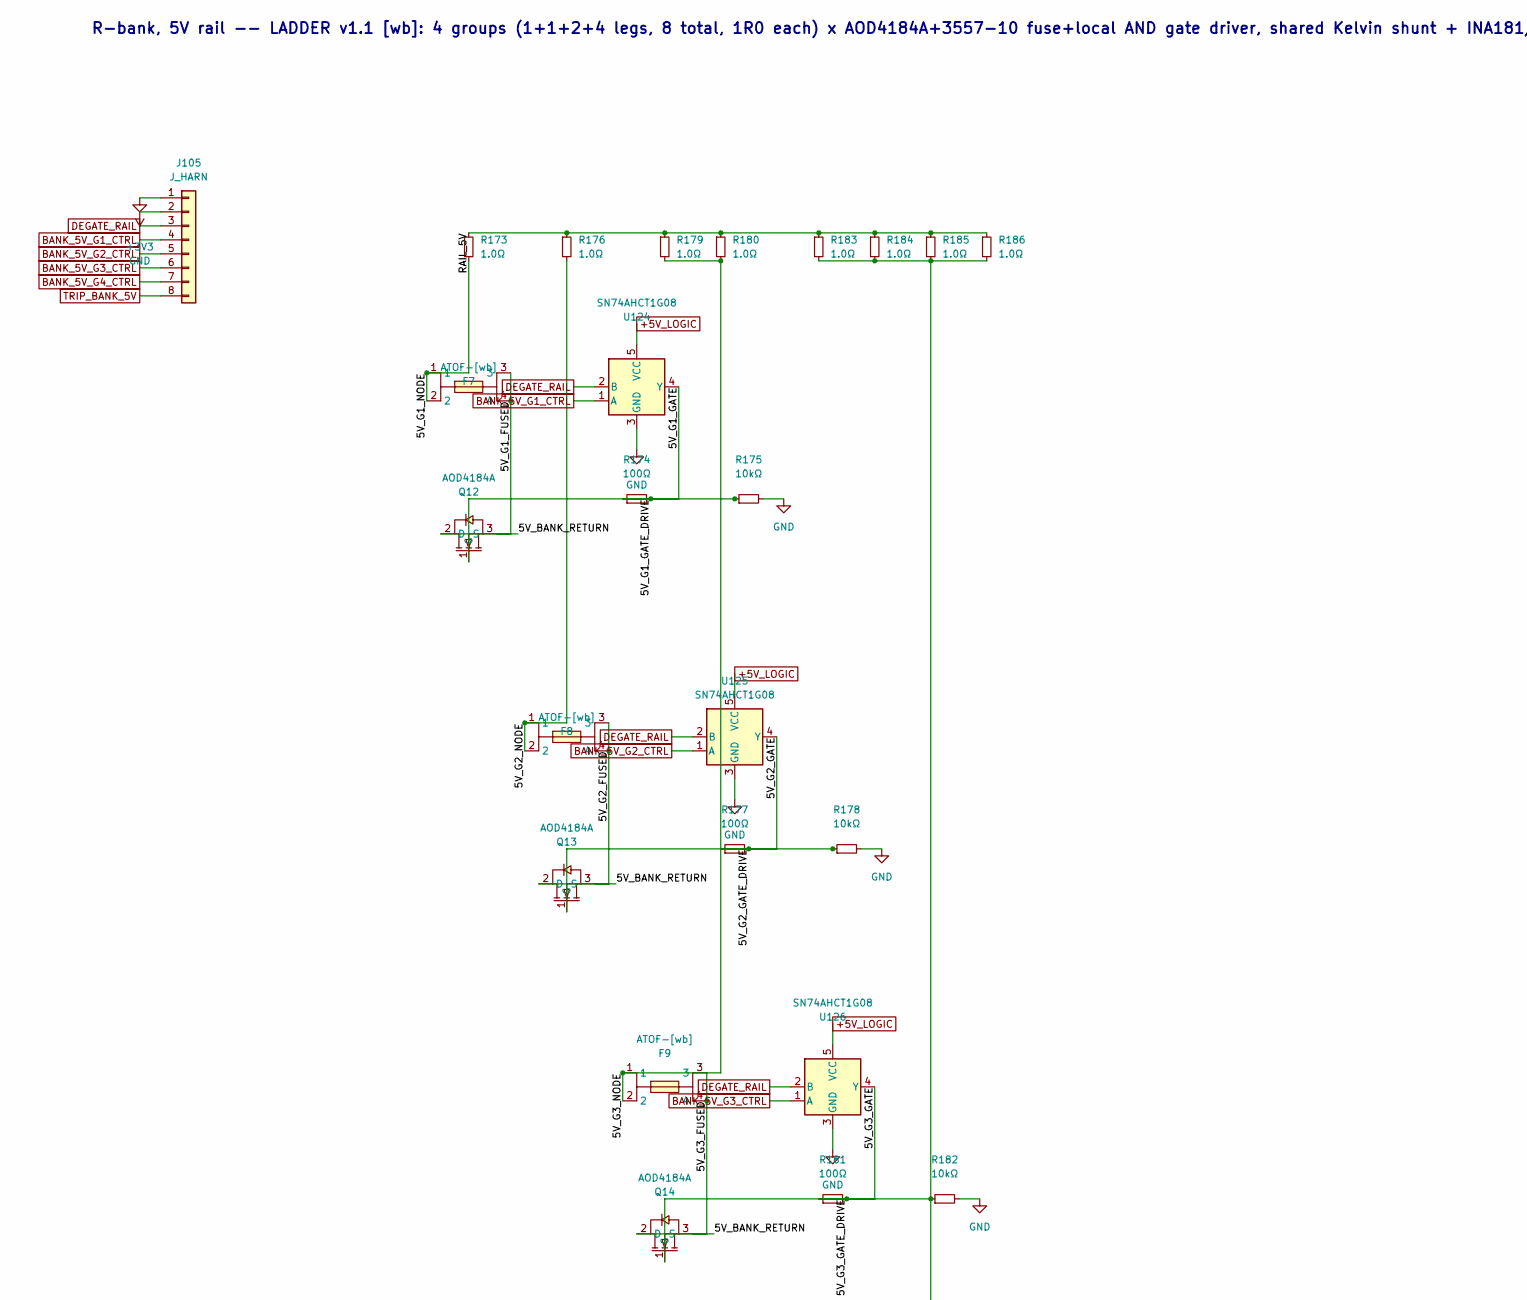
[picture p49: schematic 05b-bank-5v.kicad_sch, part in row 1, column 1]

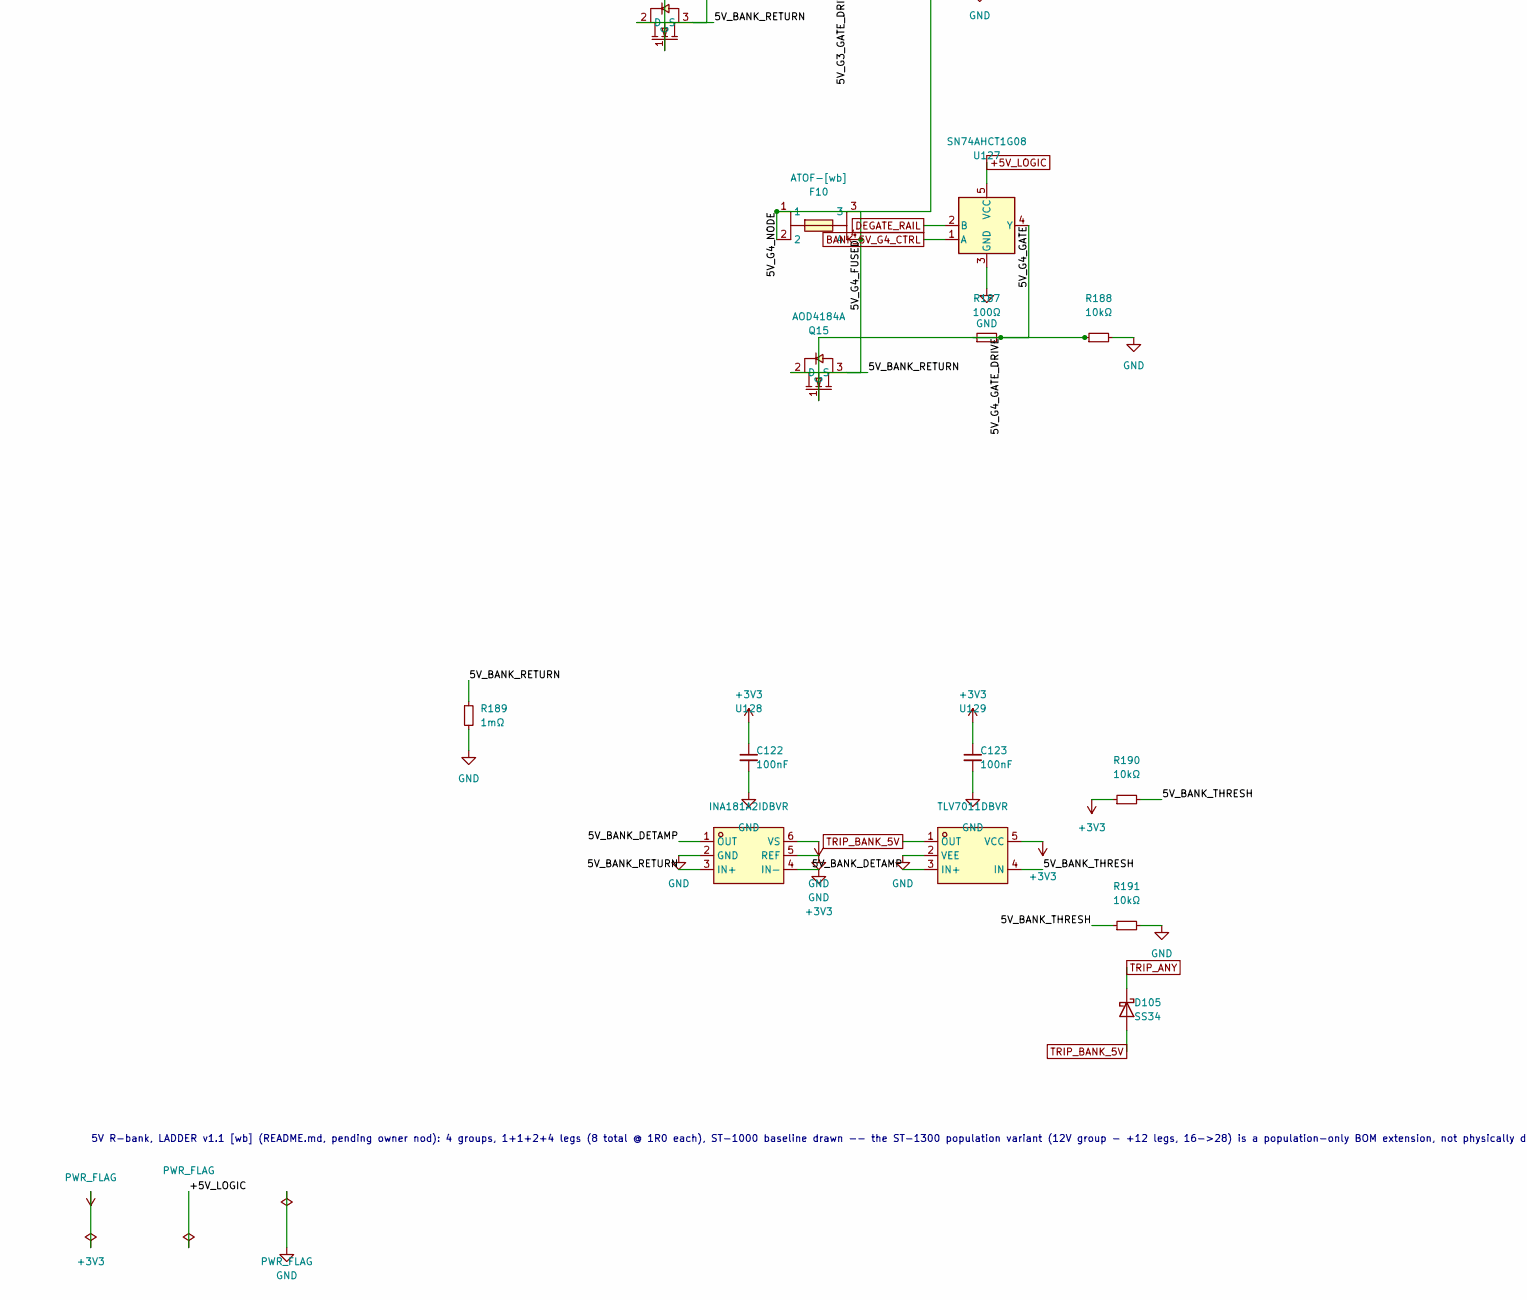
[picture p50: schematic 05b-bank-5v.kicad_sch, part in row 2, column 1]

Parts:
C122, C123: 100nF; C_0402_1005Metric
D105: SS34; D_SOD-323
F7, F8, F9, F10: ATOF-[wb]; FUSE-TH_4P-L19.8-W6.7_3557-2; MPN 3557-10; LCSC C3205403
J105: J_HARN; PinHeader_1x08_P2.54mm_Vertical
Q12, Q13, Q14, Q15: AOD4184A; TO-252-2_L6.6-W6.1-P4.57-LS9.9-TL-CW; MPN AOD4184A; LCSC C99124
R173, R176, R179, R180, R183, R184, R185, R186: 1.0Ω; R_0402_1005Metric; MPN HoRX-50W-class [wb exact LCSC line pend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
R174, R177, R181, R187: 100Ω; R_0402_1005Metric
R175, R178, R182, R188, R190, R191: 10kΩ; R_0402_1005Metric
R189: 1mΩ; R_0402_1005Metric; MPN CSS2H-2512R-1L00F; LCSC C4175647
U124, U125, U126, U127: SN74AHCT1G08; SOT-23-5; MPN SN74AHCT1G08DBVR
U128: INA181A2IDBVR; SOT-23-6; MPN INA181A2IDBVR; LCSC C2058784
U129: TLV7011DBVR; SOT-23-5; MPN TLV7011DBVR; LCSC C702117

Connections:
5V_BANK_DETAMP: U128.1 (OUT), U129.3 (IN+)
5V_BANK_RETURN: Q12.3 (S), Q13.3 (S), Q14.3 (S), Q15.3 (S), R189.1, U128.3 (IN+)
5V_BANK_THRESH: R190.2, R191.1, U129.4 (IN)
5V_G1_FUSED: F7.3, F7.4, Q12.2 (D)
5V_G1_GATE: Q12.1 (G), R174.1, R174.2, R175.1, U124.4 (Y)
5V_G1_NODE: F7.1, F7.2, R173.2
5V_G2_FUSED: F8.3, F8.4, Q13.2 (D)
5V_G2_GATE: Q13.1 (G), R177.1, R177.2, R178.1, U125.4 (Y)
5V_G2_NODE: F8.1, F8.2, R176.2
5V_G3_FUSED: F9.3, F9.4, Q14.2 (D)
5V_G3_GATE: F10.1, F10.2, Q14.1 (G), R181.1, R181.2, R182.1, R183.2, R184.2, R185.2, R186.2, U126.4 (Y)
5V_G3_NODE: F9.1, F9.2, R179.2, R180.2
5V_G4_FUSED: F10.3, F10.4, Q15.2 (D)
5V_G4_GATE: Q15.1 (G), R187.1, R187.2, R188.1, U127.4 (Y)
+3V3: C122.1, C123.1, J105.2, R190.1, U128.6 (VS), U129.5 (VCC)
+5V_LOGIC: U124.5 (VCC), U125.5 (VCC), U126.5 (VCC), U127.5 (VCC)
BANK_5V_G1_CTRL: J105.4, U124.1 (A)
BANK_5V_G2_CTRL: J105.5, U125.1 (A)
BANK_5V_G3_CTRL: J105.6, U126.1 (A)
BANK_5V_G4_CTRL: J105.7, U127.1 (A)
DEGATE_RAIL: J105.3, U124.2 (B), U125.2 (B), U126.2 (B), U127.2 (B)
GND: C122.2, C123.2, J105.1, R175.2, R178.2, R182.2, R188.2, R189.2, R191.2, U124.3 (GND), U125.3 (GND), U126.3 (GND), U127.3 (GND), U128.2 (GND), U128.4 (IN-), U128.5 (REF), U129.2 (VEE)
RAIL_5V: R173.1, R176.1, R179.1, R180.1, R183.1, R184.1, R185.1, R186.1
TRIP_ANY: D105.1 (K)
TRIP_BANK_5V: D105.2 (A), J105.8, U129.1 (OUT)

Notes on the sheet:
R-bank, 5V rail -- LADDER v1.1 [wb]: 4 groups (1+1+2+4 legs, 8 total, 1R0 each) x AOD4184A+3557-10 fuse+local AND gate driver, shared Kelvin shunt + INA181/TLV7011 trip-watch per rail; CEC_CONN harness-boundary connector
5V R-bank, LADDER v1.1 [wb] (README.md, pending owner nod): 4 groups, 1+1+2+4 legs (8 total @ 1R0 each), ST-1000 baseline drawn -- the ST-1300 population variant (12V group - +12 legs, 16->28) is a population-only BOM extension, not physically drawn this pass ("never in copper" per README -- deferr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
