nathanfraske/CEC-Platform/testers/tester-standard/05c-bank-3v3.kicad_sch

## KiCad design testers/tester-standard/05c-bank-3v3.kicad_sch (2026-07-17)

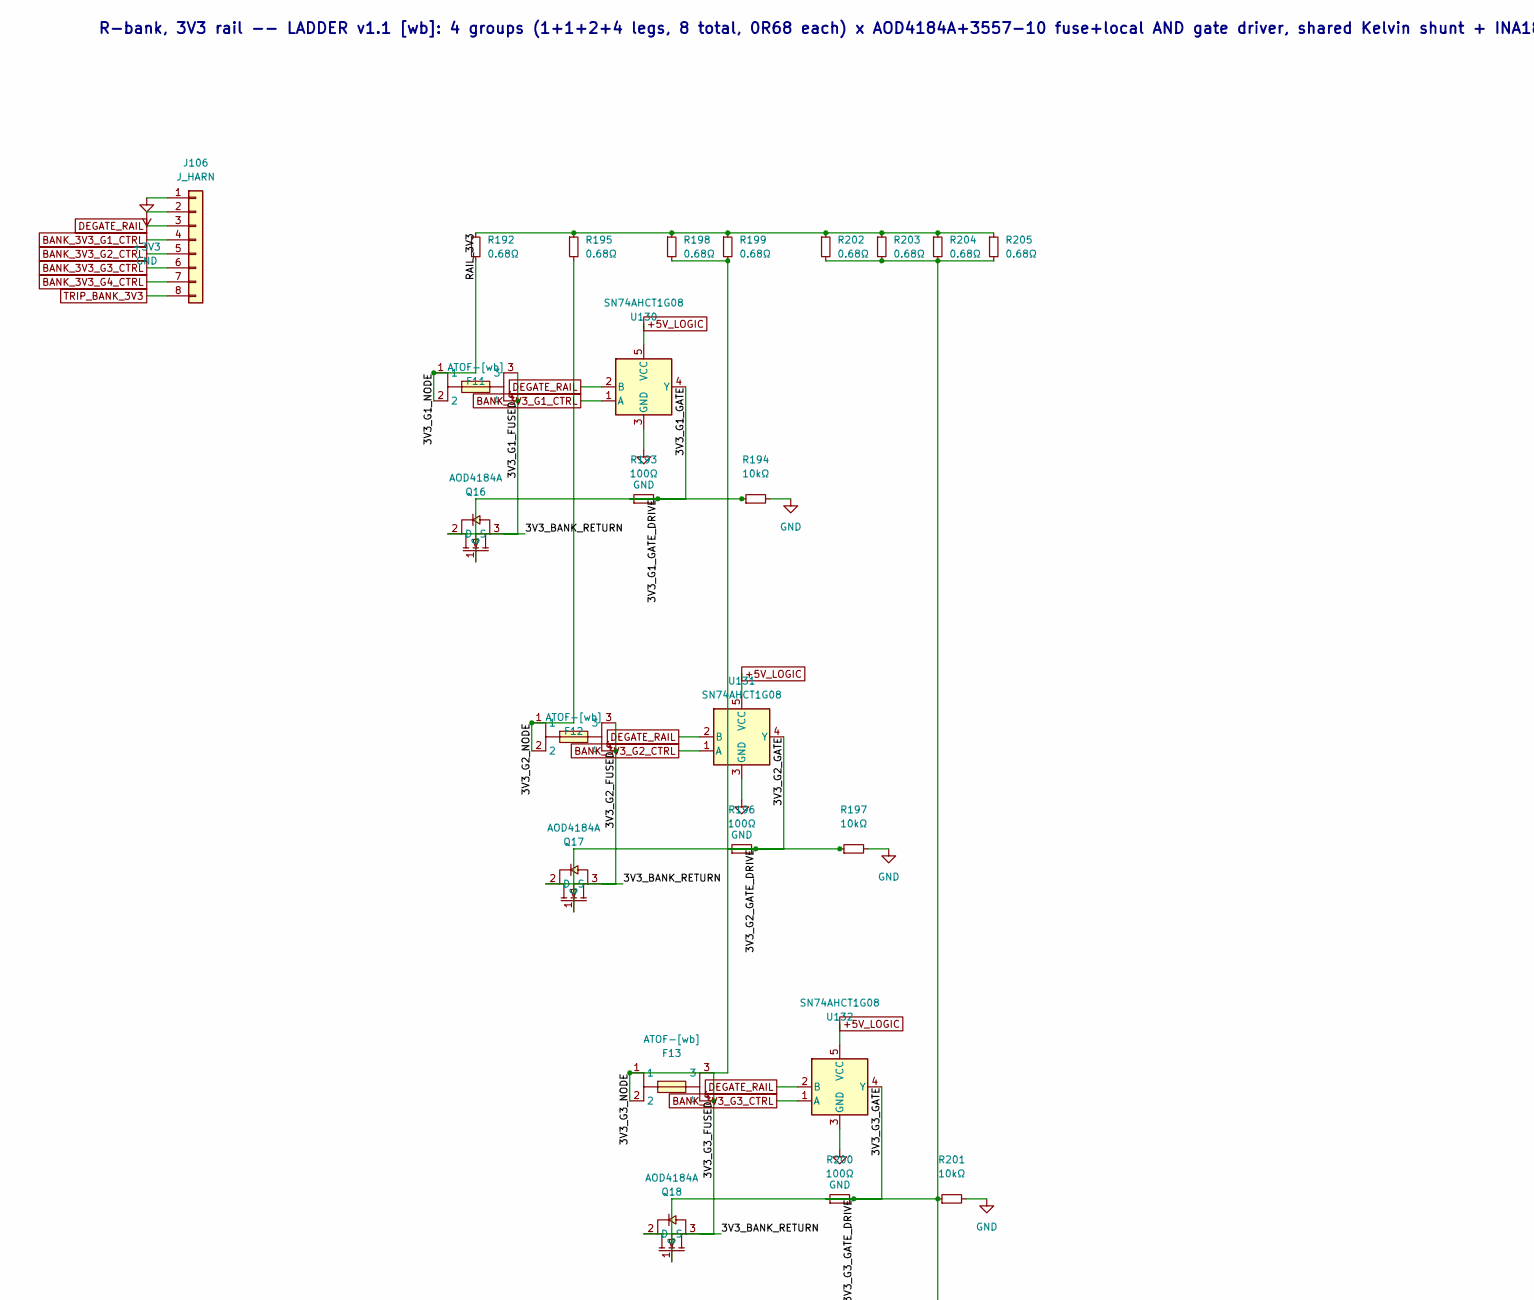
[picture p51: schematic 05c-bank-3v3.kicad_sch, part in row 1, column 1]

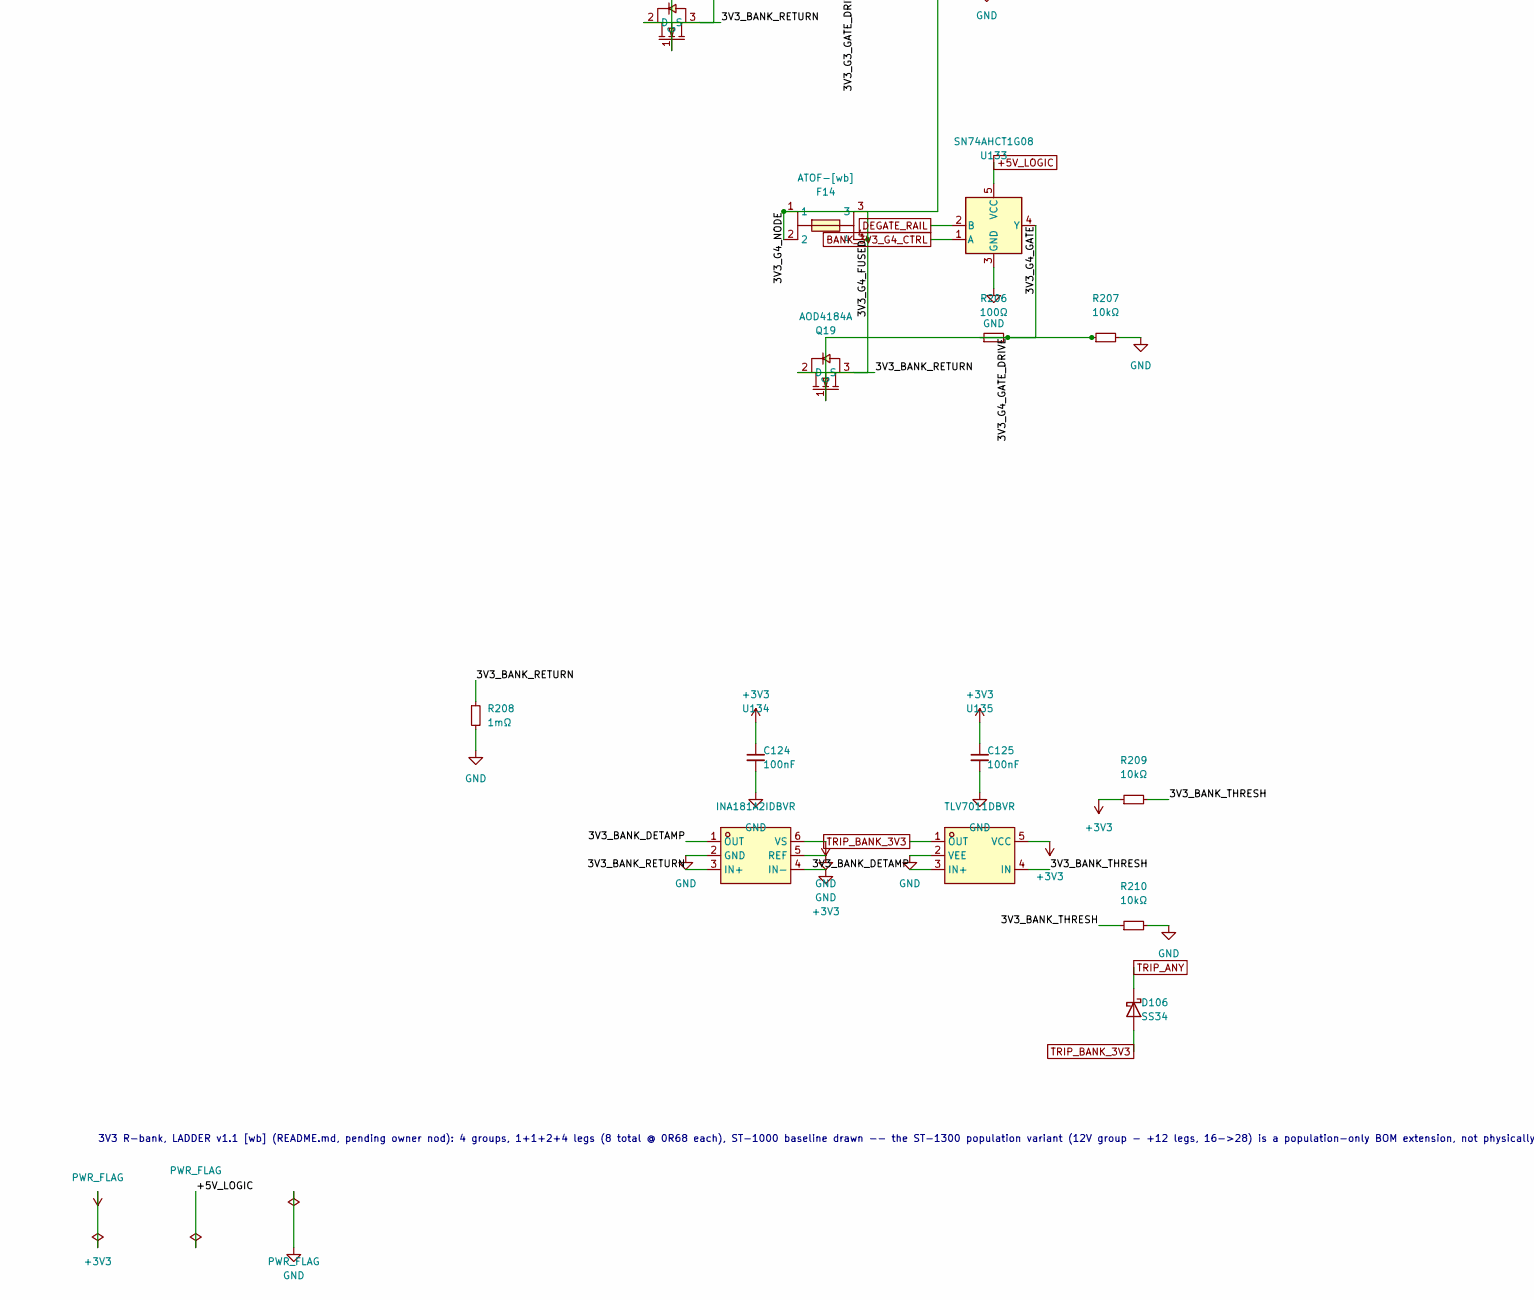
[picture p52: schematic 05c-bank-3v3.kicad_sch, part in row 2, column 1]

Parts:
C124, C125: 100nF; C_0402_1005Metric
D106: SS34; D_SOD-323
F11, F12, F13, F14: ATOF-[wb]; FUSE-TH_4P-L19.8-W6.7_3557-2; MPN 3557-10; LCSC C3205403
J106: J_HARN; PinHeader_1x08_P2.54mm_Vertical
Q16, Q17, Q18, Q19: AOD4184A; TO-252-2_L6.6-W6.1-P4.57-LS9.9-TL-CW; MPN AOD4184A; LCSC C99124
R192, R195, R198, R199, R202, R203, R204, R205: 0.68Ω; R_0402_1005Metric; MPN HoRX-50W-class [wb exact LCSC line pend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
R193, R196, R200, R206: 100Ω; R_0402_1005Metric
R194, R197, R201, R207, R209, R210: 10kΩ; R_0402_1005Metric
R208: 1mΩ; R_0402_1005Metric; MPN CSS2H-2512R-1L00F; LCSC C4175647
U130, U131, U132, U133: SN74AHCT1G08; SOT-23-5; MPN SN74AHCT1G08DBVR
U134: INA181A2IDBVR; SOT-23-6; MPN INA181A2IDBVR; LCSC C2058784
U135: TLV7011DBVR; SOT-23-5; MPN TLV7011DBVR; LCSC C702117

Connections:
3V3_BANK_DETAMP: U134.1 (OUT), U135.3 (IN+)
3V3_BANK_RETURN: Q16.3 (S), Q17.3 (S), Q18.3 (S), Q19.3 (S), R208.1, U134.3 (IN+)
3V3_BANK_THRESH: R209.2, R210.1, U135.4 (IN)
3V3_G1_FUSED: F11.3, F11.4, Q16.2 (D)
3V3_G1_GATE: Q16.1 (G), R193.1, R193.2, R194.1, U130.4 (Y)
3V3_G1_NODE: F11.1, F11.2, R192.2
3V3_G2_FUSED: F12.3, F12.4, Q17.2 (D)
3V3_G2_GATE: Q17.1 (G), R196.1, R196.2, R197.1, U131.4 (Y)
3V3_G2_NODE: F12.1, F12.2, R195.2
3V3_G3_FUSED: F13.3, F13.4, Q18.2 (D)
3V3_G3_GATE: F14.1, F14.2, Q18.1 (G), R200.1, R200.2, R201.1, R202.2, R203.2, R204.2, R205.2, U132.4 (Y)
3V3_G3_NODE: F13.1, F13.2, R198.2, R199.2
3V3_G4_FUSED: F14.3, F14.4, Q19.2 (D)
3V3_G4_GATE: Q19.1 (G), R206.1, R206.2, R207.1, U133.4 (Y)
+3V3: C124.1, C125.1, J106.2, R209.1, U134.6 (VS), U135.5 (VCC)
+5V_LOGIC: U130.5 (VCC), U131.5 (VCC), U132.5 (VCC), U133.5 (VCC)
BANK_3V3_G1_CTRL: J106.4, U130.1 (A)
BANK_3V3_G2_CTRL: J106.5, U131.1 (A)
BANK_3V3_G3_CTRL: J106.6, U132.1 (A)
BANK_3V3_G4_CTRL: J106.7, U133.1 (A)
DEGATE_RAIL: J106.3, U130.2 (B), U131.2 (B), U132.2 (B), U133.2 (B)
GND: C124.2, C125.2, J106.1, R194.2, R197.2, R201.2, R207.2, R208.2, R210.2, U130.3 (GND), U131.3 (GND), U132.3 (GND), U133.3 (GND), U134.2 (GND), U134.4 (IN-), U134.5 (REF), U135.2 (VEE)
RAIL_3V3: R192.1, R195.1, R198.1, R199.1, R202.1, R203.1, R204.1, R205.1
TRIP_ANY: D106.1 (K)
TRIP_BANK_3V3: D106.2 (A), J106.8, U135.1 (OUT)

Notes on the sheet:
R-bank, 3V3 rail -- LADDER v1.1 [wb]: 4 groups (1+1+2+4 legs, 8 total, 0R68 each) x AOD4184A+3557-10 fuse+local AND gate driver, shared Kelvin shunt + INA181/TLV7011 trip-watch per rail; CEC_CONN harness-boundary connector
3V3 R-bank, LADDER v1.1 [wb] (README.md, pending owner nod): 4 groups, 1+1+2+4 legs (8 total @ 0R68 each), ST-1000 baseline drawn -- the ST-1300 population variant (12V group - +12 legs, 16->28) is a population-only BOM extension, not physically drawn this pass ("never in copper" per README -- defe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
