nathanfraske/CEC-Platform/testers/tester-standard/05d-bank-5vsb.kicad_sch

## KiCad design testers/tester-standard/05d-bank-5vsb.kicad_sch (2026-07-17)

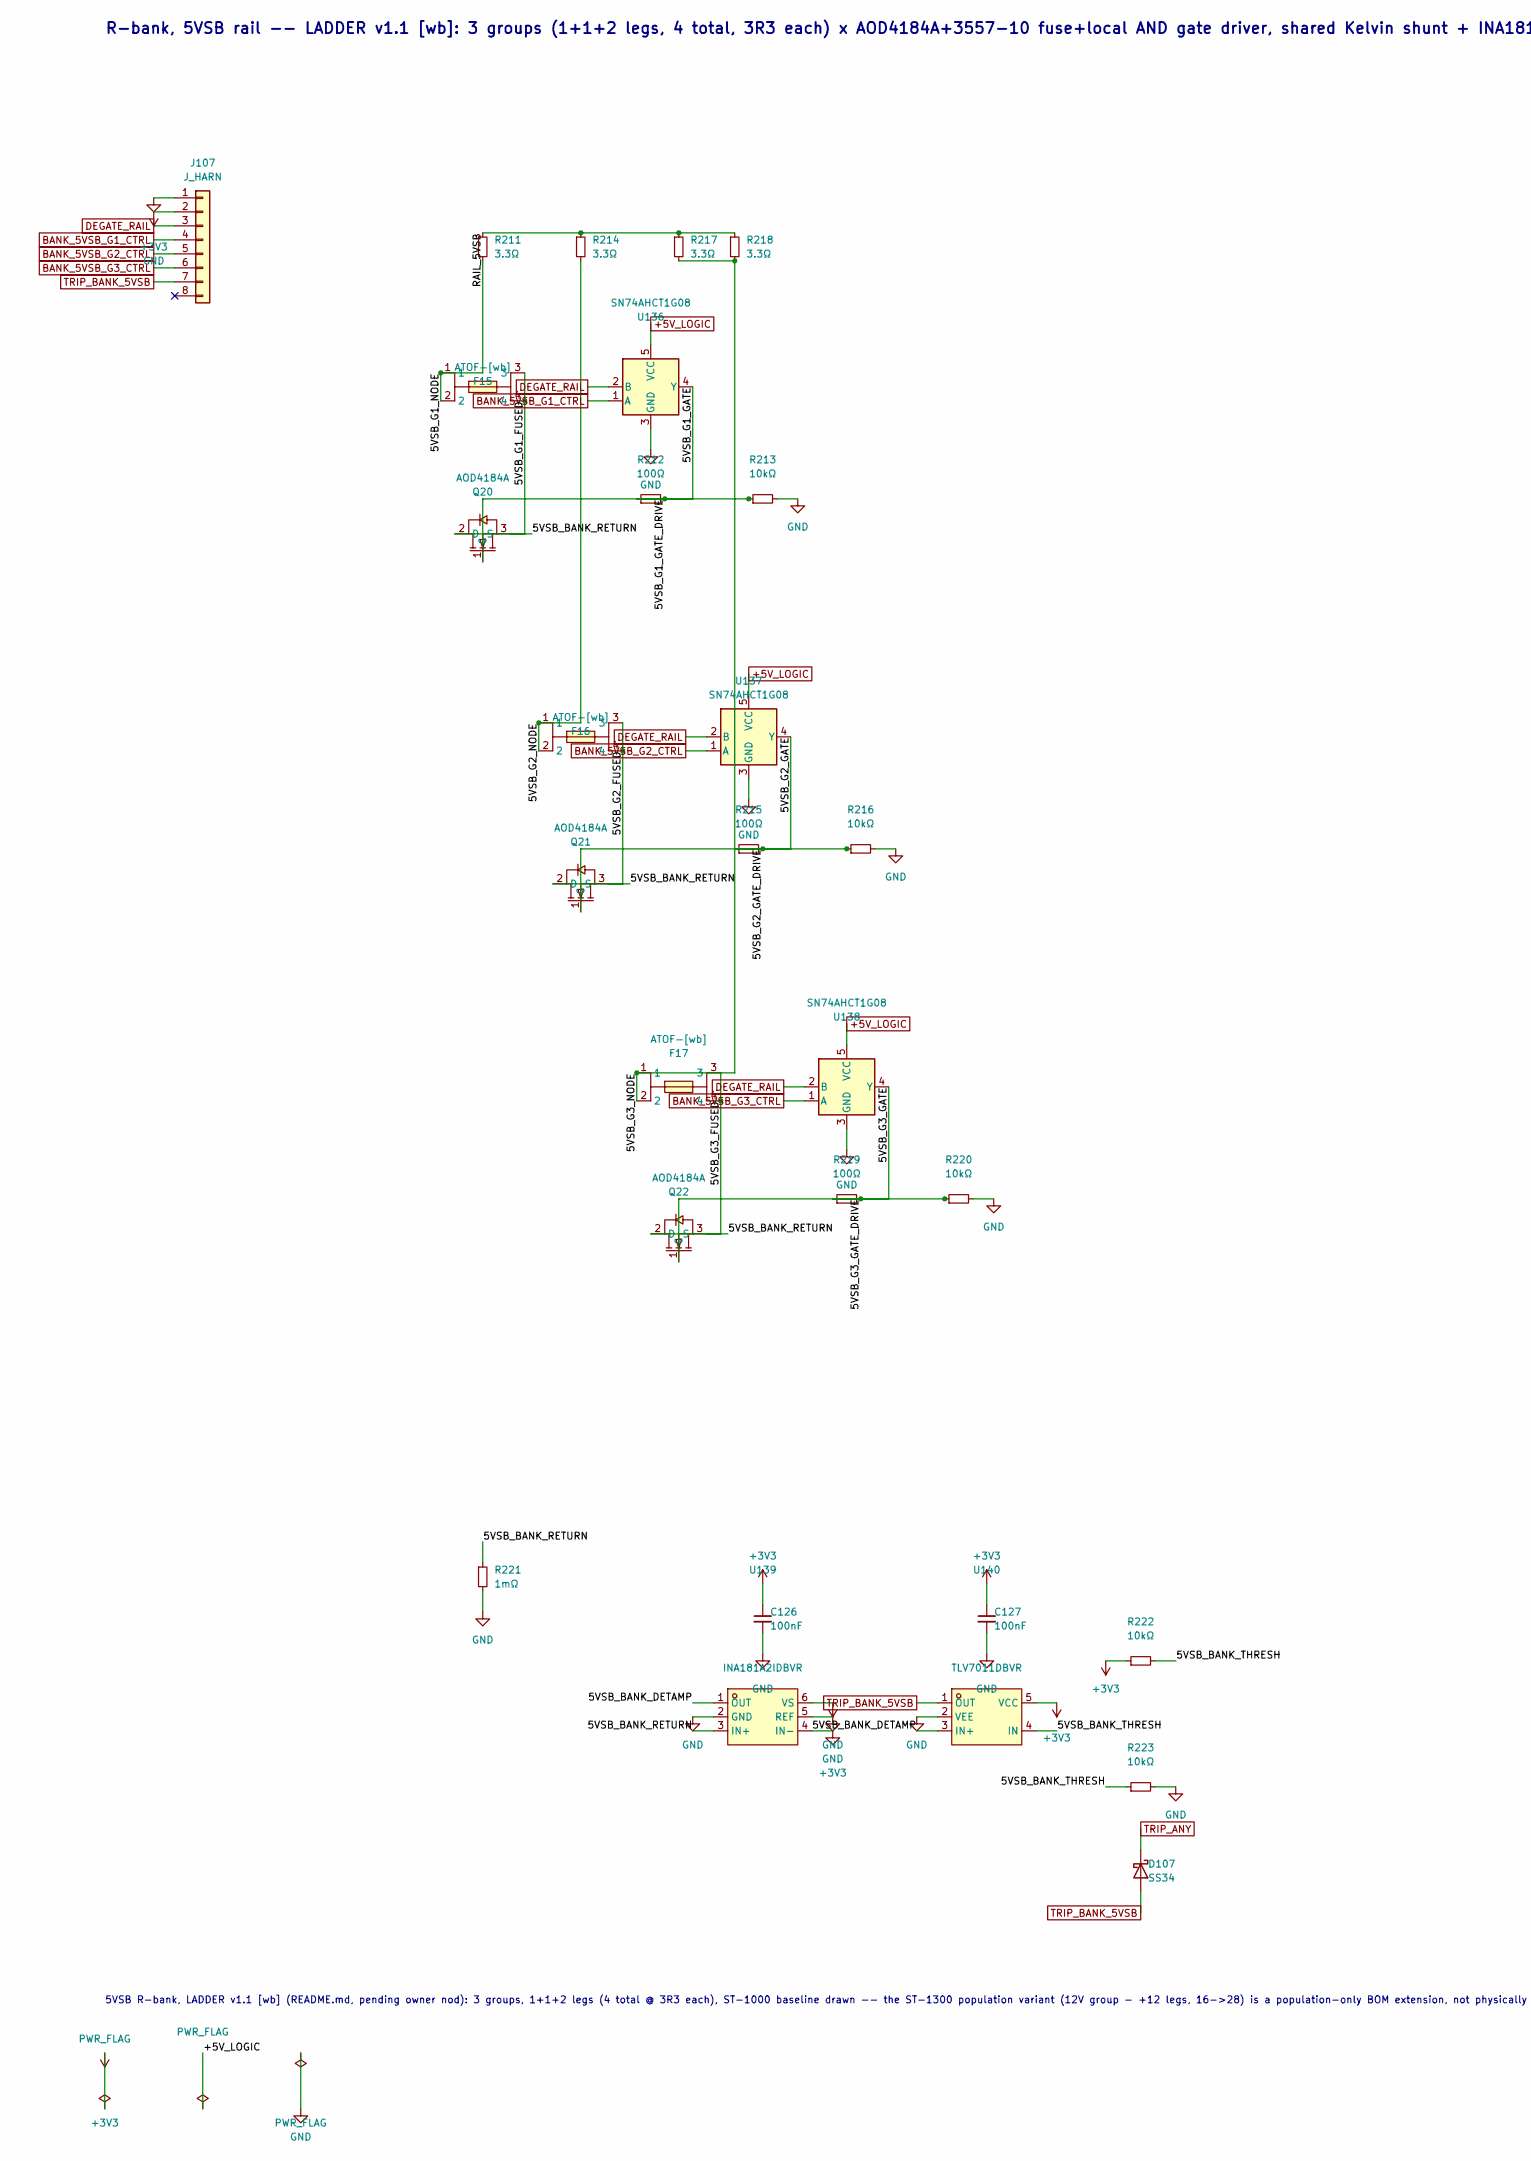
[picture p53: schematic 05d-bank-5vsb.kicad_sch, part in row 1, column 1]

Parts:
C126, C127: 100nF; C_0402_1005Metric
D107: SS34; D_SOD-323
F15, F16, F17: ATOF-[wb]; FUSE-TH_4P-L19.8-W6.7_3557-2; MPN 3557-10; LCSC C3205403
J107: J_HARN; PinHeader_1x08_P2.54mm_Vertical
Q20, Q21, Q22: AOD4184A; TO-252-2_L6.6-W6.1-P4.57-LS9.9-TL-CW; MPN AOD4184A; LCSC C99124
R211, R214, R217, R218: 3.3Ω; R_0402_1005Metric; MPN HoRX-50W-class [wb exact LCSC line pend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
R212, R215, R219: 100Ω; R_0402_1005Metric
R213, R216, R220, R222, R223: 10kΩ; R_0402_1005Metric
R221: 1mΩ; R_0402_1005Metric; MPN CSS2H-2512R-1L00F; LCSC C4175647
U136, U137, U138: SN74AHCT1G08; SOT-23-5; MPN SN74AHCT1G08DBVR
U139: INA181A2IDBVR; SOT-23-6; MPN INA181A2IDBVR; LCSC C2058784
U140: TLV7011DBVR; SOT-23-5; MPN TLV7011DBVR; LCSC C702117

Connections:
5VSB_BANK_DETAMP: U139.1 (OUT), U140.3 (IN+)
5VSB_BANK_RETURN: Q20.3 (S), Q21.3 (S), Q22.3 (S), R221.1, U139.3 (IN+)
5VSB_BANK_THRESH: R222.2, R223.1, U140.4 (IN)
5VSB_G1_FUSED: F15.3, F15.4, Q20.2 (D)
5VSB_G1_GATE: Q20.1 (G), R212.1, R212.2, R213.1, U136.4 (Y)
5VSB_G1_NODE: F15.1, F15.2, R211.2
5VSB_G2_FUSED: F16.3, F16.4, Q21.2 (D)
5VSB_G2_GATE: Q21.1 (G), R215.1, R215.2, R216.1, U137.4 (Y)
5VSB_G2_NODE: F16.1, F16.2, R214.2
5VSB_G3_FUSED: F17.3, F17.4, Q22.2 (D)
5VSB_G3_GATE: Q22.1 (G), R219.1, R219.2, R220.1, U138.4 (Y)
5VSB_G3_NODE: F17.1, F17.2, R217.2, R218.2
+3V3: C126.1, C127.1, J107.2, R222.1, U139.6 (VS), U140.5 (VCC)
+5V_LOGIC: U136.5 (VCC), U137.5 (VCC), U138.5 (VCC)
BANK_5VSB_G1_CTRL: J107.4, U136.1 (A)
BANK_5VSB_G2_CTRL: J107.5, U137.1 (A)
BANK_5VSB_G3_CTRL: J107.6, U138.1 (A)
DEGATE_RAIL: J107.3, U136.2 (B), U137.2 (B), U138.2 (B)
GND: C126.2, C127.2, J107.1, R213.2, R216.2, R220.2, R221.2, R223.2, U136.3 (GND), U137.3 (GND), U138.3 (GND), U139.2 (GND), U139.4 (IN-), U139.5 (REF), U140.2 (VEE)
RAIL_5VSB: R211.1, R214.1, R217.1, R218.1
TRIP_ANY: D107.1 (K)
TRIP_BANK_5VSB: D107.2 (A), J107.7, U140.1 (OUT)

Notes on the sheet:
R-bank, 5VSB rail -- LADDER v1.1 [wb]: 3 groups (1+1+2 legs, 4 total, 3R3 each) x AOD4184A+3557-10 fuse+local AND gate driver, shared Kelvin shunt + INA181/TLV7011 trip-watch per rail; CEC_CONN harness-boundary connector
5VSB R-bank, LADDER v1.1 [wb] (README.md, pending owner nod): 3 groups, 1+1+2 legs (4 total @ 3R3 each), ST-1000 baseline drawn -- the ST-1300 population variant (12V group - +12 legs, 16->28) is a population-only BOM extension, not physically drawn this pass ("never in copper" per README -- deferr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
