nathanfraske/CEC-Platform/testers/tester-standard/05e-bank-n12v.kicad_sch

## KiCad design testers/tester-standard/05e-bank-n12v.kicad_sch (2026-07-17)

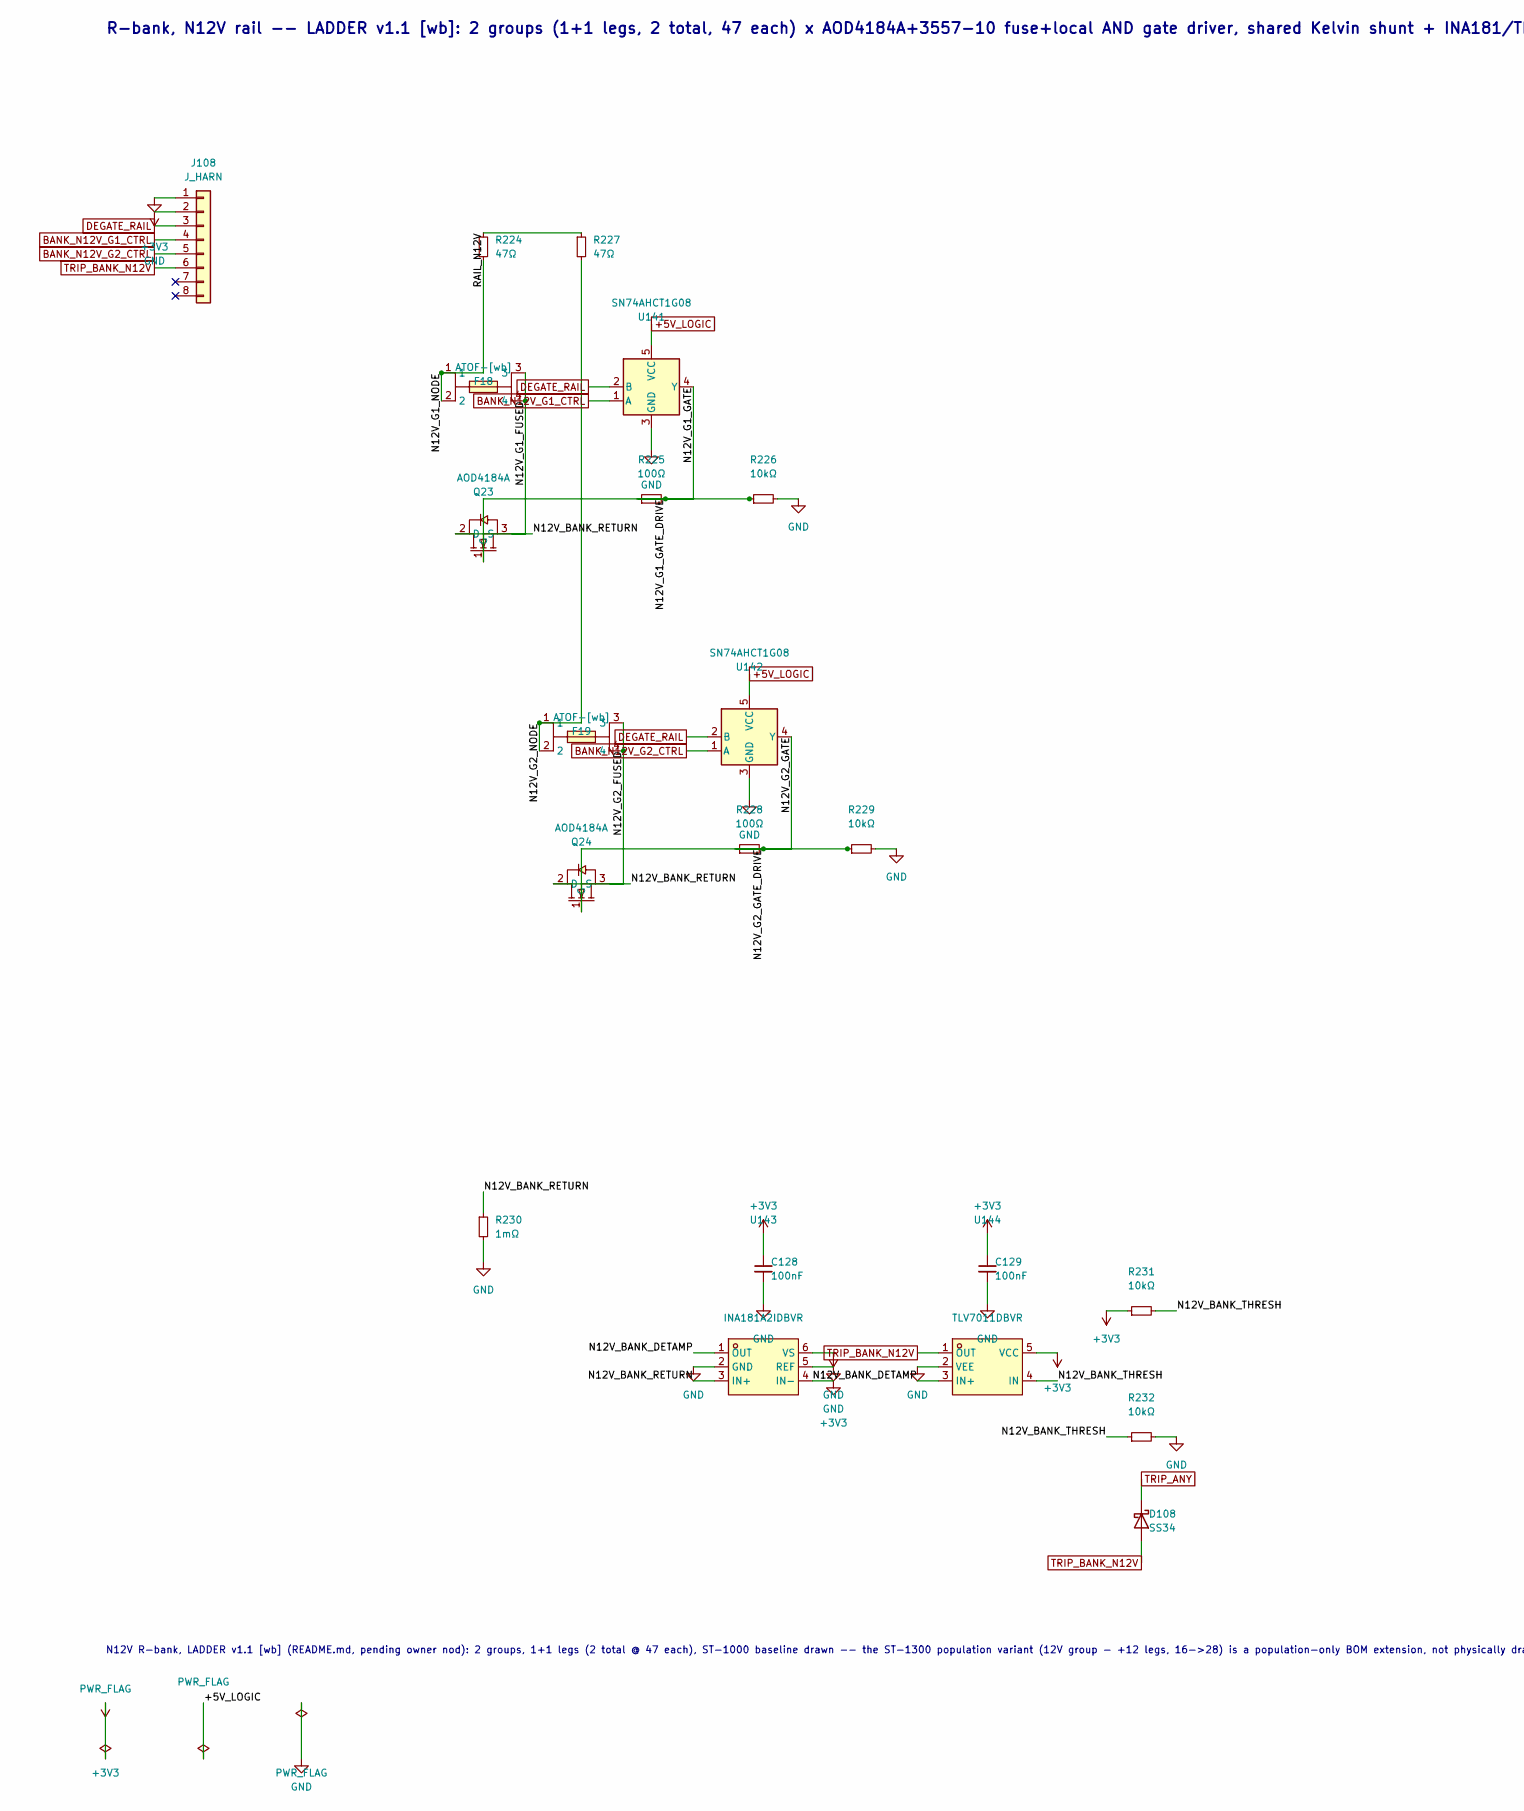
[picture p54: schematic 05e-bank-n12v.kicad_sch, part in row 1, column 1]

Parts:
C128, C129: 100nF; C_0402_1005Metric
D108: SS34; D_SOD-323
F18, F19: ATOF-[wb]; FUSE-TH_4P-L19.8-W6.7_3557-2; MPN 3557-10; LCSC C3205403
J108: J_HARN; PinHeader_1x08_P2.54mm_Vertical
Q23, Q24: AOD4184A; TO-252-2_L6.6-W6.1-P4.57-LS9.9-TL-CW; MPN AOD4184A; LCSC C99124
R224, R227: 47Ω; R_0402_1005Metric; MPN HoRX-50W-class [wb exact LCSC line pend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
R225, R228: 100Ω; R_0402_1005Metric
R226, R229, R231, R232: 10kΩ; R_0402_1005Metric
R230: 1mΩ; R_0402_1005Metric; MPN CSS2H-2512R-1L00F; LCSC C4175647
U141, U142: SN74AHCT1G08; SOT-23-5; MPN SN74AHCT1G08DBVR
U143: INA181A2IDBVR; SOT-23-6; MPN INA181A2IDBVR; LCSC C2058784
U144: TLV7011DBVR; SOT-23-5; MPN TLV7011DBVR; LCSC C702117

Connections:
+3V3: C128.1, C129.1, J108.2, R231.1, U143.6 (VS), U144.5 (VCC)
+5V_LOGIC: U141.5 (VCC), U142.5 (VCC)
BANK_N12V_G1_CTRL: J108.4, U141.1 (A)
BANK_N12V_G2_CTRL: J108.5, U142.1 (A)
DEGATE_RAIL: J108.3, U141.2 (B), U142.2 (B)
GND: C128.2, C129.2, J108.1, R226.2, R229.2, R230.2, R232.2, U141.3 (GND), U142.3 (GND), U143.2 (GND), U143.4 (IN-), U143.5 (REF), U144.2 (VEE)
N12V_BANK_DETAMP: U143.1 (OUT), U144.3 (IN+)
N12V_BANK_RETURN: Q23.3 (S), Q24.3 (S), R230.1, U143.3 (IN+)
N12V_BANK_THRESH: R231.2, R232.1, U144.4 (IN)
N12V_G1_FUSED: F18.3, F18.4, Q23.2 (D)
N12V_G1_GATE: Q23.1 (G), R225.1, R225.2, R226.1, U141.4 (Y)
N12V_G1_NODE: F18.1, F18.2, R224.2
N12V_G2_FUSED: F19.3, F19.4, Q24.2 (D)
N12V_G2_GATE: Q24.1 (G), R228.1, R228.2, R229.1, U142.4 (Y)
N12V_G2_NODE: F19.1, F19.2, R227.2
RAIL_N12V: R224.1, R227.1
TRIP_ANY: D108.1 (K)
TRIP_BANK_N12V: D108.2 (A), J108.6, U144.1 (OUT)

Notes on the sheet:
R-bank, N12V rail -- LADDER v1.1 [wb]: 2 groups (1+1 legs, 2 total, 47 each) x AOD4184A+3557-10 fuse+local AND gate driver, shared Kelvin shunt + INA181/TLV7011 trip-watch per rail; CEC_CONN harness-boundary connector
N12V R-bank, LADDER v1.1 [wb] (README.md, pending owner nod): 2 groups, 1+1 legs (2 total @ 47 each), ST-1000 baseline drawn -- the ST-1300 population variant (12V group - +12 legs, 16->28) is a population-only BOM extension, not physically drawn this pass ("never in copper" per README -- deferred,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
