nathanfraske/CEC-Platform/firmware/esp/proto/atx-24pin/main/cec_config.h

/*
 * 24-pin module board/application configuration — the official
 * board-variation point (eps main/cec_config pattern, firmware
 * consolidation Phase E3). Constants that tune the SHARED detection
 * components live here, never inside firmware/esp/components.
 *
 * Currently carries the Layer 1 / Layer 2 detector tuning hoisted from
 * main.c when the detectors moved to the shared cec_detection. Future
 * hoists (pins, dividers, trims, swing/L3 tuning) belong here too.
 */

#pragma once

#include "cec_layer1.h"

#ifdef __cplusplus
extern "C" {
#endif

/* Layer 1 static-threshold bands per rail (BAND mode). Carried forward
 * from v0.5.9: 5%/10% deviation on the main rails, 10%/20% on the
 * loose-spec 5VSB. Definitions in cec_config.c. */
extern const cec_rail_spec_t CEC_CFG_L1_SPEC_12V;
extern const cec_rail_spec_t CEC_CFG_L1_SPEC_5V;
extern const cec_rail_spec_t CEC_CFG_L1_SPEC_3V3;
extern const cec_rail_spec_t CEC_CFG_L1_SPEC_5VSB;

/* Consecutive out-of-band samples before Layer 1 reports CRITICAL
 * (v0.5.9 default). */
#define L1_CRIT_CONSECUTIVE 3

/* Layer 2 adaptive transient detectors. Per-rail min-thresholds and
 * k_sigma carry forward from v0.5.9. The fire condition is
 * |instant - ema| > max(min, k*std) for 3 consecutive samples. */
#define LAYER2_K_SIGMA       5.0f
#define LAYER2_CONSECUTIVE   3
#define L2_MIN_V_12V         0.50f
#define L2_MIN_V_5V          0.20f
#define L2_MIN_V_3V3         0.15f
#define L2_MIN_V_5VSB        0.30f
#define L2_MIN_I_12V         1.00f
#define L2_MIN_I_5V          0.50f
#define L2_MIN_I_3V3         0.30f

/* TelePlot UART transport pins -- VESTIGIAL on the production board, which has
 * only the MCU's native USB Serial/JTAG. main.c does NOT call
 * cec_telemetry_init_uart (see the comment there), so TelePlot always rides
 * stdio with the logs regardless of CONFIG_CEC_TELEMETRY_UART0. These were the
 * dev board's CH340K UART bridge (GPIO43/44, 921600); kept only so the shared
 * cec_telemetry init signature still resolves. A board that actually has the
 * bridge would call cec_telemetry_init_uart with CONFIG_CEC_TELEMETRY_UART0=y. */
#define TELEMETRY_UART_NUM       0
#define TELEMETRY_UART_TXD       43
#define TELEMETRY_UART_RXD       44
#define TELEMETRY_UART_BAUD      921600
#define TELEMETRY_UART_TX_BUF    4096   /* Burst dumps need headroom */

/*
 * 24-pin sensing, THIS spin (the alpha/rev2 bench units) — 4x INA228 (one
 * per rail), traced from the board netlist (24pin-module.kicad_sch). Each
 * INA228 gives bus voltage + current; the ACS712/divider front end is
 * retired. I2C SDA=IO8 / SCL=IO9. Owner direction 2026-07-15: the INA228
 * stays because these bench units are populated with it; the production
 * part going forward is the INA238 (spec v1.5.0, 24-pin rev3+ — separate
 * driver, firmware-integrated energy per OQ-13).
 *
 *   Rail  U     I2C   shunt    ALERT   as-built shunt (THIS spin)
 *   12V   U10   0x40  2 mOhm   IO10    PSRP25K6FR002 (Prosemi; NiCr, 6 W, ±1%, ±75 ppm/°C)
 *   5V    U11   0x41  2 mOhm   IO11    PSRP25K6FR002 (Prosemi; NiCr, 6 W, ±1%, ±75 ppm/°C)
 *   3V3   U12   0x44  2 mOhm   IO12    PSRP25K6FR002 (Prosemi; NiCr, 6 W, ±1%, ±75 ppm/°C)
 *   5VSB  U13   0x45  25 mOhm  IO13    LCSR2512FR025K9L (RESI; ±1%, ±100 ppm/°C, 2 W)
 *
 * The shunt — not the INA228 — sets current/power ACCURACY (the part is
 * 20-bit, ±0.1% gain, ~±1 uV offset; far better than the resistor in front
 * of it). All four are ±1% tolerance, so UNCALIBRATED current is ~±1%; a
 * one-point per-channel cal (current_trim, below) removes the tolerance and
 * leaves the TCR term -- ~±0.3% over a 40°C swing on the main rails (PSRP,
 * ±75 ppm/°C) -- which the INA228 die-temp can compensate. The PSRP is a 6 W
 * NiCr alloy part, so at 12V/15A (0.45 W, <8% of rating) self-heating drift
 * is small. OQ-11 is still open (Bourns CSS2H intended for production).
 *
 * Status LED: D2 on IO21 (active-high, IO21 -> R7 -> LED -> GND).
 */
#define INA228_ADDR_12V      0x40
#define INA228_ADDR_5V       0x41
#define INA228_ADDR_3V3      0x44
#define INA228_ADDR_5VSB     0x45
#define INA228_SHUNT_MAIN    0.002f   /* 12V/5V/3V3 = 2 mOhm  (PSRP25K6FR002, ±1%/±75ppm) */
#define INA228_SHUNT_5VSB    0.025f   /* 5VSB = 25 mOhm (LCSR2512FR025K9L, ±1%/±100ppm) */
#define INA228_ALERT_12V     10
#define INA228_ALERT_5V      11
#define INA228_ALERT_3V3     12
#define INA228_ALERT_5VSB    13
#define STATUS_LED_GPIO      21       /* D2, active-high */

/* PSU control/status, buffered to 3.3V by U4/U5 (74LVC1G17, non-inverting),
 * tapped off the ATX pass-through. Read-only: the module monitors these, it
 * does not drive PS_ON#. */
#define PWROK_BUF_GPIO       38       /* U4 out: ATX PWR_OK (1 = power good) */
#define PSON_BUF_GPIO        39       /* U5 out: ATX PS_ON# (0 = PSU on, active-low) */

/*
 * CAN telemetry to the Hub. Transceiver U2 = TJA1051T/3 on the RJ-45
 * CAN pair (J1 pin 3 = CAN_H, pin 6 = CAN_L). MCU side:
 *   CAN TX -> ESP IO17 (TJA1051 TXD), CAN RX <- ESP IO18 (TJA1051 RXD).
 * Pins + bitrate are set in sdkconfig.defaults (CONFIG_CEC_CAN_TX_GPIO=17,
 * RX=18, BITRATE_BPS=125000 -- the slope-controlled bench rate; 500k is the
 * platform target once the Hub's SN65HVD230 Rs is bridged to GND). The
 * shared cec_comms component reads those Kconfig values. This board sends a
 * 3-frame rail-telemetry burst (cec_telem.h) every CEC_CAN_TX_PERIOD_MS. */
#define CEC_CFG_MODULE_TYPE      CEC_MODULE_TYPE_ATX24
#define CEC_CFG_MODULE_ID        0
#define CEC_CAN_TX_PERIOD_MS     200    /* 5 Hz telemetry to the Hub */

#ifdef __cplusplus
}
#endif
