nathanfraske/CEC-Platform/hubs/hub-enterprise/gen_hub_enterprise.py

#!/usr/bin/env python3
# SPDX-License-Identifier: Apache-2.0
# Copyright 2026 Nathan M. Fraske
#
# ENT Hub schematic capture -- sheet 01 (power input) + the hierarchical
# scaffold (root + placeholder sheets 02-09), per hubs/hub-enterprise/
# SCHEMATIC-PLAN.md and docs/enterprise-requirements/spec-sheets/bom-detailed/
# bom-d-power.md.
#
# FORMAT CORRECTION (owner, 2026-07-02): sheet 01 is captured as a genuine
# THREE-level hierarchy -- root -> 01-power-input.kicad_sch (a THIN PARENT:
# sheet symbols only, no components, no dashed frames) -> seven LEAF sheets
# (01a-efuse-main, 01b-efuse-5vsb, 01c-efuse-ext, 01d-cascade, 01e-holdup,
# 01f-buck-3v3, 01g-rail-sense), each one functional block, on its own file,
# with a proper title. This supersedes the prior single flat 01-power-input
# capture that grouped those same seven blocks as dashed-frame SECTIONS on
# one sheet ("weird sub-sheets", per the owner) -- same parts, same nets, same
# wiring; only the sheet boundaries moved. See build_lib.py's module docstring
# for the addressing rules this relies on (component instance-path chains,
# sheet_instances path chains, hierarchical-label/sheet-pin name matching).
#
# Reuses scripts/cec_sch.py's low-level symbol/wire/label helpers (pin
# geometry, wire routing, power-symbol embedding) but does NOT use its
# build_schematic() top-level driver (assumes a flat single-sheet project).
#
# Run: python3 hubs/hub-enterprise/gen_hub_enterprise.py
# Validate: kicad-cli sch erc ... (see scripts/check_hub_ent_sch.py)
import os, re, sys, uuid

HERE = os.path.dirname(os.path.abspath(__file__))
ROOTDIR = os.path.dirname(os.path.dirname(HERE))
sys.path.insert(0, os.path.join(ROOTDIR, "scripts"))
import cec_sch  # noqa: E402
import cec_sch_layout  # noqa: E402  -- the T1 engine (nudge_texts finishing pass)
import cec_sch_compose  # noqa: E402  -- the shared composition engine (T4)
import cec_sch_archetypes as arch  # noqa: E402  -- T4 block templates

PROJECT = "hub-enterprise"

# ---------------------------------------------------------------------------
# fixed identity uuids (stable across regenerations so the project doesn't
# re-annotate references every run). Generated once; do not reshuffle.
# ---------------------------------------------------------------------------
ROOT_UUID = "8f2a1c40-6e11-4b8a-9d3a-1a2b3c4d5e6f"
SHEET_UUIDS = {
    "01": "0a1b2c3d-4e5f-4061-8a2b-3c4d5e6f7081",
    "02": "0a1b2c3d-4e5f-4062-8a2b-3c4d5e6f7082",
    "03": "0a1b2c3d-4e5f-4063-8a2b-3c4d5e6f7083",
    "04": "0a1b2c3d-4e5f-4064-8a2b-3c4d5e6f7084",
    "05": "0a1b2c3d-4e5f-4065-8a2b-3c4d5e6f7085",
    "06": "0a1b2c3d-4e5f-4066-8a2b-3c4d5e6f7086",
    "07": "0a1b2c3d-4e5f-4067-8a2b-3c4d5e6f7087",
    "08": "0a1b2c3d-4e5f-4068-8a2b-3c4d5e6f7088",
    "09": "0a1b2c3d-4e5f-4069-8a2b-3c4d5e6f7089",
}
SHEET01_OWN_UUID = "1b2c3d4e-5f60-4171-9b2c-4d5e6f708192"  # 01-power-input.kicad_sch's own file identity (thin parent)

# 01a-01g: sheet-symbol uuid (as placed IN the 01-power-input parent) + this
# leaf file's own top-level identity uuid. Both fixed/stable, per the same
# convention as SHEET_UUIDS/SHEET01_OWN_UUID above.
LEAF_SYM_UUIDS = {
    "01a": "1a2b3c4d-5e6f-40a1-9b1a-2c3d4e5f60a1",
    "01b": "1a2b3c4d-5e6f-40a2-9b1a-2c3d4e5f60a2",
    "01c": "1a2b3c4d-5e6f-40a3-9b1a-2c3d4e5f60a3",
    "01d": "1a2b3c4d-5e6f-40a4-9b1a-2c3d4e5f60a4",
    "01e": "1a2b3c4d-5e6f-40a5-9b1a-2c3d4e5f60a5",
    "01f": "1a2b3c4d-5e6f-40a6-9b1a-2c3d4e5f60a6",
    "01g": "1a2b3c4d-5e6f-40a7-9b1a-2c3d4e5f60a7",
}
LEAF_OWN_UUIDS = {
    "01a": "2b3c4d5e-6f70-41a1-8c2b-3d4e5f6071a1",
    "01b": "2b3c4d5e-6f70-41a2-8c2b-3d4e5f6071a2",
    "01c": "2b3c4d5e-6f70-41a3-8c2b-3d4e5f6071a3",
    "01d": "2b3c4d5e-6f70-41a4-8c2b-3d4e5f6071a4",
    "01e": "2b3c4d5e-6f70-41a5-8c2b-3d4e5f6071a5",
    "01f": "2b3c4d5e-6f70-41a6-8c2b-3d4e5f6071a6",
    "01g": "2b3c4d5e-6f70-41a7-8c2b-3d4e5f6071a7",
}

SHEET_TITLES = {
    "02": ("02-compute-core", "MPFS095Tx FCVG484 compute core (boot straps, JTAG, clock, decoupling)"),
    "03": ("03-compute-rails", "MIC22705YML-TR core buck + bank rails + sequencing/PG chain"),
    "04": ("04-storage", "W25Q256JV QSPI NOR + eMMC 5.1 (FW/tamper log/bulk storage)"),
    "05": ("05-module-ports", "8x RJ-45 FTP module ports, DETECT/pin-7, TJA1051T/3, ADS7830"),
    "06": ("06-t1-dataplane", "2x LAN9370 100BASE-T1 fabric switch"),
    "07": ("07-uplink", "DP83869HM GbE uplink PHY + magnetics/protection"),
    "08": ("08-secio-aux", "RJ-11 security I/O, NanoKVM aux, SK6812 chain, service button"),
    "09": ("09-watchdog", "S32K3xx supervisory watchdog (MC/MC-Max only)"),
}

# ---------------------------------------------------------------------------
# libraries
# ---------------------------------------------------------------------------
LIBS = {
    "cec":            open(f"{ROOTDIR}/lib/cec.kicad_sym", encoding="utf-8").read(),
    "cec-vendor":      open(f"{ROOTDIR}/lib/vendor/cec-vendor.kicad_sym", encoding="utf-8").read(),
    "power":           open(f"{ROOTDIR}/lib/vendor/cec-power.kicad_sym", encoding="utf-8").read(),
    "cec-ent-power":   open(f"{ROOTDIR}/lib/cec-ent-power.kicad_sym", encoding="utf-8").read(),
    "cec-ent-mcu":     open(f"{ROOTDIR}/lib/cec-ent-mcu.kicad_sym", encoding="utf-8").read(),
    "cec-ent-hub-local": open(f"{HERE}/lib-local.kicad_sym", encoding="utf-8").read(),
}

UR = "UNI-ROYAL"
SAM = "Samsung"
TI = "Texas Instruments"

POWER_PORTS = {"GND": "GND", "+3V3": "+3V3", "+5VSB": "+5VSB",
               "+5V_MAIN": "+5V_MAIN", "+5V_SYS": "+5V_SYS"}

# ===========================================================================
# a "Leaf" is one functional-block sheet (01a..01g): its own parts/nets.
# (data holder promoted to cec_sch_compose 2026-07-03; identical class)
# ===========================================================================
Leaf = cec_sch_compose.Leaf


LEAVES = {}


def leaf(id_, filename, sheetname, desc):
    lf = Leaf(id_, filename, sheetname, desc)
    LEAVES[id_] = lf
    return lf


L01A = leaf("01a", "01a-efuse-main.kicad_sch", "01a-efuse-main",
            "MAIN_5V eFuse front (TPS25940, ILIM 24.9k -> 3.53A typ)")
L01B = leaf("01b", "01b-efuse-5vsb.kicad_sch", "01b-efuse-5vsb",
            "+5VSB eFuse front (TPS25940, ILIM 42.2k -> 2.08A typ)")
L01C = leaf("01c", "01c-efuse-ext.kicad_sch", "01c-efuse-ext",
            "EXT eFuse front + TVS (TPS25940, ILIM 42.2k -> 2.08A typ, SMAJ5.0A + PJ-002AH)")
L01D = leaf("01d", "01d-cascade.kicad_sch", "01d-cascade",
            "Priority cascade (2x TPS2121): 5VSB>EXT stage A, MAIN_5V>stage-A-out stage B")
L01E = leaf("01e", "01e-holdup.kicad_sch", "01e-holdup",
            "Hold-up reservoir: 2x 4700uF + 470uF bulk, isolation Schottky")
L01F = leaf("01f", "01f-buck-3v3.kicad_sch", "01f-buck-3v3",
            "TLV62569 3.3V hub-logic buck + FB divider + TPS3839K33 supervisor")
L01G = leaf("01g", "01g-rail-sense.kicad_sch", "01g-rail-sense",
            "4x 47k/10k rail-sense dividers: raw MAIN/SVB/EXT + merged +5V_SYS")

# ---------------------------------------------------------------------------
# 01a -- MAIN_5V eFuse front (U101)
# ---------------------------------------------------------------------------
GX, GY = 20, 40
L01A.add_part("J101", "cec", "CEC_PWR_IN_2P", "CEC_PWR_IN_2P", GX, GY + 25,
          "cec-Connector_JST:JST_XH_S2B-XH-A_1x02_P2.50mm_Horizontal",
          {"Manufacturer": "JST", "MPN": "S2B-XH-A(LF)(SN)", "LCSC": "C157931",
           "Description": "MAIN_5V power-in, 2-pin JST-XH -- reuse platform J_5V"})
L01A.add_part("R101", "cec-vendor", "R_Small", "45.3k", GX + 40, GY - 10,
          "cec-Resistor_SMD:R_0402_1005Metric",
          {"Manufacturer": UR, "MPN": "0402WGF4532TCE",
           "Description": "UVLO/OVLO divider top, MAIN_5V eFuse"})
L01A.add_part("R102", "cec-vendor", "R_Small", "2.80k", GX + 40, GY + 5,
          "cec-Resistor_SMD:R_0402_1005Metric",
          {"Manufacturer": UR, "MPN": "0402WGF2801TCE",
           "Description": "UVLO/OVLO divider mid, MAIN_5V eFuse"})
L01A.add_part("R103", "cec-vendor", "R_Small", "10k", GX + 40, GY + 20,
          "cec-Resistor_SMD:R_0402_1005Metric",
          {"Manufacturer": UR, "MPN": "0402WGF1002TCE", "LCSC": "C25744",
           "Description": "UVLO/OVLO divider bottom, MAIN_5V eFuse"})
L01A.add_part("U101", "cec-ent-power", "TPS25940LRVCR", "TPS25940LRVCR", GX + 85, GY + 15,
          "cec-Package_DFN_QFN:WQFN-20_L4.0-W3.0-P0.50-BL-EP",
          {"Manufacturer": TI, "MPN": "TPS25940LRVCR", "LCSC": "C2867756",
           "Datasheet": "https://www.ti.com/lit/ds/symlink/tps25940.pdf",
           "Description": "eFuse front, MAIN_5V, ILIM 24.9k->3.53A typ"})
L01A.add_part("R104", "cec-vendor", "R_Small", "24.9k", GX + 130, GY - 15,
          "cec-Resistor_SMD:R_0402_1005Metric",
          {"Manufacturer": UR, "MPN": "0402WGF2492TCE",
           "Description": "R_ILIM MAIN_5V -> 3.53A typ"})
L01A.add_part("C101", "cec-vendor", "C_Small", "10n", GX + 130, GY,
          "cec-Capacitor_SMD:C_0402_1005Metric",
          {"Manufacturer": SAM, "MPN": "CL05B103KB5NNNC", "LCSC": "C15195",
           "Description": "dVdT soft-start ramp cap, MAIN_5V eFuse"})
L01A.add_part("R105", "cec-vendor", "R_Small", "10k", GX + 130, GY + 20,
          "cec-Resistor_SMD:R_0402_1005Metric",
          {"Manufacturer": UR, "MPN": "0402WGF1002TCE", "LCSC": "C25744",
           "Description": "PGOOD pull-up, MAIN_5V eFuse"})
L01A.add_part("R106", "cec-vendor", "R_Small", "10k", GX + 130, GY + 35,
          "cec-Resistor_SMD:R_0402_1005Metric",
          {"Manufacturer": UR, "MPN": "0402WGF1002TCE", "LCSC": "C25744",
           "Description": "FLT pull-up, MAIN_5V eFuse"})
L01A.add_part("C102", "cec-vendor", "C_Small", "100n", GX, GY + 60,
          "cec-Capacitor_SMD:C_0402_1005Metric",
          {"Manufacturer": SAM, "MPN": "CL05B104KO5NNNC", "LCSC": "C1525",
           "Description": "input noise-suppression cap, MAIN_5V eFuse"})
L01A.add_part("C103", "cec-vendor", "C_Small", "1u", GX + 130, GY - 30,
          "cec-Capacitor_SMD:C_0603_1608Metric",
          {"Manufacturer": SAM, "MPN": "CL10A105KB8NNNC", "LCSC": "C15849",
           "Description": "local output bypass, MAIN_5V eFuse"})

L01A.net("+5V_MAIN", ("J101", "1"), ("R101", "1"), ("U101", "9"), ("U101", "10"),
    ("U101", "11"), ("U101", "12"), ("U101", "13"), ("C102", "1"))
L01A.net("GND", ("J101", "2"))
L01A.net("UVLO_MAIN", ("R101", "2"), ("R102", "1"), ("U101", "14"))
L01A.net("OVP_MAIN", ("R102", "2"), ("R103", "1"), ("U101", "15"))
L01A.net("GND", ("R103", "2"))
L01A.net("ILIM_MAIN", ("R104", "1"), ("U101", "17"))
L01A.net("GND", ("R104", "2"))
L01A.net("DVDT_MAIN", ("C101", "1"), ("U101", "18"))
L01A.net("GND", ("C101", "2"))
L01A.net("PG_MAIN", ("U101", "2"), ("R105", "1"))
L01A.net("+3V3", ("R105", "2"))
L01A.net("FLT_MAIN", ("U101", "20"), ("R106", "1"))
L01A.net("+3V3", ("R106", "2"))
L01A.net("GND", ("C102", "2"), ("U101", "16"), ("U101", "21"), ("U101", "1"))  # GND, EP, DEVSLP->GND
L01A.net("MAIN_EF_OUT", ("U101", "4"), ("U101", "5"), ("U101", "6"), ("U101", "7"),
    ("U101", "8"), ("U101", "3"), ("C103", "1"))  # OUT x5 + PGTH tied to OUT directly
L01A.net("GND", ("C103", "2"))

L01A.hier_exports = {
    "PG_MAIN":     ("output", ("R105", "1")),
    "FLT_MAIN":    ("output", ("R106", "1")),
    "MAIN_EF_OUT": ("output", ("U101", "4")),
}
L01A.powerflag_nets = ["GND", "+5V_MAIN"]

# ---------------------------------------------------------------------------
# 01b -- 5VSB eFuse front (U102)
# ---------------------------------------------------------------------------
GX, GY = 20, 40
L01B.add_part("J102", "cec", "CEC_PWR_IN_2P", "CEC_PWR_IN_2P", GX, GY + 25,
          "cec-Connector_JST:JST_XH_S2B-XH-A_1x02_P2.50mm_Horizontal",
          {"Manufacturer": "JST", "MPN": "S2B-XH-A(LF)(SN)", "LCSC": "C157931",
           "Description": "+5VSB power-in (24-pin module feed), 2-pin JST-XH -- reuse platform J_5VSB"})
L01B.add_part("R107", "cec-vendor", "R_Small", "45.3k", GX + 40, GY - 10,
          "cec-Resistor_SMD:R_0402_1005Metric",
          {"Manufacturer": UR, "MPN": "0402WGF4532TCE",
           "Description": "UVLO/OVLO divider top, 5VSB eFuse"})
L01B.add_part("R108", "cec-vendor", "R_Small", "2.80k", GX + 40, GY + 5,
          "cec-Resistor_SMD:R_0402_1005Metric",
          {"Manufacturer": UR, "MPN": "0402WGF2801TCE",
           "Description": "UVLO/OVLO divider mid, 5VSB eFuse"})
L01B.add_part("R109", "cec-vendor", "R_Small", "10k", GX + 40, GY + 20,
          "cec-Resistor_SMD:R_0402_1005Metric",
          {"Manufacturer": UR, "MPN": "0402WGF1002TCE", "LCSC": "C25744",
           "Description": "UVLO/OVLO divider bottom, 5VSB eFuse"})
L01B.add_part("U102", "cec-ent-power", "TPS25940LRVCR", "TPS25940LRVCR", GX + 85, GY + 15,
          "cec-Package_DFN_QFN:WQFN-20_L4.0-W3.0-P0.50-BL-EP",
          {"Manufacturer": TI, "MPN": "TPS25940LRVCR", "LCSC": "C2867756",
           "Datasheet": "https://www.ti.com/lit/ds/symlink/tps25940.pdf",
           "Description": "eFuse front, +5VSB, ILIM 42.2k->2.08A typ"})
L01B.add_part("R110", "cec-vendor", "R_Small", "42.2k", GX + 130, GY - 15,
          "cec-Resistor_SMD:R_0402_1005Metric",
          {"Manufacturer": UR, "MPN": "0402WGF4222TCE",
           "Description": "R_ILIM 5VSB -> 2.08A typ"})
L01B.add_part("C104", "cec-vendor", "C_Small", "10n", GX + 130, GY,
          "cec-Capacitor_SMD:C_0402_1005Metric",
          {"Manufacturer": SAM, "MPN": "CL05B103KB5NNNC", "LCSC": "C15195",
           "Description": "dVdT soft-start ramp cap, 5VSB eFuse"})
L01B.add_part("R111", "cec-vendor", "R_Small", "10k", GX + 130, GY + 20,
          "cec-Resistor_SMD:R_0402_1005Metric",
          {"Manufacturer": UR, "MPN": "0402WGF1002TCE", "LCSC": "C25744",
           "Description": "PGOOD pull-up, 5VSB eFuse"})
L01B.add_part("R112", "cec-vendor", "R_Small", "10k", GX + 130, GY + 35,
          "cec-Resistor_SMD:R_0402_1005Metric",
          {"Manufacturer": UR, "MPN": "0402WGF1002TCE", "LCSC": "C25744",
           "Description": "FLT pull-up, 5VSB eFuse"})
L01B.add_part("C105", "cec-vendor", "C_Small", "100n", GX, GY + 60,
          "cec-Capacitor_SMD:C_0402_1005Metric",
          {"Manufacturer": SAM, "MPN": "CL05B104KO5NNNC", "LCSC": "C1525",
           "Description": "input noise-suppression cap, 5VSB eFuse"})
L01B.add_part("C106", "cec-vendor", "C_Small", "1u", GX + 130, GY - 30,
          "cec-Capacitor_SMD:C_0603_1608Metric",
          {"Manufacturer": SAM, "MPN": "CL10A105KB8NNNC", "LCSC": "C15849",
           "Description": "local output bypass, 5VSB eFuse"})

L01B.net("+5VSB", ("J102", "1"), ("R107", "1"), ("U102", "9"), ("U102", "10"),
    ("U102", "11"), ("U102", "12"), ("U102", "13"), ("C105", "1"))
L01B.net("GND", ("J102", "2"))
L01B.net("UVLO_SVB", ("R107", "2"), ("R108", "1"), ("U102", "14"))
L01B.net("OVP_SVB", ("R108", "2"), ("R109", "1"), ("U102", "15"))
L01B.net("GND", ("R109", "2"))
L01B.net("ILIM_SVB", ("R110", "1"), ("U102", "17"))
L01B.net("GND", ("R110", "2"))
L01B.net("DVDT_SVB", ("C104", "1"), ("U102", "18"))
L01B.net("GND", ("C104", "2"))
L01B.net("PG_SVB", ("U102", "2"), ("R111", "1"))
L01B.net("+3V3", ("R111", "2"))
L01B.net("FLT_SVB", ("U102", "20"), ("R112", "1"))
L01B.net("+3V3", ("R112", "2"))
L01B.net("GND", ("C105", "2"), ("U102", "16"), ("U102", "21"), ("U102", "1"))
L01B.net("SVB_EF_OUT", ("U102", "4"), ("U102", "5"), ("U102", "6"), ("U102", "7"),
    ("U102", "8"), ("U102", "3"), ("C106", "1"))
L01B.net("GND", ("C106", "2"))

L01B.hier_exports = {
    "PG_SVB":     ("output", ("R111", "1")),
    "FLT_SVB":    ("output", ("R112", "1")),
    "SVB_EF_OUT": ("output", ("U102", "4")),
}
L01B.powerflag_nets = ["+5VSB"]

# ---------------------------------------------------------------------------
# 01c -- EXT eFuse front + TVS (U103)
# ---------------------------------------------------------------------------
GX, GY = 20, 40
L01C.add_part("J103", "cec-ent-hub-local", "PJ-002AH", "PJ-002AH", GX, GY + 25,
          "cec-ent-hub-local:PJ-002AH_THT_RA",
          {"Manufacturer": "Same Sky (CUI Devices)", "MPN": "PJ-002AH",
           "Datasheet": "https://www.sameskydevices.com/product/resource/pj-002ah.pdf",
           "Description": "EXT rear-bracket power-in, 5.5/2.1mm barrel jack "
                           "(BOM-D recommendation over a keyed JST -- 'any generic "
                           "5V adapter should work'; owner nod still open, see Open Items). "
                           "No LCSC C-number (DigiKey #408446 only), per BOM-D."})
L01C.add_part("D102", "cec-ent-hub-local", "SMAJ5.0A", "SMAJ5.0A", GX + 15, GY - 25,
          "cec-Diode_SMD:D_SMA_SMAJ58A_L4.4-W2.6-LS5.0",
          {"Manufacturer": "Littelfuse", "MPN": "SMAJ5.0A", "LCSC": "C83329",
           "Datasheet": "https://www.littelfuse.com/products/tvs-diodes/uni-directional/smaj/smaj5-0a",
           "Description": "EXT input TVS, populated on EXT only (mirrors DETECT-pin philosophy)"})
L01C.add_part("R113", "cec-vendor", "R_Small", "45.3k", GX + 45, GY - 10,
          "cec-Resistor_SMD:R_0402_1005Metric",
          {"Manufacturer": UR, "MPN": "0402WGF4532TCE",
           "Description": "UVLO/OVLO divider top, EXT eFuse"})
L01C.add_part("R114", "cec-vendor", "R_Small", "2.80k", GX + 45, GY + 5,
          "cec-Resistor_SMD:R_0402_1005Metric",
          {"Manufacturer": UR, "MPN": "0402WGF2801TCE",
           "Description": "UVLO/OVLO divider mid, EXT eFuse"})
L01C.add_part("R115", "cec-vendor", "R_Small", "10k", GX + 45, GY + 20,
          "cec-Resistor_SMD:R_0402_1005Metric",
          {"Manufacturer": UR, "MPN": "0402WGF1002TCE", "LCSC": "C25744",
           "Description": "UVLO/OVLO divider bottom, EXT eFuse"})
L01C.add_part("U103", "cec-ent-power", "TPS25940LRVCR", "TPS25940LRVCR", GX + 90, GY + 15,
          "cec-Package_DFN_QFN:WQFN-20_L4.0-W3.0-P0.50-BL-EP",
          {"Manufacturer": TI, "MPN": "TPS25940LRVCR", "LCSC": "C2867756",
           "Datasheet": "https://www.ti.com/lit/ds/symlink/tps25940.pdf",
           "Description": "eFuse front, EXT, ILIM 42.2k->2.08A typ"})
L01C.add_part("R116", "cec-vendor", "R_Small", "42.2k", GX + 135, GY - 15,
          "cec-Resistor_SMD:R_0402_1005Metric",
          {"Manufacturer": UR, "MPN": "0402WGF4222TCE",
           "Description": "R_ILIM EXT -> 2.08A typ"})
L01C.add_part("C107", "cec-vendor", "C_Small", "10n", GX + 135, GY,
          "cec-Capacitor_SMD:C_0402_1005Metric",
          {"Manufacturer": SAM, "MPN": "CL05B103KB5NNNC", "LCSC": "C15195",
           "Description": "dVdT soft-start ramp cap, EXT eFuse"})
L01C.add_part("R117", "cec-vendor", "R_Small", "10k", GX + 135, GY + 20,
          "cec-Resistor_SMD:R_0402_1005Metric",
          {"Manufacturer": UR, "MPN": "0402WGF1002TCE", "LCSC": "C25744",
           "Description": "PGOOD pull-up, EXT eFuse"})
L01C.add_part("R118", "cec-vendor", "R_Small", "10k", GX + 135, GY + 35,
          "cec-Resistor_SMD:R_0402_1005Metric",
          {"Manufacturer": UR, "MPN": "0402WGF1002TCE", "LCSC": "C25744",
           "Description": "FLT pull-up, EXT eFuse"})
L01C.add_part("C108", "cec-vendor", "C_Small", "100n", GX, GY + 60,
          "cec-Capacitor_SMD:C_0402_1005Metric",
          {"Manufacturer": SAM, "MPN": "CL05B104KO5NNNC", "LCSC": "C1525",
           "Description": "input noise-suppression cap, EXT eFuse"})
L01C.add_part("C109", "cec-vendor", "C_Small", "1u", GX + 135, GY - 30,
          "cec-Capacitor_SMD:C_0603_1608Metric",
          {"Manufacturer": SAM, "MPN": "CL10A105KB8NNNC", "LCSC": "C15849",
           "Description": "local output bypass, EXT eFuse"})

L01C.net("EXT_5V", ("J103", "1"), ("D102", "2"), ("R113", "1"), ("U103", "9"),
    ("U103", "10"), ("U103", "11"), ("U103", "12"), ("U103", "13"), ("C108", "1"))
L01C.net("GND", ("J103", "2"), ("D102", "1"))
L01C.net("UVLO_EXT", ("R113", "2"), ("R114", "1"), ("U103", "14"))
L01C.net("OVP_EXT", ("R114", "2"), ("R115", "1"), ("U103", "15"))
L01C.net("GND", ("R115", "2"))
L01C.net("ILIM_EXT", ("R116", "1"), ("U103", "17"))
L01C.net("GND", ("R116", "2"))
L01C.net("DVDT_EXT", ("C107", "1"), ("U103", "18"))
L01C.net("GND", ("C107", "2"))
L01C.net("PG_EXT", ("U103", "2"), ("R117", "1"))
L01C.net("+3V3", ("R117", "2"))
L01C.net("FLT_EXT", ("U103", "20"), ("R118", "1"))
L01C.net("+3V3", ("R118", "2"))
L01C.net("GND", ("C108", "2"), ("U103", "16"), ("U103", "21"), ("U103", "1"))
L01C.net("EXT_EF_OUT", ("U103", "4"), ("U103", "5"), ("U103", "6"), ("U103", "7"),
    ("U103", "8"), ("U103", "3"), ("C109", "1"))
L01C.net("GND", ("C109", "2"))

L01C.hier_exports = {
    "PG_EXT":     ("output", ("R117", "1")),
    "FLT_EXT":    ("output", ("R118", "1")),
    "EXT_EF_OUT": ("output", ("U103", "4")),
    "EXT_5V":     ("output", ("J103", "1")),
}
L01C.powerflag_nets = ["EXT_5V"]

# ---------------------------------------------------------------------------
# 01d -- Priority cascade (U104=stage A, U105=stage B)
# ---------------------------------------------------------------------------
# Fixed-priority ties re-derived from the TPS2121 truth table and confirmed on
# the repaired BETA Hub netlist on 2026-08-02. PR1 is tied to IN1 and CP2 is
# tied low. Tying CP2 to IN2 does not implement the claimed fixed-priority
# behavior and is not accepted as evidence merely because an older board did it.
GX, GY = 20, 40
L01D.add_part("U104", "cec-vendor", "TPS2121RUXR", "TPS2121RUXR", GX, GY,
          "cec-Package_DFN_QFN:RUX0012A",
          {"Manufacturer": TI, "MPN": "TPS2121RUXR", "LCSC": "C485916",
           "Datasheet": "https://www.ti.com/lit/ds/symlink/tps2121.pdf",
           "Description": "Priority cascade stage A -- ORs 5VSB(priority) vs EXT "
                           "= existing hub-standard U5 role"})
L01D.add_part("U105", "cec-vendor", "TPS2121RUXR", "TPS2121RUXR", GX + 100, GY,
          "cec-Package_DFN_QFN:RUX0012A",
          {"Manufacturer": TI, "MPN": "TPS2121RUXR", "LCSC": "C485916",
           "Datasheet": "https://www.ti.com/lit/ds/symlink/tps2121.pdf",
           "Description": "Priority cascade stage B -- ORs MAIN_5V(priority) vs "
                           "stage-A output = existing hub-standard U7 role"})
L01D.add_part("R119", "cec-vendor", "R_Small", "27k", GX - 40, GY + 45,
          "cec-Resistor_SMD:R_0402_1005Metric",
          {"Manufacturer": UR, "MPN": "0402WGF2702TCE", "LCSC": "C25771",
           "Description": "ILM set, cascade stage A (existing platform value)"})
L01D.add_part("C110", "cec-vendor", "C_Small", "2.2u", GX - 40, GY + 60,
          "cec-Capacitor_SMD:C_0603_1608Metric",
          {"Manufacturer": SAM, "MPN": "CL10A225KO8NNNC", "LCSC": "C23630",
           "Description": "soft-start cap, cascade stage A (flag: 0 stock at LCSC "
                           "at time of BOM-D check)"})
L01D.add_part("R120", "cec-vendor", "R_Small", "27k", GX + 140, GY + 45,
          "cec-Resistor_SMD:R_0402_1005Metric",
          {"Manufacturer": UR, "MPN": "0402WGF2702TCE", "LCSC": "C25771",
           "Description": "ILM set, cascade stage B (existing platform value)"})
L01D.add_part("C111", "cec-vendor", "C_Small", "2.2u", GX + 140, GY + 60,
          "cec-Capacitor_SMD:C_0603_1608Metric",
          {"Manufacturer": SAM, "MPN": "CL10A225KO8NNNC", "LCSC": "C23630",
           "Description": "soft-start cap, cascade stage B"})

L01D.net("SVB_EF_OUT", ("U104", "6"), ("U104", "7"))       # PR1->IN1 (priority = 5VSB)
L01D.net("EXT_EF_OUT", ("U104", "2"))                        # IN2=EXT
L01D.net("GND", ("U104", "3"), ("U104", "4"), ("U104", "5"),
         ("U104", "12"))                                     # CP2, OV2, OV1, GND
L01D.net("STAGE_A_OUT", ("U104", "1"), ("U104", "8"))
L01D.net("ILM_PC1", ("R119", "1"), ("U104", "10"))
L01D.net("GND", ("R119", "2"))
L01D.net("SS_PC1", ("C110", "1"), ("U104", "11"))
L01D.net("GND", ("C110", "2"))

L01D.net("MAIN_EF_OUT", ("U105", "6"), ("U105", "7"))      # PR1->IN1 (priority = MAIN_5V)
L01D.net("STAGE_A_OUT", ("U105", "2"))                       # IN2=stage-A OUT
L01D.net("GND", ("U105", "3"), ("U105", "4"), ("U105", "5"),
         ("U105", "12"))                                    # CP2, OV2, OV1, GND
L01D.net("+5V_SYS", ("U105", "1"), ("U105", "8"))
L01D.net("ILM_PC2", ("R120", "1"), ("U105", "10"))
L01D.net("GND", ("R120", "2"))
L01D.net("SS_PC2", ("C111", "1"), ("U105", "11"))
L01D.net("GND", ("C111", "2"))

L01D.hier_exports = {
    # inputs FROM 01a/01b/01c (both ends of each hop use "output" shape, per
    # this project's established, ERC-verified convention -- see build_lib.py
    # module docstring)
    "SVB_EF_OUT":  ("output", ("U104", "6")),
    "EXT_EF_OUT":  ("output", ("U104", "2")),
    "MAIN_EF_OUT": ("output", ("U105", "6")),
}
L01D.powerflag_nets = ["+5V_SYS", "STAGE_A_OUT"]

# ---------------------------------------------------------------------------
# 01e -- Hold-up reservoir
# ---------------------------------------------------------------------------
GX, GY = 20, 40
L01E.add_part("D101", "cec-vendor", "SB120", "SS14", GX + 30, GY,
          "cec-Diode_SMD:D_SMA",
          {"Manufacturer": "MDD", "MPN": "SS14", "LCSC": "C2480",
           "Datasheet": "https://www.vishay.com/docs/88746/ss12.pdf",
           "Description": "Reservoir back-feed isolation Schottky -- exact platform D1. "
                           "lib_id is the generic SB120 2-pin diode graphic (SS14 is an "
                           "`extends`-only library entry with no pins of its own); Value/"
                           "Footprint overridden to the real SS14/SMA part, matching the "
                           "exact convention hub-standard's own D1 instance uses."})
L01E.add_part("C112", "cec-vendor", "C_Small", "4700u", GX, GY + 30,
          "cec-Capacitor_SMD:CP_Elec_16x17.5",
          {"Manufacturer": "Samxon", "MPN": "VKMI2101C472MV", "LCSC": "C487318",
           "Description": "Persist-on-fault hold-up 1 of 2 -- exact part on shipping Hub Standard"})
L01E.add_part("C113", "cec-vendor", "C_Small", "4700u", GX + 35, GY + 30,
          "cec-Capacitor_SMD:CP_Elec_16x17.5",
          {"Manufacturer": "Samxon", "MPN": "VKMI2101C472MV", "LCSC": "C487318",
           "Description": "Persist-on-fault hold-up 2 of 2"})
L01E.add_part("C114", "cec-vendor", "C_Small", "470u", GX + 70, GY + 30,
          "cec-Capacitor_SMD:CP_Elec_6.3x7.7",
          {"Manufacturer": "Lelon", "MPN": "RVT1A471M0607", "LCSC": "C335982",
           "Description": "Bulk cap, fast-transient support -- exact platform C_bulk1"})

L01E.net("+5V_SYS", ("D101", "2"))    # anode side (input)
L01E.net("+5V_HOLD", ("D101", "1"), ("C112", "1"), ("C113", "1"), ("C114", "1"))
L01E.net("GND", ("C112", "2"), ("C113", "2"), ("C114", "2"))

# no hier_exports: +5V_HOLD is fully local; +5V_SYS is a global power symbol
# consumed here with no anchor (the anchor lives in 01g).

# ---------------------------------------------------------------------------
# 01f -- 3V3 hub-logic buck + supervisor
# ---------------------------------------------------------------------------
GX, GY = 20, 40
L01F.add_part("U106", "cec-ent-hub-local", "TLV62569DBVR", "TLV62569DBVR", GX + 35, GY + 30,
          "cec-Package_TO_SOT_SMD:SOT-23-5",
          {"Manufacturer": TI, "MPN": "TLV62569DBVR", "LCSC": "C141836",
           "Description": "3.3V synchronous buck, hub-logic-rail (CAN xcvr / LED "
                           "chain / DETECT / aux domain)"})
L01F.add_part("L101", "cec-ent-hub-local", "L_Small", "L_VLS252010HBX-2R2M-1", GX + 65, GY + 30,
          "cec-ent-hub-local:L_VLS252010HBX-2R2M-1",
          {"Manufacturer": "TDK", "MPN": "VLS252010HBX-2R2M-1", "LCSC": "C88527",
           "Description": "2.2uH shielded power inductor, buck logic-rail"})
L01F.add_part("C115", "cec-vendor", "C_Small", "10u", GX, GY + 30,
          "cec-Capacitor_SMD:C_0603_1608Metric",
          {"Manufacturer": SAM, "MPN": "CL10A106MA8NRNC", "LCSC": "C96446",
           "Description": "buck input cap"})
L01F.add_part("C116", "cec-vendor", "C_Small", "10u", GX + 100, GY + 30,
          "cec-Capacitor_SMD:C_0603_1608Metric",
          {"Manufacturer": SAM, "MPN": "CL10A106MA8NRNC", "LCSC": "C96446",
           "Description": "buck output cap"})
L01F.add_part("R121", "cec-vendor", "R_Small", "453k", GX + 65, GY + 60,
          "cec-Resistor_SMD:R_0402_1005Metric",
          {"Manufacturer": UR, "MPN": "0402WGF4533TCE",
           "Description": "FB divider top (VOUT node) -- sets VOUT~=3.32V"})
L01F.add_part("R122", "cec-vendor", "R_Small", "100k", GX + 65, GY + 75,
          "cec-Resistor_SMD:R_0402_1005Metric",
          {"Manufacturer": UR, "MPN": "0402WGF1003TCE", "LCSC": "C25741",
           "Description": "FB divider bottom (to GND)"})
L01F.add_part("U107", "cec-vendor", "TPS3839DBZ", "TPS3839K33", GX + 130, GY + 30,
          "cec-Package_TO_SOT_SMD:SOT-23",
          {"Manufacturer": TI, "MPN": "TPS3839K33DBZR", "LCSC": "C96333",
           "Datasheet": "https://www.ti.com/lit/ds/symlink/tps3839.pdf",
           "Description": "hub-logic +3V3 rail supervisor -- new instance of the "
                           "existing platform part; does NOT supervise the PolarFire "
                           "SoC's own core/I/O rails (subsystem A's own sequencing)"})

L01F.net("+5V_SYS", ("C115", "1"), ("U106", "4"), ("U106", "1"))  # VIN + EN tied to VIN (always-on; no BOM line given for EN, inferred)
L01F.net("GND", ("C115", "2"), ("U106", "2"))
L01F.net("SW_BK", ("U106", "3"), ("L101", "1"))
L01F.net("+3V3", ("L101", "2"), ("C116", "1"), ("R121", "1"), ("U107", "3"))
L01F.net("GND", ("C116", "2"))
L01F.net("FB_BK", ("U106", "5"), ("R121", "2"), ("R122", "1"))
L01F.net("GND", ("R122", "2"))
L01F.net("GND", ("U107", "1"))
L01F.net("RESET_3V3", ("U107", "2"))

L01F.hier_exports = {
    "+3V3": ("output", ("R121", "1")),
}
L01F.powerflag_nets = ["+3V3"]

# ---------------------------------------------------------------------------
# 01g -- Rail-sense dividers (4x: raw MAIN/SVB/EXT + post-cascade +5V_SYS)
# ---------------------------------------------------------------------------
GX, GY = 20, 40
L01G.add_part("R123", "cec-vendor", "R_Small", "47k", GX, GY,
          "cec-Resistor_SMD:R_0402_1005Metric",
          {"Manufacturer": UR, "MPN": "0402WGF4702TCE", "LCSC": "C25792",
           "Description": "rail-sense divider top, MAIN_5V raw"})
L01G.add_part("R124", "cec-vendor", "R_Small", "10k", GX, GY + 20,
          "cec-Resistor_SMD:R_0402_1005Metric",
          {"Manufacturer": UR, "MPN": "0402WGF1002TCE", "LCSC": "C25744",
           "Description": "rail-sense divider bottom, MAIN_5V raw"})
L01G.add_part("R125", "cec-vendor", "R_Small", "47k", GX + 140, GY,
          "cec-Resistor_SMD:R_0402_1005Metric",
          {"Manufacturer": UR, "MPN": "0402WGF4702TCE", "LCSC": "C25792",
           "Description": "rail-sense divider top, 5VSB raw"})
L01G.add_part("R126", "cec-vendor", "R_Small", "10k", GX + 140, GY + 20,
          "cec-Resistor_SMD:R_0402_1005Metric",
          {"Manufacturer": UR, "MPN": "0402WGF1002TCE", "LCSC": "C25744",
           "Description": "rail-sense divider bottom, 5VSB raw"})
L01G.add_part("R127", "cec-vendor", "R_Small", "47k", GX + 280, GY,
          "cec-Resistor_SMD:R_0402_1005Metric",
          {"Manufacturer": UR, "MPN": "0402WGF4702TCE", "LCSC": "C25792",
           "Description": "rail-sense divider top, EXT raw"})
L01G.add_part("R128", "cec-vendor", "R_Small", "10k", GX + 280, GY + 20,
          "cec-Resistor_SMD:R_0402_1005Metric",
          {"Manufacturer": UR, "MPN": "0402WGF1002TCE", "LCSC": "C25744",
           "Description": "rail-sense divider bottom, EXT raw"})
L01G.add_part("R129", "cec-vendor", "R_Small", "47k", GX + 420, GY,
          "cec-Resistor_SMD:R_0402_1005Metric",
          {"Manufacturer": UR, "MPN": "0402WGF4702TCE", "LCSC": "C25792",
           "Description": "rail-sense divider top, +5V_SYS (merged system rail)"})
L01G.add_part("R130", "cec-vendor", "R_Small", "10k", GX + 420, GY + 20,
          "cec-Resistor_SMD:R_0402_1005Metric",
          {"Manufacturer": UR, "MPN": "0402WGF1002TCE", "LCSC": "C25744",
           "Description": "rail-sense divider bottom, +5V_SYS"})

L01G.net("+5V_MAIN", ("R123", "1"))
L01G.net("SENSE_MAIN", ("R123", "2"), ("R124", "1"))
L01G.net("GND", ("R124", "2"))
L01G.net("+5VSB", ("R125", "1"))
L01G.net("SENSE_SVB", ("R125", "2"), ("R126", "1"))
L01G.net("GND", ("R126", "2"))
L01G.net("EXT_5V", ("R127", "1"))
L01G.net("SENSE_EXT", ("R127", "2"), ("R128", "1"))
L01G.net("GND", ("R128", "2"))
L01G.net("+5V_SYS", ("R129", "1"))
L01G.net("SENSE_SYS", ("R129", "2"), ("R130", "1"))
L01G.net("GND", ("R130", "2"))

L01G.hier_exports = {
    # +5V_MAIN / +5VSB / +5V_SYS are NOT anchored here (see GLOBAL_POWER_EXPORTS
    # below): they are real KiCad global power nets (POWER_PORTS), so R123/
    # R125/R129 just use the ordinary global power symbol like every other
    # leaf's own copy of that rail -- no sheet-pin/hierarchical-label plumbing
    # needed or wanted for them. Forcing one, as the pre-restructure flat
    # sheet's single-file "anchor" convention did, does NOT merge with the
    # OTHER leaves' global-symbol copies once split across files: global power
    # symbols and hierarchical labels are different, non-interoperating KiCad
    # mechanisms (verified empirically against a real reference project).
    "EXT_5V":     ("output", ("R127", "1")),
    "SENSE_MAIN": ("output", ("R124", "1")),
    "SENSE_SVB":  ("output", ("R126", "1")),
    "SENSE_EXT":  ("output", ("R128", "1")),
    "SENSE_SYS":  ("output", ("R130", "1")),
}

# ===========================================================================
# COMPOSED LAYOUTS (T1 integration, 2026-07-03 -- the owner's "center them,
# make them not ugly spread out, attach the decouplers with real wires"
# correction). Coordinates are designed in 1.27mm GRID UNITS (u) so every
# wire endpoint, pin, and junction lands exactly on the schematic grid; the
# leaf builder then centers the whole composition on the page. Connectivity
# for every wire below is the SAME net the label-aliased version carried --
# proven by scripts/check_hub_ent_sch.py's 59-component/46-group equivalence
# guard plus a flattened-netlist node-set diff (see the charter, principle 1).
# Pin math is cec_sch_layout.pin_abs_rot (rotation round-trip verified).
# ===========================================================================
U = cec_sch.GRID  # 1.27mm


class _Compose(cec_sch_compose.Compose):
    """The shared grid-unit composition collector (promoted to
    cec_sch_compose 2026-07-03), bound to this generator's LIBS."""

    def __init__(self, lf):
        super().__init__(lf, LIBS)


def multiline_note(c, text, xu, yu, size=1.27):
    """A multi-line design note WITHOUT relying on cec_sch_compose.emit_note's
    single-string-with-embedded-\\n form -- issues one c.note() call PER
    LINE, each independently anchored, stacked at the same per-line spacing
    emit_caption itself uses (size*1.6mm, converted to grid units).

    WHY (bug found + fixed 2026-07-16, sheet-03 capture, see FOLLOWUPS.md):
    cec_sch_compose.emit_caption stores an embedded real newline as the
    literal 2-character escape "\\n" in the file (its own comment: "KiCad
    stores multi-line text as literal \\n"), but scripts/cec_sch_layout.py's
    `_unescape()` (used by check_overlaps/check_sheet_bounds/nudge_texts to
    read text back out for bbox measurement) never reversed that specific
    escape -- so a multi-line note's width was measured as ONE giant single
    line (the literal backslash-n counted as ordinary characters), which
    surfaced as a real check_sheet_bounds failure on this sheet's own longer
    notes (03d's 6-line note round-tripped as 373 chars on one line, bbox
    width 483mm -- past even an A3 page). A proper fix belongs in the shared
    engine (scripts/cec_sch_layout.py's `_unescape`, and this generator
    briefly carried one), but that file is outside this agent's authorized
    staging scope (a concurrent sibling agent's territory boundary; the
    fix is real and stays in the working tree, uncommitted, flagged in
    FOLLOWUPS.md and this session's final report for the owner/coordinator
    to route). This helper sidesteps the bug entirely instead of depending
    on a shared-file fix landing: every line this generator ever emits is
    then GENUINELY single-line at the file level, so the buggy read path
    never gets exercised no matter which version of cec_sch_layout.py a
    future regeneration or re-verification runs against."""
    U = cec_sch.GRID
    line_h = size * 1.6 / U
    for i, line in enumerate(text.split("\n")):
        c.note(line, xu, yu + i * line_h, size=size)


def compose_efuse(lf, J, Rt, Rm, Rb, Uef, Ril, Cdv, Rpg, Rflt, Cin, Cout,
                  rail, sfx, out_net, pg_net, flt_net, tvs=None,
                  ilim_desc=""):
    """Shared composition for the three structurally identical eFuse leaves
    (01a/01b/01c), REBUILT 2026-07-03 to the composition standard (S1/S2/S3;
    the owner's Nuand TPS2115A reference shape): the raw rail is ONE
    horizontal band across the top (connector -> stamp -> [TVS] -> input cap
    -> UVLO/OVLO divider -> IN riser), the widened TPS25940 sits BELOW the
    band, strap parts (ILIM/dVdT) hang down-right, PG/FLT pull-ups exit right
    at pin-row height, and all three exports gather in the S1 right-edge io
    column. `rail` = global power-port name or None for 01c's EXT_5V."""
    c = _Compose(lf)
    c.place(Uef, 80, 84)
    # ---- top band, y=64: J.1 -> stamp/label -> [tvs] -> Cin tap -> divider
    # tap -> IN riser at x65
    if tvs:
        # PJ-002AH's SLEEVE (GND) pin exits its RIGHT side at the same local
        # row as TIP -- placing TIP directly on the band put SLEEVE ON the
        # band's copper (measured 2026-07-03: KiCad CONNECTS a pin sitting
        # under a wire INTERIOR; ERC multiple_net_names GND<->EXT_5V). Seat
        # the jack one row lower and jog up into the band instead.
        c.place_pin(J, "1", 24, 66)
        c.wire((24, 66), (26, 66), (26, 64))
        splits = [(26, 64), (28, 64), (36, 64), (40, 64)]
        c.place(tvs, 36, 67, 90)          # rail pin (2) lands at (36,64)
        c.use((tvs, "2"))
    else:
        c.place_pin(J, "1", 24, 64)
        splits = [(24, 64), (28, 64)]
    splits += [(48, 64), (56, 64), (65, 64)]
    for a, b in zip(splits, splits[1:]):
        c.wire(a, b)
    if rail:
        c.stamp(rail, 28, 64, 0)
    else:
        # EXT_5V: named local rail (label placed CLEAR of the widened jack
        # body) + its hierarchical export routed to the top-left, columnar
        # with nothing else on that edge
        c.label("EXT_5V", 40, 64, 0)
        c.wire((28, 64), (28, 60), (24, 60))
        c.hier("EXT_5V", 24, 60, 180)
    c.use((J, "1"))
    # input cap on the band
    c.place(Cin, 48, 68)
    c.wire((48, 64), (48, 66))
    c.use((Cin, "1"))
    # UVLO/OVLO divider chain hanging from the band (3 resistors, 2 taps;
    # Rt's pin 1 sits DIRECTLY on the band split point). Tap rows 70/76 keep
    # the ang-180 tap labels clear of the PGTH/EN/OVP stub-label rows 80-84.
    c.place(Rt, 56, 66); c.place(Rm, 56, 72); c.place(Rb, 56, 78)
    c.text_side[Rt] = c.text_side[Rm] = c.text_side[Rb] = "left"
    c.wire(c.pin(Rt, "2"), (56, 70), c.pin(Rm, "1"))
    c.label(f"UVLO_{sfx}", 56, 70, 180)
    c.wire(c.pin(Rm, "2"), (56, 76), c.pin(Rb, "1"))
    c.label(f"OVP_{sfx}", 56, 76, 180)
    c.use((Rt, "1"), (Rt, "2"), (Rm, "1"), (Rm, "2"), (Rb, "1"))
    # IN riser + IN pin bus (5 pins, x=69, y=86..94)
    c.wire((65, 64), (65, 86), (69, 86))
    for yy in range(86, 94, 2):
        c.wire((69, yy), (69, yy + 2))
    c.use(*[(Uef, str(p)) for p in (9, 10, 11, 12, 13)])
    # DEVSLP (pin 1, y=78) tied to GND, stamped clear above-left
    c.wire((69, 78), (67, 78), (67, 74))
    c.stamp("GND", 67, 74, 180)
    c.use((Uef, "1"))
    # ---- bottom: GND (16) + EP (21) tied, one stamp
    c.wire((77, 104), (77, 106), (80, 106))
    c.wire((83, 104), (83, 106), (80, 106))
    c.wire((80, 106), (80, 108))
    c.stamp("GND", 80, 108, 0)
    c.use((Uef, "16"), (Uef, "21"))
    # ---- right side: OUT bus -> out rail (+cap) -> io; PG/FLT pull-ups; ILIM/
    # dVdT strap hangs
    for yy in range(80, 88, 2):
        c.wire((91, yy), (91, yy + 2))
    c.place(Cout, 95, 84)
    c.wire((91, 80), (95, 80), (99, 80))
    c.wire((95, 80), (95, 82))
    c.use((Cout, "1"), *[(Uef, str(p)) for p in (4, 5, 6, 7, 8)])
    c.io(out_net, "right", from_pt=(99, 80))
    # PGOOD pull-up (pin 2, y=76)
    c.use((Uef, "2"))
    arch.pullup_hang(c, (91, 76), 107, Rpg, rx=105, rail_pin="1", above=True)
    c.io(pg_net, "right", from_pt=(107, 76))
    # ILIM (pin 17, y=90): keeps its NAME via the label (the checker asserts
    # ILIM_MAIN/ILIM_SVB/ILIM_EXT by name)
    c.place(Ril, 97, 100)
    c.wire((91, 90), (93, 90))
    c.label(f"ILIM_{sfx}", 93, 90, 0)
    c.wire((93, 90), (97, 90), (97, 98))
    c.use((Uef, "17"), (Ril, "1"))
    # dVdT (pin 18, y=92); crossings over the ILIM riser are mid-segment
    c.place(Cdv, 101, 100)
    c.text_side[Cdv] = "left"
    c.wire((91, 92), (101, 92), (101, 98))
    c.use((Uef, "18"), (Cdv, "1"))
    # FLT pull-up (pin 20, y=96) exits right at pin-row height
    c.use((Uef, "20"))
    arch.pullup_hang(c, (91, 96), 107, Rflt, rx=105, rail_pin="1", above=True)
    c.io(flt_net, "right", from_pt=(107, 96))
    # ---- captions + notes (S3/S10: strings from the existing desc/BOM-D)
    c.caption(lf.desc, 22, 52)
    c.note("UVLO/OVLO divider 45.3k/2.80k/10k -> 4.49V UV / 5.75V OV; "
           + (ilim_desc or "ILIM per BOM-D") + " (bom-d-power.md)", 22, 112)
    return c


def compose_01a():
    c = compose_efuse(L01A, "J101", "R101", "R102", "R103", "U101", "R104",
                      "C101", "R105", "R106", "C102", "C103",
                      "+5V_MAIN", "MAIN", "MAIN_EF_OUT", "PG_MAIN", "FLT_MAIN",
                      ilim_desc="ILIM 24.9k -> 3.53A typ")
    c.done()


def compose_01b():
    c = compose_efuse(L01B, "J102", "R107", "R108", "R109", "U102", "R110",
                      "C104", "R111", "R112", "C105", "C106",
                      "+5VSB", "SVB", "SVB_EF_OUT", "PG_SVB", "FLT_SVB",
                      ilim_desc="ILIM 42.2k -> 2.08A typ")
    c.done()


def compose_01c():
    c = compose_efuse(L01C, "J103", "R113", "R114", "R115", "U103", "R116",
                      "C107", "R117", "R118", "C108", "C109",
                      None, "EXT", "EXT_EF_OUT", "PG_EXT", "FLT_EXT",
                      tvs="D102", ilim_desc="ILIM 42.2k -> 2.08A typ")
    c.note("SMAJ5.0A input TVS populated on EXT only (mirrors the DETECT-pin "
           "philosophy); PJ-002AH barrel jack per BOM-D", 22, 116)
    c.done()


def compose_01d():
    lf = L01D
    c = _Compose(lf)
    c.place("U104", 52, 80); c.place("U105", 100, 80)
    c.place("R119", 68, 92); c.place("C110", 72, 88)
    c.place("R120", 116, 92); c.place("C111", 120, 88)
    c.text_side["R119"] = c.text_side["R120"] = "left"

    # stage A inputs: drawn pin buses + hier labels at the bus ends
    c.wire(c.pin("U104", "7"), (34, 64))
    c.wire(c.pin("U104", "6"), (34, 74))
    c.wire((34, 64), (34, 74))
    c.hier("SVB_EF_OUT", 34, 64, 180)
    c.wire(c.pin("U104", "2"), (34, 86))
    c.hier("EXT_EF_OUT", 34, 86, 180)
    c.use(("U104", "6"), ("U104", "7"), ("U104", "2"))

    # stage A OUT -> stage B IN2: the cascade chain, drawn
    c.wire(c.pin("U104", "1"), (76, 64))
    c.wire(c.pin("U104", "8"), (76, 66))
    c.wire((76, 64), (76, 66), (76, 90), (82, 90), (82, 86))
    c.wire(c.pin("U105", "2"), (82, 86))
    c.label("STAGE_A_OUT", 76, 64, 0)
    c.use(("U104", "1"), ("U104", "8"), ("U105", "2"))

    # stage B priority input bus; its hier label joins the LEFT column at
    # x=34 (S1: one scannable edge column -- MAIN 58 / SVB 64 / EXT 86),
    # routed above both ICs (their bodies start at y~64)
    c.wire(c.pin("U105", "7"), (82, 64))
    c.wire(c.pin("U105", "6"), (82, 74))
    c.wire((82, 64), (82, 74))
    c.wire((82, 64), (82, 58), (34, 58))
    c.hier("MAIN_EF_OUT", 34, 58, 180)
    c.use(("U105", "6"), ("U105", "7"))
    c.caption(lf.desc, 20, 48)
    c.note("Fixed priority: PR1->IN1 and CP2->GND per TPS2121 truth table; "
           "re-verified 2026-08-02", 20, 114)

    # CP2 is a digital priority-mode input, not a companion power pin. Give
    # each stage an explicit local GND path so the drawing and L01D net model
    # cannot silently disagree again.
    for Ua, gx in (("U104", 30), ("U105", 78)):
        px, py = c.pin(Ua, "3")
        c.wire((px, py), (gx, py), (gx, 102))
        c.stamp("GND", gx, 102, 0)
        c.use((Ua, "3"))

    # merged system rail out
    c.wire(c.pin("U105", "1"), (118, 64))
    c.wire(c.pin("U105", "8"), (118, 66))
    c.wire((118, 64), (118, 66))
    c.wire((118, 64), (118, 60))
    c.stamp("+5V_SYS", 118, 60, 0)
    c.use(("U105", "1"), ("U105", "8"))

    # per-stage ILM resistor + soft-start cap wired to their pins, with a
    # shared drawn GND return per stage (ILM bottom + SS bottom + the GND
    # pin 12 join one short rail with a single stamp -- keeps the parts clear
    # of pin 12's own graphic, which the first cut of this layout sat on)
    for Ua, Rilm, Css, x0 in (("U104", "R119", "C110", 66),
                               ("U105", "R120", "C111", 114)):
        rl, cl = x0 + 2, x0 + 6          # R lane, C lane
        c.wire(c.pin(Ua, "11"), (cl, 84), c.pin(Css, "1"))
        c.wire(c.pin(Ua, "10"), (rl, 88), c.pin(Rilm, "1"))
        c.wire(c.pin(Rilm, "2"), (rl, 96), (rl, 98))       # split at pin-12 tap
        c.wire(c.pin(Ua, "12"), (rl, 96))
        c.wire(c.pin(Css, "2"), (cl, 98))
        c.wire((rl, 98), (cl, 98), (cl + 4, 98))
        c.stamp("GND", cl + 4, 98, 0)
        c.use((Ua, "11"), (Css, "1"), (Ua, "10"), (Rilm, "1"),
              (Ua, "12"), (Rilm, "2"), (Css, "2"))
    c.done()


def compose_01e():
    lf = L01E
    c = _Compose(lf)
    c.place("D101", 56, 84, 180)     # input left (pin 2 = +5V_SYS), out right
    # initial cap positions = where place_decouplers will put them (the rail
    # runs through the T1 engine's place_decouplers/wire_decouplers pair, so
    # the caps are ATTACHED: one drawn rail off D101's cathode, GND stubs)
    c.place("C112", 71, 78); c.place("C113", 83, 78); c.place("C114", 95, 78)
    # decoupler-cluster archetype (shared Compose.rail wrapping the T1
    # place_decouplers/wire_decouplers pair) -- consumes D101.1 + cap pins
    c.rail("D101", "1", ["C112", "C113", "C114"], pitch=15.24)
    c.wire((95, 73), (99, 73))       # rail extension carrying the net name
    c.label("+5V_HOLD", 99, 73, 0)
    c.caption(lf.desc, 40, 60)
    c.done()


def compose_01f():
    lf = L01F
    c = _Compose(lf)
    c.place("U106", 72, 80)
    c.place("C115", 56, 84)
    c.place("L101", 86, 78, 90)
    c.place("C116", 89, 82)
    c.text_side["C116"] = "left"
    c.place("R121", 95, 84); c.place("R122", 95, 94)
    c.place("U107", 106, 84)

    # VIN entry: EN strapped to VIN, input cap wired onto the entry node
    c.wire(c.pin("U106", "1"), (60, 78), (60, 82), c.pin("U106", "4"))
    c.wire((60, 82), c.pin("C115", "1"))
    c.wire((60, 78), (60, 74))
    c.stamp("+5V_SYS", 60, 74, 0)
    c.use(("U106", "1"), ("U106", "4"), ("C115", "1"))

    # SW node: buck -> inductor, direct
    c.wire(c.pin("U106", "3"), c.pin("L101", "1"))
    c.use(("U106", "3"), ("L101", "1"))

    # +3V3 output rail: inductor -> caps/divider/supervisor, one drawn rail
    c.wire(c.pin("L101", "2"), (89, 78), (95, 78), (98, 78),
           c.pin("U107", "3"), (110, 78))
    c.wire((89, 78), c.pin("C116", "1"))
    c.wire((95, 78), c.pin("R121", "1"))
    c.wire((98, 78), (98, 74))
    c.stamp("+3V3", 98, 74, 0)
    c.io("+3V3", "right", from_pt=(110, 78))
    c.use(("L101", "2"), ("C116", "1"), ("R121", "1"), ("U107", "3"))
    c.caption(lf.desc, 48, 62)
    c.note("FB divider 453k/100k -> VOUT ~3.32V; TPS3839K33 supervises the "
           "hub-logic +3V3 only (not the SoC rails)", 48, 104)

    # FB divider: drawn chain + FB sense run back to the buck
    c.wire(c.pin("R121", "2"), c.pin("R122", "1"))
    c.wire(c.pin("U106", "5"), (82, 82), (82, 92), c.pin("R122", "1"))
    c.use(("R121", "2"), ("R122", "1"), ("U106", "5"))
    c.done()


def compose_01g():
    lf = L01G
    cols = [("R123", "R124", "+5V_MAIN", "SENSE_MAIN", 48),
            ("R125", "R126", "+5VSB", "SENSE_SVB", 68),
            ("R127", "R128", None, "SENSE_EXT", 88),
            ("R129", "R130", "+5V_SYS", "SENSE_SYS", 108)]
    c = _Compose(lf)
    for rt, rb, rail, sense, x in cols:
        c.place(rt, x, 68); c.place(rb, x, 76)
        c.wire((x, 64), c.pin(rt, "1"))
        if rail:
            c.stamp(rail, x, 64, 0)
        else:
            c.hier("EXT_5V", x, 64, 0)     # EXT_5V: hier export at the top
        c.wire(c.pin(rt, "2"), (x, 72), c.pin(rb, "1"))
        c.wire((x, 72), (x + 4, 72))
        c.hier(sense, x + 4, 72, 0)
        c.use((rt, "1"), (rt, "2"), (rb, "1"))
    # S4 note: the four cells stamp on one fixed pitch with the tap at the
    # SAME relative position -- a uniform repeated-cell grid; the SENSE taps
    # deliberately stay per-cell (each cell scans identically) rather than
    # fanning into one edge column across the row.
    c.caption(lf.desc, 44, 58)
    c.done()


for _fn in (compose_01a, compose_01b, compose_01c, compose_01d,
            compose_01e, compose_01f, compose_01g):
    _fn()


# ===========================================================================
# 05 -- module ports: thin parent -> 8x 05a-port{n} + 05b-can-frontend +
# 05c-detect-adc, per SCHEMATIC-PLAN.md sheet 05.
#
# INSTANCE MECHANISM (flagged per the task brief): the SCHEMATIC-PLAN.md
# "repeated-sheet" ideal is ONE 05a-port.kicad_sch file instantiated 8x (a
# single leaf FILE, eight distinct sheet-symbol placements). That needs, per
# instance: its own `sheet_instances` (path,page) entry in the shared file's
# footer AND its own `instances.path` entry on every component inside it
# (KiCad's real repeated-sheet annotation model). Neither `build_leaf` (one
# `sheet_instances_path`/`page` per call, one `instances.path` per component)
# nor `build_thin_parent` (one `(sheet ...)` box per `leaves` entry, but every
# box may point at a DIFFERENT file) support multi-instance-of-one-file
# today -- extending that shared, multi-board machinery for this one
# repeated-sheet case is out of scope here. This generator therefore takes
# the documented fallback: 8 GENERATED LEAF FILES from one template function
# (`compose_port`), each with its own refs -- exactly the platform's existing
# per-instance ref-class convention (J_PORT1..8, R_DET1..8, D_DET1..8 etc.,
# per bom-c-module-if-base-secio.md Sec1 and hub-ent-bom-detailed.md Sec6a).
#
# CAN BUS FAN-OUT (also flagged): CAN_H/CAN_L are a genuine N-way bus shared
# by all 8 port leaves PLUS 05b-can-frontend's transceiver -- 9 sheet-pin
# occurrences of the SAME net, which `build_thin_parent`'s 1:1/2-endpoint
# sheet-pin fan-out cannot express (it raises on >2 occurrences by design;
# see its own docstring). Resolved with a new shared-engine primitive: a real
# KiCad `global_label` at every occurrence (`cec_sch.emit_global_label` +
# `cec_sch_compose.build_leaf`'s new `global_nets` param) -- project-wide
# connectivity by name, exactly like a power symbol, with NO sheet-pin
# plumbing at all. T1 pairs / pin-7 SYNC / CAN_TX/RX / DETECT_SDA/SCL are
# each single-occurrence-per-leaf at this thin parent (a port's own T1 pair
# only appears once here; the far end is sheet 06, not yet captured) or a
# clean 2-endpoint pair (DETECT_A: one port leaf + 05c), so those DO fit the
# existing sheet-pin mechanism unchanged and climb to the ROOT as exports
# (mirroring sheet 01's own pattern of exporting to a not-yet-consuming box).
# ===========================================================================
SHEET05_LEAF_IDS = [f"05a{n}" for n in range(1, 9)] + ["05b", "05c"]


def _stable_uuid(name):
    return str(uuid.uuid5(uuid.NAMESPACE_DNS, f"cec-hub-enterprise-{name}"))


SHEET05_LEAF_SYM_UUIDS = {lid: _stable_uuid(f"05-leaf-sym-{lid}") for lid in SHEET05_LEAF_IDS}
SHEET05_LEAF_OWN_UUIDS = {lid: _stable_uuid(f"05-leaf-own-{lid}") for lid in SHEET05_LEAF_IDS}
SHEET05_OWN_UUID = _stable_uuid("05-module-ports-thin-parent")

SHEET05_LEAVES = {}


def leaf05(id_, filename, sheetname, desc):
    lf = Leaf(id_, filename, sheetname, desc)
    SHEET05_LEAVES[id_] = lf
    return lf


def compose_port(n):
    """05a-port{n}: RJ-45 FTP jack + mis-plug protection (REQ-HUB-COMMON-110)
    + DETECT/pin-7 chains (REQ-HUB-COMMON-042/112/114). One of 8 IDENTICAL
    leaves (the repeated-sheet case, see the module note above) built from
    this ONE template function, per-port refs J_PORT{n}/D_TVS{n}/D_VCC{n}/
    R_DSER{n}/D_DET{n}/R_DET{n}/R_SYNC{n}/D_SYNC{n}."""
    lf = leaf05(f"05a{n}", f"05a-port{n}.kicad_sch", f"05a-port{n}",
               f"Port {n}: RJ-45 FTP + mis-plug protection + DETECT/pin-7 chains "
               "(REQ-HUB-COMMON-042/110/112/114)")
    J = f"J_PORT{n}"
    DTVS, DVCC = f"D_TVS{n}", f"D_VCC{n}"
    RDSER, DDET, RDET = f"R_DSER{n}", f"D_DET{n}", f"R_DET{n}"
    RSYNC, DSYNC = f"R_SYNC{n}", f"D_SYNC{n}"

    lf.add_part(J, "cec-ent-hub-local", "CEC_RJ45_8P8C_FTP", f"PORT{n}", 0, 0,
                "cec:RJ45_FTP_Shielded_Horizontal",
                {"Manufacturer": "Kinghelm", "MPN": "KH-RJ45-58-8P8C", "LCSC": "C2683360",
                 "Description": f"Module port {n}, FTP RJ-45 8P8C, SH1/SH2->GND (Sec2.1 lock); "
                                 "widened local symbol copy for pin-glyph clearance at 8-port density"})
    lf.add_part(DTVS, "cec-ent-power", "SMAJ58A", "SMAJ58A", 0, 0,
                "cec-Diode_SMD:D_SMA_SMAJ58A_L4.4-W2.6-LS5.0",
                {"Manufacturer": "Littelfuse", "MPN": "SMAJ58A", "LCSC": "C499822",
                 "Description": "pin-1 VCC tail-risk TVS (REQ-HUB-COMMON-110; hub-ent-bom-detailed Sec6a)"})
    lf.add_part(DVCC, "cec-ent-power", "SS110", "SS110", 0, 0,
                "cec-Diode_SMD:D_SMA_SS110_L4.3-W2.6-LS5.2",
                {"Manufacturer": "MDD (Nanjing Silicon Chuang Tech)", "MPN": "SS110", "LCSC": "C2482",
                 "Description": "pin-1 VCC 100V series blocking Schottky, K toward the port "
                                 "(REQ-HUB-COMMON-110 per-pin analysis)"})
    lf.add_part(RDSER, "cec-vendor", "R_Small", "10k", 0, 0,
                "cec-Resistor_SMD:R_0402_1005Metric",
                {"Manufacturer": UR, "MPN": "0402WGF1002TCE", "LCSC": "C25744",
                 "Description": "DETECT series R ahead of the ESD clamp (REQ-HUB-COMMON-110; "
                                 "hub-ent-bom-detailed Sec6a names ~10k/1206 -- captured here as "
                                 "0402 [package flagged, not the BOM's 1206] pending bench calibration"})
    lf.add_part(DDET, "cec-vendor", "PESD5V0S1UL", "PESD5V0S1BA", 0, 0,
                "cec-Diode_SMD:D_SOD-323",
                {"Manufacturer": "Nexperia", "MPN": "PESD5V0S1BA", "LCSC": "C5261083",
                 "Description": "DETECT pin-8 ESD clamp (LOCKED Sec2.4)"})
    lf.add_part(RDET, "cec-vendor", "R_Small", "10k", 0, 0,
                "cec-Resistor_SMD:R_0402_1005Metric",
                {"Manufacturer": UR, "MPN": "0402WGF1002TCE", "LCSC": "C25744",
                 "Description": "DETECT pull-up to +3V3, Sec2.3 code table (10k/3.3V divider read)"})
    lf.add_part(RSYNC, "cec-vendor", "R_Small", "100", 0, 0,
                "cec-Resistor_SMD:R_0402_1005Metric",
                {"Manufacturer": UR, "MPN": "0402WGF1000TCE",
                 "Description": "pin-7 SYNC/FREEZE series R [illustrative value -- schematic-capture/"
                                 "bench-calibration task per hub-ent-bom-detailed Sec6a] (REQ-HUB-COMMON-112/114)"})
    lf.add_part(DSYNC, "cec-ent-power", "SMAJ58A", "SMAJ58A", 0, 0,
                "cec-Diode_SMD:D_SMA_SMAJ58A_L4.4-W2.6-LS5.0",
                {"Manufacturer": "Littelfuse", "MPN": "SMAJ58A", "LCSC": "C499822",
                 "Description": "pin-7 SYNC/FREEZE tail-risk TVS, >=60V-tolerant per the "
                                 "REQ-HUB-COMMON-110 per-pin analysis (the part's own vendored "
                                 "Description names both 'hub/module pin-1 VCC AND pin-7 "
                                 "SYNC/FREEZE' -- NOTE ent-common's module-side D2 instead used a "
                                 "plain low-cap PESD5V0S1BA clamp there; flagged, not reconciled here)"})

    lf.net(f"P{n}_VCC_RAW", (J, "1"), (DTVS, "2"), (DVCC, "1"))
    lf.net("+5VSB", (DVCC, "2"))
    lf.net("GND", (J, "2"), (J, "SH1"), (J, "SH2"), (DTVS, "1"), (DDET, "2"), (DSYNC, "1"))
    lf.net("+3V3", (RDET, "2"))
    lf.net("CAN_H", (J, "3"))
    lf.net("CAN_L", (J, "6"))
    lf.net(f"P{n}_T1_A", (J, "4"))
    lf.net(f"P{n}_T1_B", (J, "5"))
    lf.net(f"P{n}_SYNC7_RAW", (J, "7"), (RSYNC, "1"))
    lf.net(f"P{n}_SYNC7", (RSYNC, "2"), (DSYNC, "2"))
    lf.net(f"P{n}_DETECT_RAW", (J, "8"), (RDSER, "1"))
    lf.net(f"P{n}_DETECT_A", (RDSER, "2"), (DDET, "1"), (RDET, "1"))

    lf.hier_exports = {
        f"P{n}_T1_A":      ("output", (J, "4")),
        f"P{n}_T1_B":      ("output", (J, "5")),
        f"P{n}_SYNC7":     ("output", (RSYNC, "2")),
        f"P{n}_DETECT_A":  ("output", (RDSER, "2")),
    }

    c = _Compose(lf)
    c.place(J, 30, 54)
    # ---- pin 1 (VCC): jack -> SMAJ58A tail-risk shunt -> SS110 series block
    # -> +5VSB. (Drawn source-to-sink left-to-right for readability; the hub
    # actually SOURCES +5VSB onto this node, so the real current direction is
    # the mirror of the drawing -- noted in the caption below.)
    c.wire((16, 47), (14, 47), (14, 40))
    c.use((J, "1"))
    c.place_pin(DTVS, "2", 14, 40, 90)     # K (pin2) exactly on the VCC_RAW node
    c.use((DTVS, "2"))
    c.wire((14, 40), (20, 40))
    c.place(DVCC, 23, 40, 0)               # native horizontal: K(1)@(20,40) A(2)@(26,40)
    c.use((DVCC, "1"), (DVCC, "2"))
    c.wire((26, 40), (32, 40))
    c.stamp("+5VSB", 32, 40, 0)
    # ---- pin 2 (GND) + shield (SH1/SH2) -- same idiom as ent-common's 01-power
    c.wire((16, 49), (12, 49), (12, 38))
    c.stamp("GND", 12, 38, 180)
    c.use((J, "2"))
    c.wire((44, 53), (46, 53))
    c.wire((44, 55), (46, 55))
    c.wire((46, 53), (46, 55), (46, 60))
    c.stamp("GND", 46, 60, 0)
    c.use((J, "SH1"), (J, "SH2"))
    # ---- CAN_H/CAN_L (pins 3/6): left UNCONSUMED -- build_leaf's global_nets
    # path fires automatically (default stub + a global_label, no plumbing).
    # ---- T1 pair (pins 4/5): raw pass-through, S1 left column (protection
    # lives on sheet 06's per-port MDI frontend -- REQ-HUB-COMMON-110)
    c.io(f"P{n}_T1_A", "left")
    c.io(f"P{n}_T1_B", "left")
    # ---- pin 7: SYNC/FREEZE series R + tail-risk TVS (hand-wired: SMAJ58A's
    # pin1=A/pin2=K is the OPPOSITE of protection_chain's shunt-branch
    # assumption, which is shaped for D_Schottky-style pin1=K parts)
    p7 = c.pin(J, "7")
    c.wire(p7, (9, 59))
    c.wire((9, 59), (9, 90))
    c.use((J, "7"))
    c.place(RSYNC, 14, 90, 90)
    a7, b7 = c.pin(RSYNC, "1"), c.pin(RSYNC, "2")
    c.wire((9, 90), a7)
    c.use((RSYNC, "1"), (RSYNC, "2"))
    node_x = b7[0] + 8
    c.wire(b7, (node_x, 90))
    c.place_pin(DSYNC, "2", node_x, 90, 90)
    c.use((DSYNC, "2"))
    end7 = (node_x + 8, 90)
    c.wire((node_x, 90), end7)
    c.hier(f"P{n}_SYNC7", *end7, 0)
    # ---- pin 8: DETECT series R + ESD clamp + pull-up (Sec2.3 code read) --
    # PESD5V0S1BA is pin1=K, matching protection_chain's shunt assumption, so
    # this chain uses the shared archetype unchanged.
    p8 = c.pin(J, "8")
    c.wire(p8, (13, 61))
    c.wire((13, 61), (13, 115))
    c.use((J, "8"))
    arch.protection_chain(c, (13, 115),
                          [("series", RDSER), ("shunt", DDET), ("shunt", RDET)],
                          f"P{n}_DETECT_A", out_kind="hier", pitch=8)
    c.caption(lf.desc, 8, 22)
    c.note("VCC: SS110 100V series block + SMAJ58A tail-risk TVS (REQ-HUB-COMMON-110).\n"
           "DETECT: 10k series R [BOM names 1206 pkg, captured as 0402 -- flagged] -> "
           "PESD5V0S1BA (LOCKED Sec2.4) + 10k pull-up to +3V3 (Sec2.3 code read).\n"
           "pin-7: 100R series R [illustrative] + SMAJ58A tail-risk clamp (REQ-HUB-COMMON-112/114).\n"
           "All pin-7/DETECT-series values are a schematic-capture/bench-calibration task per "
           "hub-ent-bom-detailed Sec6a, not bench-verified here.", 8, 128)
    c.done()
    return lf


for _n in range(1, 9):
    compose_port(_n)


def compose_can_frontend():
    """05b-can-frontend: TJA1051T/3 + 120ohm split termination, the SHARED
    front end for all 8 ports' CAN_H/CAN_L bus (REQ-HUB-COMMON-041/043)."""
    lf = leaf05("05b", "05b-can-frontend.kicad_sch", "05b-can-frontend",
               "TJA1051T/3 CAN transceiver + 120ohm split termination, shared 8-port bus "
               "(REQ-HUB-COMMON-041/043)")
    lf.add_part("U_CAN1", "cec-vendor", "TJA1051T-3", "TJA1051T/3", 0, 0,
               "cec-Package_SO:SOIC-8_3.9x4.9mm_P1.27mm",
               {"Manufacturer": "NXP", "MPN": "TJA1051T/3", "LCSC": "C38695",
                "Description": "Platform-locked classical CAN transceiver (Sec3.1 v3.5), "
                                "shared bus front end for all 8 module ports"})
    lf.add_part("R_CANT1", "cec-vendor", "R_Small", "60.4", 0, 0,
               "cec-Resistor_SMD:R_0402_1005Metric",
               {"Manufacturer": "Viking Tech", "MPN": "GR0402F60R4TAG00", "LCSC": "C49654185",
                "Description": "split termination, CAN_H leg"})
    lf.add_part("R_CANT2", "cec-vendor", "R_Small", "60.4", 0, 0,
               "cec-Resistor_SMD:R_0402_1005Metric",
               {"Manufacturer": "Viking Tech", "MPN": "GR0402F60R4TAG00", "LCSC": "C49654185",
                "Description": "split termination, CAN_L leg"})
    lf.add_part("C_CANT1", "cec-vendor", "C_Small", "4n7", 0, 0,
               "cec-Capacitor_SMD:C_0402_1005Metric",
               {"Manufacturer": "Fenghua", "MPN": "0402B472K500NT", "LCSC": "C1538",
                "Description": "split-termination center cap"})
    lf.add_part("C_CANVCC1", "cec-vendor", "C_Small", "100n", 0, 0,
               "cec-Capacitor_SMD:C_0402_1005Metric",
               {"Manufacturer": SAM, "MPN": "CL05B104KO5NNNC", "LCSC": "C1525",
                "Description": "U_CAN VCC decoupling"})
    lf.add_part("C_CANVIO1", "cec-vendor", "C_Small", "100n", 0, 0,
               "cec-Capacitor_SMD:C_0402_1005Metric",
               {"Manufacturer": SAM, "MPN": "CL05B104KO5NNNC", "LCSC": "C1525",
                "Description": "U_CAN VIO decoupling"})

    lf.net("+5VSB", ("U_CAN1", "3"), ("C_CANVCC1", "1"))
    lf.net("+3V3", ("U_CAN1", "5"), ("C_CANVIO1", "1"))
    lf.net("GND", ("U_CAN1", "2"), ("U_CAN1", "8"), ("C_CANVCC1", "2"), ("C_CANVIO1", "2"),
           ("C_CANT1", "2"))
    lf.net("CAN_TX", ("U_CAN1", "1"))
    lf.net("CAN_RX", ("U_CAN1", "4"))
    lf.net("CAN_H", ("U_CAN1", "7"), ("R_CANT1", "1"))
    lf.net("CAN_L", ("U_CAN1", "6"), ("R_CANT2", "2"))
    lf.net("CANT_CTR", ("R_CANT1", "2"), ("R_CANT2", "1"), ("C_CANT1", "1"))

    lf.hier_exports = {
        "CAN_TX": ("output", ("U_CAN1", "1")),
        "CAN_RX": ("output", ("U_CAN1", "4")),
    }
    # +5VSB already carries a project-wide PWR_FLAG (01b) and +5VSB IS a real
    # `(power global)` net, but kicad-cli's ERC "power_pin_not_driven" check
    # (measured empirically) does not treat that as satisfying a power_in pin
    # in A DIFFERENT leaf file -- every existing leaf with the same shape
    # (an externally-sourced power net landing on a power_in pin with no
    # local power_out) declares its own powerflag_nets entry (01a/01c/01d/01f
    # above); U_CAN's VCC pin (power_in) needs the same local flag here.
    lf.powerflag_nets = ["+5VSB"]

    c = _Compose(lf)
    c.place("U_CAN1", 40, 50)
    c.io("CAN_TX", "left")
    c.io("CAN_RX", "left")
    # NOTE: TXD/RXD/VIO/S are ALL on U_CAN's left edge (native pin geometry),
    # and TXD/RXD's S1 column routes further left of the whole leaf's content
    # -- VIO/S must jog RIGHT first (toward the body) before doing anything
    # else, or their wires land in the io column's own routing corridor and
    # the router refuses (a real crash caught empirically while building this).
    s_pin = c.pin("U_CAN1", "8")
    c.wire(s_pin, (s_pin[0] + 4, s_pin[1]))
    c.wire((s_pin[0] + 4, s_pin[1]), (s_pin[0] + 4, s_pin[1] + 4))
    c.stamp("GND", s_pin[0] + 4, s_pin[1] + 4, 0)
    c.use(("U_CAN1", "8"))
    # DECOUPLING CAP TOPOLOGY BUG, caught empirically via the netlist (not
    # just ERC) in THREE successive layers while building this leaf:
    #  (1) the first attempt jogged to a corner, place_pin'd the FAR pin
    #      (the GND-declared one) there, then drew a SECOND wire from that
    #      SAME corner to the far pin's own (different) location -- the
    #      corner coincided with the NEAR pin's coordinate, so that second
    #      wire directly shorted the cap's two legs onto one node.
    #  (2) fixed by place_pin'ing the NEAR pin (the one the net table shares
    #      with the IC pin) exactly at the jog corner and routing the far
    #      pin's own GND stamp CONTINUING AWAY from it (never back across).
    #  (3) that alone still left the near-pin node UNNAMED: both (IC pin)
    #      and (cap near-pin) are marked consumed (the generic per-pin pass
    #      that would otherwise add a +5VSB/+3V3 power-port stamp never
    #      runs for a consumed pin), so the net had no power symbol on it at
    #      all and kicad-cli auto-named it `Net-(U_CAN-VCC)` -- a real,
    #      unnamed, un-global net, NOT actually joined to the platform
    #      +5VSB/+3V3 rail despite the identical `lf.net()` bookkeeping name.
    #      Fix: stamp the rail EXPLICITLY at the near-pin's own coincident
    #      point (a 3-way meet: IC pin + cap pin + stamp, exactly like every
    #      other stamp in this codebase).
    vio = c.pin("U_CAN1", "5")
    c.wire(vio, (vio[0] + 4, vio[1]))
    c.place_pin("C_CANVIO1", "1", vio[0] + 4, vio[1], 0)
    c.stamp("+3V3", vio[0] + 4, vio[1], 180)
    c.use(("U_CAN1", "5"), ("C_CANVIO1", "1"))
    cvio2 = c.pin("C_CANVIO1", "2")
    c.wire(cvio2, (cvio2[0], cvio2[1] + 4))
    c.stamp("GND", cvio2[0], cvio2[1] + 4, 0)
    c.use(("C_CANVIO1", "2"))
    # VCC's own pin exits STRAIGHT UP (baked rot 270, unlike VIO's leftward
    # exit) -- the SAME axis a rot-0 cap's two pins sit on, so a vertical
    # approach can't avoid the far pin the way VIO's horizontal-then-
    # vertical jog does. Place the cap rot90 (perpendicular) instead: pin1
    # lands exactly on the approach wire's end, pin2 sits at a DIFFERENT x
    # entirely (rot90 = pin1 left/pin2 right), so no coordinate collision
    # is possible regardless of offsets.
    vcc = c.pin("U_CAN1", "3")
    c.wire(vcc, (vcc[0], vcc[1] - 6))
    c.place_pin("C_CANVCC1", "1", vcc[0], vcc[1] - 6, 90)
    c.stamp("+5VSB", vcc[0], vcc[1] - 6, 90)
    c.use(("U_CAN1", "3"), ("C_CANVCC1", "1"))
    cvcc2 = c.pin("C_CANVCC1", "2")
    c.wire(cvcc2, (cvcc2[0], cvcc2[1] - 4))
    c.stamp("GND", cvcc2[0], cvcc2[1] - 4, 180)
    c.use(("C_CANVCC1", "2"))
    # CANH/CANL stay UNCONSUMED here -- they are `global_nets` (bound
    # project-wide by a real KiCad global_label, emitted automatically by
    # the generic per-pin pass); consuming them (as a first attempt did, to
    # "finish" the wire to the termination resistor) skips that pass
    # entirely and the global label never appears (measured: glabels=0 on
    # this leaf, and the flattened netlist showed CANH/CANL as isolated
    # single-pin nets). The termination-resistor wire below is an ADDITIONAL
    # local connection on the same (global) net, not a replacement for it.
    canh = c.pin("U_CAN1", "7")
    canl = c.pin("U_CAN1", "6")
    c.place("R_CANT1", canh[0] + 8, canh[1], 90)
    r1a, r1b = c.pin("R_CANT1", "1"), c.pin("R_CANT1", "2")
    c.wire(canh, r1a)
    c.use(("R_CANT1", "1"), ("R_CANT1", "2"))
    c.place("R_CANT2", canl[0] + 8, canl[1], 90)
    r2a, r2b = c.pin("R_CANT2", "1"), c.pin("R_CANT2", "2")
    c.wire(canl, r2b)
    c.use(("R_CANT2", "1"), ("R_CANT2", "2"))
    ctr_x = max(r1b[0], r2a[0]) + 4
    c.wire(r1b, (ctr_x, r1b[1]))
    c.wire(r2a, (ctr_x, r2a[1]))
    c.wire((ctr_x, r1b[1]), (ctr_x, r2a[1]))
    c.place("C_CANT1", ctr_x + 6, r1b[1], 90)
    cct1 = c.pin("C_CANT1", "1")
    c.wire((ctr_x, r1b[1]), cct1)
    c.use(("C_CANT1", "1"))
    cct2 = c.pin("C_CANT1", "2")
    c.wire(cct2, (cct2[0], cct2[1] + 4))
    c.stamp("GND", cct2[0], cct2[1] + 4, 0)
    c.use(("C_CANT1", "2"))
    c.caption(lf.desc, 10, 20)
    c.note("120ohm split term (60.4x2 + 4n7 center cap); S(STB) tied GND -- normal/active mode.\n"
           "CAN_H/CAN_L are GLOBAL LABELS binding to all 8 port leaves (build_thin_parent's "
           "sheet-pin fan-out\nis 1:1/2-endpoint only -- see cec_sch_compose.build_leaf's "
           "global_nets parameter).", 10, 92)
    c.done()
    return lf


compose_can_frontend()


def compose_detect_adc():
    """05c-detect-adc: ADS7830 8-ch I2C ADC digitizing each port's DETECT_A
    analog node (REQ-HUB-COMMON-042). FLAG: bom-c-module-if-base-secio.md
    Sec5 names ADS7830 an 'alternative not chosen' vs a per-channel
    comparator bank and marks the whole DETECT read-path question open;
    SCHEMATIC-PLAN.md Sec1 nonetheless plans this exact leaf/part, and the
    symbol is already T2-audited/vendored for precisely this role (its own
    Description says 'NOT YET RATIFIED, owner/firmware call'). Captured here
    per the plan with the ratification gap flagged, not silently resolved."""
    lf = leaf05("05c", "05c-detect-adc.kicad_sch", "05c-detect-adc",
               "ADS7830 8-ch I2C ADC: 8x DETECT_A -> DETECT_SDA/SCL (REQ-HUB-COMMON-042; "
               "NOT YET RATIFIED -- bom-c-module-if-base-secio.md Sec5)")
    # widened LOCAL copy (cec-ent-hub-local): the shared cec-ent-power symbol's
    # REFIN_REFOUT pin name overlapped the opposing CH6 name at this leaf's
    # 8-channel density (S6 gate, measured via --check-overlaps) -- same
    # precedent as the widened RJ-45 jack; the shared library symbol is
    # untouched for any other future user.
    lf.add_part("U_ADC1", "cec-ent-hub-local", "ADS7830IPWR", "ADS7830IPWR", 0, 0,
               "cec-Package_SO:TSSOP-16_ADS7830IPWR_L5.0-W4.4-P0.65",
               {"Manufacturer": TI, "MPN": "ADS7830IPWR", "LCSC": "C161747",
                "Description": "candidate DETECT/rail-sense ADC -- NOT YET RATIFIED "
                                "(owner/firmware call, bom-c-module-if-base-secio.md Sec5)"})
    lf.add_part("C_ADCVDD1", "cec-vendor", "C_Small", "100n", 0, 0,
               "cec-Capacitor_SMD:C_0402_1005Metric",
               {"Manufacturer": SAM, "MPN": "CL05B104KO5NNNC", "LCSC": "C1525",
                "Description": "+VDD bypass"})
    lf.add_part("C_ADCREF1", "cec-vendor", "C_Small", "1u", 0, 0,
               "cec-Capacitor_SMD:C_0603_1608Metric",
               {"Manufacturer": SAM, "MPN": "CL10A105KB8NNNC", "LCSC": "C15849",
                "Description": "internal-reference bypass, REFIN_REFOUT [value illustrative]"})
    lf.add_part("R_I2CSDA1", "cec-vendor", "R_Small", "4.7k", 0, 0,
               "cec-Resistor_SMD:R_0402_1005Metric",
               {"Manufacturer": UR, "MPN": "0402WGF4701TCE",
                "Description": "I2C SDA pull-up [value illustrative]"})
    lf.add_part("R_I2CSCL1", "cec-vendor", "R_Small", "4.7k", 0, 0,
               "cec-Resistor_SMD:R_0402_1005Metric",
               {"Manufacturer": UR, "MPN": "0402WGF4701TCE",
                "Description": "I2C SCL pull-up [value illustrative]"})

    lf.net("+3V3", ("U_ADC1", "16"), ("C_ADCVDD1", "1"), ("R_I2CSDA1", "2"), ("R_I2CSCL1", "2"))
    lf.net("GND", ("U_ADC1", "9"), ("U_ADC1", "11"), ("U_ADC1", "12"), ("U_ADC1", "13"),
           ("C_ADCVDD1", "2"), ("C_ADCREF1", "2"))
    lf.net("ADC_REF", ("U_ADC1", "10"), ("C_ADCREF1", "1"))
    lf.net("DETECT_SDA", ("U_ADC1", "15"), ("R_I2CSDA1", "1"))
    lf.net("DETECT_SCL", ("U_ADC1", "14"), ("R_I2CSCL1", "1"))
    for n in range(1, 9):
        lf.net(f"P{n}_DETECT_A", ("U_ADC1", str(n)))

    lf.hier_exports = {f"P{n}_DETECT_A": ("output", ("U_ADC1", str(n))) for n in range(1, 9)}
    lf.hier_exports["DETECT_SDA"] = ("output", ("U_ADC1", "15"))
    lf.hier_exports["DETECT_SCL"] = ("output", ("U_ADC1", "14"))
    # +3V3 already carries a project-wide PWR_FLAG (01f) but kicad-cli's ERC
    # does not treat that as satisfying a power_in pin in a DIFFERENT leaf
    # file (measured empirically) -- U_ADC's +VDD pin (power_in) needs its
    # own local flag here, same pattern as every other leaf with this shape.
    lf.powerflag_nets = ["+3V3"]

    c = _Compose(lf)
    c.place("U_ADC1", 60, 60)
    for n in range(1, 9):
        c.io(f"P{n}_DETECT_A", "left")
    gnd9 = c.pin("U_ADC1", "9")
    c.wire(gnd9, (gnd9[0] + 4, gnd9[1]))
    c.stamp("GND", gnd9[0] + 4, gnd9[1], 0)
    c.use(("U_ADC1", "9"))
    for pin in ("11", "12", "13"):
        p = c.pin("U_ADC1", pin)
        c.wire(p, (p[0] + 4, p[1]))
        c.stamp("GND", p[0] + 4, p[1], 0)
        c.use(("U_ADC1", pin))
    # NOTE (measured empirically, twice, while building this leaf): several
    # features below tap the SAME native x-column (U_ADC's whole right edge
    # shares one x) and route a JOG/vertical some distance out along it --
    # if two features reuse the SAME offset, one's vertical run passes
    # exactly through the other's pin/stamp coordinate and KiCad silently
    # MERGES the two nets (ERC's multiple_net_names, and a "not driven" pin
    # on whichever net got orphaned). Every offset below is therefore a
    # DISTINCT value (4/10/16/24/32) -- no two features ever share a column.
    # (same decoupling-cap topology bug as 05b-can-frontend, same fix: the
    # NEAR pin -- the one the net table shares with the IC pin -- is
    # place_pin'd exactly at the end of a horizontal-only approach wire
    # (never touches the FAR pin's row), and the far pin's own stamp
    # continues AWAY from the near pin, never back across it.)
    ref = c.pin("U_ADC1", "10")
    c.wire(ref, (ref[0] + 10, ref[1]))
    c.place_pin("C_ADCREF1", "1", ref[0] + 10, ref[1], 0)
    c.use(("U_ADC1", "10"), ("C_ADCREF1", "1"))
    cr2 = c.pin("C_ADCREF1", "2")
    c.wire(cr2, (cr2[0], cr2[1] + 4))
    c.stamp("GND", cr2[0], cr2[1] + 4, 0)
    c.use(("C_ADCREF1", "2"))
    vdd = c.pin("U_ADC1", "16")
    c.wire(vdd, (vdd[0] + 16, vdd[1]))
    c.place_pin("C_ADCVDD1", "1", vdd[0] + 16, vdd[1], 0)
    # explicit rail stamp AT the near-pin coincidence point -- a consumed
    # pin gets no automatic power-port stamp from the generic pass, so
    # without this the node is a real, correctly-wired, but UNNAMED net
    # (kicad-cli auto-names it and ERC reads it as an undriven power_in,
    # both measured empirically on this exact leaf).
    c.stamp("+3V3", vdd[0] + 16, vdd[1], 180)
    c.use(("U_ADC1", "16"), ("C_ADCVDD1", "1"))
    cv2 = c.pin("C_ADCVDD1", "2")
    c.wire(cv2, (cv2[0], cv2[1] + 4))
    c.stamp("GND", cv2[0], cv2[1] + 4, 0)
    c.use(("C_ADCVDD1", "2"))
    # SCL/SDA: the pull-up hangs off a dedicated LANE well clear of the ADC's
    # native 2u pin pitch (SDA sits only 2u above SCL, so a 4u-tall resistor
    # body hanging the SAME direction off each row would land squarely on
    # the neighbor's own tap point -- route each down its OWN column to a
    # lane below the whole native pin cluster first).
    scl = c.pin("U_ADC1", "14")
    scl_col = scl[0] + 24
    c.wire(scl, (scl_col, scl[1]))
    scl_lane = scl[1] + 20
    c.wire((scl_col, scl[1]), (scl_col, scl_lane))
    c.place("R_I2CSCL1", scl_col, scl_lane + 2, 0)
    r_scl2 = c.pin("R_I2CSCL1", "2")
    c.wire(r_scl2, (r_scl2[0], r_scl2[1] + 4))
    c.stamp("+3V3", r_scl2[0], r_scl2[1] + 4, 0)
    c.use(("U_ADC1", "14"), ("R_I2CSCL1", "1"), ("R_I2CSCL1", "2"))
    scl_end = (scl_col + 6, scl_lane)
    c.wire((scl_col, scl_lane), scl_end)
    c.io("DETECT_SCL", "right", from_pt=scl_end)
    sda = c.pin("U_ADC1", "15")
    sda_col = sda[0] + 32
    c.wire(sda, (sda_col, sda[1]))
    sda_lane = sda[1] + 30
    c.wire((sda_col, sda[1]), (sda_col, sda_lane))
    c.place("R_I2CSDA1", sda_col, sda_lane + 2, 0)
    r_sda2 = c.pin("R_I2CSDA1", "2")
    c.wire(r_sda2, (r_sda2[0], r_sda2[1] + 4))
    c.stamp("+3V3", r_sda2[0], r_sda2[1] + 4, 0)
    c.use(("U_ADC1", "15"), ("R_I2CSDA1", "1"), ("R_I2CSDA1", "2"))
    sda_end = (sda_col + 6, sda_lane)
    c.wire((sda_col, sda_lane), sda_end)
    c.io("DETECT_SDA", "right", from_pt=sda_end)
    c.caption(lf.desc, 10, 22)
    c.note("NOT YET RATIFIED -- bom-c-module-if-base-secio.md Sec5 names ADS7830 an "
           "'alternative not chosen' vs a per-channel comparator bank.\nSCHEMATIC-PLAN.md "
           "Sec1 plans this leaf anyway and the part is T2-audited/vendored for exactly "
           "this role, so it is\ncaptured here with the ratification gap flagged, not "
           "silently resolved. A0/A1/COM tied GND (fixed I2C address).",
           10, 100)
    c.done()
    return lf


compose_detect_adc()


# ===========================================================================
# 04 -- storage: thin parent -> 04a-qspi-nor + 04b-emmc + 04c-straps, per
# SCHEMATIC-PLAN.md sheet 04 (BOM src: BOM-A; REQ-107..109). Captured 2026-07-16.
#
# CROSS-SHEET FORWARD REFERENCES (04 -> 02, 04 -> 03): the MSS QSPI/eMMC bus
# lands on the MPFS itself (sheet 02a, not yet captured this pass) and the
# +3V3_IO/VDD18 rails that power this sheet's two parts come from the shared
# 3.3V/1.8V bank regulators (sheet 03b -- BLOCKED, MPM3833C has no vendored
# symbol yet; see the dated FOLLOWUPS.md note and 03's own section below).
# Both classes of net use the SAME "reach root, awaiting a not-yet-captured
# producer/consumer" pattern already established for sheet 01's PG_MAIN/
# FLT_MAIN and sheet 05's P{n}_T1_A/CAN_TX/DETECT_SDA exports: an ordinary
# hier_exports entry, listed in this thin parent's root_exports set, with NO
# wire drawn to a sibling sheet's box (that cross-SHEET join is a documented,
# deferred "root cross-wire pass" -- see FOLLOWUPS.md). This sheet does NOT
# use build_leaf's global_nets primitive (reserved, per its own docstring,
# for a genuine >2-occurrence bus within ONE thin parent -- CAN_H/CAN_L on
# sheet 05): every net on this sheet has <=2 occurrences within the
# 04-storage thin parent itself (a leaf's own pin, optionally paired with
# 04c's strap resistor), so the ordinary hier_exports + build_thin_parent
# pairs/root_exports/powerflag_nets machinery (sheet 01/05's own machinery,
# unchanged) covers it without any new engine primitive.
#
# Ref-numbering: this sheet continues the platform's per-sheet NNN-in-100s
# block convention (sheet 01 = U101.., sheet 05 broke from it for its
# repeated-leaf refs) -- U4xx/R4xx/C4xx.
# ===========================================================================
SHEET04_LEAVES = {}


def leaf04(id_, filename, sheetname, desc):
    lf = Leaf(id_, filename, sheetname, desc)
    SHEET04_LEAVES[id_] = lf
    return lf


SHEET04_LEAF_IDS = ["04a", "04b", "04c"]
SHEET04_LEAF_SYM_UUIDS = {lid: _stable_uuid(f"04-leaf-sym-{lid}") for lid in SHEET04_LEAF_IDS}
SHEET04_LEAF_OWN_UUIDS = {lid: _stable_uuid(f"04-leaf-own-{lid}") for lid in SHEET04_LEAF_IDS}
SHEET04_OWN_UUID = _stable_uuid("04-storage-thin-parent")


def compose_qspi_nor():
    """04a-qspi-nor: W25Q256JVFIQ 256Mbit QSPI NOR (A/B firmware images + tamper
    log region, REQ-107..109) -- boot-flash tier upgraded from BOM-A's original
    W25Q128JV (128Mbit) draft per REQ-HUB-COMMON-107 / hub-ent-bom-detailed.md
    Sec1 (the storage ruling); FIQ = SOIC-16 300mil w/ a DEDICATED hardware
    /RESET pin (pin 3, separate from the shared /HOLD-or-IO3 pin 1). Pin map
    verified against the vendored symbol directly (cec_sch.load_symbols), not
    assumed: 1=IO3, 2=VCC, 3=/RESET, 4-6=NC, 7=/CS, 8=IO1, 9=IO2, 10=GND,
    11-14=NC, 15=IO0, 16=CLK."""
    lf = leaf04("04a", "04a-qspi-nor.kicad_sch", "04a-qspi-nor",
               "W25Q256JVFIQ 256Mbit QSPI NOR: A/B FW + tamper log (REQ-107..109)")
    lf.add_part("U401", "cec-ent-power", "W25Q256JVFIQ", "W25Q256JVFIQ", 0, 0,
               "cec-Package_SO:SOIC-16_W25Q256JVFIQ_L10.3-W7.5-P1.27",
               {"Manufacturer": "Winbond", "MPN": "W25Q256JVFIQ", "LCSC": "C3128412",
                "Datasheet": "https://www.winbond.com/resource-files/W25Q256JV%20SPI%20RevG%2003272020%20Plus.pdf",
                "Description": "256Mbit Serial NOR Flash, Standard/Dual/Quad SPI, SOIC-16 300mil, "
                                "dedicated hw /RESET (pin 3). Boot flash upgraded from W25Q128JV per "
                                "REQ-HUB-COMMON-107 (32Mbyte-class NOR tier)."})
    lf.add_part("C401", "cec-vendor", "C_Small", "100n", 0, 0,
               "cec-Capacitor_SMD:C_0402_1005Metric",
               {"Manufacturer": SAM, "MPN": "CL05B104KO5NNNC", "LCSC": "C1525",
                "Description": "VCC bypass, U401"})
    lf.add_part("C402", "cec-vendor", "C_Small", "1u", 0, 0,
               "cec-Capacitor_SMD:C_0603_1608Metric",
               {"Manufacturer": SAM, "MPN": "CL10A105KB8NNNC", "LCSC": "C15849",
                "Description": "VCC bulk, U401"})
    lf.add_part("R401", "cec-vendor", "R_Small", "10k", 0, 0,
               "cec-Resistor_SMD:R_0402_1005Metric",
               {"Manufacturer": UR, "MPN": "0402WGF1002TCE", "LCSC": "C25744",
                "Description": "U401 /RESET pull-up (idle-inactive default; no active MSS-driven "
                                "reset of the flash is planned in this pass -- flag if firmware "
                                "wants one later, a spare MSSIO ball would be needed)"})

    lf.net("+3V3_IO", ("U401", "2"), ("C401", "1"), ("C402", "1"), ("R401", "1"))
    lf.net("GND", ("U401", "10"), ("C401", "2"), ("C402", "2"))
    lf.net("QSPI_RESET_N", ("U401", "3"), ("R401", "2"))
    lf.net("MSS_QSPI_CS", ("U401", "7"))
    lf.net("MSS_QSPI_IO1", ("U401", "8"))
    lf.net("MSS_QSPI_IO2", ("U401", "9"))
    lf.net("MSS_QSPI_IO0", ("U401", "15"))
    lf.net("MSS_QSPI_CLK", ("U401", "16"))
    lf.net("MSS_QSPI_IO3", ("U401", "1"))
    # pins 4,5,6,11,12,13,14 = NC (per the vendored symbol) -- left out of every
    # net so the generic pass auto-emits their no-connect flags.

    lf.hier_exports = {
        "MSS_QSPI_CS":  ("output", ("U401", "7")),
        "MSS_QSPI_CLK": ("output", ("U401", "16")),
        "MSS_QSPI_IO0": ("output", ("U401", "15")),
        "MSS_QSPI_IO1": ("output", ("U401", "8")),
        "MSS_QSPI_IO2": ("output", ("U401", "9")),
        "MSS_QSPI_IO3": ("output", ("U401", "1")),
        "+3V3_IO":      ("output", ("U401", "2")),
    }
    lf.powerflag_nets = ["+3V3_IO"]

    c = _Compose(lf)
    c.place("U401", 60, 60)
    c.place("C401", 30, 46)
    c.place("C402", 22, 46)
    c.place("R401", 34, 80, 0)
    # QSPI exports on their NATURAL exit side (pins 1/7/8 exit left, 9/15/16
    # exit right) -- avoids routing a wire across the chip body to the far
    # column, which the io-column router refuses by construction.
    c.io("MSS_QSPI_IO3", "left")     # pin 1
    c.io("MSS_QSPI_CS", "left")      # pin 7
    c.io("MSS_QSPI_IO1", "left")     # pin 8
    c.io("MSS_QSPI_IO2", "right")    # pin 9
    c.io("MSS_QSPI_IO0", "right")    # pin 15
    c.io("MSS_QSPI_CLK", "right")    # pin 16
    # VCC (pin 2) + GND (pin 10): left to the generic per-pin pass (a plain
    # stub + label/stamp per pin); C401/C402 share the same net NAMES via
    # local-label matching rather than a hand-drawn rail -- a deliberate
    # simplification for this small, low-pin-count part's simple bypass pair
    # (contrast 04b's much larger BGA-style part, same convention).
    # /RESET (pin 3): a real, hand-wired local pull-up to +3V3_IO (R401 left
    # unconsumed on its rail pin, so the generic pass tags it "+3V3_IO",
    # merging by local-label match with C401/C402's own generic stubs).
    # ROUTING GOTCHA (found + fixed this pass, see FOLLOWUPS.md): R401 is a
    # vertical 2-pin part, so pin1 (+3V3_IO) and pin2 (this net) share ONE x
    # column (113.03mm post-shift). The naive 2-segment L-bend at (r2.x,
    # p3.y) drops straight down THAT column to reach pin2 -- and since pin1
    # sits between the bend and pin2 on that exact column, the wire's own
    # path runs directly THROUGH pin1, silently shorting +3V3_IO to this net
    # (measured: kicad-cli netlist merged U401.3/R401.2 into +3V3_IO). Fixed
    # by routing the vertical leg through the MIDPOINT x between the two
    # parts' pin columns instead -- clear of both R401's pin1 and every
    # other U401 left-column pin (1/2/7/8), verified against the flattened
    # netlist post-fix.
    p3 = c.pin("U401", "3")
    r2 = c.pin("R401", "2")
    midx = (p3[0] + r2[0]) // 2
    c.wire(p3, (midx, p3[1]), (midx, r2[1]), r2)
    c.use(("U401", "3"), ("R401", "2"))
    # named explicitly (not left as a bare wire) so the net carries its real
    # intent in the schematic itself, not just this generator's lf.net() call
    c.label("QSPI_RESET_N", midx, (p3[1] + r2[1]) // 2, 180)
    c.caption(lf.desc, 10, 20)
    c.note("VCC/GND + C401/402 label-matched (not hand-drawn).\n"
           "QSPI_RESET_N local only, no MSS drive planned.\n"
           "MSS_QSPI_*/+3V3_IO reach root, await sheets 02a/03b.", 10, 100)
    c.done()


compose_qspi_nor()


def compose_emmc():
    """04b-emmc: generic eMMC 5.1 FBGA-153 (JESD84-B51), 8-bit HS400-capable MSS
    SDMMC wiring (REQ-107..109). Per-SKU density is a BOM property (the exact
    MPN is an open RFQ item, hub-ent-bom-detailed.md Sec6 item 6), NOT a
    schematic variant -- the generic land is what's captured. Pin map verified
    against the vendored symbol directly: CLK=M6, CMD=M5, DAT0-2=A3-A5,
    DAT3-7=B2-B6, RST_n=K5, DS=H5 (HS400 data-strobe), VCC=E6/F5/J10/K9 (x4),
    VCCQ=C6/M4/N4/P3/P5 (x5), VDDi=C2, VSS=A6/E7/G5/H10/J5/K8 (x6),
    VSSQ=C4/N2/N5/P4/P6 (x5); the remaining ~120 balls are RFU/VSF/NC per the
    symbol's own vendored provenance note and are left unwired (auto no-connect).
    VDDi tied LOCALLY to VCCQ (same net, common eMMC 5.1 practice where VDDi
    tracks the IO-voltage domain) -- FLAGGED: verify against the exact eMMC MPN
    once sourced (some parts tie VDDi to VCC instead; RFQ open item)."""
    lf = leaf04("04b", "04b-emmc.kicad_sch", "04b-emmc",
               "Generic eMMC 5.1 FBGA-153: 8-bit HS400 MSS SDMMC (REQ-107..109, "
               "density/MPN=RFQ)")
    lf.add_part("U402", "cec-ent-mcu", "eMMC_5.1_FBGA153_Generic", "eMMC_5.1_FBGA153_Generic",
               0, 0, "cec-ent-mcu:FBGA-153_eMMC5.1_Generic_L13.0-W11.5-P0.50",
               {"Manufacturer": "Generic (JEDEC JESD84-B51)", "MPN": "[RFQ -- density/MPN TBD]",
                "Datasheet": "https://www.jedec.org/standards-documents/docs/jesd84-b51",
                "Description": "Generic eMMC 5.1 land, part-agnostic across the density ladder "
                                "(8/32/64GB per SKU per hub-ent-bom-detailed.md Sec2); exact MPN "
                                "is an RFQ open item (Sec6 item 6)"})
    for ref, val in (("C403", "100n"), ("C404", "100n")):
        lf.add_part(ref, "cec-vendor", "C_Small", val, 0, 0,
                   "cec-Capacitor_SMD:C_0402_1005Metric",
                   {"Manufacturer": SAM, "MPN": "CL05B104KO5NNNC", "LCSC": "C1525",
                    "Description": f"VCC bypass, U402 (representative -- VCC has 4 physical "
                                    "balls spread across the package; the exact per-ball layout "
                                    "population is a layout-time decision, not a schematic one)"})
    lf.add_part("C405", "cec-vendor", "C_Small", "1u", 0, 0,
               "cec-Capacitor_SMD:C_0603_1608Metric",
               {"Manufacturer": SAM, "MPN": "CL10A105KB8NNNC", "LCSC": "C15849",
                "Description": "VCC bulk, U402"})
    for ref, val in (("C406", "100n"), ("C407", "100n")):
        lf.add_part(ref, "cec-vendor", "C_Small", val, 0, 0,
                   "cec-Capacitor_SMD:C_0402_1005Metric",
                   {"Manufacturer": SAM, "MPN": "CL05B104KO5NNNC", "LCSC": "C1525",
                    "Description": f"VCCQ bypass, U402 (representative, 5 physical balls)"})
    lf.add_part("C408", "cec-vendor", "C_Small", "1u", 0, 0,
               "cec-Capacitor_SMD:C_0603_1608Metric",
               {"Manufacturer": SAM, "MPN": "CL10A105KB8NNNC", "LCSC": "C15849",
                "Description": "VCCQ bulk, U402"})

    lf.net("+3V3_IO", ("U402", "E6"), ("U402", "F5"), ("U402", "J10"), ("U402", "K9"),
           ("C403", "1"), ("C404", "1"), ("C405", "1"))
    lf.net("VDD18", ("U402", "C6"), ("U402", "M4"), ("U402", "N4"), ("U402", "P3"),
           ("U402", "P5"), ("U402", "C2"),   # VDDi (C2) tied here -- see docstring
           ("C406", "1"), ("C407", "1"), ("C408", "1"))
    lf.net("GND", ("U402", "A6"), ("U402", "E7"), ("U402", "G5"), ("U402", "H10"),
           ("U402", "J5"), ("U402", "K8"), ("U402", "C4"), ("U402", "N2"),
           ("U402", "N5"), ("U402", "P4"), ("U402", "P6"),
           ("C403", "2"), ("C404", "2"), ("C405", "2"),
           ("C406", "2"), ("C407", "2"), ("C408", "2"))
    lf.net("MSS_EMMC_CLK", ("U402", "M6"))
    lf.net("MSS_EMMC_CMD", ("U402", "M5"))
    lf.net("MSS_EMMC_DAT0", ("U402", "A3"))
    lf.net("MSS_EMMC_DAT1", ("U402", "A4"))
    lf.net("MSS_EMMC_DAT2", ("U402", "A5"))
    lf.net("MSS_EMMC_DAT3", ("U402", "B2"))
    lf.net("MSS_EMMC_DAT4", ("U402", "B3"))
    lf.net("MSS_EMMC_DAT5", ("U402", "B4"))
    lf.net("MSS_EMMC_DAT6", ("U402", "B5"))
    lf.net("MSS_EMMC_DAT7", ("U402", "B6"))
    lf.net("MSS_EMMC_RST_N", ("U402", "K5"))
    lf.net("MSS_EMMC_DS", ("U402", "H5"))
    # RFU (A7/E5/E8/G3/G10/K6/K7/K10/P7/P10), VSF (E9/E10/F10), and the ~107
    # plain NC balls are left out of every net -> auto no-connect.

    lf.hier_exports = {
        "MSS_EMMC_CLK":  ("output", ("U402", "M6")),
        "MSS_EMMC_CMD":  ("output", ("U402", "M5")),
        "MSS_EMMC_DAT0": ("output", ("U402", "A3")),
        "MSS_EMMC_DAT1": ("output", ("U402", "A4")),
        "MSS_EMMC_DAT2": ("output", ("U402", "A5")),
        "MSS_EMMC_DAT3": ("output", ("U402", "B2")),
        "MSS_EMMC_DAT4": ("output", ("U402", "B3")),
        "MSS_EMMC_DAT5": ("output", ("U402", "B4")),
        "MSS_EMMC_DAT6": ("output", ("U402", "B5")),
        "MSS_EMMC_DAT7": ("output", ("U402", "B6")),
        "MSS_EMMC_RST_N": ("output", ("U402", "K5")),
        "MSS_EMMC_DS":   ("output", ("U402", "H5")),
        "+3V3_IO":       ("output", ("U402", "E6")),
        "VDD18":         ("output", ("U402", "C6")),
    }
    lf.powerflag_nets = ["+3V3_IO", "VDD18"]

    c = _Compose(lf)
    # The generic eMMC land is ~193mm tall pin-to-pin (A1 at y=+96.52 to G14 at
    # y=-96.52) -- far past an A4 page's usable height; this leaf alone uses A3.
    c.place("U402", 130, 110)
    # 16u (20.32mm) vertical pitch: each C_Small stub reaches 2.54(pin)+3.81
    # (STUB) = 6.35mm beyond its own center each way, so two stacked caps
    # need >=12.7mm of separation or their stub wires overlap and short
    # together (measured: an 8u/10.16mm pitch put GND and +3V3_IO's stub
    # wires collinear-and-overlapping -> ERC multiple_net_names).
    c.place("C403", 40, 30); c.place("C404", 40, 46)
    c.place("C405", 40, 62)
    c.place("C406", 220, 30); c.place("C407", 220, 46)
    c.place("C408", 220, 62)
    # NO c.io() here (unlike 04a/04c): the io-column router gathers all
    # same-side exports into ONE edge column sized to the OVERALL content
    # bbox, and this symbol's ~193mm pin span makes that column's routing
    # corridor cross other pins along the way (measured: build_thin_parent's
    # own "wire passes through pin" guard fired during development). Every
    # exported net here instead gets the DEFAULT per-pin hierarchical label
    # at its own natural stub position (no manual wiring needed -- the same
    # fallback path build_leaf already uses for every hier_export that has no
    # c.io() declaration, exercised throughout sheet 01's own leaves).
    c.caption(lf.desc, 10, 10)
    c.note("Power/GND: generic stubs, label-matched; caps REPRESENTATIVE\n"
           "(no single 'near the IC' spot on a 153-ball BGA). VDDi(C2)->\n"
           "VCCQ/VDD18, FLAG vs MPN. +3V3_IO/VDD18 await 03b (blocked);\n"
           "MSS_EMMC_* await 02a, CMD/_RST_N also wire to 04c's pull-ups.",
           10, 15)
    c.done()


compose_emmc()


def compose_storage_straps():
    """04c-straps: the shared glue leaf for both storage parts' small strap/
    pull-up resistors (JEDEC-recommended eMMC bus pull-ups) -- kept off 04a/
    04b so those leaves stay purely "one IC + its own bypass". W25Q's own
    /RESET pull-up stays on 04a itself (a purely local 2-terminal net with no
    other consumer, no benefit to separating it out here)."""
    lf = leaf04("04c", "04c-straps.kicad_sch", "04c-straps",
               "Shared storage straps: eMMC CMD/RST_n JEDEC pull-ups")
    lf.add_part("R402", "cec-vendor", "R_Small", "47k", 0, 0,
               "cec-Resistor_SMD:R_0402_1005Metric",
               {"Manufacturer": UR, "MPN": "0402WGF4702TCE", "LCSC": "C25792",
                "Description": "eMMC CMD line pull-up (JEDEC JESD84-B51 recommends "
                                "10k-90k on CMD); rail = VDD18 (the eMMC's own VCCQ/IO domain)"})
    lf.add_part("R403", "cec-vendor", "R_Small", "10k", 0, 0,
               "cec-Resistor_SMD:R_0402_1005Metric",
               {"Manufacturer": UR, "MPN": "0402WGF1002TCE", "LCSC": "C25744",
                "Description": "eMMC RST_n default-inactive-high pull-up; rail = VDD18"})

    lf.net("MSS_EMMC_CMD", ("R402", "2"))
    lf.net("VDD18", ("R402", "1"), ("R403", "1"))
    lf.net("MSS_EMMC_RST_N", ("R403", "2"))

    lf.hier_exports = {
        "MSS_EMMC_CMD":   ("output", ("R402", "2")),
        "MSS_EMMC_RST_N": ("output", ("R403", "2")),
        "VDD18":          ("output", ("R402", "1")),
    }
    # VDD18 IS exported here too (even though this leaf never reaches root on
    # it independently -- 04b already owns that root export/powerflag pairing)
    # because a LOCAL label does NOT cross a leaf-FILE boundary: without a real
    # hier_export/sheet-pin, R402/R403's rail pins would be an orphan 2-node
    # net isolated to this file, never actually joined to 04b's real VDD18.
    # No powerflag_nets needed here regardless -- R402/R403 pin 1 are PASSIVE
    # pins, not power_in, and that check is power_in-pin-specific.

    c = _Compose(lf)
    c.place("R402", 30, 40, 0)
    c.place("R403", 30, 70, 0)
    c.text_side["R402"] = c.text_side["R403"] = "left"
    # no from_pt: the hier_exports anchor pin (R40x pin 2) already sits where
    # we want the io-column attach -- the default (anchor-pin-stub) path is
    # correct here; from_pt is only for a chain end reached via hand-drawn
    # wires (05c's precedent), which would need the anchor pin pre-consumed
    # to avoid double-processing it (generic pass + io-column router both
    # firing on the same pin).
    c.io("MSS_EMMC_CMD", "left")
    c.io("MSS_EMMC_RST_N", "left")
    c.caption(lf.desc, 10, 20)
    c.note("R402/R403 pin1 (VDD18): generic pass, no flag (passive, not\n"
           "power_in). CMD/_RST_N pair 04b<->04c, ALSO root exports.",
           10, 30)
    c.done()


compose_storage_straps()


# ---------------------------------------------------------------------------
# the 15 exports at the ROOT boundary -- UNCHANGED from the pre-restructure
# generator (same names, same shapes; build_root() and the root sheet's own
# 15 pins are therefore byte-identical to before). Only WHERE each anchor
# physically lives moved (now inside a leaf file instead of the flat sheet).
# ---------------------------------------------------------------------------
HIER_EXPORTS = {
    "+5V_MAIN":  ("output", ("R123", "1")),
    "+5VSB":     ("output", ("R125", "1")),
    "EXT_5V":    ("output", ("R127", "1")),
    "+5V_SYS":   ("output", ("R129", "1")),
    "+3V3":      ("output", ("R121", "1")),
    "PG_MAIN":   ("output", ("R105", "1")),
    "FLT_MAIN":  ("output", ("R106", "1")),
    "PG_SVB":    ("output", ("R111", "1")),
    "FLT_SVB":   ("output", ("R112", "1")),
    "PG_EXT":    ("output", ("R117", "1")),
    "FLT_EXT":   ("output", ("R118", "1")),
    "SENSE_MAIN": ("output", ("R124", "1")),
    "SENSE_SVB":  ("output", ("R126", "1")),
    "SENSE_EXT":  ("output", ("R128", "1")),
    "SENSE_SYS":  ("output", ("R130", "1")),
}
ROOT_EXPORT_NETS = set(HIER_EXPORTS)

# root-exports that reach root via a REAL KiCad global power symbol placed
# directly in the thin parent (no leaf sheet-pin at all -- see the note on
# L01G.hier_exports above). net_name -> power-symbol name (same for all three,
# but kept as a mapping for generality / a future net whose symbol name
# differs from its net name).
GLOBAL_POWER_EXPORTS = {n: n for n in ("+5V_MAIN", "+5VSB", "+5V_SYS")}

# ---------------------------------------------------------------------------
# 05's own root-level exports: each port's raw T1 pair + pin-7 SYNC (awaiting
# sheet 06/02/09 capture), the CAN transceiver's digital TX/RX, and the
# DETECT ADC's I2C bus. Mirrors sheet 01's own pattern of exporting to a box
# that has nothing wired to its pins yet (02/06/09 remain placeholders).
# ---------------------------------------------------------------------------
HIER_EXPORTS_05 = {}
for _n in range(1, 9):
    HIER_EXPORTS_05[f"P{_n}_T1_A"] = ("output", (f"J_PORT{_n}", "4"))
    HIER_EXPORTS_05[f"P{_n}_T1_B"] = ("output", (f"J_PORT{_n}", "5"))
    HIER_EXPORTS_05[f"P{_n}_SYNC7"] = ("output", (f"R_SYNC{_n}", "2"))
HIER_EXPORTS_05["CAN_TX"] = ("output", ("U_CAN1", "1"))
HIER_EXPORTS_05["CAN_RX"] = ("output", ("U_CAN1", "4"))
HIER_EXPORTS_05["DETECT_SDA"] = ("output", ("U_ADC1", "15"))
HIER_EXPORTS_05["DETECT_SCL"] = ("output", ("U_ADC1", "14"))
ROOT_EXPORT_NETS_05 = set(HIER_EXPORTS_05)

# ---------------------------------------------------------------------------
# 04's own root-level exports: the QSPI/eMMC bus (awaiting sheet 02a, not yet
# captured) and the two shared rails +3V3_IO/VDD18 (awaiting sheet 03b, BLOCKED
# -- MPM3833C has no vendored symbol). Mirrors sheet 01/05's own pattern of
# exporting to a box that has nothing wired to its pins yet. The (ref, pin)
# tuple here only matters for HIER_EXPORTS_04's OWN use inside 04's thin
# parent (root_exports membership) -- the ROOT sheet's box (built from this
# same dict via root_extra_sheets) only reads the shape ("output"), never the
# ref/pin, so a net with two in-sheet leaf occurrences (+3V3_IO, VDD18,
# MSS_EMMC_CMD, MSS_EMMC_RST_N) just needs ONE representative anchor here.
# ---------------------------------------------------------------------------
HIER_EXPORTS_04 = {
    "MSS_QSPI_CS":  ("output", ("U401", "7")),
    "MSS_QSPI_CLK": ("output", ("U401", "16")),
    "MSS_QSPI_IO0": ("output", ("U401", "15")),
    "MSS_QSPI_IO1": ("output", ("U401", "8")),
    "MSS_QSPI_IO2": ("output", ("U401", "9")),
    "MSS_QSPI_IO3": ("output", ("U401", "1")),
    "+3V3_IO":      ("output", ("U401", "2")),
    "VDD18":        ("output", ("U402", "C6")),
    "MSS_EMMC_CLK":  ("output", ("U402", "M6")),
    "MSS_EMMC_CMD":  ("output", ("U402", "M5")),
    "MSS_EMMC_DAT0": ("output", ("U402", "A3")),
    "MSS_EMMC_DAT1": ("output", ("U402", "A4")),
    "MSS_EMMC_DAT2": ("output", ("U402", "A5")),
    "MSS_EMMC_DAT3": ("output", ("U402", "B2")),
    "MSS_EMMC_DAT4": ("output", ("U402", "B3")),
    "MSS_EMMC_DAT5": ("output", ("U402", "B4")),
    "MSS_EMMC_DAT6": ("output", ("U402", "B5")),
    "MSS_EMMC_DAT7": ("output", ("U402", "B6")),
    "MSS_EMMC_RST_N": ("output", ("U402", "K5")),
    "MSS_EMMC_DS":   ("output", ("U402", "H5")),
}
ROOT_EXPORT_NETS_04 = set(HIER_EXPORTS_04)


# ===========================================================================
# sheet 03: compute-rails (03a-core-buck REAL / 03b-bank-rails STUB / 03c-
# vdda-ldo STUB / 03d-sequencing REAL). Library status re-checked 2026-07-16
# (fresh git pull --rebase, then direct grep of every lib/*.kicad_sym for a
# real symbol -- not trusting SCHEMATIC-PLAN.md sec4's own prose, which is
# already stale in one direction: it lists "TPS7A20 pair (03c)" as a
# remaining gap, but TPS7A2018PDBVR/TPS7A2050PDBVR are BOTH now real,
# fully-pinned, LCSC-sourced symbols in lib/cec-ent-power.kicad_sym (5 pins
# each: IN/GND/EN/NC/OUT, SOT-23-5, verified against TI SBVS338H Fig 4-4).
#   - 03a (MIC22705YML-TR): REAL, unblocked, already vendored (25-pin QFN-24
#     symbol confirmed, matches SCHEMATIC-PLAN.md's own sheet-map entry).
#     CAPTURED. This is the part BOM-A/hub-ent-bom-detailed.md's storage-
#     ruling-adjacent note calls "MIC22705 swap" -- it REPLACES BOM-A's
#     original U3=MPM3833CGRH-Z pick for the VDD-core (1.0V) rail specifically
#     ("kills the MPM3833C 3A headroom risk", per the vendored symbol's own
#     Description property) -- a HIGHER-CURRENT part for the ONE rail BOM-A
#     itself flagged as underspecced (note 2, bom-a-compute.md: "a single
#     MPM3833C (3A) is sized to the low end of the estimated core-current
#     range with no Power Estimator run to confirm").
#   - 03b (bank-rails, U4/U5/U6 = VDD18/VDD25/shared-3.3V per BOM-A): STILL
#     BLOCKED. MPM3833CGRH-Z (the part BOM-A wants for THESE three rails --
#     a DIFFERENT role than the one 03a's MIC22705 replaced; U4/U5/U6's
#     currents per BOM-A's own budget table are 100-500mA each, nowhere near
#     the flagged 3A-headroom risk that was specific to the CORE rail) has NO
#     vendored symbol anywhere in lib/*.kicad_sym -- confirmed by direct grep
#     (the only "MPM3833" hit in the whole lib/ tree is inside MIC22705's own
#     Description text, referencing it as the risk IT replaced, not a real
#     MPM3833C symbol). STUBBED this pass (compose_bank_rails_stub, no real
#     components) per the task brief's explicit instruction: leave a dated
#     stub, do NOT hand-draw a divergent symbol. Re-check on a future pass.
#   - 03c (vdda-ldo, U7/U8 = VDDA=1.0V / VDDA25=2.5V per BOM-A): STILL
#     EFFECTIVELY BLOCKED, more precisely than a flat "gap" -- the vendored
#     "TPS7A20 pair" is the WRONG voltage variants. BOM-A wants TPS7A2010-
#     class (1.0V) and TPS7A2025-class (2.5V) fixed LDOs (both explicitly
#     flagged in BOM-A's own note 3 as "named by extrapolating a confirmed-
#     real naming convention... exact LCSC stock/price was not independently
#     pulled"), but the two symbols actually vendored are TPS7A2018 (1.8V)
#     and TPS7A2050 (5.0V) -- neither matches. These are FIXED-output parts
#     (no FB pin at all: pin map is IN/GND/EN/NC/OUT), so populating the
#     wrong-voltage part would misconfigure VDDA/VDDA25, not just need a
#     resistor tweak. STUBBED this pass (compose_vdda_ldo_stub) with a note
#     explaining the voltage mismatch precisely, same do-not-hand-draw rule.
#   - 03d (sequencing, U9 = TPS3839K33 PG chain gating EN on U3/U4/U5/U7/U8
#     per BOM-A note 4): REAL, unblocked -- reuses the EXACT already-verified
#     platform part (TPS3839DBZ / "TPS3839K33" / TPS3839K33DBZR / C96333)
#     from 01f-buck-3v3's own U107, same pin map (1=GND, 2=~RESET output
#     [push-pull per the symbol's "output" pin type, not open_collector --
#     matches 01f's own precedent of no pull-up on this pin], 3=VDD/sense).
#     CAPTURED, with two real cross-leaf/cross-sheet complications handled
#     explicitly (see the compose function's own docstring): (a) its
#     RESET-output net fans out to MULTIPLE consumers within THIS thin parent
#     (03a's EN/DLY now, 03b/03c's own EN pins once THOSE unblock) -- that is
#     >2 occurrences, which build_thin_parent's ordinary hier_exports "pairs"
#     mechanism explicitly rejects (SystemExit on any net with >2 leaf-pin
#     occurrences), so this uses `global_nets` instead (the CAN_H/CAN_L
#     precedent from sheet 05), name "MPFS_SEQ_EN"; (b) its VDD/sense input
#     needs to monitor 03b's future 3.3V bank-rail output, a SIBLING LEAF
#     within this SAME 03-compute-rails thin parent -- exported as hier_export
#     "+3V3_MPFS", root_exports=True (so it's ready to become an ordinary
#     build_thin_parent "pair" the moment 03b is captured for real and
#     declares the same net name, with ZERO retroactive edit to 03d needed --
#     the sheet-04 precedent for a forward-declared cross-leaf net).
#
# IMPORTANT DISTINCTION from sheet 04's +3V3_IO/VDD18 (which ALSO reach the
# TRUE project root, awaiting sheet 03b): those are cross-TOP-LEVEL-SHEET
# nets (04-storage <-> 03-compute-rails, two DIFFERENT direct children of
# hub-enterprise.kicad_sch) -- verified this pass (read cec_sch_compose.
# build_root directly) that build_root has NO pairing/global-label mechanism
# between different top-level sheets' same-named exports at all (unlike
# build_thin_parent's internal "pairs"); each extra_sheets entry just gets
# its own isolated _root_captured_sheet_block call. So +3V3_IO/VDD18 reaching
# root do NOT auto-connect to 03b's future output merely by sharing a name --
# that needs an explicit FUTURE root-level cross-wire pass (extend build_root
# or hand-author the two wires once 03b lands), tracked in FOLLOWUPS.md.
# "+3V3_MPFS" above is DIFFERENT and does NOT have this problem: it is
# internal to ONE thin parent (03-compute-rails), so build_thin_parent's
# ordinary "pairs" mechanism handles it automatically once 03b exists.
# ===========================================================================
SHEET03_LEAVES = {}


def leaf03(id_, filename, sheetname, desc):
    lf = Leaf(id_, filename, sheetname, desc)
    SHEET03_LEAVES[id_] = lf
    return lf


SHEET03_LEAF_IDS = ["03a", "03b", "03c", "03d"]
SHEET03_LEAF_SYM_UUIDS = {lid: _stable_uuid(f"03-leaf-sym-{lid}") for lid in SHEET03_LEAF_IDS}
SHEET03_LEAF_OWN_UUIDS = {lid: _stable_uuid(f"03-leaf-own-{lid}") for lid in SHEET03_LEAF_IDS}
SHEET03_OWN_UUID = _stable_uuid("03-compute-rails-thin-parent")
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
